gibbs212521/HEC_2_senior_design/LaTeX/FDR_front_page.pdf

## The University of Texas at Tyler College of Engineering and Computer Science Tyler, TX 75799

## Final Design Report

## For

## Wireless Charger Project

### A design project to fulfill the requirements of Senior Design in the Department of Electrical Engineering at The University of Texas at Tyler

The individuals whose names and signatures appear below certify that the narrative, diagrams, figures, tables, calculations, and analyses contained within this document are their original work except as otherwise cited.

Flory, David | April 12, 2021
Signature | Date
Fran¸ca, Natasha | April 12, 2021
Signature | Date
Franulovic, Franci | April 12, 2021
Signature | Date
Gibbons, Chad | April 12, 2021
Signature | Date
Sosa, Francisco | April 12, 2021
Signature | Date
