gibbs212521/HEC_2_senior_design/LaTeX/PDD_Submission.pdf

## The University of Texas at Tyler College of Engineering and Computer Science Tyler, TX 75799

## Primary Design Document Draft For

## Wireless Charger Project

### A design project to fulfill the requirements of Senior Design in the Department of Electrical Engineering at The University of Texas at Tyler

The individuals whose names and signatures appear below certify that the narrative, diagrams, figures, tables, calculations, and analyses contained within this document are their original work except as otherwise cited.

Flory, David | December 1, 2020
Signature | Date
Franca, Natasha | December 1, 2020
Signature | Date
Franulovic, Franci | December 1, 2020
Signature | Date
Gibbons, Chad | December 1, 2020
Signature | Date
Sosa, Francisco | December 1, 2020
Signature | Date

EXECUTIVE SUMMARY

The team proposes to design and prototype a managed, 30 watt wireless resonant charger for use with lithium-ion battery packs. It will be a versatile solution to the problem of powering autonomous mobile devices fitted with moderately sized battery packs of approximately four to six 18650 cells configured for 7.4 to 14.7 volts nominal output. With a preliminary cost estimate of $300, it fills a gap between inexpensive inductive chargers in the 5 watt range and custom 90 watt robotic power systems with an entry level price of $2000.

Our charging system will be made of two essential components: a transmitter and receiver. The transmitter will be supplied by standard line voltage and will be responsible for safely delivering up to 30 watts of resonant power to the receiver when in range and appropriately positioned. It will communicate status with the receiver over a Bluetooth link and will enable or disable power transmission when requested.

The receiver will communicate with the transmitter and to a user GUI over Bluetooth links, and optionally with the user’s own application (i.e. a robot microcontroller) over a serial link. It will be capable of delivering requested power transmission and charging status information and beginning or ending the charging process. It will disable charging on receipt of an error status from the charging circuit and will notify the user to take corrective action. Under normal conditions it will deliver power to the charging control IC, which in turn will charge the attached battery pack.

The charger may be configured to charge 7.4 to 14.7 nominal Li-Ion battery cells, which must have internal protection circuitry in accordance with UL1642 and IEC61960. Optimal configurations would include a 7.4V pack rated for 3.2A charging, a 11.1V pack rated for 2.2A charging, or a 14.8V pack rated for 1.7A charging.

To best demonstrate the full potential of our project, the team has specified optional deliverables that will be completed if time permits once the core project is completed. These stretch goals include a mobile robot capable of charging itself for continuous wireless operation and integration with a smart Li-ion battery for detailed fuel gauge and battery health status.

i

## Contents

I | Project Description | 1
II | Target Specifications and Ethical Considerations | 3
II.A Subsystem Dependencies | | 4
II.B | Hardware Components | | 5
II.1 | Transmitter: | | 6
II.2 | Receiver: | | 6
II.3 | Robot: | | 7
II.4 | Software: | | 7
II.C | Ethical and Professional Considerations | | 9
II.1 | Public Health: | | 9
II.2 | Safety and Welfare: | | 9
II.3 | Global Factors: | | 9
II.4 | Societal factors | | 9
II.5 | Environmental factors: | | 9
II.6 | Economic factors: | | 9
III | Engineering Standards and Constraints | 10
III.A Safety Constraints Mandated by Government and Possible Risks of Wire-
less Power Transfer (WPT) | | 10
III.1 FDA Safety Regulations | | 11
III.B Relevant FDA Safety Regulations and Standards | | 11
III.1 Safety Standards for Lithium-ion Battery Chargers | | 12
III.2 WPT frequency plan and power limits international overview . . . | 12
IV | Evaluation of Design Alternatives | 15
IV.A Primary Power Stage | | 15
IV.B Battery Management, Power Supply, and Target Power Delivery . . . . | 16
IV.C Transmitter circuit | | 20
IV.D Wireless Communications | | 24
IV.1 Ultra-Wideband | | 24
IV.2 ZigBee | | 25
IV.3 Infrared Wireless | | 26
IV.4 Bluetooth | | 26
IV.E Transmitter Coil Design | | 28
IV.F Software | | 29
V | Final Design | 34
V.A Battery Management, Power Supply, and Target Power Delivery . . . . | 34
V.B | Transmitter and Receiver Voltage Regulators (3.3 V and 5 V) | | 37
V.C | Class E Amplifier 30V Voltage Regulator | | 38
V.D Transmitter Design | | 40
V.E | Skin Depth Effects Calculations and Coil Parameters | | 47

ii

V.F | MSP430FR5994 Microcontroller | | 52
V.G Software | | 54
VI | Subsystem Simulations | 56
VI.A Transmitter Simulation | | 56
VI.B Receiver Simulation | | 58
VI.C Battery Management, Power Supply, and Target Power Delivery Simulation 59
VI.D Software Testing Protocol | | 61
VI.E Buck Down Converter Simulations | | 62
VII | Final Design Specifications | 65
VII.A Feasibility Study | | 65
VII.B Microcontroller | | 66
VII.C Transmitter Coil | | 66
VII.D Transmitter | | 67
VII.E Receiver | | 68
VII.F Thermal Considerations for 3.3V and 5V Voltage Regulators | | 68
VII.G Charging Subsystem | | 70
VII.H Battery Considerations | | 70
VII.I Microcontroller Considerations | | 73
VII.J Firmware Requirements: Transmitter | | 73
VII.K Firmware Requirements: Receiver | | 74
VII.L Software Requirements: GUI | | 75
VII.M Coil Considerations | | 75
VII.N Specification Summary | | 77
VIII Project Work Plan for Senior Design II | 78
IX | Resources Required | 81
IX.1 Simulation Tools | | 82
IX.2 Necessary Tools and Equipment | | 82
X | Conclusion | 83
XI | References | 84
Appendices | 87
A | Project Gantt Chart | 87
A.1 | First Review Period | | 87
A.2 | Second Review Period | | 90
A.3 | Third Review Period | | 92
B | Coursework Related Knowledge and Skills | 94

iii

## List of Figures

1 | Operation Story Block Diagram | | 2
2 | Power Supply of Transmitter and Receiver Subsystems | | 5
3 | Transmitter and Receiver Block Diagrams | | 5
4 | Subsystem Relational Block Diagram | | 8
5 | Microsemi Reference Design Kit for DRF1200 [6] | | 20
6 | Singe-Stage and Push-Pull Topology Comparison [11] | | 21
7 | Half-Bridge Structure [33] | | 21
8 | Receiver RF-DC Stage | | 23
9 | 9V to 35V 2-Cell 3.2A Charger with PowerPath and 2A Input Limit [20] | 34
10 | Battery Charger State Diagram [20] | | 35
11 | Tabular Representation of the JEITA system, Default JEITA Values and
| β=3490K Equivalent Temperatures [20] | | 36
12 | Recommended NTC Thermistor Circuit, Analog Devices: NTC Calculator 36
13 | 48 V to 3.33 V or 5 V Buck Down Converter Typical Schematic with Fixed
| Output [35] | | 38
14 | 48 V to 30 V Buck Down Converter Simplified Schematic Diagram [34] . | 39
15 | 48 V to 30 V Buck Down Converter Full Schematic Diagram | | 39
16 | LMG1210 Internal functional block diagram [19] | | 40
17 | Topology of Class-E Amplifier | | 41
18 | Transmitter Class E Amplifier Circuit Diagram | | 44
19 | Receiver RF to DC Stage | | 44
20 | INA19x Reference Schematic Diagram [15] | | 47
21 | Cross-Sectional View of Flat Spiral Coil [5] | | 49
22 | Functional Block Diagram [22] | | 52
23 | Comparison Within MSP430 Family [22] | | 53
24 | Graphical User Interface Architecture UML Diagram | | 55
25 | Class E Amplifier Simulation | | 56
26 | Class E Amplifier Output Voltage and GaN FET Drain Voltage | | 57
27 | Receiver RF-DC Converter | | 58
28 | LTC4162 Demo Board Layout [9] | | 59
29 | LTC4162 Demo Board Output GUI [9] | | 60
30 | LTC4162 Demo Board Simulated Performance [9] | | 61
31 | Schematic Diagram for TPSM265R1V3SILR (3.3 V Regulator) | | 62
32 | 3.33V Buck Converter Efficiency Curve for Expected Input Voltage vs
| Load Current | | 63
33 | Schematic Diagram forTPSM265R1V5SILR (5 V Regulator) | | 63
34 | 5V Buck Converter Efficiency Curve for Expected Input Voltage vs Load
| Current | | 64
35 | 30V Power Supply Schematic | | 64
36 | 30V Buck Converter Efficiency Curve for Expected Input Voltage vs Load
| Current | | 65
37 | Thermal Resistance vs. PCB Area [35] | | 69
38 | Basic Work Breakdown Structure Diagram – Deliverable-Based WBS . . | 79
| iv

## List of Tables

1 | Receiver Specifications | | 3
2 | Transmitter Specifications | | 3
3 | Communication Link Specifications | | 3
4 | GUI Specifications | | 3
5 | Ethical and Professional Considerations | | 10
6 | Overview of Relevant Standards | | 13
7 | Overview of Constraints | | 14
8 | Battery Charger Alternatives Evaluation Table | | 19
9 | Transmitter Alternatives Evaluation Table | | 24
10 | RF-DC Converter Alternatives Evaluation Table | | 25
11 | Wireless Communication Alternatives Evaluation Table | | 27
12 | Coil Design Alternatives Evaluation Table | | 29
13 | Software Alternatives Evaluation Table | | 32
14 | Alternatives Evaluation Table | | 43
15 | Skin Depths Effects in Copper Wire at High Frequencies | | 48
16 | Copper Coil Inner Diameters Calculated at 90 mm Outer Diameter [21] . | 49
17 | Copper Coil Inner Diameters Calculated at 90 mm Outer Diameter with
| Winding Variables | | 50
18 | Copper Coil Inner Diameters Calculated at 90 mm Outer Diameter with
| Inductance | | 50
19 | Copper Coil Resonance Inductance and Capacitance at 13.6 MHz . . . . | 50
20 | Copper Coil Skin Depth and Resistivity Calculations | | 51
21 | Quality Factor Inputs and Outputs | | 51
22 | MSP430FR5994 Parameters [22] | | 54
23 | Table of Software Utilized | | 54
24 | Final Design’s Charging Subsystem Specifications | | 72
25 | Final Design’s Coil Tubing Specifications | | 75
26 | Final Design’s Receiver Coil Specifications | | 76
27 | Final Design’s Receiver Specifications | | 77
28 | Final Design’s Transmitter Specifications | | 77
29 | Final Design’s Communication Link Specifications | | 78
30 | Final Design’s GUI Specifications | | 78
31 | Project Milestones | | 80
32 | Coursework Related Knowledge and Skills Table | | 94

v

I. PROJECT DESCRIPTION

Our project is to design and prototype a 30 watts nominal resonant wireless charger for use with 4 to 6 cell lithium ion battery packs. It will be microcontroller managed and may be monitored and controlled by a user GUI or directly by the target application. Unlike existing customized and proprietary robotic charging systems, our product will charge a standard battery type and be suitable for both stand-alone operation and integration into the user’s own design.

The team has been unable to discover any equivalent to our intended product for retail. The closest comparable product is a 90 watt magnetic resonance device that is marketed to businesses designing commercial drones and robotic systems. On the lower end, nearly all unbranded, low-cost wireless chargers that are available from mass online retailers supply no more than 5W via inductive charging. For a single industrial unit, the team has received a price quote for approximately $2000 USD. Individuals and small R&D teams that search for suitable devices through online retailers will find that these low-end transmitters are not modular and are limited to one specific purpose such as charging cell phones or key-fobs.

Our charging system shall employ magnetic resonance coupling to charge a lithium ion battery pack, delivering between 15 and 30 watts of power. The power transmitter and receiver will communicate as a unified system which shall provide battery management, protect against overcharging, and provide both diagnostic and telemetric information to the user and to an optional serial connection with the powered application’s control circuitry. The charging system may be monitored and controlled by the user either through an attached LCD interface or a GUI from either a Bluetooth connected PC or smartphone.

As an alternative to wireless charging, our intended market of hobbyists and prototype designers might consider a self-docking direct electrical connection. This is the charging method used by the Roomba, which engages with a custom dock and charges using metal contacts. While this is a cost-effective solution for a mass-produced product, wireless charging is a superior choice for autonomous mobile devices that might have a wide variety of sizes and shapes. The benefits offered by wireless charging include flexible placement of the charger, a compact charging area, greater tolerance for imperfect alignment between the charger and the target device, and the absence of exposed electrical connections.

To best demonstrate the full potential of our project, the team has specified optional deliverables that will be specified in detail once the core project is completed and tested. They include a mobile robot capable of charging itself for continuous wireless operation, fully integrated with a smart Li-ion battery for detailed fuel gauge and battery health status.

The team holds that a moderate power, low cost wireless charger with accessible telemetry will be useful to a small but important market of robotics hobbyists and developers, who at present are not being served by either proprietary business-to-business solutions or the low power, poorly documented inductive chargers available on the hobby market.

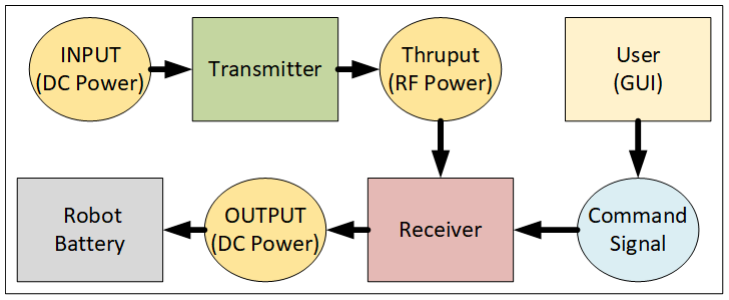
[picture p66: figure]

Figure 1: Operation Story Block Diagram

II. TARGET SPECIFICATIONS AND ETHICAL CONSIDERATIONS

Table 1: Receiver Specifications

Charge time
(4Ah Battery
Pack)

5 Hours Max

Battery pack voltage | 14.2 V
Coupling
Efficiency Transmitter to Receiver | 90%
AC-DC Conversion Efficiency | 80%
Charging Controller DC-DC converter | 85%
Overall Receiver Conversion Efficiency | 61.2%
Maximum Battery Charging Current | 1.25 A (14.7 V battery pack)
Charger Subsystem Charge Protocol | Constant Current Constant Voltage (Li-ION Battery)
Battery Type | Lithium-Ion (4 x18650 in Series or 2P4S Configuration)
Power Negotiation | Bluetooth 5 LE
Transmitter Locator Method | RF Localization [Bluetooth]
Deliverable Demo | Self-Moving Device (Robot)
Telemetry | Report State to GUI Device
LCD display | Diagnostic Character String Display

Table 2: Transmitter Specifications

Operating frequency | 13.56 MHz
RF power output | 30 W
Max operating range | 30 cm
DC Power supply | 12V 5A max.
Conversion
Efficiency DC-AC | 80%
Telemetry | Report State to GUI Device

Table 3: Communication Link Specifications

Communication Medium | Bluetooth 5 LE
Protocol | TBD

Table 4: GUI Specifications

GUI OS | WinOS, IOS, Linux, & Android
License | LGPL 3.0
Software Architecture | Model-Controller-View (MCV) Architecture
Delivery Model | Open Source (Free App Download)

A. Subsystem Dependencies

There are three modular components of the wireless charger project: the transmitter, the receiver, and the GUI. Additionally, in order to demonstrate a POC, this project will include a robotic subsystem that accepts the receiver as an onboard module. Thus, the project is concerned with four modular components that fall within a hierarchy of control. This evaluation of how each component and their subsystems subordinate to one another is critical for firmware and software development methodologies implementation.

The most independent component is the robot. This means that the robot does not ask anything from the receiver, transmitter, or GUI but must accept transmissions to it and perform the task associated with the particular communiqu´e and any status report is read by the other components dependent upon the robot for information. The furthest extent of interaction on part of the robot component for the POC would be to validate a networking handshake during Bluetooth communications.

The next most independent component is the transmitter on account to its responsive or passive functionality. The transmitter shall respond to the receiver’s requests for charging and periodically emit RF-pings to provide the receiver with positional data. The transmitter will not consider whether a ping is received nor search for a receiver unless instructed to do so by the user via the project’s GUI. The transmitter must have fail-safe protocols within its subsystems from its microcontroller.

Each receiver is independent of one another as well as from the GUI. A receiver would be dependent upon the robot accepting its telemetry’s locating feed as well as the transmitter pings and power to provide any value. The receiver will monitor the battery status and seek to induce proper voltages and currents in order to charge the battery. It will provide the transmitter with a distance vector to validate that it is close enough to begin charging via magnetic coupling. Furthermore, it will inform the transmitter to shut off by ceasing network authentication after detecting that the battery is charged or any system error is detected. The receiver shall be pairable to a specific transmitter before it is installed into a robot in order to maintain full operability in the absence of a user running The Project’s GUI Application.

The completely dependent component is the GUI, i.e. the Graphical User Interface. For the purposes of this section, the GUI will be considered indistinguishable from the Project’s Application that runs the GUI and fulfills all its functionality. It will have the adaptability to communicate with the receiver’s enclosing robot. The GUI primarily fulfills the need to monitor the status of the transmitter and receiver in real time. It can be used to monitor the battery’s charge or to turn off either the receiver or the transmitter directly as a bypass. The GUI will be compiled on any OS that Qt5 supports and downloadable for free off the internet. The GUI will add value to the Wireless Charging System as a whole without being a critical component.

B. Hardware Components

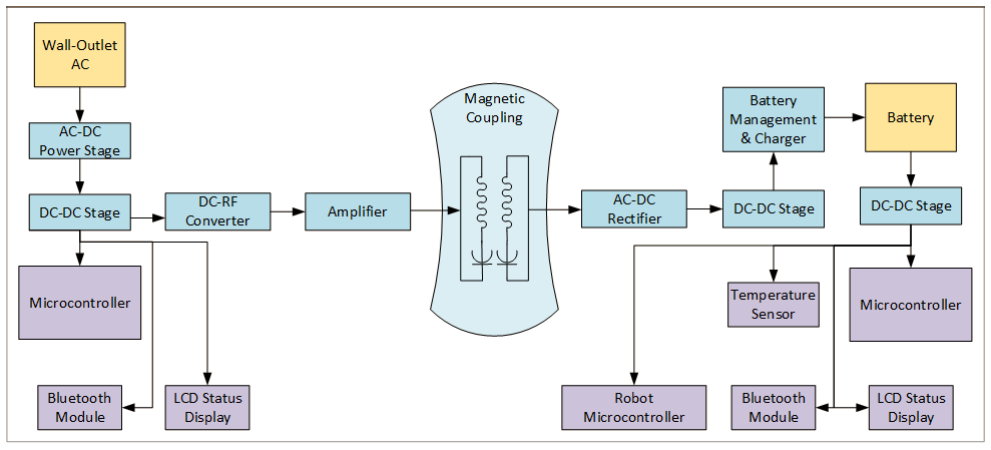
[picture p67: figure]

Figure 2: Power Supply of Transmitter and Receiver Subsystems

There are two hardware components to the system: a transmitter and receiver. Additionally, a third hardware component shall be included for the scope of this system’s proof of concept (POC), i.e. a robot with the wireless charger receiver module on-board. The POC demonstration will exhibit the charging of onboard batteries, locating the robot via the receiver’s telemetry, an error test with only the receiver’s attached LCD Status Display, and provide real-time feedback on a GUI via Bluetooth communication. The onboard battery pack is to provide power to both the robot and the receiver power when uncoupled from the transmitter.

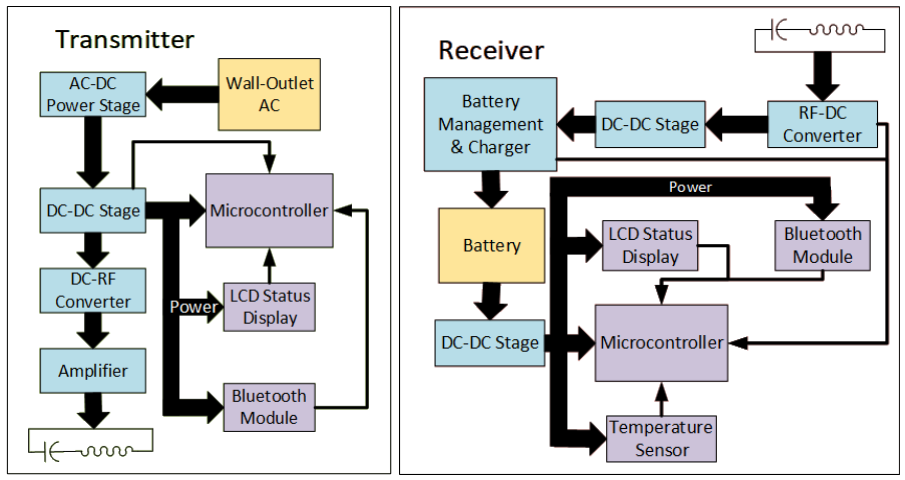
[picture p68: figure]

Figure 3: Transmitter and Receiver Block Diagrams

1.) Transmitter: The transmitter provides power wirelessly and communicates asynchronously with the receiver. The receiver converts that power to proper voltage levels for battery charging. Telemetry and robot subsystems shall operate on the battery’s power. Both the transmitter and receiver will negotiate power transmission and the wattage thereof. The transmitter will not be on at all times. The transmitter will start providing RF power only while the receiver requests power. Also, power delivery will be disabled if the coupling efficiency drops below 90%. Upon undesired decoupling, the receiver will provide its robot correctional vectors that can be used to reposition the robot for optimal charging. This receiver’s positional correction will give an added benefit of preventing bystanders from exposure to strong electromagnetic fields.

Both of the system’s hardware components will require firmware for their microcontrollers to fulfill their targeted deliverables. This firmware is specific to their design and must be developed as part of the project. Their firmware must permit communication with external devices running the project’s graphical user interface (GUI) over Bluetooth.

The transmitter takes power from a DC source and generates an electromagnetic field using an RF amplifier and antenna. For safety and efficiency concerns a power negotiation protocol between the transmitter and the receiver is required for safe and efficient operation. The transmitter will display important parameters on the LCD display mounted on its enclosure and more detailed data will be transmitted to the remote PC, tablet or phone via wireless link.

- External power supply 12V, 5A (off the shelf power supply) will be used to provide power to the system.
- Internal DC-DC converter will be used to step down input voltage to appropriate levels for internal devices. (The transmitter will require at three different voltage levels for powering microcontroller, Bluetooth, LCD, RF generation stage and RF amplifier.)
- DC to RF converter consists of an RF oscillator followed by a buffer stage.
- Buffered RF signal is supplied to the class E amplifier that drives the tuned transmitter LC circuit.
- Microcontroller is used to control the transmitter (power negotiation and safety), data collection and communication coordination.
- The LCD is used to display selected parameters such as RF amplifier supply current, input power current and coil RF voltage. This display will be a simple two row charter display.
- The Bluetooth module will be used as a communication device for telemetry and power negotiation between the power transmitter and receiver.
- Entire transmitter will be designed and assembled on a single PCB.

2.) Receiver: The receiver is responsible for battery management, conversion of RF to DC power for charging, and for communicating status with the transmitter, the device under power, and the user via a local LCD interface or remote GUI. Battery management functions will include the monitoring of charge level, battery temperature, and charging current and voltage. The receiver will detect a low battery condition, provide telemetry to the powered device, and will request RF power transmission from the transmitter when in charging range. A single microcontroller will manage all receiver functions with support from appropriate battery management and wireless communication modules.

3.) Robot: As a proof of concept for the wireless charger we will integrate it into an example robotics application. Our mobile robotics application will interpret charger telemetry to recognize a low battery condition and position itself appropriately for charging.
- Custom PCB will be required for the microcontroller and stepper motor drivers. Electronic circuit for this part will be independent from the charger circuit.

4.) Software: The inter-platform software will provide the user an interactive suite of realtime information via a graphical user interface (GUI). The GUI shall be modular and have the ability to incorporate further functionality, be it communicating with the robot or implementing automated communications to the hardware components.


Figure 4: Subsystem Relational Block Diagram

C. Ethical and Professional Considerations

1.) Public Health: Life preserving medical equipment requires concern in the transmission of powerful RF charging signals that may interfere with the medical equipment. We will adhere to FCC standards for intentional radiators and ensure that the charger transmitter does not exceed FDA guidelines for RF emission. Our design will be informed by the guidelines of the National Council on Radiation Protection and Measurements (NCRP) and the Institute of Electrical and Electronics Engineers (IEEE).

2.) Safety and Welfare: Our design may contribute to public safety and welfare by easing the development of robotic systems intended to handle hazardous materials, work in narrow spaces, high temperature environments, or in vacuum. We will follow industry best practices for safe charging, such as current limiting and temperature monitoring, to minimize the risk of battery failure.

3.) Global Factors: The pressures of governing bodies are to be taken into consideration in any choice this project takes; however, we are primarily concerned with the US governing bodies and then the EU bodies in order to streamline our development process to hit the largest market base possible. Additionally, Canadian and Mexican regulations would be considered as immediate market options.
In an alternate vein, there are sourcing questions that must be investigated before production in order to conform with internation laws and prevent being banned from specific global markets whether at home or abroad.

4.) Societal factors The source code will be educational as well as providing value to the device itself. The design’s modular intention will permit versatile implementations at work or at home. The product should serve influenceable groups such as teenagers, helping them enter STEM related fields.
The product as a whole should be considered in a way that would encourage further education in the classroom in physics. Likewise, the production of the product should foster a community between the product’s programmers and engineers.

5.) Environmental factors: This concern requires continual attention for any anomalies concerning the battery cells. The device cannot account for all of these concerns, but should maintain labeling that makes the customer aware of such concerns that may be caused by their device. The project must provide a means of emergency shut off by some interrupt port that is always active. The operating robot, the user via a GUI, and the receiver itself must have this ability to turn off the charging feature of the receiver.

6.) Economic factors: The device could fulfill legal requirements for a client, and, in that case, a custom suite would be developed in the software at a premium to satisfy a client’s needs. Additionally, creating a lightweight, low-cost production process is critical in maximizing profits. The open-source market also provides extensive free advertising momentum when capitalized successfully. Additionally, the product would assist in producing other products, especially in research and development.

Table 5: Ethical and Professional Considerations

Public Health | · Medical Equipment RF Exposure · Electrical Shock · Chemical Exposure
Safety and Wellness | · RF Bandwidth Jamming · Electrical Shock · Chemical Exposure
Global Factors | · International Governing Bodies · Sourcing Restrictions · Inter-Market Penetrability
Societal Factors | · Open-Source Capitalization · STEM Educational Resources · Professional Organizations · Customer Privacy & Security
Environmental Factors | · Chemical Pollution · User Environmental Awareness · Emergency Shut Off Cases
Economic Factors | · Open-Source Capitalization · Specialty Clientele · Rapid Agile-Deployment · Light-Weight Production

III. ENGINEERING STANDARDS AND CONSTRAINTS

A. Safety Constraints Mandated by Government and Possible Risks of Wireless Power Transfer (WPT)

In the United States, two government agencies are responsible for regulations regarding RF exposure safety. Those agencies are the Federal Drug Administration (FDA) and Federal Communications Commission (FCC). Both agencies have their own set of rules that are similar.

1.) FDA Safety Regulations There are safety concerns about exposure to strong electromagnetic fields. The FDA divides wireless chargers into two categories:
- Proximity type (where the device is in contact with the charger)
- Directed (beamed) delivery across space

Since this design fits in the category of proximity chargers FDA rules for this type of charger must be followed. According to FDA Resonant proximity charges have resonant LC circuit which improves range and efficiency. FDA clearly states that higher power RF transmitters pose a higher risk. Since the wireless charger is a powerful RF transmitter there are concerns about effects of the wireless charger to metal objects such as rings and implanted medical devices and other wearable metal pieces.

The FDA clearly states that higher power products pose a higher risk and there are concerns about effects of the wireless charger to metal objects such as rings implanted medical devices and other wearable metal pieces. Also, the FDA has concerns regarding WPT in terms of electromagnetic interference with medical devices or disruption of device communications. Therefore, engineering controls must be sensitive and reliable enough to prevent injury. Also, it is important to keep in mind that not all existing products implement electromagnetic safety. Hence, some existing products may malfunction if they are exposed to strong electromagnetic fields.

B. Relevant FDA Safety Regulations and Standards

FDA has multiple standards and regulations. Since our device will use an RF transmitter for power transfer, Title 21 code CFR 1000.15(b) is applicable [1].

IEEE C95.1-2005 standard defines guidelines regarding RF power density for localized and whole-body exposure to electromagnetic fields generated by the RF emitter [14] (in our case transmitter). Those two standards address exposure to electromagnetic fields. In order to address this rule, we are limiting our transmitter power to 30W[14]. A power negotiation protocol will be used to enable the charger transmitter only when the receiver is present and properly placed in the front of the charger.

Exposure limits are clarified in IEEE Standards Interpretations for IEEE Std C95.1-2005. IEEE Standard for Safety Levels concerning Human Exposure to Radio Frequency Electromagnetic Fields, 3 kHz to 300 GHz. According to interpretation from the IEEE Standards Interpretations the whole body exposure is limited to 0.08W /kg and localized exposure is 2W/kg. Since the transmitter will operate on the frequency that ranges from 100kHz to 1GHz exposure levels in this rule is applicable to our design.

The FCC also addresses concerns about RF exposure considerations for low power consumer wireless power transfer from FCC. WPT devices must satisfy RF exposure limits from FCC standard KDB 680106 D01 [25][16][27]. All wireless power transfer devices that operate above 9kHz are considered intentional radiators and they are subject to FCC rules.

FCC sets regulations and norms for WPT devices and it is mandatory to certify WPT devices prior making them available on the market. Those rules include unwanted emissions limits in order to prevent electromagnetic interference. Also, FCC sets frequency allocation plans. According to the frequency allocation plan frequency 13.56MHz is available for wireless power transfer devices in the USA.

FCC has established a regulatory framework for wireless power transfer. According to the FCC information, the charging mode is certified under FCC Part 18 [16] and the communication part is certified under Part 15 [25][27]. Given FCC requirements it is feasible to use an already certified module for wireless communication such as Bluetooth, Zigbee, or Wi-Fi. That way only WPT circuits would be subject to certification according to FCC Part 18 [16]. When all available regulations are considered the best operating frequency for the wireless charger is most likely 13.56MHz since that frequency may become the worldwide standard for WPT. Also, this frequency will allow WPT transfer using magnetic resonance which does not require very precise positioning and matching charger transmitter coil. The power limit ( max. 30W) will be more than enough for this application.

Given FCC requirements, it is feasible to use an already certified module for wireless communication such as Bluetooth. Bluetooth is covered by the IEEE 802.15.1 standard and is widely used in many devices and is licensed worldwide [12].

1.) Safety Standards for Lithium-ion Battery Chargers We plan to follow the IEEE 1625-2008 Standard [13] for rechargeable batteries for multicell mobile computing devices because this device is universal and can be considered as a computing device. This standard provides guidelines on implementing the safety controls for the design and manufacture of lithium-ion (Li-ion) and lithium-ion polymer (Li-ion polymer) rechargeable battery packs [13]. Safety guidelines are addressing the fire hazard due to charger or battery failure [13].

2.) WPT frequency plan and power limits international overview According to ETSI (European Standards Organization), there are certain frequencies and prescribed maximum power levels for wireless charging. Some of those frequency bands are candidates for international harmonization (those frequency bands will be dedicated to WPT transfer). At this moment there is no agreement on which frequency band will be used for WPT worldwide.

ETSI documentation gives an overview of different frequencies for the implementation of WPT systems. According to ETSI 13.553 – 13.567 MHz band is currently used for power transfer for the following power classes P<1W, 1W<P<5W, 5W<P<31.5W [17]. This is an International standard that covers European Union EU and European economic area (EEA) as well as many other regions (Parts of Africa, Asia and Australia ) follow European Union (EU) regulations related to this matter.

EN 55011:2016 international standard for electromagnetic compatibility. This standard applies Industrial, scientific and medical equipment and addresses radio frequency disturbance. This standard sets limits to electromagnetic emissions from the product. In order to avoid creating disturbance in RF communication the wireless charger electromagnetic emissions must be below the limit prescribed in this standard. This is achieved by proper circuit design and using low pass filters on all connections that are exposed to the user.

Table 6: Overview of Relevant Standards

Organization | Engineering Standards
IEEE | IEEE C95.1-2005 This standard defines exposure limits to the electromagnetic field This standard is adopted in many safety standards. IEEE 1625-2008 Standard for rechargeable batteries for multicell mobile computing devices. IEEE 802.15.1 Bluetooth standard
Government | FCC Part 15, FCC part 18 RF Power levels and communication links are defined by FCC Part 15 and Part 18. The RF transmitter power level limits in the US are much higher than in some other countries. FDA: 21 CFR 1000.15 FCC: KDB 680106 D01 Both standards define exposure limits to electromagnetic fields. The limits will be satisfied if the transmitter power is limited to 5W. Higher power levels are allowed if proper safety measures are implemented.
International | EN 55011:2016 This standard defines limits for unwanted emissions in the RF spectrum above 30MHz. The proposed WPT charger system must follow limitations for unwanted emissions.

Table 7: Overview of Constraints

| Technical Description
Cost | $320 Estimated Prototype Cost
FDA | FDA: 21 CFR 1000.15 FCC: KDB 680106 D01 Both standards define exposure limits to electromagnetic fields. The limits will be satisfied if the transmitter power is limited to 5W. Higher power levels are allowed with proper safety measures.
Government | FCC Part 15, FCC part 18 RF Power levels and communication links sic FCC Part 15 and Part 18. The RF transmitter power level limits in the US are much higher than other countries. EU rules power requirements satisfy US regulations.
International | EN 55011:2016 This standard defines limits for unwanted emissions in the RF spec-trum above 30MHz. The proposed WPT charger system must follow limitations for un-wanted emissions.
Speed | Recharge speed 5 hours (for 5. Ah battery pack 14.4V)
Reliability | The charger will be able to detect improper positioning and it will monitor for power coupling efficiency. If is coupling inefficient it will provide warning and it will not start charging process. The device will continuously monitor battery conditions such as charge or discharge current, voltage and temperature in order to prevent battery capacity degradation Power RF transmitter power <30W Overall power supply input requirement will be <50W.
Complexity | The system has two hardware parts power transmitter and the robot with integrated power receiver with the charger battery management and battery pack
Manufacturability | The device design will be based on standard electronic/electrical and mechanical components that are readily available. Electronic circuit assembly sic custom printed circuit board design. Two PCBs one for receiver and the other for the receiver/robot. All electrical components such as batteries and motors will be stan-dard, readily available components. The design will utilize mechanical parts such as gears, shafts, and fasteners that are commonly used and readily available.
Sustainability | This device is designed to cause minimal wear and tear to itself and any device connected to its system. The receiver would extend the lifetime of others’ devices by providing a low-cost recharging option.

IV. EVALUATION OF DESIGN ALTERNATIVES

A. Primary Power Stage

The wireless charger and receiver system will depend on AC line power provided to the wireless transmitter unit.

Options:

1) Direct AC connection
a) Immediately rejected due to safety concerns and unneeded complexity.
2) Approved 110-220 VAC to 12 VDC commercial switch-mode power supply.
a) Advantages
i) low cost
ii) standard voltage
iii) ready availability.
b) Disadvantages
i) Additional boost stage required to provide the higher voltages required by the resonant transmitter, adding complexity and power loss.
ii) Five amp input current would create undesired power losses.
3) Approved 110-220 VAC to 48 VDC commercial switch-mode power supply.
a) Advantages
i) Good availability through engineering supply channels.
ii) Relatively low input current reduces heat loss
iii) Voltage near or only slightly above what is needed by the transmission stage.
iv) Example: TDK-Lambda DT62PW480D
1) 48 VDC, 1.36 A maximum (65 watts)
2) Higher wattages and alternate manufacturers available
3) Note that optimal efficiency is usually obtained below maximum
power draw.

The 48 VDC primary supply was provisionally approved. It will require a step down stage to provide 5V and 3.3V logic supplies for the wireless transmitter microcontroller, class E amplifier, and support circuitry.

The step down buck down DC converters could either be accomplished via individual custom op amp voltage regulators or integrated buck down circuits. Furthermore, the 5 V and 3.33 V buck down DC converters could potentially be merged into a single topology. Custom op amp voltage regulators would take up a larger surface area as well as require excessive soldering and are thus not desirable. The only limitation in merging the 5 V and 3.33 V buck downs into a unified topology is that the 5 V buck down would require more current to feed both outputs. The benefit would be the reduction of parts and surface area required for the total circuit.

B. Battery Management, Power Supply, and Target Power Delivery

Our project will convert electricity from the wireless power receiver into a form suitable for charging a cell battery. It must do so while powering its own circuitry, and it must deliver power from the batteries to the target application. Our project must also be capable of monitoring the charging process and battery charge status for both safety and diagnostic purposes. It must be able to respond to instructions and queries received from the wireless power receiver microcontroller.

When implementing a rechargeable battery management system, it is first necessary to decide what battery chemistries the system will support. The team considered NiMH and Li-ion chemistries and favored the latter due to the far greater power density. The team had already selected a mobile robot as an ideal example application for our charger. It was clear that the performance and user appeal of our wireless charger would be much greater if it could utilize the higher-performance battery chemistry. The team understood that there would need to take special care that our charge circuitry would manage these high performance batteries safely.

The following requirements were identified for the battery management system:

1.) DC to DC conversion from the wireless power receiver to a form appropriate for the charging and power supply circuits.
2.) Charging appropriate for battery chemistry, i.e. constant current stage followed by a constant voltage stage.
3.) Temperature monitoring and protection against overcharging.
4.) The ability to vary charging currents in response to varying levels of wireless power, either automatically or in response to commands from the wireless receiver control unit.
5.) The ability to draw operating power from batteries and charger while charging is in progress (i.e. PowerPath).
6.) The ability to detect a low battery condition, which may or may not include more detailed fuel gauge capabilities.
7.) The ability to control charging behavior as needed in response to demands from the wireless power receiver microprocessor or user controls.
8.) The ability to report telemetry to the wireless power receiver microprocessor or user.

There are many available integrated solutions that could meet the above requirements. In order to narrow down the possibilities the following choices must be made:

1) Battery chemistry
a) Lithium-Ion
b) NiMH option
c) Multi-chemistry: rejected due to limited hardware options, complexity, and safety concerns.
2) Linear vs. Switching input stage and input voltage range
a) Linear
i) Usually seen on small, single or dual cell chargers.
b) If Switching:
i) Buck: may make an additional DC/DC stage unnecessary.
ii) Boost: not likely to be necessary
iii) Buck-boost: may make an additional DC/DC stage unnecessary
3) Stand-alone vs. programmable
a) Jumper/hardware settings
i) Limited configuration options.
ii) Limited data available via status lines (i.e. over-temp condition) iii) Simple implementation.
b) I2C programmability
i) Most configuration and control issues may be worked out in software. ii) Configuration may be altered during operation by firmware or
user instructions.
iii) Status registers may be queried by the microcontroller at any time.
c) SMBus programmability
i) Generally equivalent to I2C
ii) Libraries available for MSP430
iii) Automatic timeout supported
4) Maximum power point tracking
a) Offered as an integrated option within Analog Devices LTC4162 family.
i) May be useful depending on wireless power receiver design choices.

Preliminary recommendations: A fully programmable multi-cell charge controller from a modern, well-supported product line is the most flexible option. Such a device would allow many design choices to be made in software and changed if necessary.

Candidates include:

1) Texas Instruments: BQ257xx
a) Buck-boost power input
b) Supports 1-4 Li-ion cells
c) Options include I2C/SMBus, USB-PD, CPU throttling signals
d) Demo available: BQ2571x
2) Analog Devices: LTC4162
a) Buck power input
b) Supports 1-8 Li-ion cells
c) Integrated MPPT option
d) Demo available: DC2038A
3) Texas Instruments: BQ2002
a) Linear power regulation
b) Supports 1-4 NiMH cells
c) Thermistor monitoring
d) Standalone RC-Settable

Table 8: Battery Charger Alternatives Evaluation Table

Evaluation Basis | Texas Instruments BQ25790 | Analog Devices LTC4162 | Texas Instruments BQ2002
Environmental Factors | RoHS compliant. Environmental con-cerns with Li-ion cell production and disposal. | RoHS compliant. Environmental con-cerns with Li-ion cell production and disposal. | RoHS compliant. Environmental con-cerns with Li-ion cell production and disposal.
Economic Factors | $2.29 per unit | $2.95 per unit | $0.786 per unit
Public Health | RoHS | RoHS | RoHS
Social Factors | Fully programmable charge voltage and cell configuration. High power density for a wide variety of applications. | Fully programmable charge voltage and cell configuration. High power density for a wide variety of applications. | Very simple imple-mentation. Much lower power density may limit applications.
Safety and Welfare | Full battery teleme-try and temperature monitoring. | Full battery teleme-try and temperature monitoring. | Thermistor monitor-ing. Fewer safety con-cerns with NiMH chemistry.
Global Factors | None identified; may be used worldwide. | None identified; may be used worldwide. | NiMH cells may be more readily available in some markets.
Cultural Factors | Flexible battery configuration. | Flexible battery configuration. | Fixed battery con-figuration using batteries widely available by retail.

Our team decided to use Li-ion chemistry due to its superior performance and power density. The Analog Devices LTC4162 was chosen for its versatility, clear documentation and the availability of development hardware.

C. Transmitter circuit

One very common way of driving coils at 13.56MHz is the class E amplifier. This amplifier can be realized by using discrete components available in integrated amplifiers (hybrid ICs).

One readily available solution for the transmitter amplifier circuit is an integrated circuit from Microsemi (part # DRF1200).


Figure 5: Microsemi Reference Design Kit for DRF1200 [6]

This DRF1200 was tested and found to meet project specifications. The manufacturer had acceptable support and documentation. The cost of the driver was $182.80, which would have added unacceptable costs to the design. With a maximum 1 kW output, it also far exceeded the project’s 30 W power requirement [6].

A very high voltage across the transmitter coil can be developed at high output powers in class E amplifier designs. This voltage could be as high as 1kVp−p. This is a potential electric shock hazard. A possible safer alternative to the class E amplifier is a push-pull driver, commonly used in low-frequency WPT designs but can extend to 13.56 MHz.

The push-pull topology utilizes two power transistors for driving in a way that one transistor is on and the other is off. This design would have required a complex gate

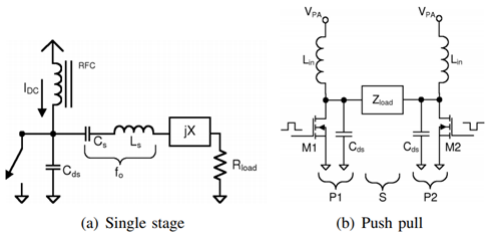
[picture p69: figure]

Figure 6: Singe-Stage and Push-Pull Topology Comparison [11]

driving circuit and it as well required a circuit that generates two signals, 180 degrees out of phase for the power MOSFETs gate drive. In this design, the load impedance was not required to have a tuned network on the output [11].

Another way of driving the transmitter coil was to implement a H bridge. This design would have required two half H-bridge circuits that would have been used to drive the transmitter coils.


Figure 7: Half-Bridge Structure [33]

This topology requires a gate driving circuit which is similar to the push-pull gate driving circuit. The load in this design was driven with full h-bridge (two half-bridge circuits). One side of the H bridge would act as a current sink while the other side would act as a current source. This approach increases the complexity and cost of the circuit beyond that of a single transistor class E amplifier [33].

Powerful electromagnetic fields can cause undesired heating of nearby metal objects. Possible safety mechanisms include power negotiation and monitoring of the receivertransmitter coupling. These safety mechanisms will prevent the transmitter from turning on without the proper receiver coupling. With effective coupling, most of the RF energy will be absorbed by the receiver and when the batteries are fully charged the receiver will then be able to send a request to the transmitter to turn off RF power.

Receiver alternative designs

The conversion from RF power to DC is performed by the rectifying stage. The design options for this stage are relatively limited and straightforward. One common way of solving this problem is to implement a full-wave rectifier bridge implementing Schottky diodes. There are many diodes that are available for this purpose. One adequate choice was the diode part number 80SQ045N from ON Semiconductor.

A half-wave rectifier circuit would be the simplest and least expensive method for RF-DC conversion. This option was immediately rejected for the unacceptable loss of half the potential power of the induced AC current.

For safety and testing purposes, it is necessary for the receiver to be capable of determining how much power is received. The most direct approach to making this data available is to include a current sense resistor and differential amplifier to provide current sense data, and a voltage divider to provide voltage sense data. The analog output of these sensors may be measured directly by the microcontroller ADC.

The final design recommendation is that RF to DC conversion shall be performed by a full-wave Schottky diode rectifier bridge with sense circuits for the measurement of received power.


Figure 8: Receiver RF-DC Stage

Table 9: Transmitter Alternatives Evaluation Table

Evaluation Basis | Single-stage driver | Push-pull driver | H-Bridge driver
Environmental Factors | Less efficient than push-pull or H-bridge driver | Efficient requires less energy than a single-stage driver for the same power output. | Efficient and com-plexity are similar to a push-pull solution.
Public Health | Does not have nega-tive effects on public health if safety circuits are imple-mented. | Does not have nega-tive effects on public health if safety circuits are imple-mented. | Does not have nega-tive effects on public health if safety circuits are imple-mented.
Economic Factors | Easy to implement. Simple driving cir-cuit | Requires compli-cated driver circuit. Increases the cost of the product. | Requires compli-cated driver circuit. Increases the cost of the product.
Social Factors | N/A | N/A | N/A
Safety and Welfare | Requires safety circuits in order to satisfy safe RF exposure limits. | Requires safety circuits in order to satisfy safe RF exposure limits. | Requires safety circuits in order to satisfy safe RF exposure limits.
Global Factors | This circuit does not have any special parts. Parts are very likely available in most countries. | Special parts may be required for this design that may not be available in every country. | Special parts may be required for this design that may not be available in every country.
Cultural Factors | N/A | N/A | N/A
D. Wireless Communications

1.) Ultra-Wideband This communication technique is designed for short-range transmission, and enables charging of multiple devices of high bandwidth data. Used to relay data from one device to another within a maximum distance of 30 feet. UWB waveforms are different from other carrier waves in that they are short in duration. They also offer optimal enhancements in areas including communications, radar and positioning/ranging. In communications systems, large RF bandwidths can transmit data rates

Table 10: RF-DC Converter Alternatives Evaluation Table

Evaluation Basis | Diode full-wave rectifier bridge | Diode half-wave rectifier bridge
Environmental Factors | More efficient which will reduce negative environmental ef-fects. | Less efficient
Public Health | Does not have nega-tive effects on public health. | Does not have nega-tive effects on public health.
Economic Factors | Simple and inexpen-sive design. | More simple and inexpensive design.
Social Factors | N/A | N/A
Safety and Welfare | N/A | N/A
Global Factors | This circuit does not have any special parts. Parts are very likely available in most countries. | This circuit does not have any special parts. Parts are very likely available in most countries.
Cultural Factors | N/A | N/A

of gigabits per second. UWB can be also used as communication links that involve sensors, such as temperature, and pulse rate sensors. Within positioning/ranging systems, time is used to determine signals that give out close-range positioning within ten of meters. When the bandwidth is increased, precision is also increased [26]. This system is very low cost and low power for ICs. UWB causes little to no interference within existing services because it divides its power across a big frequency spectrum. Used in military and other government operations, ultra wideband is considered to be the most secure and reliable means of data communication. [3]

2.) ZigBee This is one of the most widely used transceiver standards in wireless applications. ZigBee is reliable, can support a large number of nodes, is easy to deploy, has incredibly long battery durability, secure, low cost unit, used world-wide, has standards protocol with little to no licensing fees, has chipsets available from different sources, it is low power, low and maintenance. ZigBee’s data transfer seems to fall around 250kbps, which accounts for a low data rate transfer application. Applications involve home automation systems, meter reading, vehicle control, and fitness monitoring. This system’s end device is ideally a low power battery device. It also can’t relay data from other devices. [31]

3.) Infrared Wireless Infrared is used for short-range and indoor communication. Its high-speed emitters and detectors are low cost. It is unregulated worldwide. Infrared light is absorbed by dark objects, reflected from shiny objects/surfaces and colored items. It penetrates through glass, but not through walls or any other barriers which limits transmission to a single room. While it requires a line-of-sight (LOS) connection, its wave confinement allows for secure communication and does not interfere with other devices located outside its room. Infrared can achieve high capacity and efficient signal transmission, while radio communications suffer from larger fluctuations in signal receiving due to multiple-path transmission needing coordination. [18]

4.) Bluetooth Bluetooth is a wireless system that uses radio waves for communication. It operates at 2.45 GHz (available globally), although slight variation of location and bandwidth apply. Does not interfere with other devices on the same frequency. The maximum operational range is between 10 and 100 meters to optimize experience for users. Gross data rate is 1 Mbit/s. It draws low current at standby mode, enabling performance longevity for battery powered devices. Bluetooth provides very low risk of RF radiation that is linked to cell function, infertility, and DNA damage, and emits low levels of nonionizing radiation, considered safe to humans. Class 3 radios have range 1 to 3 feet, class 2 have range 10 to 30 feet, and class 1 have range 100 to 300 feet.

Table 11: Wireless Communication Alternatives Evaluation Table

Evaluation Basis | Ultra Wideband | ZigBee | Infrared Wireless | Bluetooth
Environmental Factors | N/A | Low Draw Power | N/A | Low Power Draw
Public Health | N/A | N/A | Point-to-point laser can cause burns or blind-ing | N/A
Economic Factors | Low Cost (Sub $25) | Low Cost | Low Cost | Low Cost (Sub $13)
Social Factors | Able to be integrated in wide array of applications | Able to be integrated in wide array of applications | Able to be integrated in wide array of applications Signal confine-ment increases data security. | Able to be integrated in wide array of applications Radio ranges: Class 1 = 100m Class 2 = 10m Class 3 = 1m
Safety and Welfare | Safety Periodic Limit: (10 µs to 100µs) | Device Limit: 50 | Low power transmitter recommended | N/A
Global Factors | Frequency ranges in most countries in EMEA range from 3.1-4.8 GHz. | Has standards protocol with little to no licensing fees. | Generally unregulated worldwide. | Operates in the unlicensed ISM band (2.4 to 2.485 GHz).
Cultural Factors | N/A | N/A | N/A | N/A

E. Transmitter Coil Design

There are various types of coil shapes that can be implemented in our product to provide wireless power transfer. These diverse coil shapes offer different efficiencies in power transfer and as well differ in performance. It was imperative to decide on a method which was the best suitable for our project, there were three different coil shapes designs that were considered for this project; helix circular coils, planar circular coils and multiple circular planar coils. The coil configurations that were considered all provided the same purpose, but each one affected specific attributes of our application. It is important that the correct coil shape design is implemented in order to optimize functionality in the WPT system. Since there were different configurations of the coils, these varying configurations will affect certain parameters of the coils which are highly essential in WPT systems. These parameters have a large impact on efficiency, bandwidth, and transfer distance of the wireless power transfer system. [6]

The first alternative considered that was a helix circular coil design. The major reason this design was considered was because this type of coil design provided adequate transfer efficiency in WPT systems [36]. Another reason it was considered as an alternative was because this coil design also performs very well in long transfer distances. Although this coil design is efficient in power transfer and also had the longest transfer distance out of the three, it had a couple of downsides which could cause issues with our product. A drawback of this coil design would be that it occupies too much space. [36]

The second alternative method is a planar circular coil design. This design is traditionally the most used design in wireless charging applications. The circular planar coil design also provides good wireless power transfer capabilities but not as good as the helix circular coils [36]. This design could maintain a good efficiency at larger distances than the helix design. Positioning of the transmitter and receiver must be precise in order to perform efficient power transfer in the WPT system.[7]

The multi coil circular planar design of multiple circular planar coils provides several solutions to issues that were faced by the single circular planar coil. It provides the same characteristics of a single planar coil but resolves the issue of precise positioning. This coil design provides a free position solution to the application. This coil design would not limit it to a specific charging area but rather allow it to be charged in multiple positions, thus the receiver would have more freedom of coupling capabilities.[7]

Table 12: Coil Design Alternatives Evaluation Table

Evaluation Basis | Helix Circular Coil | Single Planar Circular Coil | Multi-Coil Planar Circular Coil
Environmental Factors | Long RF Transfer distance More directional | Medium RF transfer distance | Medium RF transfer distance
Public Health | Greater directional-ity Increases risk at high transmission power. | Dependent on trans-mission power | Dependent on trans-mission power
Economic Factors | High production cost Low durability Inflexible Efficiency is distance dependent | Easy implementation Flexible Durable Compact | Easy implementation Flexible Simultaneous coil charging
Social Factors | Low portability pos-sibilities | High portable possi-bilities | High portable possi-bilities
Safety and Welfare | Higher risk to com-ponent damage Low risk of shock | Low risk of shock | Low risk of shock
Global Factors | N/A | N/A | N/A
Cultural Factors | N/A | N/A | N/A
F. Software

The software design can be accomplished via various programming languages, frameworks, toolkits, architectures, and development methodologies. The programming language will dictate the limitations and speed of the software itself. Various frameworks should be considered for each programming language due to their built-in functionalities and platform preferences. Any available toolkits should be considered and given a proper cost-benefit analysis. Various architectures should be considered to match the needs of the project’s scope and complexity. Lastly, the design considerations should also evaluate the development methodologies or if any combinational approach best accommodates time constraints and all deliverables.

The programming languages available are C++, Python, and Javascript. All three languages are deployable on every desired operating system. Python is the slowest while C++ is the fastest. Python is an interpretive language while both C++ and Javascript are compiled languages, on account of which Python is better for rapid or iterative testing. Javascript would rely upon software such as Chrome or other modern internet browsers to build the GUI. Python and C++ would be downloadable and built to the OS specifically. The team is not aware of any method of deploying python without revealing source code directly beside running a script that “hides” directories on the machine. C++ may be deployed in the binary state or as a single executable file that at least immediately conceals source code. Javascript permits server-side operations and license control that can mostly hide server side code. C++ is the lowest level language while Python is the highest level language. The higher level a programming language is, the greater the impact value per line of code is. Lastly, the team is most familiar with Python and least familiar with Javascript.

C++ Frameworks could include either Qt5 or wxWidgets. wxWidgets includes all basic GUI functionality and is open source even when deployed commercially. The framework does not have native Bluetooth capabilities but is capable of being adapted to utilize Bluetooth. Qt5, however, has built-in Bluetooth integration for all operating systems when utilizing Bluetooth LE Central [24] . However, Qt requires modification to operate Classic Bluetooth on iOS and cannot immediately operate Bluetooth LE Peripheral on Windows machines. In any case where the framework cannot fulfill a required deliverable such as Bluetooth operation, the design would have to implement either custom code or employ another framework.

Python Frameworks could include PyQt5 and TkInter. PyQt5 has most of the functionality of Qt5 but requires familiarity with C++ in order to take advantage of many class methods. TkInter is a basic GUI framework that lacks a large portion of functionality compared to PyQt5. TkInter could also be fully deployed under corporate licensure without permitting access to source code as it is in Python’s Standard Library. TkInter would also require additional front-end work to create an intuitive relationship between user interactions and visual objects.

Javascript frameworks could include Vue.js or Angular.js. Vue.js is both newer and more compact than Angular.js with a significant upward trend in popularity. Angular.js can be integrated into standalone apps for mobile devices or desktop operating systems and overcomes a general fault of javascript’s reliance on third party software to operate, such as Chrome. Vue.js renders graphics on the server-side and adds a layer of proprietary security at the cost of program speed. Angular.js possesses a larger codebase that would make the downloadable file larger and take up greater bandwidth. Angular.js is rendered on the client-side and is not necessarily dependent upon an internet connection to function.

As far toolkits of interest are concerned, there is either Qt-Designer and OutSystems Integration Studio. Both are open-source toolkits that add value to their respective frameworks. Both add excessive overhead to the development process for the cost of real-time visualization. Qt-Designer can be implemented for either PyQt on Python or Qt on C++. OutSystems Integration Studio utilizes Angular.js to create phone apps or web apps.

The software could be accomplished as a monolith, Model-Controller-View (MCV), or Humble View architecture. The monolith is the simplest and, theoretically, fastest architecture to employ during software design. Monolith programs have an exponential relationship between their size and how long it takes to produce or test the code. If the GUI can be created quickly and simply, this would be the best option. The MCV architecture allows for an increase in modularity to the software by separating out the intrinsic components of a GUI into individual modules that scale to fulfill the program requirements. Humble View architectures are an offshoot of the MCV architecture that strips out anything that cannot be tested by some automation and isolates them as visual objects and model objects have no functionality beyond being methodless data-classes. Humble View architectures require the most up front work but provide the most versatile development platform for continual development.

There are three recommendable development methodologies to implement with the project: Agile, Waterfall, and Spiral. Waterfall development is generally what engineers use and requires all constraints and deliverables to be known before planning out the project. Waterfall development is not flexible and moves from one stage of development to the next in a linear fashion. Agile development is the polar opposite of waterfall development and is most suited to GUI Software development as it emphasizes keeping a production worthy program at every stage of the development process that adds value iteratively. A compromise between these design methodologies would be spiral development. Spiral Development retains clear stages that are planned up front but has planned releasable deliverables that must be tested before moving onto the next stage with regular integration testing of prior code throughout each spiral.

Table 13: Software Alternatives Evaluation Table

Evaluation Basis | Python | C++ | Javascript
Environmental Factors | Permits use of commonly owned hardware preventing the need to purchase materials for addi-tional remotes | Permits use of commonly owned hardware preventing the need to purchase materials for addi-tional remotes | Permits use of commonly owned hardware preventing the need to purchase materials for addi-tional remotes
Economic Factors | Minimal develop-ment expenses | Balances develop-ment with security | Ability for minimal copyright infringe-ment expenses.
Public Health | N/A | N/A | N/A
Social Factors | Encourage STEM | Encourage STEM | Encourage STEM
Safety and Welfare | Allows for minimal interaction with powered hardware | Allows for minimal interaction with powered hardware | Allows for minimal interaction with powered hardware
Global Factors | Opportunity for multi-national imple-mentation | Opportunity for multi-national imple-mentation | Opportunity for multi-national imple-mentation
Cultural Factors | Opportunity for multi-national imple-mentation | Opportunity for multi-national imple-mentation | Opportunity for multi-national imple-mentation

Due to the importance of source code security and the intention of mass deployment, the software language should be C++. Python could cut down development time to less than a tenth of the C++ time but would require a C++ wrapper to deploy cleanly. However, the team lacks the experience of wrapping a C++ wrapper for Python in C++. In some sense, wrapping python code that wraps C++ with a C++ wrapper is redundant. Javascript would be the heaviest option if the team built a stand alone app or the least reliable option if the team built an app dependent on server-side operations. Javascript has no development advantage over C++ and has the option of server-side security features at the cost of reliability.

The framework of choice is Qt5 primarily based upon the team’s experience with it. The team has some experience with the Qt Framework and producing professional GUI apps. There are other frameworks that may be a better fit, but the codebase would have to be refactored post-production in order to become marketable. Additionally, fully open-source projects lack the depth and functionality that Qt has.

The design will not use any toolkit in the development of the software. Toolkits are generally beneficial for creating a quick and dirty program, but it is necessary to have a malleable program that can adapt to new, unforeseen problems and needs as is reflective in agile methodologies. Qt’s toolkit, Qt Designer, would build additional overhead and create a functional mapping nightmare when evaluating or testing the codebase. This choice will increase the development time-frame of an initial product by more than twenty times but will make the app versatile enough to create entirely new programs in less than 30 minutes which is impossible with a designer tool. This post production benefit of time saved is also true when library dependencies update and creates a product that has nominal upkeep costs.

The architecture of the GUI application should be a Model-View-Controller (MCV) architecture. This architecture would be a compromise moving towards an ideal Humble View architecture that sets the project in position to be refactored into a Humble View architecture. The MCV architecture will allow for a clean testing suite that allows due to its distinct boundaries based on code functionality. If the architecture can be implemented with functional programming, it will lead to an effective, modular codebase that could adapt to any business rule. The codebase is expected to be too large to handle a monolithic architecture. The time-frame of delivery is too short for implementing a Humble View architecture.

Due to the requirements of this PDD the design methodology for both the GUI application and microcontroller will be a spiral development methodology. These constrictions of the product force a waterfall front load of the design and development process with the objective of achieving a minimally viable product with specific deliverables already in mind. However, the project has too many unknowns and is too large to use a waterfall development methodology effectively. Thus a spiral design methodology is a balanced compromise between the agile and waterfall methods that allow the development tract to focus on one aspect at a time and bring that individual component to the minimally viable status until the whole project is presentable.

V. FINAL DESIGN
A. Battery Management, Power Supply, and Target Power Delivery

Most battery management and power delivery functions will be performed by the LTC4162-L monolithic charging controller as shown in the example circuit design below. Note that charging does not interrupt the power supply to the target device. The microcontroller may read and change the LTC4162 status and control registers through I2C, but is not required to directly manage the charging process. It may remain in a low-power state until an interrupt-on-change is triggered by SMBALERT.

The LTC4162-L can monitor input, output, and battery voltage, input and battery current, battery pack thermistor voltage, and battery impedance. The microcontroller will periodically query these measurements over the I2C interface and make them available via the GUI or LCD interface. The firmware can also set limits on these parameters and trigger a shutdown and error report if they are exceeded. An abnormally high or low battery impedance could indicate a defective or incorrectly installed battery pack.


Figure 9: 9V to 35V 2-Cell 3.2A Charger with PowerPath and 2A Input Limit [20]

The wireless receiver microcontroller will draw power from the installed Li-ion batteries though a suitable linear or low power switching/linear regulator.

Most important battery testing and safety procedures are handled automatically, as shown in the battery charging state diagram below. Charging does not begin unless batteries are detected and can draw and receive a test current while maintaining a stable voltage. In the event of an error a microcontroller interrupt may be triggered via the SMBALERT line for further error handling. Most faults will require the microcontroller to signal the wireless power transmitter to cease operation while notifying the user to take corrective action.


Figure 10: Battery Charger State Diagram [20]

Under normal circumstances the LTC4162-L will automatically charge Li-ion batteries in accordance with JEITA (Japan Electronics and Information Technology Industries Association) recommended charge curves. The thermistor circuit and charge curve coefficients are set by programmable registers. The standard JEITA charging profile is set by default. Current and voltage will automatically be limited when the temperature recorded near the battery pack is below or above the optimal charging temperature of 10 to 40 degrees Celsius.

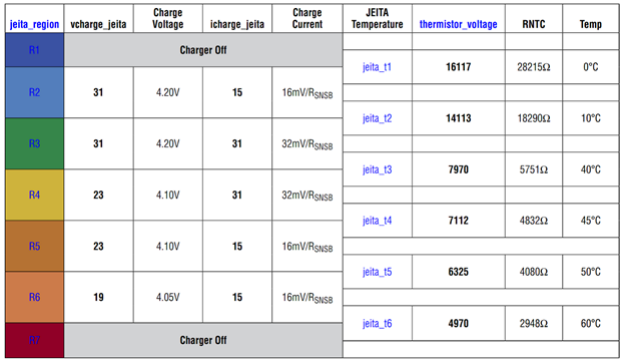
[picture p70: figure]

Figure 11: Tabular Representation of the JEITA system, Default JEITA Values and β=3490K Equivalent Temperatures [20]

Temperature is measured using a NTC thermistor circuit with a Beta of approximately 3490K. A Vishay NTCS0402E3103FLT is a recommended example. Appropriate values may be found by using Analog Devices’ NTC Calculator or by reference to the datasheet.

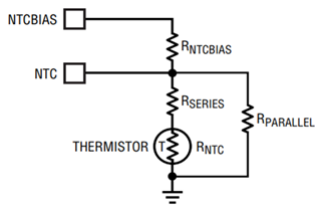
[picture p71: figure]

Figure 12: Recommended NTC Thermistor Circuit, Analog Devices: NTC Calculator

The LT4162-L is designed to operate at switching frequencies between 1Mhz and 2.5Mhz, with optimal performance at 1.5Mhz. At this frequency the switching inductor may be determined from:

L =

0.3 · VinMAX
1.5MHz

(1)

An appropriate inductor must have a saturation current well above the maximum charging current. The Coilcraft XGL6060 6.8uH is one possible example.

Two logic-level MOSFETs are necessary to control the input and battery paths. Their exact specifications will depend on the maximum load current and input and battery voltages.

The high frequency of the LT4162-L switching stage places special requirements on component selection and placement, particularly for bypass capacitors and switching components. The team will follow the manufacturer’s guidelines to minimize the risk of glitches or interference. Detailed recommendations for support circuitry and PCB layout are found in the Analog Devices LTC4162-L datasheet.

Reversal of the battery in the charger can create a hazardous condition. The team will implement appropriate protection circuitry to prevent this common user error from damaging the device or putting the user at risk. [30]

B. Transmitter and Receiver Voltage Regulators (3.3 V and 5 V)

The transmitter requires the power supplies regulated to 5V, 3.3V, and 30V. The expected input voltage is 48V.
Based on power requirements and input voltages the following parts are selected and simulated.

The 3.3 V (TPSM265R1V3SILR) voltage regulator is used for digital circuits.

The 5.0V (TPSM265R1V5SILR) voltage regulator is used for the transmitter amplifier driver, LCD backlight, and other low power circuits that require a 5V power supply.

Both voltage regulators have a wide input range of 3V to 65V and adjustable output voltages from 1.223V to 15V. Also, this series of buck regulators offers internally set output voltages that are commonly used such as 3.3V and 5V. That makes this part a good choice for this application because it reduces the number of components required and reduces the cost of the product. This part has a quiescent current of 0.5-µA which is very important for low power applications.

The maximum output current for both voltage regulators is 100mA.

It is not expected that 3.3V and 5V buck regulators will be providing a large output current (the expected current draw is from 50mA to 80 mA). The maximum output current estimate of 0.1A seems to be reasonable.

The same regulators will be used in the receiver subsystem since the power requirements in the receiver are also low [35].


Figure 13: 48 V to 3.33 V or 5 V Buck Down Converter Typical Schematic with Fixed Output [35]

C. Class E Amplifier 30V Voltage Regulator

The schematic below shows the TPS54160ADGQR integrated power supply that takes 45V-60 V input and regulates to 30.0 V. The power supply is optimized for 1 A output current. At 1 A load current total power dissipation is 1 W. The maximum output current is 1.5 A. The output voltage is set using the equation shown below. R2 (Rfbb) value is 10 kΩ and the desired voltage on the output is 30 V.

R1 = R2 ·

VOUT − 0.8V
0.8V

(2)

R1(Rfbt)= 10 kΩ³⁰⁻⁰.8
0.8 =365 kΩ
Output capacitor calculation based on the ripple voltage and capacitor equivalent series resistance (ESR)

IRIP P LE = 1.5 A = 1500 mA
VOUT RIP P LE = 0.3 V = 30 mV

COUT

1

8 · fsw

·

1

VOUT (ripple)

IRIP P LE

(3)

RESR = 30
1500 = 0.02 Ω

COUT =

1
8∗189870 ·

1
0.02 = 32.92 µF

The slow start capacitor is used to determine the minimum amount of time that will take for the regulator to reach the specified output voltage. In this case, the output voltage is 30 V. This feature is used to prevent large inrush currents and prevent overcurrent protection activation in the external power supply.

Slow start capacitor calculation are below.

CssnF =

tss · Iss[ms · µA]
VREF · 0.8[V ]

(4)

tss = 0.0027 s
Iss = 2 µA
Css =

0.0027·1.5
0.8

2 = 6.8 nF


Figure 14: 48 V to 30 V Buck Down Converter Simplified Schematic Diagram [34]

The circuit diagram below shows a complete voltage regulator schematic. The circuit is relatively simple with a total of 17 components. The circuit is optimized for 48V input voltage.

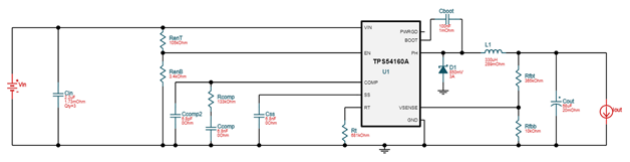
[picture p72: figure]

Figure 15: 48 V to 30 V Buck Down Converter Full Schematic Diagram

D. Transmitter Design

DC to RF Converter
Oscillator and Driver

The DC to RF converter consists of a temperature-compensated crystal oscillator (TCXO) connected to the buffer. The buffer is connected to the input of the class-E amplifier. The buffer circuit will be realized using Texas instruments GaN FET driver part number LMG1210. The crystal oscillator will be realized using TCXO from Abracon (part number AST3TQ-T-15.360MHZ-28). Both components are standard components that are readily available from many electronics parts vendors. AST3TQ-T-15.360MHZ-28 operates at 3.3V. The initial frequency tolerance is +/-0.3ppm. Supply current is 4.0mA at 10 MHz output carrier. The output waveform is a square wave with a minimum of 2.4V in a high state (VOH) and VOL 0.4V maximum [4].

The LMG1210 is a high-speed Gallium Nitride Field Effect Transistor (GaN FET) driver that operates up to 50MHz. The GaN FET driver requires a 6V minimum and 18V maximum supply voltage for proper operation. The driver is optimized for GaN FETs. PWM and EN digital inputs work with standard CMOS voltage levels. The GaN FET driver has two outputs for driving FETs on the high side and low side FETs. In this design, it is required to drive only low-side FET.

According to Texas Instruments, it is recommended to install a bypass 0.3 µF capacitor between Vdd and Vss to avoid undervoltage lockdown conditions. Also, to avoid ground bounce effects, it is recommended to insert an RC filter between the TCXO and the driver [19].


Figure 16: LMG1210 Internal functional block diagram [19]

Coil Driver
Class E-Amplifier

The transmitter operates at 13.56MHz. Precise frequency is generated by a crystal oscillator (TCXO). The oscillator output is buffered using a driver LMG1210 circuit. The output of the buffer is connected to the input of the class E amplifier.

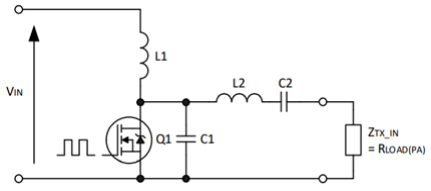
[picture p73: figure]

Figure 17: Topology of Class-E Amplifier

The topology of the Class-E amplifier is shown in the figure above. The figure above is generic and does not show passive components values. In order to determine passive components design, parameters must be established based on the design requirements and specifications. According to the design specifications, the operating frequency is 13.56MHz and output power is 30W.

Based on research the best way to achieve a 30W power level with a single-stage amplifier is to use GaN FET. This transistor is inexpensive ($3.34 ). Maximum Drain -Source voltage is 200V and the maximum drain current is 8.5A. The maximum on-resistance is 0.05 Ω. The maximum gate-source voltage is 6V and the minimum gate-source voltage is -4V [10].

The class E amplifier design eliminates the effects of capacitances within the MOS transistor which results in high-efficiency operation. This amplifier is a switching amplifier with a tuned RC network on the output. The transistor switches between two states zero voltage and zero current (on state and off-state). To achieve maximum efficiency, resistances in all components must be as low as possible. Those resistances include ESR of inductors and capacitors and on-resistance of the FET.

The following equations were used to determine passive components values

C1 =

1
2πfR(π²
4 + 1) π
2

(0.99866 +

0.91424
QL

−

1.03175
Q²
L

) + 0.6 (2πf) 2LI
(5)

C1 =

1
34.2219R

(0.99866 +

0.91424
QL

−

1.03175
Q²
L

) + 0.6
(2πf)

2LI

(6)

C2 =

1
2πfR

(

1
QL − 0.104823

)(1.00121 +

1.01468
QL − 1.7879

) −

0.2
(2πf)

2LI

(7)

L2 =

QLR
2πf | (8)

Load Resistance:

Rload = RESRL2 − ESRC2 − 1.365Ron − 0.2116ESRC1 | (9)

Ron is the resistance of the transistor

QL is defined as 2πf L2
R
R = ((VCC − Vo)

2
P

)0.576801(1.0000086 −

0.414395
QL

−

0.414395
Q²
L

+

0.205967
Q³
L

(10)

Where Vo is the transistor saturation offset voltage. Vo can be neglected because in this design a field-effect transistor is used [29].

Due to the complexity of the equations, it was necessary to set up an Excel spreadsheet for C1, C2, L1, and L2 calculations.

Calculations are performed using the formulas shown above. The results of all calculations are shown in the table below.

From the calculation data the Load resistance is 15.5Ω, L2 inductance is 0.9096 µH, C2 capacitance 203.2pF, and C1 capacitance is 1.65pF. L1 is selected arbitrarily and the value is 50muH. The calculations are based on the inductor L2 quality factor of 5 and supply voltage 30V.

Table 14: Alternatives Evaluation Table

PARAMETER | VALUE | UNITS
Frequency | 13.56 | MHz
L1 | 50 | µH
QL | 5
Transistor Saturation Offset Voltage Vo | 0 | V
Supply voltage VCC | 30 | V
Pout | 30 | W
Load Resistance R | 15.4988268 | Ω
L2 | 909.556 | nH
C1 | 1.65369 | pF
C2 | 203.206 | pF

The amplifier schematic is shown below.
The Receiver has multiple components and is one of the most critical components in the RF to DC converter

In this design, the RF to DC converter will be a full-wave rectifier bridge. The bridge will be realized using the Schottky diodes. Schottky diodes exhibit lower forward voltage drop, therefore, the rectifier circuit will produce lower power dissipation which will result in higher overall efficiency. The diode part manufacturer number is 80SQ045N. According to the manufacturer datasheet, the diode maximum forward voltage drop is 0.55V. The diode average rectifying current is 8.0A and the non-repetitive peak surge current is 140A. According to the manufacturer, the diode exhibits low-power loss at high frequency [2].

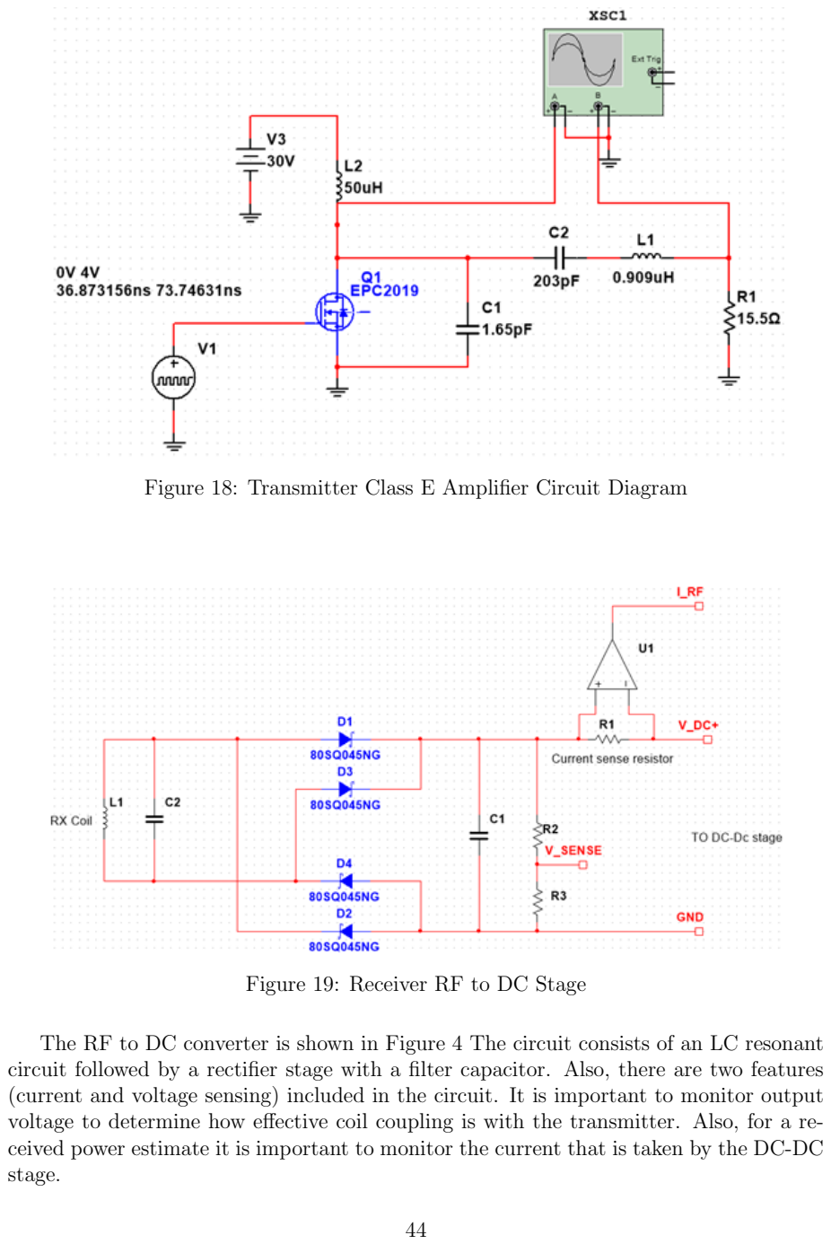
[picture p74: page 50]

Figure 18: Transmitter Class E Amplifier Circuit Diagram

Figure 19: Receiver RF to DC Stage

The RF to DC converter is shown in Figure 4 The circuit consists of an LC resonant circuit followed by a rectifier stage with a filter capacitor. Also, there are two features (current and voltage sensing) included in the circuit. It is important to monitor output voltage to determine how effective coil coupling is with the transmitter. Also, for a received power estimate it is important to monitor the current that is taken by the DC-DC stage.

Maximum power dissipation is estimated by assuming that that maximum current of 2.5A will be supplied to the DC-DC stage. This is the worst case scenario: power dissipation in the rectifier bridge is based on two forward voltage drops across diodes in the rectifier bridge.

PdissipationRB = 2VD · Imax = 2 · (0.55) · 2.5 = 2.75W | (11)
Filter capacitor C1 selection

The ripple voltage can be calculated using the following equation [23]:

Vr =

Vmax
2fRC | (12)

Required capacitance can be calculated based on ripple voltage on the output of the RF-DC converter

Let Vr = 0.1V.

C =

Vmax
2fRVr

=

Vmax
2fVrR

=

Imax
2fVr

=

2.5
2 · 13.56 · 10⁶
- 0.1
= 9.218 · 10⁻⁷F = 921.8nF | (13)
C ≈ 1.0µF | (14)
R1 and R2 are used to divide DC voltage to a level that is appropriate for sampling using an analog to digital converter (ADC). The AD converter maximum input voltage is 3.3V. Therefore, the sense voltage cannot exceed 3.3V. However, it is difficult to make an exact calculation for the unregulated DC voltage on the output of the RF to DC converter. The voltage may reach 50V on the output of the RF-DC stage.

Current sense resistor selection

Vo = VDC

R2
R3 + R2

(15)

R2 = R3(

VDC

VSENSE

− 1) | (16)

By assuming that 55V is the maximum voltage 50V + 5V for a safety margin.

The resistive divider resistor values are calculated by assuming that R3 is 10kΩ

And R2 is
R2 = 10k(

55
3.3
− 1) | (17)
R2 = 156.67kΩ | (18)
Therefore, R3 = 10kΩ and R2= 156.67Ω. Current sense

Current sensing will be realized using Texas instruments

INA197 has a gain of 50 V
V

. This amplifier has a wide common-mode voltage (from -16 to+80V), low error (3.0%), and a quiescent current of 0.9mA [15].

Because the maximum battery charging current is 1.25A it is realistic to assume that the current into DC/DC converter will not exceed 2.5A (that is double of estimated battery charging current on the battery side. Also, it is expected that the voltage on the RF-DC converter side will be higher than the voltage on the battery side. That means that under normal operation the current on the high voltage side will be lower than the current on the output of the buck converter. The expected efficiency of the buck converter is in the range from 80 to 90%.

If the current sense resistor is 20mΩ than the output voltage of the current sense amplifier can be calculated using the following equation

Vo = AvRsenseIV DCMAX = 50 · 0.002 · 2.5 = 2.5V | (19)

Maximum power loss (when IV DC = 2.5A) can be calculated using the the following equation

Pdissipation = IV DCMAX · Rsense = 2.5

2
- 0.02 = 0.125W | (20)
The figure below shows the current sense circuit implementation. The current sense resistor is connected in series with the load and amplifier input is connected across the resistor. The power supply for the amplifier is taken from the separate power supply that has a voltage in the range from 2.7V to 18V [15].

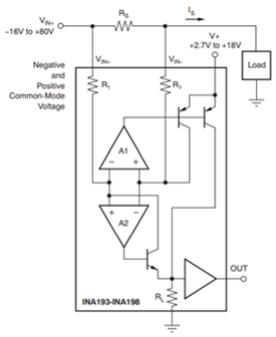
[picture p75: figure]

Figure 20: INA19x Reference Schematic Diagram [15].

E. Skin Depth Effects Calculations and Coil Parameters

The operating frequency influences the design of any WPT system. Throughout the WPT design it is important to consider the possible skin effects that RF current could possibly have on the copper coils. Since the WPT system would be operating at a high frequency of 13.6 MHz it is important to consider this element. Generally in a copper coil, the RF current will flow within a very small thickness of the surface of the conductor [5]. For this reason, if the skin depth is low, a copper tube could be implemented without any perceivable loss of functionality in the performance in the WPT system [5]. Typically conductors may have a relative permeability of very near to 1, so a µ value of 4π· 10-7 H/m may safely be assumed [8].

δs =

r
2
ω · µ · σ

=

r
1
π · f · µ · σ

(21)

The equation above is used to calculate skin depth [28] where: δs is the skin depth in meters (m), ρ is resistivity in ohm-meters (Ω·m), ω is frequency in radians, and σ is conductivity in siemen per meter ( S
m

or mho
m

).

Table 15: Skin Depths Effects in Copper Wire at High Frequencies

Frequency | Skin Depth (µm) | Skin Depth (m)
5 MHz | 29.15 | 2.915 x 10⁻5
11 MHz | 19.65 | 1.965 x 10⁻5
13.6 MHz | 17.67 | 1.767 x 10⁻5
16 MHz | 16.29 | 1.629 x 10⁻⁵

The table above shows the possible skin depths of a wide range of high frequencies from 5 MHz to 16 MHz in the copper material. The table shows that the coil’s copper wire may be replaced with tubing to lower its cost.

The planar spiral coils would allow the WPT system to have optimal power transfer between the transmitter and receiver. [5] The figure below shows the relationship between the coil dimensions, wire diameter, the spacing, and the number of turns.

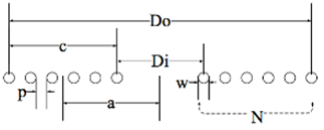
[picture p76: figure]

Figure 21: Cross-Sectional View of Flat Spiral Coil [5]

Di = Do − 2N(w + p) | (22)

Based on the amplifier inductance requirements, the coil parameters were determined: such as the length of the coil, the inner diameter, the winding radius, the radial depth of the windings, the inductance, and resistances at various number of turns. The type of copper tubing that is used has an outer diameter of 1/8 of an inch (3.175 mm) with a wall thickness of 0.03 inches (0.762 mm) [21].

Table 16: Copper Coil Inner Diameters Calculated at 90 mm Outer Diameter [21]

Outer Diameter (Do) [mm] | Number of Turns (N) | Spacing Between Coils (p) [mm] | Diameter of Coil (w) [mm] | Inner Diameter (Di) [mm]
90 | 3 | 3.13 | 3.175 | 52.17
90 | 4 | 4.81 | 3.175 | 26.12
90 | 5 | 5.04 | 3.175 | 7.85

l =

1
2
Nπ(Do + Di) | (23)

Where l is the length of wire [5]

a =

1
4
(Do + Di) | (24)

Where a is the winding radius [5]

c =

1
2
(Do − Di) | (25)

Table 17: Copper Coil Inner Diameters Calculated at 90 mm Outer Diameter with Winding Variables

Outer Diameter (Do) [mm] | Number of Turns (N) | Inner Diameter (Di) [mm] | Length [mm] | Winding Radius [mm] | Radial Depth [mm]
90 | 3 | 52.17 | 669.9 | 35.50 | 18.92
90 | 4 | 26.12 | 729.6 | 29.03 | 31.94
90 | 5 | 7.85 | 7685 | 24.46 | 41.08

Where c is the radial depth of the winding [5]

L(H) = N²

(Do − N(w + p))²
16Do + 28N(w + p)

(26)

Where L(H) is the inductance of the coil [5].

Table 18: Copper Coil Inner Diameters Calculated at 90 mm Outer Diameter with Inductance

Outer Diameter (Do) [mm] | Spacing Between Coils [mm] (p) | Number of Turns (N) | Length [mm] | Inner Diameter (Di) [mm] | Inductance [nH]
90 | 3.13 | 3 | 669.9 | 3.175 | 909.04
90 | 4.81 | 4 | 729.6 | 3.175 | 909.66
90 | 5.04 | 5 | 7685 | 3.175 | 909.60
C(F) = | 1 (2πf)

2L

(27)

Where C is the capacitance of the coil [5].

Table 19: Copper Coil Resonance Inductance and Capacitance at 13.6 MHz

Frequency (f) [MHz] | Inductance (L) [nH] | Capacitance (C) [pF]
13.6 | 909.04 | 150.65
13.6 | 909.66 | 150.55
13.6 | 909.60 | 150.56

RDC =

l
σπ(w/2)²

(28)

Where RDC is the DC resistance of the coil [5].

R = RDC

w
4δ

(29)

Where R is the total resistance of the coil [5].

Table 20: Copper Coil Skin Depth and Resistivity Calculations

Skin Depth [µm] | Width of Tubing (w) [mm] | Conductivity [MS] | Length [mm] | RDC [mΩ] | R [mΩ]
17.67 | 3.175 | 596 | 669.9 | 1.4197 | 63.80
17.67 | 3.175 | 596 | 729.6 | 1.5462 | 69.46
17.67 | 3.175 | 596 | 768.5 | 1.6286 | 71.58

Q =

1
R

r
L
C

(30)

Where Q is the quality factor of the coil [5].

Table 21: Quality Factor Inputs and Outputs

Inductance (L) [nH] | Capacitance (C) [pF] | R [mΩ] | Q
909.04 | 150.65 | 63.80 | 1217
909.66 | 150.55 | 069.46 | 1119.09
909.60 | 150.56 | 71.58 | 1085.87

F. MSP430FR5994 Microcontroller

The 16-bit RISC architecture MSP430FR5994 contains 256 KB FRAM, and a clock that can reach 16MHz. This microcontroller writes at a rate of 125 ns per word using ultra low power. Being fairly resistant to radiation and nonmagnetic, the voltage supply of this device goes from 1.8 V to 3.6 V, as restricted by regulations. [32]


Figure 22: Functional Block Diagram [22]

This system is advanced and flexible, performing under very low power within an active mode of 118 µA/MHz. Its standby conditions include VLO and real time clock. VLO of current 500 nA, and real time clock of 350 nA. For the shutdown, 45 nA. This microcontroller contains 8KB SRAM, which gives a maximum of 264KB to be used among code and data sections [32]. The MSP430FR5994 also contains Low-Energy Accelerator (LEA), which gives a highly efficient while low power acceleration, making it easier for the microcontroller to acknowledge analog data coming in. This operation is independent , with 4KB RAM shared with the CPU. [22]

There are quite a few peripherals integrated within this device which include comm ports, real time clock, AES encryption, error checking modules, real time clock, interrupts, timers, and comparators. It is worth mentioning the smart technology within these, which include 16 bit timers, RTC with functions such as calendar and alarm, internal DMA up to 6 channels, and a 32 bit multiplier. [32]


Figure 23: Comparison Within MSP430 Family [22]

Within its flexibility, the clock system offers a frequency that is DCO fixed, and with up 10 options. As mentioned earlier, VLO is included. The crystals in this system are also very high frequency, 32 kHz. Important to the user is also whether the microcontroller is secured, and AES encryption and decryption coprocessor guarantees that, with a size of either 128 or 256 bits. Random number seed (RNS) used for algorithm writing, as well as the use of IP address encapsulation to ensure no access from the outside can be granted. [22]

The MSP430FR5994 has an improved serial link, with up to 4 serial comm ports, UART with Baud rate detection, as well as IrDA encode and decode. This device’s input and output ports are multifunctional, with pins supporting capacitive touch (no need for outside components). Featuring bits that are easily accessible, programmable port pull-up and pull-down, and edge wake port from LPM. With high performing analog features it is a 16 channel comparator, and 12 bit ADC that features window comparator, sample-and-hold, and maximum of 20 external input channels. [22]

The team purchased Launchpad kits to test the battery circuit with these microcontrollers. The system will be using two of these, one for the transmitter and one for the receiver. The receiver microcontroller will communicate with the transmitter and GUI. The MSP430FR5994 will also gather battery data.

Table 22: MSP430FR5994 Parameters [22]

Features | DMA, Low-Energy Accel-erator (LEA), Real-Time Clock
Non-volatile memory (kB) | 256
RAM (KB) | 8
ADC | 12-bit SAR
ADC: channels (#) | 20
GPIO pins (#) | 68
I2C | 4
SPI | 8
UART | 4
Comparator channels (#) | 16
Approx. price (US$) | 1ku | 3.08
Timers – 16-bit | 6
Bootloader (BSL) | UART
Special I/O | N/A
Operating temperature range (C) | -40 to 85
Rating | Catalog
G. Software

Table 23: Table of Software Utilized

Language | C++
Framework | Qt
Toolkit | None
Architecture | MCV
Development Methodology | Spiral


Figure 24: Graphical User Interface Architecture UML Diagram

VI. SUBSYSTEM SIMULATIONS

A. Transmitter Simulation

In this simulation calculated components are verified
The amplifier circuit was simulated using Multisim software.
The amplifier circuit was simulated using calculated capacitors and inductors values.

Simulation data is shown below:
DC supply voltage was 30V.
DC supply current was 0.878A.
Output Average Power 26.7W (measured in simulation). However, the calculated power is lower than the power measured by the probe. This could be a problem with Multisim power measurements.


Figure 25: Class E Amplifier Simulation


Figure 26: Class E Amplifier Output Voltage and GaN FET Drain Voltage

The figure above shows waveforms on GaN FET Drain (lower trace ) and output (across R1) upper trace.
The output voltage across the 15.5 Ω resistor is 56.6 Vp−p and the drain voltage is 117 Vp−p.
Based on the simulation data input power Pin = VDC IDC = 30 (0.878) = 26.34W. The output power POUT = VRMS/R1 = 202/15.5 = 25.83W.
Efficiency η = Pout/Pin = 25.83/26.34 = 0.98.
The simulated efficiency is 98%. However, the simulation includes ideal passive components and it is expected that the efficiency of the real circuit is lower.

B. Receiver Simulation

The receiver Rf-DC simulation circuit is shown in the figure below.
The coupling factor between the generator coil and the receiver coil was 0.95 Simulation results.
Input RMS current was 1.40A.
Input RMS voltage was 23.25V.
Output current into 20Ω load was 1.15A.
DC voltage across load was 22.93.
The current sensor amplifier current was 412.278mV. Vsense voltage was 1.383V.

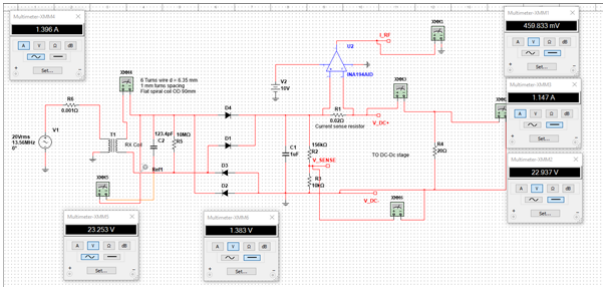
[picture p77: figure]

Figure 27: Receiver RF-DC Converter

Input power Pin= Vinrms· Iinrms = 23.25 · 1.40 = 32.55W Output power Pin= Vout· Iload = 22.93 · 1.15 = 26.37W
Efficiency η= Pout/Pin = 26.37/32.55 = 0.81
Efficiency η= 0.81

The expected efficiency was 80%. Simulation efficiency is 81%. It is important to select fast recovery diodes with a low forward voltage drop to improve efficiency.
The Current sense amplifier has the wrong gain. The current sense amplifier part number is correct but the gain looks lower (20V/V instead 50V/V). In the simulation was used the correct part with a gain of 50 V/V.
V sense voltage has correct scaling.

C. Battery Management, Power Supply, and Target Power Delivery Simulation

Simulation of the charging operation and microcontroller interface will be performed with an Analog Devices DC2038A-J demonstration board. This board contains an LTC4162 reference charging circuit and permits GUI or programmed monitoring and control of all registers during charge and discharge cycles. It will be used as an operational reference and as a development platform for the wireless power receiver firmware. In the following example, an input power supply of 16V and 4A is supplied to Vin. The circuit provides power to Vout while simultaneously charging a simulated battery.

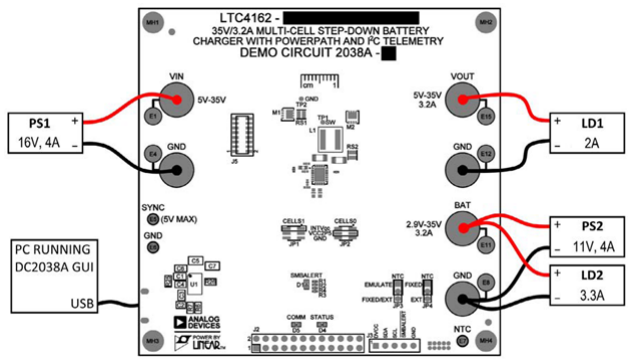
[picture p78: figure]

Figure 28: LTC4162 Demo Board Layout [9]

This hardware simulation may be performed with real batteries, which will make it possible for us to evaluate specific target battery configurations and expected charging temperature and behavior under load.

A GUI and onboard microcontroller permits real time monitoring of charging state and all control and status registers.


Figure 29: LTC4162 Demo Board Output GUI [9]

Note that the current and voltage supplied to the battery depends on battery temperature and the current charge state. The DC2038 and GUI tools may be used to configure and test JEITA charge thresholds.


Figure 30: LTC4162 Demo Board Simulated Performance [9]

At a later stage of development, the on-board microcontroller will be bypassed and our MSP-EXP430FR5994 will interface directly with the LTC4162 over I2C.
This development hardware will make it possible for us to refine and test our power delivery system design and firmware with real hardware before taking on the challenges of layout and PCB fabrication.
D. Software Testing Protocol

The software testing will incorporate three distinct categories: 1) functional unit testing, 2) mock-up unit testing, and 3) integration testing. Functional unit tests will be utilized to ensure continuous integration during development so that a new piece of code does not break any pre-existing code. Mock-up unit tests will be utilized to ensure that a component or section of the software and/or hardware communicates according to the proper algorithm and accepts appropriate messages at their respective ports. Mock-up unit tests will be compartmentalized with each software component integrated with that software’s hardware components only. Unlike mock-up testing, integration testing will involve actual communication between the microcontrollers and both other microcontrollers and the GUI. Integration testing will be composed of manual and automated tests conducted from a central virtual machine or server.

E. Buck Down Converter Simulations

Both voltage regulators based on the TPSM265R integrated circuit are simulated using the Texas Instruments Webench simulator. The data shown below is a summary of the simulations.

The schematic of the 3.3V circuit is shown below.

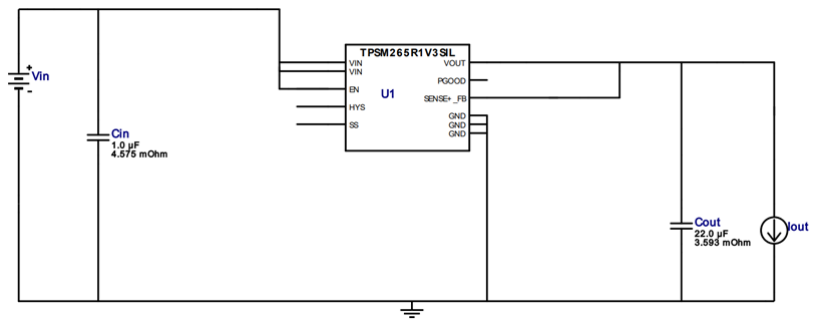
[picture p79: figure]

Figure 31: Schematic Diagram for TPSM265R1V3SILR (3.3 V Regulator)

The largest ripple voltage observed in simulation at full load was 8 mV.

According to the simulation, startup time is 1.14 ms.

Expected efficiency for 48V input vs. load current is given in the graph below. The lowest efficiency is around 67.8% at the highest load current (0.1 A). The power dissipation according to the simulation is 0.16 W.

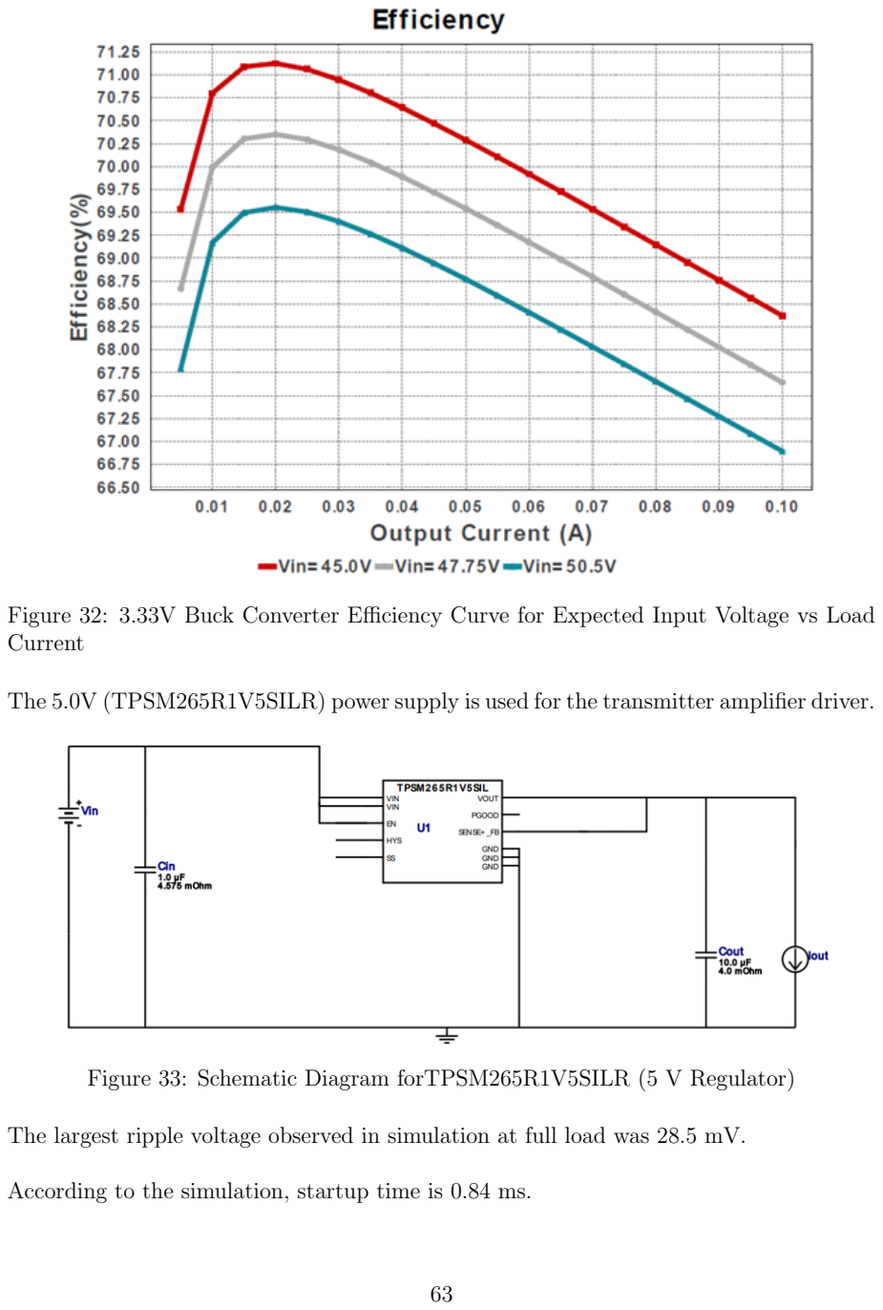
[picture p80: page 69]

Figure 32: 3.33V Buck Converter Efficiency Curve for Expected Input Voltage vs Load Current

The 5.0V (TPSM265R1V5SILR) power supply is used for the transmitter amplifier driver.

Figure 33: Schematic Diagram forTPSM265R1V5SILR (5 V Regulator)

The largest ripple voltage observed in simulation at full load was 28.5 mV.

According to the simulation, startup time is 0.84 ms.

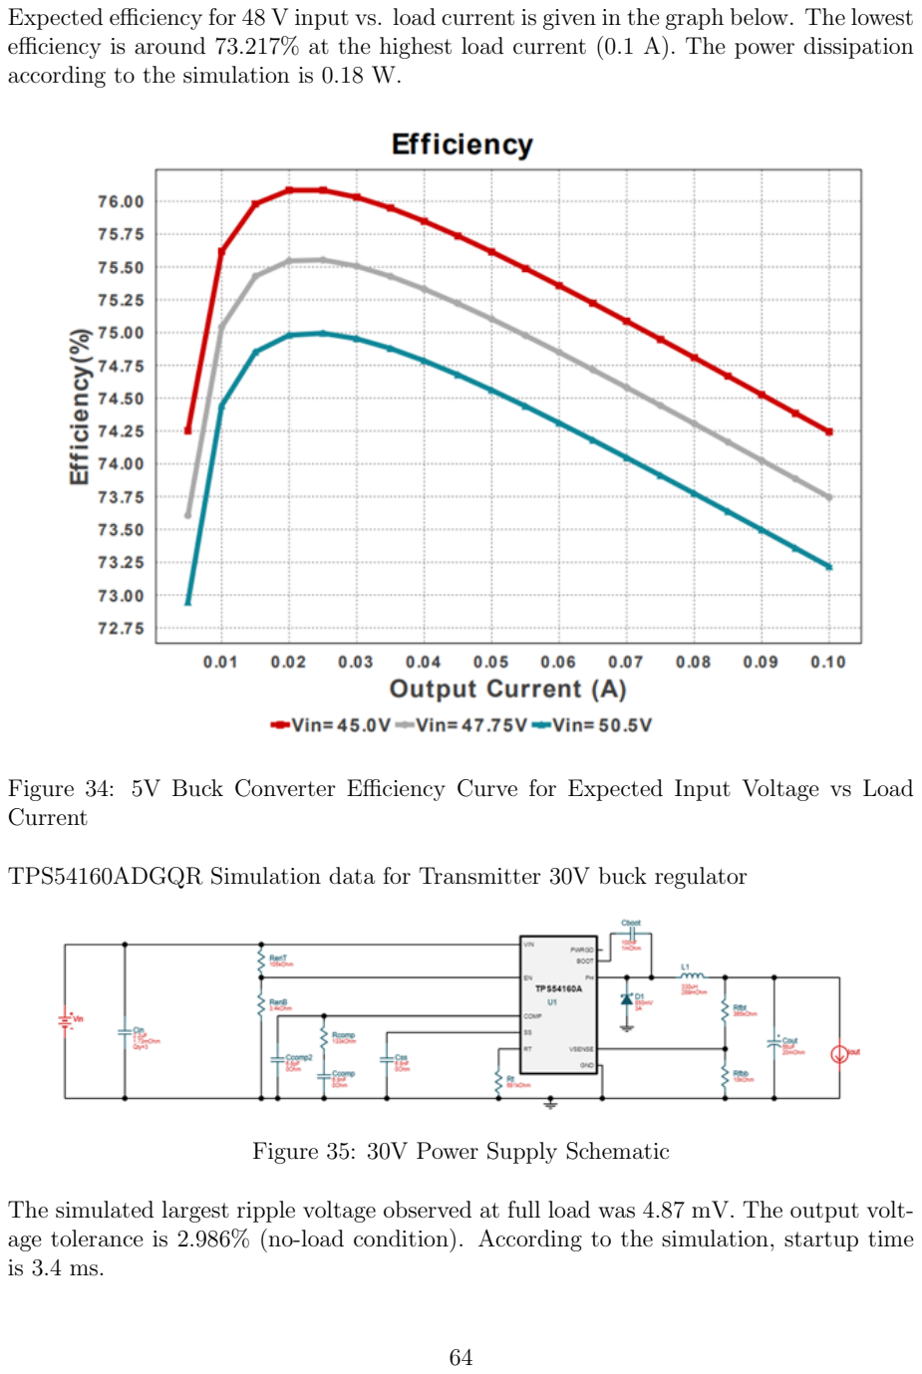
[picture p81: page 70]

Expected efficiency for 48 V input vs. load current is given in the graph below. The lowest efficiency is around 73.217% at the highest load current (0.1 A). The power dissipation according to the simulation is 0.18 W.

Figure 34: 5V Buck Converter Efficiency Curve for Expected Input Voltage vs Load Current

TPS54160ADGQR Simulation data for Transmitter 30V buck regulator

Figure 35: 30V Power Supply Schematic

The simulated largest ripple voltage observed at full load was 4.87 mV. The output voltage tolerance is 2.986% (no-load condition). According to the simulation, startup time is 3.4 ms.

Expected efficiency for 48 V input vs. load current is given in the graph below. The lowest efficiency is around 96.76% at the highest load current (1.0 A). The power dissipation according to the simulation is 1 W.


Figure 36: 30V Buck Converter Efficiency Curve for Expected Input Voltage vs Load Current

VII. FINAL DESIGN SPECIFICATIONS

A. Feasibility Study

The design consists of two subsystems: the transmitter and the receiver. This product is expected to be used by hobbyists and prototype designers for different applications that require contactless charging. There is no similar device available in the price range from $200 to $400. The expected cost of the charger system is $300. There are some commercial chargers available right now and the cost of that system is $2000. The price of $300 per system will make wireless charging affordable for hobbyists and freelance hardware developers.

The design tools such as Altium designer and Multisim simulator are available free of charge to all group members using the provided UT Tyler license. Also, parts manufacturers are providing free simulation and evaluation tools for development. In addition to the software evaluation kits may be required for testing certain parts of the system such as the microcontroller, Bluetooth module, and the battery charger controller. Most of those evaluation modules are already purchased and they are available to team members. Evaluation kits are purchased by Indus instruments.

The system is designed such that it uses standard components that are available at any electronic components store and they can be purchased without restrictions. PCB fabrication will be given to a company located in China that is offering quick turnaround PCB fabrication and fast shipping. Components purchasing and printed circuit board assembly will be done at Indus Instruments. Indus Instruments have all the necessary equipment that can handle surface mount components.

All test equipment required for development and testing will be available. Indus Instruments will provide space and necessary test equipment for the wireless charging system prototype evaluation and testing.

The final product cost is estimated at around $300 (for small quantities). Most likely for larger quantities, it is possible to decrease the cost even more.

B. Microcontroller

There are four aspects to analyze: economics, technical, legal, and scheduling. A single MSP430FR5994 part costs about $3 to $4, while the MSP-EXP430FR5994 Launch-Pad kit costs $16.99. Considering the team will have only two of these microcontrollers (one for the transmitter and one for the receiver), this is a cheap and reasonable cost. [22 & 31] [22] [32]. On the technical side, this microcontroller’s memory, voltage supply limitations, UART and I2Cmode specifications, and overall low power consumption makes it the ideal model for our project needs [22]. Some of the most important standards TI’s MSP430FR5994 complies with include ANSI, JEDEC, and ESDA [22]. Lastly, the team already has in hands the LaunchPad kit for the microcontroller. The individual microcontrollers are also ready-to-purchase items with delivery times of less than 7 days. More testing will be done once the team has the first PCB design in hands.

C. Transmitter Coil

The circular planar coil was the most inexpensive approach, the copper tubing to make the coils has an approximate value of $15.99. The design properties also significantly contributed to reducing the complexity of acquiring the main coil parameters. It was important to take this factor into account because of the time constraint of two months. In order to reduce the complexity in our project, the spiral planar design was the best option.

The calculation of the inductance formula in the planar spiral design was easier to acquire than the other two proposed solutions. This was crucial because it significantly gave the project a higher chance of matching the predestined inductance of the circuit

requirement of .909 µH.

The economical and ethical considerations did not affect our decision making as much, due to the fact that there were not many differences. Furthermore, this design was appropriate for our project and the team does have the budget, resources and time to successfully to implement this design.

In order for the project to have a stronger chance of successfully providing a prototype, the best option was the planar spiral coil design. This design will allow the project to more likely have a chance of being completed within the time constraint as well it reduced the complexity of the formulas implemented in the calculations. It also allowed for the project to be completed in a much easier and efficient manner.

D. Transmitter

The transmitter class-E amplifier circuit was simulated and efficiency was 98%. The actual transmitter efficiency will likely be around 90% with the actual circuit. In the simulation, it was determined that the current required to power the class-E amplifier is 0.9 A at 30 V. The power for the transmitter will be supplied by using an external 48 V AC to DC converter followed by a step-down converter in the transmitter subsystem.

The main concern in this subsystem is the immunity of the supporting circuits to the RF electromagnetic field generated by the transmitter coil. The transmitter coil placement must be done such that the electromagnetic field has minimal effects on the electronic circuits in the transmitter. The transmitter sensitive electronic parts may require EMI shields.

During the simulation, the high voltage across the coil was observed. The highest voltage observed was 320 Vpp. That voltage poses a serious electric shock hazard. Therefore, the transmitter coil insulation must be capable of withstanding voltages that are in the 500V to 1kV range to provide a safety margin for the design. One way of achieving this is to make a plastic box that would contain the transmitter coil and have insulation that is capable of withstanding voltages in the 500 V to 1000 V range.

Heat dissipation in the Class E amplifier circuit is expected to be around 3W (based on the efficiency of 90%). That dissipation will occur in inductors, capacitors (due to ESR), and the amplifier transistor. The transistor will have a proper heatsink to prevent overheating. Since the dissipation in the transistor is very small (on-resistance is 50 mW) the proper thermal management will be achieved on the printed circuit board. Coils used in the transmitter will be designed such that the col resistance is minimized which also will decrease the heat dissipation in the transmitter circuit.

E. Receiver

There is a possibility that the receiver RF to DC stage performs with higher losses than the losses that were determined in the simulation. According to the simulation data, the RF to DC conversion will be 81% efficient. In the system specification, the conversion efficiency is set to 80%. It is important to keep efficiency above 80% to prevent excessive heat generation. If received power is 25W and efficiency is 80% then power dissipation is 5 W.

The excessive heat may have adverse effects on battery life and the speed of charging [35]. A higher temperature environment requires lower charging currents to prevent further temperature rise and damage to the battery cells. Also, excessive heat generation must be minimized to avoid the use of fans and large heat-sinks. Heat-sinks and fans would increase the cost and the size of our product. If during the prototype test phase efficiency drops below 80% the circuit must be redesigned to achieve the target specification efficiency.

One problem that is likely to occur is the interference in the battery charging and communication link circuits caused by a strong electromagnetic field generated by the transmitter coil. Even though all good practices will be followed for the circuit board design the electromagnetic interference still may not be prevented. Charging circuit disruption can cause battery failure due to overcharging or overheating. If this problem occurs the additional EMI shielding will be required. The shielding includes placing metal boxes over sensitive electronic subcircuits and placing additional filters in series with DC power supplies for sensitive parts such as a microcontroller, Bluetooth module, and charger controller.

F. Thermal Considerations for 3.3V and 5V Voltage Regulators

According to the simulation data both parts have small power dissipation. The largest power dissipation is 0.18 W (5.0V regulator).

The graph below provides thermal resistance junction to ambient as a function of the printed circuit board. The equation below can be used to find the required thermal resistance junction to ambient (ΘJA). The estimated ambient temperature in the transmitter is 45◦C.

ΘJA =

125◦C − TA(max)

PD(max)

◦C
W
(31)

ΘJA =

125−45

0.18 = 444.44 h
◦C
W

i

The estimated transmitter PCB area will be around 100cm2. Given the board size and thermal resistance vs. board size, those regulators will have a proper heatsink.

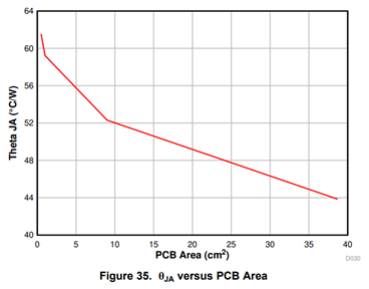
[picture p82: figure]

Figure 37: Thermal Resistance vs. PCB Area [35]

Thermal considerations(for class E amplifier voltage regulator (30V, 1.0A buck converter)

TA(max) = TJ(max) − RT H · PT OT | (32)
- PT OT is the total device power dissipation in [W]
- TA is the ambient temperature in [◦C]
- TJ is the junction temperature in [◦C]
- RT H is the thermal resistance of the package h
◦C
W

i

- TA(max)

is the maximum ambient temperature in [◦C]

- TJ(max)

is the maximum junction temperature in [◦C]

The expected ambient temperature is 40◦C (that is temperature inside the transmitter enclosure).
Thermal resistance for a standard board (ΘJA) is 62.5h
◦C
W

i
[34].
From the simulation the total power dissipation is 1 W.
From the recommended operating conditions the maximum junction temperature is 150◦C [34].
Based on the data from the simulation and the datasheet the maximum ambient temperature can be determined

TA(MAX) = TJ(MAX) - RT H*PT OT
TA(MAX) = 150 – 62.5*1 = 87.5◦C

The expected ambient temperature is lower than the maximum temperature calculated based on simulation data. Therefore, this part will operate within specified recommended conditions in the datasheet.

G. Charging Subsystem

The LTC4162-L is designed to manage a power path between an external input power source Vin, an output power Vout, and an installed battery pack. When external input power greater than the battery voltage is available at Vin, the LTC4162 will route Vin to Vout and charge the connected battery. If external power is interrupted or falls below Vbat, battery power will be automatically routed to Vout. As long as the battery has charge or a power source exists at Vin, Vout will be supplied with power, but the voltage will range from Vbat to Vin. In order to provide consistent voltage to the target device output power should be drawn directly from the battery. Leaving Vout unused allows the maximum power point tracking feature to operate with optimal efficiency.

The LTC4162 draws power directly from Vout and has its own internal LDO linear regulators. All other components of the wireless receiver PCB must be powered by an appropriate DC-DC stage at Vout that can convert any potential input voltage (i.e. 7.4-35
V) to the required operating voltages of 5 V and 3.3 V. These circuits will require power in order to operate and initiate charging. In the event that the battery is severely depleted and cannot power the microprocessor and Bluetooth interface, it will be necessary for the transmitter to be capable of initiating charging independently.

Since the LTC4162 has only an internal buck voltage regulator, the wireless power receiver subsystem must provide power to Vin that is higher than the voltage of the battery but below the maximum input voltage of 35V.

The LTC4162 approaches 95% efficiency at recommended switching frequency when the input voltage is no more than approximately 5V above battery charging voltage, and surpasses 90% in less ideal configurations. Heat losses will be in the range of three watts or less. It has a ΘJC of 3.4 h
◦C
W

i
and will be soldered to a four-layer PCB. The team does not anticipate any thermal management issues with this circuit.
H. Battery Considerations

Li-Ion batteries offer superb performance and high energy density, but require special attention to safety. Under normal circumstances the LTC4162-L will monitor battery voltage and avoid overcharging. A NTC thermistor will allow the LTC4162 to monitor local charging temperatures and limit current in accordance with JEIDA recommendations.

For safety reasons, the team requires stricter battery specifications than originally planned. While our charger’s thermistor can limit charging current in response to ambient temperature extremes, it cannot monitor individual cells–particularly if the battery pack is intended to be modular. While it can recognize and respond to abnormal battery voltages or short conditions, it cannot automatically determine maximum safe charging current. Any battery pack used must have a maximum charge current greater than the maximum current delivery of the charger. Battery packs must also meet UL1642 and IEC61960 standards and contain internal protection circuitry to limit charge and discharge currents and protect against thermal runaway.

The LTC4162 can deliver a maximum of 3.2 amps and has an efficiency of up to 95%. Assuming optimal efficiency and 26 W output from the wireless receiver, the charging voltage must be at least frac25W3.2A = 7.8 V in order to fully utilize the available power. Since the voltage of a typical Li-Ion cell is 3.7 V and the charging voltage is 4.2 V, the target battery pack should consist of two or more cells in series. The LTC4162 supports 1 to 8 cell series arrangements provided the input voltage is adequate. Optimal arrangements would include a 7.4V pack rated for 3.2 A charging, a 11.1 V pack rated for 2.2 A charging, or a 14.8 V pack rated for 1.7 A charging. The number of cells is set by selection pins and may be configured by a DIP switch or jumpers. It is not necessary to specify a specific number of cells for suitable battery packs, provided that they meet UL1642 and IEC61960 standards. The optimal balance of safe charging rates and performance will likely be found with packs utilizing six to eight 18650 cells or the equivalent. The power delivery estimates above are optimistic and actual power delivery from the charger may not reach these levels. As prototyping progresses, it will be possible to refine battery recommendations and expected charging times.

Ideally, up to 25 W will be delivered to the battery pack, making the battery the largest potential source of heat in our system. Since the battery pack is intended to be a modular, removable component with flexible specifications, it will not necessary for it to be enclosed with the wireless receiver PCB and receiving coil. It will be connected by an appropriate low-loss cable and connector, and exact placement will be determined by the user application. For this reason, the team has specified that only battery packs with internal temperature monitoring and protection circuitry should be used with this charger.

Our original specifications suggested that the charging subsystem would be capable of detailed monitoring of battery health and charge state. The team has learned that this type of information must be obtained at the individual cell level by a specialized controller which is usually integrated into the battery pack itself. Our charge subsystem can only recognize an approaching low-battery condition by a drop in voltage, and cannot estimate battery capacity except by calculation using charging voltage, charge times and currents, and such data would be of limited use considering battery aging and user-replaceability. It will be possible to notify the user and target device of a drop in battery voltage, but more detailed fuel gauge and battery health information will require an SMBus enabled smart battery. An I2C line on the MSP430FR5994 will be reserved for communication with an optional SMBus capable smart battery pack. If feasible, optional battery pack telemetry may be polled by firmware and reported to the user along with the data already available from the LTC4162.

All the parts and design resources needed to complete the charging and power subsystem are readily available. Constructing this subsystem within the projected time-frame is feasible.

Table 24: Final Design’s Charging Subsystem Specifications

DC-DC stage from wireless receiver to Vin | May not be necessary, pending further determination of wireless receiver output voltage
DC-DC stage from Vout | 5V at 100mA; 3.3V at 100 mA
Battery Requirements | UL1642 and IEC61960 compliant Li-Ion packs with 7.4-15 VDC nominal output voltage
Maximum Charging Current | 3.2A (7.4V); 2.2A (11.1V); 1.7A (14.8V)
Provision for optional smart battery health and fuel gauge monitoring | Reserved I2C line from MSP430FR5994 with buffering

I. Microcontroller Considerations

The MSP430FR5994 has a body size that ranges from 6mm by 6mm to 12mm by 12mm depending on the package the group purchases, 8KB RAM, 68 GPIO pins, 4 I²C, 4 UART, up to four serial communication ports, and 20 ADC channels. The MSP430 series include limitations that range from safety to performance [22].

Relevant limitations to the project include:

1. ESD (Electrostatic discharge) ratings. For a human-body model, safe discharge ratings are around 500 V to 1000 V, while for a charged-device model, safe discharge ratings are around 250 V. These regulations are taken from JEDEC JS-001 and JESD22-C101 respectively [22].
2. Absolute maximum ratings: voltage applied to any pin must be within -0.3 V to 4.1 V, voltage difference between DVCC and AVCC pins must stay within -0.3 V to 0.3 V (if not, writing errors could occur to RAM and FRAM), and current at any device pin must have a maximum of -2 to 2 mA [22].
3. Supply voltage applied should be within 1.8 V to 3.6 V, maximum ACLK frequency should be 50 kHz, and maximum SMCLK frequency should be 16 MHz [22].
4. For the eUSCI I²C, eUSCI (enhanced universal serial communication interface) input clock frequency should not exceed 16 MHz, SCL clock frequency should not exceed 400 kHz [22].
J. Firmware Requirements: Transmitter

The Wireless Power Transmission Stage (Transmitter) will be controlled by an MSP430FR5994 running custom firmware. The firmware must meet the following requirements:

1.) Activate or deactivate wireless transmitter.

2.) Respond to commands received from a Bluetooth link with the Wireless Power Receiver Stage (Receiver), which may include requests for power delivery measurements or instructions to initiate or cease charging.

3.) Continuously monitor wireless power transmitter current and voltage and calculate delivered power.

4.) Automatically cease power transmission when the Receiver requests a shutdown or if severe interference is detected.

5.) Communicate operating status to the Receiver via Bluetooth, and directly to the user via fault LED’s or an installed LCD.

K. Firmware Requirements: Receiver

The Wireless Power Receiver Stage (Receiver) will be controlled by an MSP430FR5994 running custom firmware. The firmware must meet the following requirements:

1.) Link to the Transmitter over Bluetooth.

2.) Link to user GUI device over Bluetooth.

3.) Link to an optional UART connection with the target device.

4.) Respond to queries or instructions from the Bluetooth connection to the user GUI or from the optional UART connection.

5.) Monitor charging state and battery status though I2C connection with LTC4162 and optional SMBus link with smart battery.

6.) Recognize low voltage state or optional low capacity battery warning and notify the user and target device.

7.) Signal the Transmitter via Bluetooth to initiate charging when instructed by the user or target device.

8.) Continuously monitor wireless power receiver current and voltage and calculate delivered power.

9.) Monitor reported power transmission from the Transmitter, compare it with received power, and recognize excessive power losses that could indicate unsafe interference conditions

10.) In the event of excessive transmission losses, instruct the Transmitter to cease power transmission. Notify the user and target device of the error condition.

The Transmitter and Receiver firmware will be developed with Texas Instruments Code Composer Studio. The team has suitable Launchpad development boards and access to all necessary documentation and libraries are available. The team is composed of multiple experienced programmers in our group. The firmware requirements are limited and well-defined and completing it within our scheduled time-frame is feasible.

L. Software Requirements: GUI

The GUI will be operated on multiple platforms and rely upon QT5 to operate. The software must fulfill the following requirements:

1.) Provide connection to transmitter and receiver for the product’s user that grants sufficient control over the product’s hardware

2.) Serve as a platform for custom messages to and from the user’s device connected to the receiver.

3.) Provide alert system via push notifications and continuous monitoring of the transmitter and receiver.

M. Coil Considerations

Table 25: Final Design’s Coil Tubing Specifications

Material | 122 Copper
Tube Size | 1 [in] 8
Outter Diameter (OD) | 1 [in] 4
Wall Thickness | 0.049 [in]
Inner Diameter (ID) | 0.152 [in]
Fabrication | Seamless
Bending Method | By hand
Temper Rating | Soft
Compatible Tube Fittings | Compression, Solder Connect
Specifications met | ASTM B75 RoHS 3(2015/863/EU) Compliant
Resistivity | 1.68 x 10⁻⁸ [Ω/m]
Conductivity | 5.96 x 10⁷ [S/m]

This tubing has good corrosion resistance and excellent heat transfer qualities. All tubing meets international standards for copper tubing. Important to note: Tube size is an accepted industry designation, not an actual size [8].

Table 26: Final Design’s Receiver Coil Specifications

Outside Diameter of Coils (Do) | 90 mm
Number of Turns | 4
Length | 729.6 mm
Spacing | 4.81 mm
Width of Tubing | 3.175 mm
Inner Diameter (Di) | 26.12 mm
Winding Radius | 29.03 mm
Radial Depth | 31.94 mm
Inductance | 909.66 nH.
Capacitance | 150.55 pF
Frequency | 13.6 MHz
Resistance (Dc) | 1.5462 mΩ
Total Resistance | 69.46 mΩ
Quality Factor | 1119.09

N. Specification Summary

Table 27: Final Design’s Receiver Specifications

Charge time(4Ah Battery Pack) | 5 Hours Max
Battery pack voltage | User Selectable: 7.4V-14.2 V
Coupling Efficiency Transmitter to Receiver | 90%
AC-DC Conversion Efficiency | 80%
Charging Controller DC-DC Converter | 85%
Overall Receiver Conversion Efficiency | 61.2%
Battery Requirements: | UL1642 and IEC61960 compliant Li-ion packs.
Maximum Battery Charging Current | 3.2A (7.4V); 2.2A (11.1V); 1.7A (14.8V)
Charger Subsystem Charge Protocol | Constant Current Constant Voltage (Li-Ion Battery)
Battery Type | UL1642 and IEC61960 compliant Li-Ion packs; 7.4-15 VDC nominal output voltage.
Power Negotiation | Using Bluetooth 5 LE
Deliverables | Wireless resonant charger with approximately 30W power transmission capability. Stretch Goal: a mobile device to demonstrate autonomous charging.
Telemetry | Report State to GUI Device
LCD display | Diagnostic Data Character String Display

Table 28: Final Design’s Transmitter Specifications

Operating Frequency | 13.56 MHz
RF Power Output | 30 W
Max. Charging Distance | 30 cm
DC Power supply | 48V 1.25A min.
Conversion Efficiency DC-AC | 80%
Telemetry | Report State to Receiver

Table 29: Final Design’s Communication Link Specifications

Communication Medium | Bluetooth 5 LE
Protocols | GUI: Host Controller Interface (HCI) Receiver- transmitter: Synchronous Connection-Oriented (SCO) link

Table 30: Final Design’s GUI Specifications

OS | WinOS, IOS, Linux, & Android
License | LGPL 3.0
Software Architecture | Model-Controller-View (MCV) Architecture
Delivery Model | Open Source Free App Download

VIII. PROJECT WORK PLAN FOR SENIOR DESIGN II

The Wireless Power Charger Project shall be completed with three major components with a supplementary component that could either be purchased off the shelf or designed explicitly for the project’s proof of concept. The components are listed in the work breakdown structure diagram (WBS) below with all deliverables. The WBS does not include subprocess breakdowns; for a greater breakdown, one may see Appendix C: Project Management Gantt Chart.


Figure 38: Basic Work Breakdown Structure Diagram – Deliverable-Based WBS

Table 31: Project Milestones

| Transmitter | Receiver | GUI | Robot
Planned and Designed | X | X | X | X
Coil Module Completed | X | X
Complete Enclosure | X | X
End User Documentation | X | X | X
Design Documentation | | | X
Wall AC-DC Converter Obtained | X
Firmware Implemented | X | X
Order Initial PCB | X | X
Test and Modify Initial PCB | X | X | X
Order Second/Final PCB | X | X
Compiled | | | X
Architecture Implemented | | | X
Initial Demo | X | X | X | X
Stress Test Completed | X | X | X | X
Complete PDD
Present for Senior Design

Clear due dates may be observed in Appendix D: The Spring Project Calendar which is broken up into five major sections that each concludes with some due date or deadline. The team shall utilize Winter Break to prep for the January PCB design. The initial PCB and all tasks leading up to it should be completed by the last week of January followed by a period focusing on the first PDD report until the PCB arrives. The next section focuses on experiments that will be used to elaborate the second PDD report slated for the first week of March as well as modify the design. The fourth section of time shall focus on PCB design modifications until the second and final PCB is ordered in late mid-March. Lastly, the project’s final period shall begin with the third PDD report at the start of April and end with the tandem presentation of a prototype alongside the final PDD report in the middle of April.

It is expected that with each PDD report submission or presentation, that there will be a formal design review that serves to report all tasks accomplished and referenced against the timelines provided. Additionally, these milestones and tasks shall be modified as is necessary.

All PCB designs shall be accomplished via the Altium Designer software’s student license. PCB Components not included in the PCB CAD software shall be created to fulfill requirements. The PCB construction shall be outsourced to Chinese companies due to budget constraints, and the team is allocating between ten and fifteen days for each shipment to arrive from the day of ordering.

The coils shall be created according to calculated specs above and validated via a vector network analyzer (VNA) provided by our sponsor company, Indus Instruments.

The software and firmware methods will be developed prior to ordering the initial PCB. The software GUI visual mock-up shall be completed prior to the building of the initial PCB while awaiting the PCB’s arrival. The software and firmware methods must be tested during the initial evaluation of the initial PCB and demo. The software must be compiled in all intended operating systems for exhaustive testing to be accomplished prior to the submission of the second PDD report. Software and firmware must undergo stress testing alongside all hardware components prior to the ordering of the final PCB. Cellular demos shall be recorded via an external camera while PC demos shall be recorded via third party, onboard video software.

Any and all additional, script documentation is considered a stretch goal in addition to developing a proof of concept robot.

IX. RESOURCES REQUIRED

All test equipment and programming tools needed for this project are available at Indus Instruments. The software required for simulation and testing is available through our school or we will have access to it at Indus Instruments.

The prototype PCB build depends on an external company which means that there is little control over their schedule. This makes it even more important to pay attention to the schedule and place PCB fabrication orders in a timely manner. Also, it is necessary to do a PCB design review before the order is placed. Because time is limited and the whole project must be finished during the spring semester it is crucial to minimize the number of PCB design iterations.

In the event that our PCB supplier is unable to complete our boards on time, we have alternative local fabricators available that will be able to meet our needs at the cost of higher prototyping expenses.

1.) Simulation Tools

1) MSP-EXP430FR5994
a) Microcontroller Development Board
b) Code Composer Studio
2) DC2038A
a) LTC4162-L Development Board
b) LTC4162 GUI
3) RN4870
a) Bluetooth Development Board
4) Wireless Power Transmission Circuits
a) Multisim
b) Laboratory work with test circuits
5) Power Conversion Stages
a) TI WEBBench and Power Stage Designer
b) Multisim

2.) Necessary Tools and Equipment

1) Laboratory Equipment
a) DC Power Supplies
b) Simulated Load
c) Li-Ion Battery Packs
d) Oscilloscope
e) a) Vector Network Analyzer (VNA)
f) Spectrum Analyzer
g) Digital Multimeter
2) Prototyping and Fabrication Resources
a) Altium Designer
b) Soldering and Reflow Tools
c) PCB Fabrication Service

X. CONCLUSION

Our proposed project is the design and prototype of a wireless resonant charger. This charger will consist of a transmitter and receiver, and will deliver approximately 30 watts to a Li-Ion battery charge controller integrated into the receiver. The transmitter will be powered by a regionally approved mains adapter.

The transmitter and receiver will be computer-controlled and will communicate with each other and to a GUI interface over Bluetooth LE.

The team has developed a timeframe for the necessary steps to complete the design and prototype. Those steps include finalizing charger subsystems design, creating necessary manufacturing documentation, testing prototypes and repeating the process until the prototype is working as specified. If the team meets its design goals ahead of schedule it will attempt to develop a mobile device to demonstrate the wireless charger’s potential as part of an autonomous charging system.

XI. REFERENCES

SOFTWARE REFERENCES

Block diagrams were rendered in Windows Visio Standard 2019. Multisim circuits simulated in NI Multisim V.14.2 2019.

REGULATORY REFERENCES

[1] “21 CFR §1000.15 - Examples of electronic products subject to Radiation Control for Health and Safety Act of 1968”. In: Electronic Code of Federal Regulations Title 21 (2020). url: https://www.law.cornell.edu/cfr/text/21/1000.15.
[3] “A Summary of Worldwide Telecommunications Regulations Governing the Use of Ultra-Wideband Radio Version 1.2”. In: Decawave Application Note: APR001 (2015), pp. 1–63.
[12] “IEEE Standard for Information Technology. Local and Metropolitan Area Networks. Specific Requirements”. In: IEEE Std 802.15.1-2005 (2005), pp. 1–312.
[13] “IEEE Standard for Rechargeable Batteries for Multi-Cell Mobile Computing Devices”. In: IEEE Std 1625-2008 (Revision of IEEE Std 1625-2004) (2008), pp. 1–0. doi: 10.1109/IEEESTD.2008.4657368. (https://doi.org/10.1109/IEEESTD.2008.4657368)
[14] “IEEE Standard for Safety Levels with Respect to Human Exposure to Electric, Magnetic, and Electromagnetic Fields, 0 Hz to 300 GHz”. In: IEEE Std C95.1-2019 (Revision of IEEE Std C95.1-2005/ Incorporates IEEE Std C95.1-2019/Cor 1-2019) (2019), pp. 1–312.
[16] “Industrial, Scientific, and Medical Equipment”. In: FCC Std 18 (2020).
[17] “Industrial, Scientific and Medical Equipment. Radio-Frequency Disturbance Characteristics. Limits and Methods of Measurement”. In: BS EN 55011:2016+A1:2017 (2017), pp. 1–98.
[25] “Radio Frequency Devices”. In: FCC Std 15 (2020).
[27] “RF Exposure Considerations for Low Power Consumer Wireless Power Transfer Applications”. In: FCC Office of Engineering and Technology Laboratory Division (2018), pp. 1–4.

DESIGN REFERENCES

[2] “80SQ045N Axial Lead Rectifier”. In: Semiconductor Components Industries LLC. Public Datasheet (2000), pp. 1–5. url: https://www.onsemi.com/pub/Collateral/80SQ045N-D.PDF. (https://www.onsemi.com/pub/Collateral/80SQ045N-D.PDF)
[4] “AST3TQ-28”. In: Abracon LLC. Precision SMD TCXO/VCTCXO (2019), pp. 1–
6. url: https://abracon.com/Oscillators/AST3TQ-28.pdf.
[5] Gunbok Lee Benjamin Waters Brody Mahoney and Joshua R. Smith. “Optimal Coil Size Ratios for Wireless Power Transfer Applications”. In: ISCAS (2014), pp. 1–4.
url: https://sensor.cs.washington.edu/pubs/ML/power/optimal\_coil_ratio.pdf. (https://sensor.cs.washington.edu/pubs/ML/power/optimal\_coil_ratio.pdf)
[6] G. Choi. “13.56 MHz, CLASS-E, 1KW RF Generator using a Microsemi DRF1200 Driver/ MOSFET Hybrid”. In: Microsemi (2013).
[7] “Coils Used for Wireless Charging”. In: Freescale Semiconductor, Inc. AN4866 Rev. 0, 01/2014 (2014).
[8] Conductor Bulk Resistivity & Skin Depths. RF Cafe. url: https://www.rfcafe.com/references/electrical/cond-high-freq.htm. (https://www.rfcafe.com/references/electrical/cond-high-freq.htm)
[9] “DEMO MANUAL DC2038A”. In: Analog Devices, Inc. Evaluation Kit Manuals (2019), pp. 1–14. url: analog.com/media/en/dsp-documentation/evaluationkit-manuals/DC2038A.pdf.
[10] “eGaN® FET DATASHEET”. In: Efficient Power Conversion Corporation (EPC) Patents (2019), pp. 1–6. url: https : / / epc - co . com / epc / Portals / 0 / epc / documents/datasheets/EPC2019\_datasheet.pdf. (https://epc-co.com/epc/Portals/0/epc/documents/datasheets/EPC2019\_datasheet.pdf)
[11] T. Gerrits. “Third harmonic filtered 13.56 MHz Push-Pull Class-E Power Amplifier”. In: Energy Conversion Congress and Exposition (ECCE), 2010 IEEE (2008).
[15] “INA19x”. In: Texas Instruments Inc. SBOS307G12D - MAY 2004 - REVISED JANUARY 2015 (2015), pp. 1–33. url: https://www.ti.com/lit/ds/symlink/ina197 . pdf ? ts = 1603583914042 \ &ref _ url = https \ %253A \ %252F \ %252Fwww . ti.com\%252Fproduct\%252FINA197\%253Fdcmp\%253Ddsproject\%2526hqs\ %253Dpf.. (https://www.ti.com/lit/ds/symlink/ina197.pdf?ts=1603583914042\)
[19] “LMG1210”. In: Texas Instruments Inc. SNOSD12D - NOVEMBER 2018 - RE-VISED JANUARY 2019 (2019), pp. 1–6. url: https://www.ti.com/lit/ds/symlink / lmg1210 . pdf ? HQS = TI - null - null - mousermode - df - pf - null - wwe \ &DCM=yes\&ref\_url=https\%3A\%2F\%2Fwww.mouser.com\%2F\&distId=26. (https://www.ti.com/lit/ds/symlink/lmg1210.pdf?HQS=TI-null-null-mousermode-df-pf-null-wwe\&DCM=yes\&ref\_url=https\%3A\%2F\%2Fwww.mouser.com\%2F\&distId=26)
[20] “LTC4162-L 35V/3.2A Multicell Lithium-Ion Step-Down Battery Charger with PowerPath and I² Telemetry”. In: Analog Devices, Inc (2018), pp. 1–52. url:
https : / / www . analog . com / media / en / technical - documentation / data -sheets/LTC4162-L.pdf. (https://www.analog.com/media/en/technical-documentation/data-sheets/LTC4162-L.pdf)

[22] “MSP430FR599x, MSP430FR596x Mixed-Signal Microcontrollers”. In: Texas Instruments Inc. SLASE54C - MARCH 2016 - REVISED AUGUST 2018 (2018), pp. 1–172. url: https : / / www . ti . com / lit / ds / symlink / msp430fr5994 . pdf?ts=1604041478538\&ref\_url=https\%253A\%252F\%252Fwww.ti.com\ %252Fproduct\%252FMSP430FR5994. (https://www.ti.com/lit/ds/symlink/msp430fr5994.pdf?ts=1604041478538\)
[23] D. A. Neamen. Microelectronics: Circuit Analysis and Design. Mc Graw Hill, 2010, pp. 75–81.
[24] Qt Documentation :: Qt 5.15 :: Qt Bluetooth. Qt Company Ltd. url: https : //doc.qt.io/qt-5/qtbluetooth-index.html (visited on 10/08/2020).
[26] Y. Rahayu et al. “Ultra wideband technology and its applications”. In: 2008 5th IFIP International Conference on Wireless and Optical Communications Networks (WOCN ’08). 2008, pp. 1–5. doi: 10.1109/WOCN.2008.4542537. (https://doi.org/10.1109/WOCN.2008.4542537)
[28] Skin Depth (aka Skin Effect) as a Function of Frequency, Permeability, & Conductivity. RF Cafe. url: https://www.rfcafe.com/references/electrical/skindepth.htm. (https://www.rfcafe.com/references/electrical/skin-depth.htm)
[29] N. O. Sokal. “Class-E RF Power Amplifiers”. In: QEX (2001), pp. 9–20.
[30] Battery Charger Design Manager Steven Martin. “Reverse Voltage Protection for Battery Chargers”. In: Analog Devices, Inc. Application Note 171 (2018), pp. 1–
6. url: https : / / www . analog . com / media / en / technical - documentation / application-notes/AN-171\_AN-1568.pdf. (https://www.analog.com/media/en/technical-documentation/application-notes/AN-171\_AN-1568.pdf)
[32] Texas Instruments MSP430FR5994 Tool Description. url: https://www.ti.com/tool/MSP-EXP430FR5994. (https://www.ti.com/tool/MSP-EXP430FR5994)
[33] “The Quest for Power Density”. In: Semiconductor Components Industries, LLC TND6239/D Rev.1, JUNE - 2019 (2019).
[34] “TPS54160 1.5-A, 60-V, Step-Down DC/DC Converter with Eco-mode”. In: Texas Instruments Inc. SLVSB56C - MAY 2012 - REVISED FEBRUARY 2014 (2014), pp. 1–58. url: https://www.ti.com/lit/ds/symlink/tps54160.pdf.
[35] “TPSM265R1 65-V Input, 100-mA Power Module with Ultra-Low IQ”. In: Texas Instruments Inc. SNVSBF6A - OCTOBER 2019 - REVISED DECEMBER 2019 (2019), pp. 1–32. url: https : / / www . ti . com / lit / ds / symlink / tpsm265r1 . pdf?ts=1606735419804&ref_url=https\%253A\%252F\%252Fduckduckgo.com\ %252F. (https://www.ti.com/lit/ds/symlink/tpsm265r1.pdf?ts=1606735419804)
[36] Meiling Qu Xinshi Shi Chang Qi and Shuangli Ye. “Effects of Coil Shapes on Wireless Power Transfer Via Magnetic Resonance Coupling”. In: Journal of Electromagnetic Waves and Applications 28 (11) (2014).

CATELOGS FOR PARTS INVESTIGATED

[21] McMaster-Carr Standard Metal Tubing Catelog. url: https://www.mcmaster.com/standard-metal-tubing/. (https://www.mcmaster.com/standard-metal-tubing/)

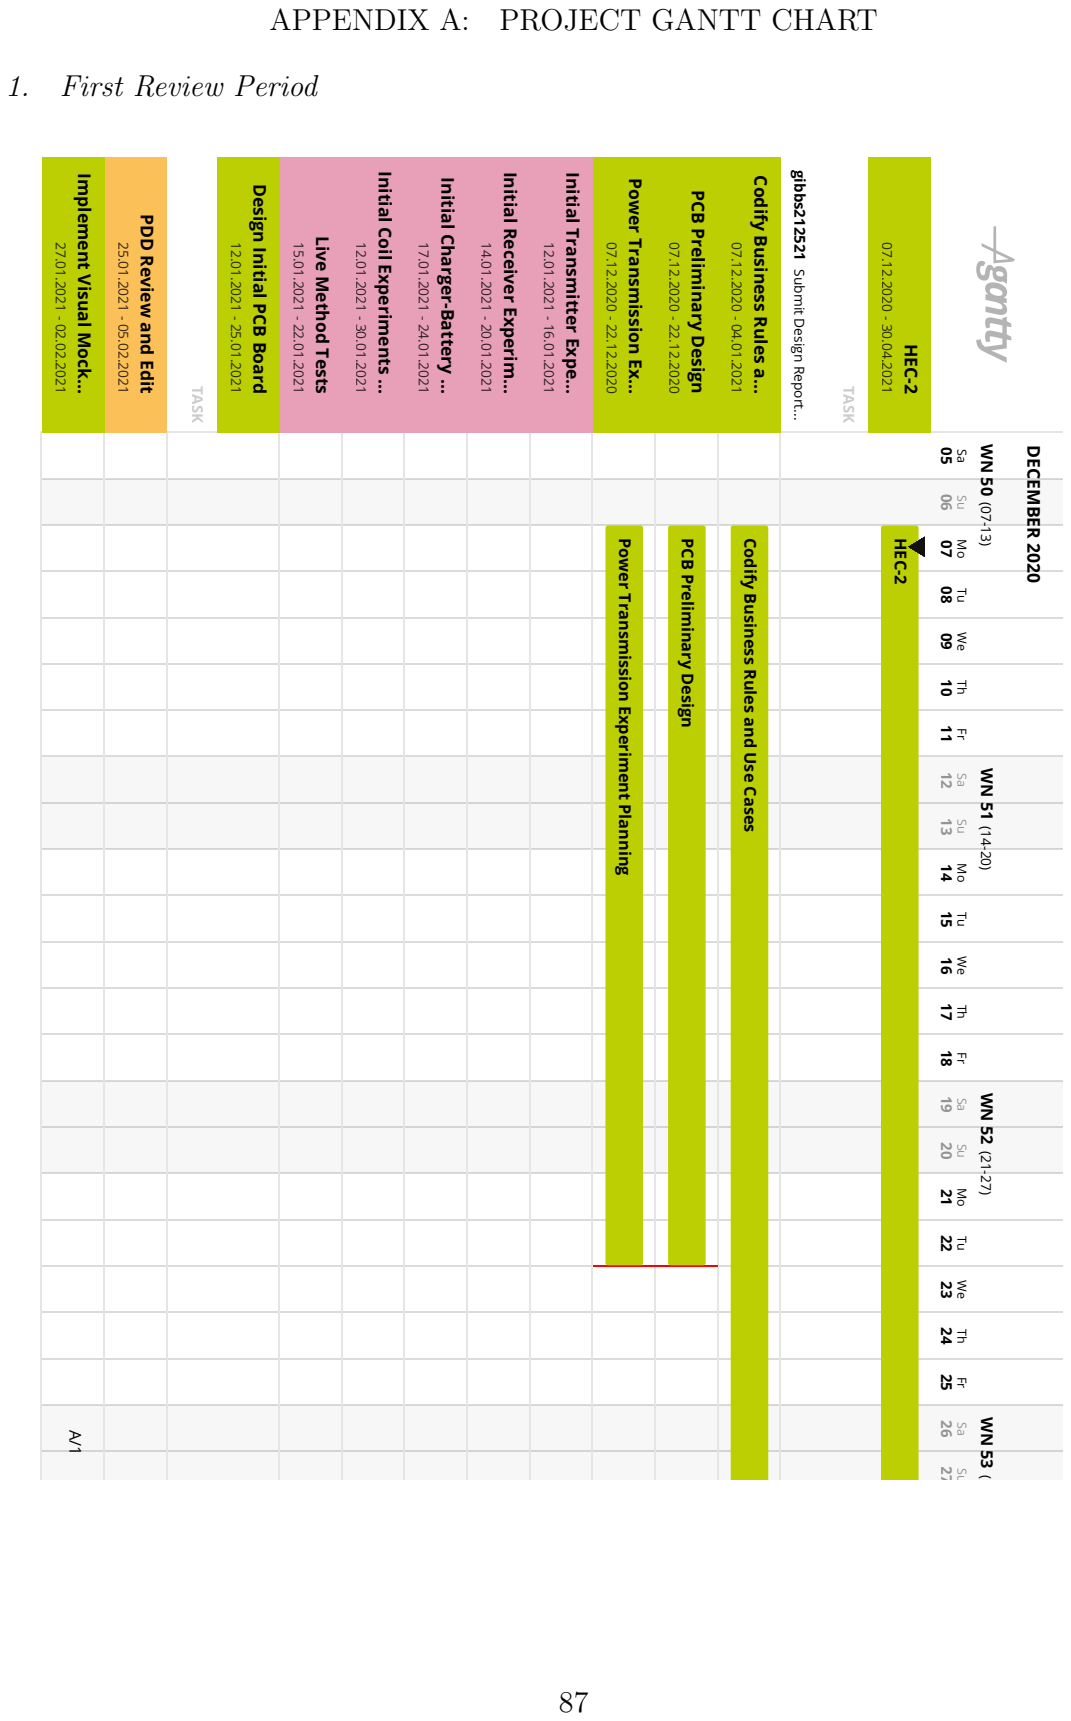
[picture p83: page 93]
gibbs212521; HEC-2; DECEMBER 2020

APPENDIX A: PROJECT GANTT CHART

1. First Review Period

Submit Design Report... 07.12.2020 - 30.04.2021TASK Codify Business Rules a... 07.12.2020 - 04.01.2021 PCB Preliminary Design 07.12.2020 - 22.12.2020 Power Transmission Ex... 07.12.2020 - 22.12.2020 Initial Transmitter Expe... 12.01.2021 - 16.01.2021 Initial Receiver Experim... 14.01.2021 - 20.01.2021 Initial Charger-Battery ... 17.01.2021 - 24.01.2021 Initial Coil Experiments ... 12.01.2021 - 30.01.2021 Live Method Tests 15.01.2021 - 22.01.2021 Design Initial PCB Board 12.01.2021 - 25.01.2021TASK PDD Review and Edit 25.01.2021 - 05.02.2021 Implement Visual Mock... 27.01.2021 - 02.02.2021 Power Transmission Experiment Planning PCB Preliminary Design Codify Business Rules and Use Cases

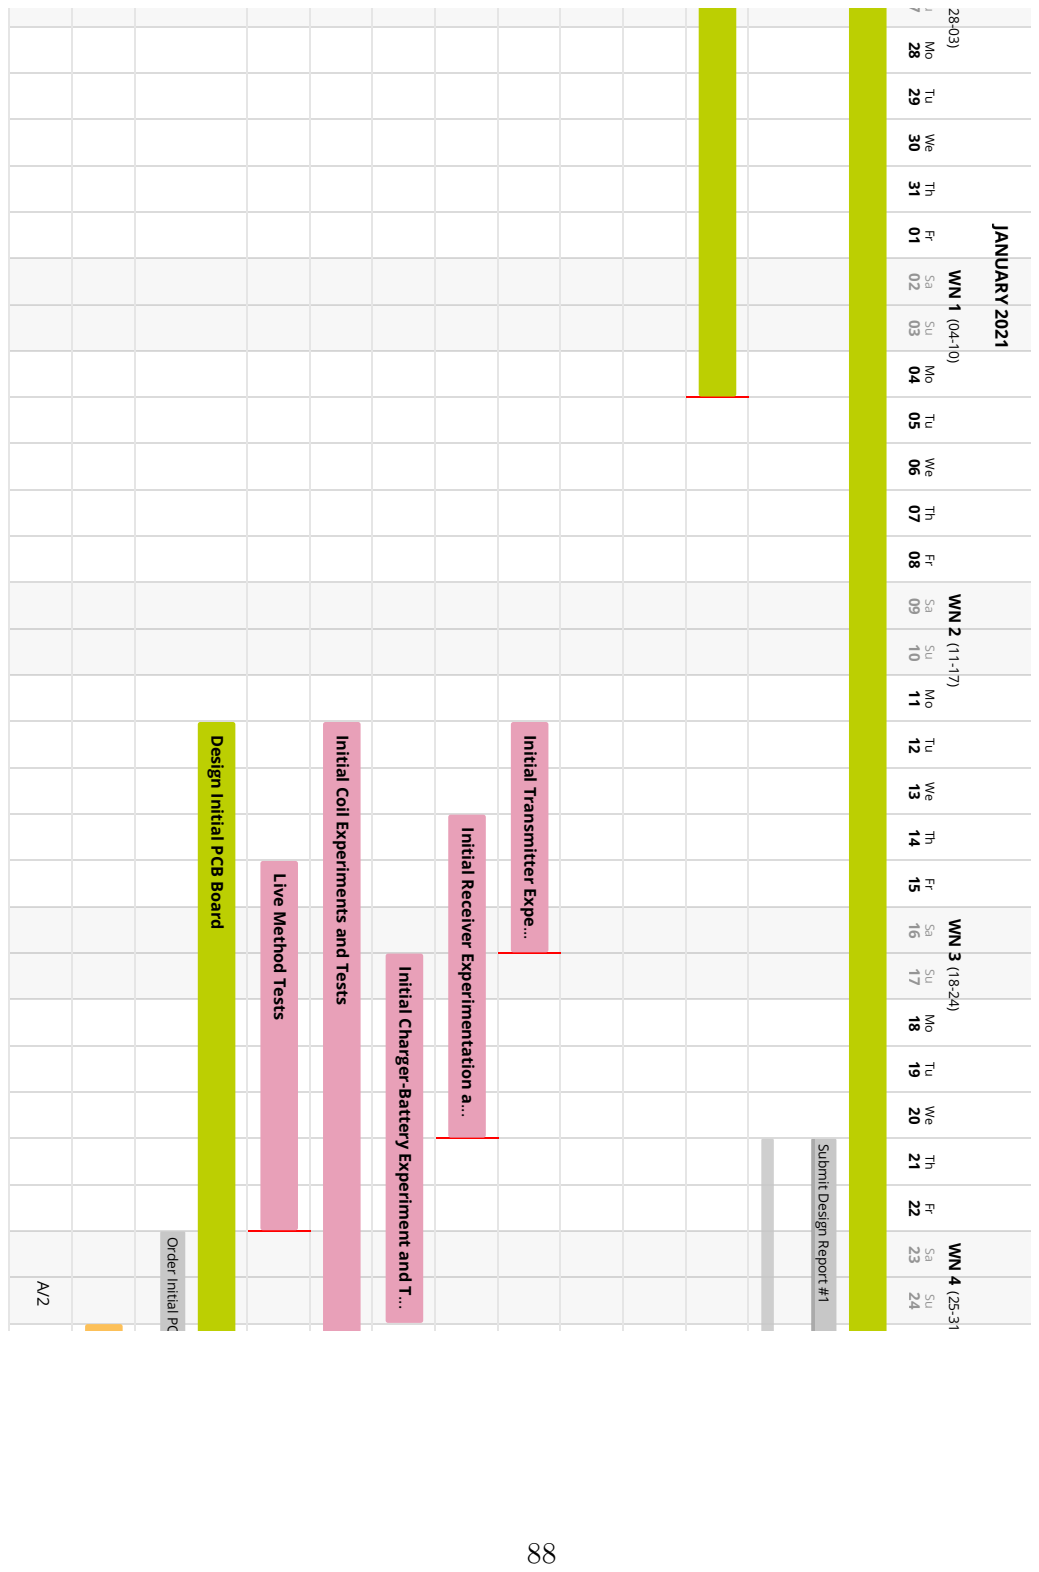
[picture p84: page 94]
JANUARY 2021

Design Initial PCB Board

Initial Coil Experiments and Tests

Submit Design Report #1 ... Initial Transmitter Expe ... Initial Receiver Experimentation a ... Initial Charger-Battery Experiment and T

Live Method Tests

Order Initial PC

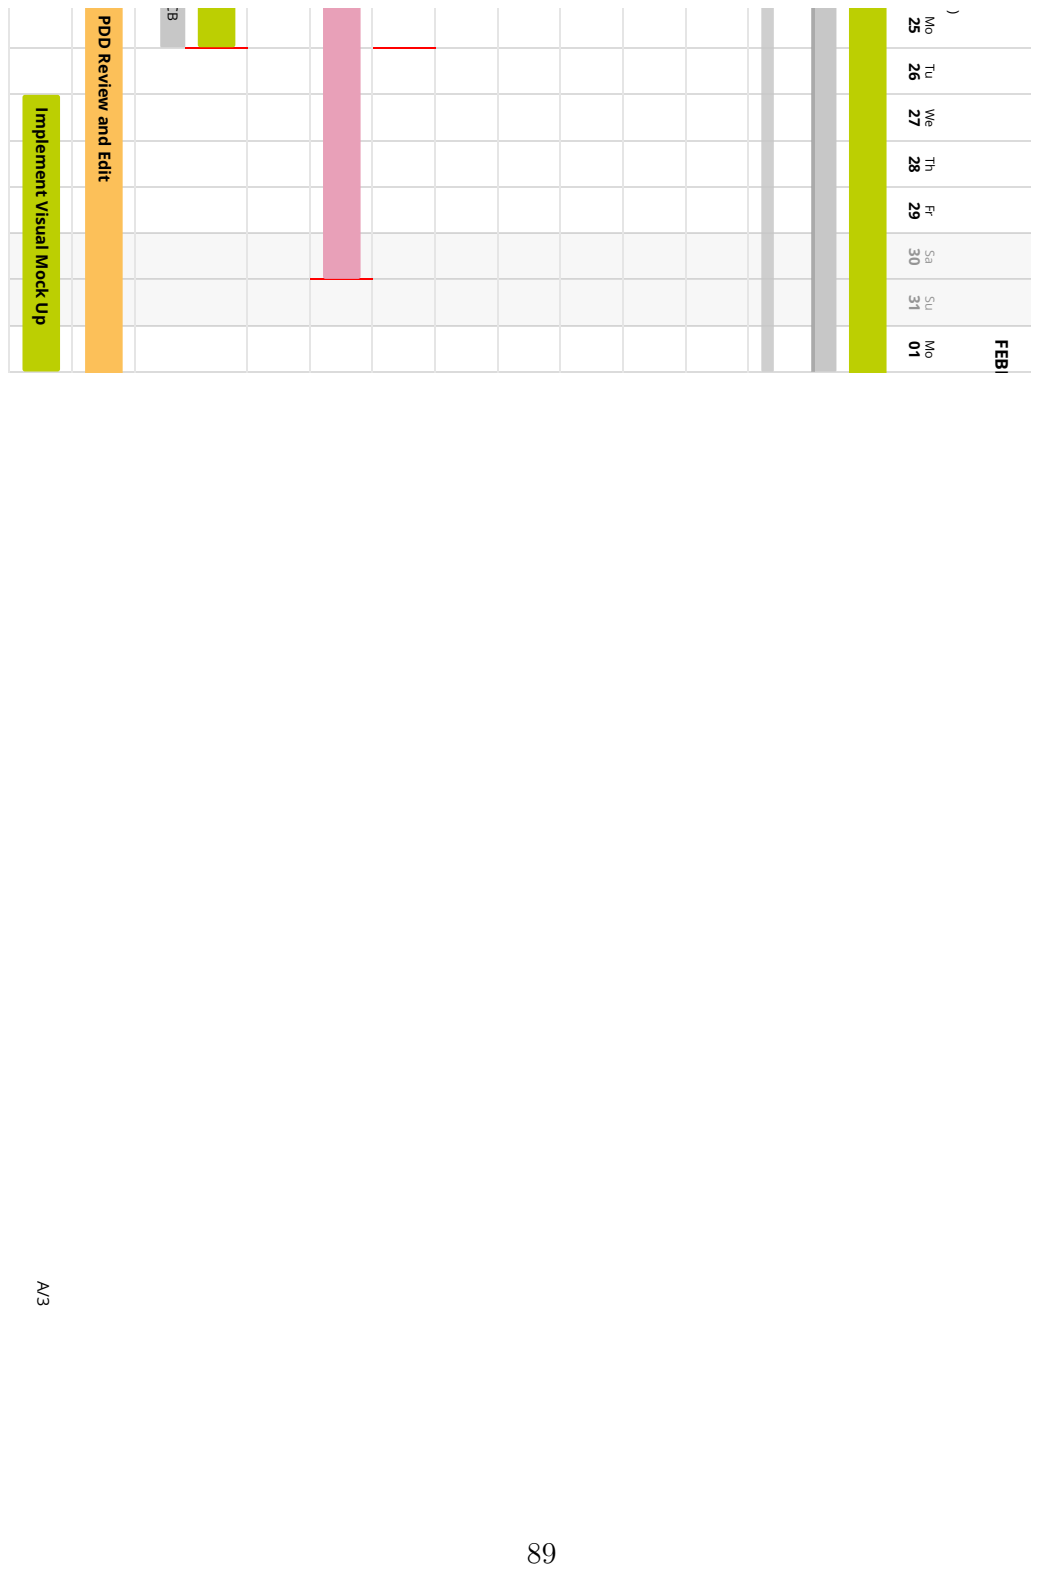
[picture p85: page 95]
FEBR

PDD Review and Edit

Implement Visual Mock Up

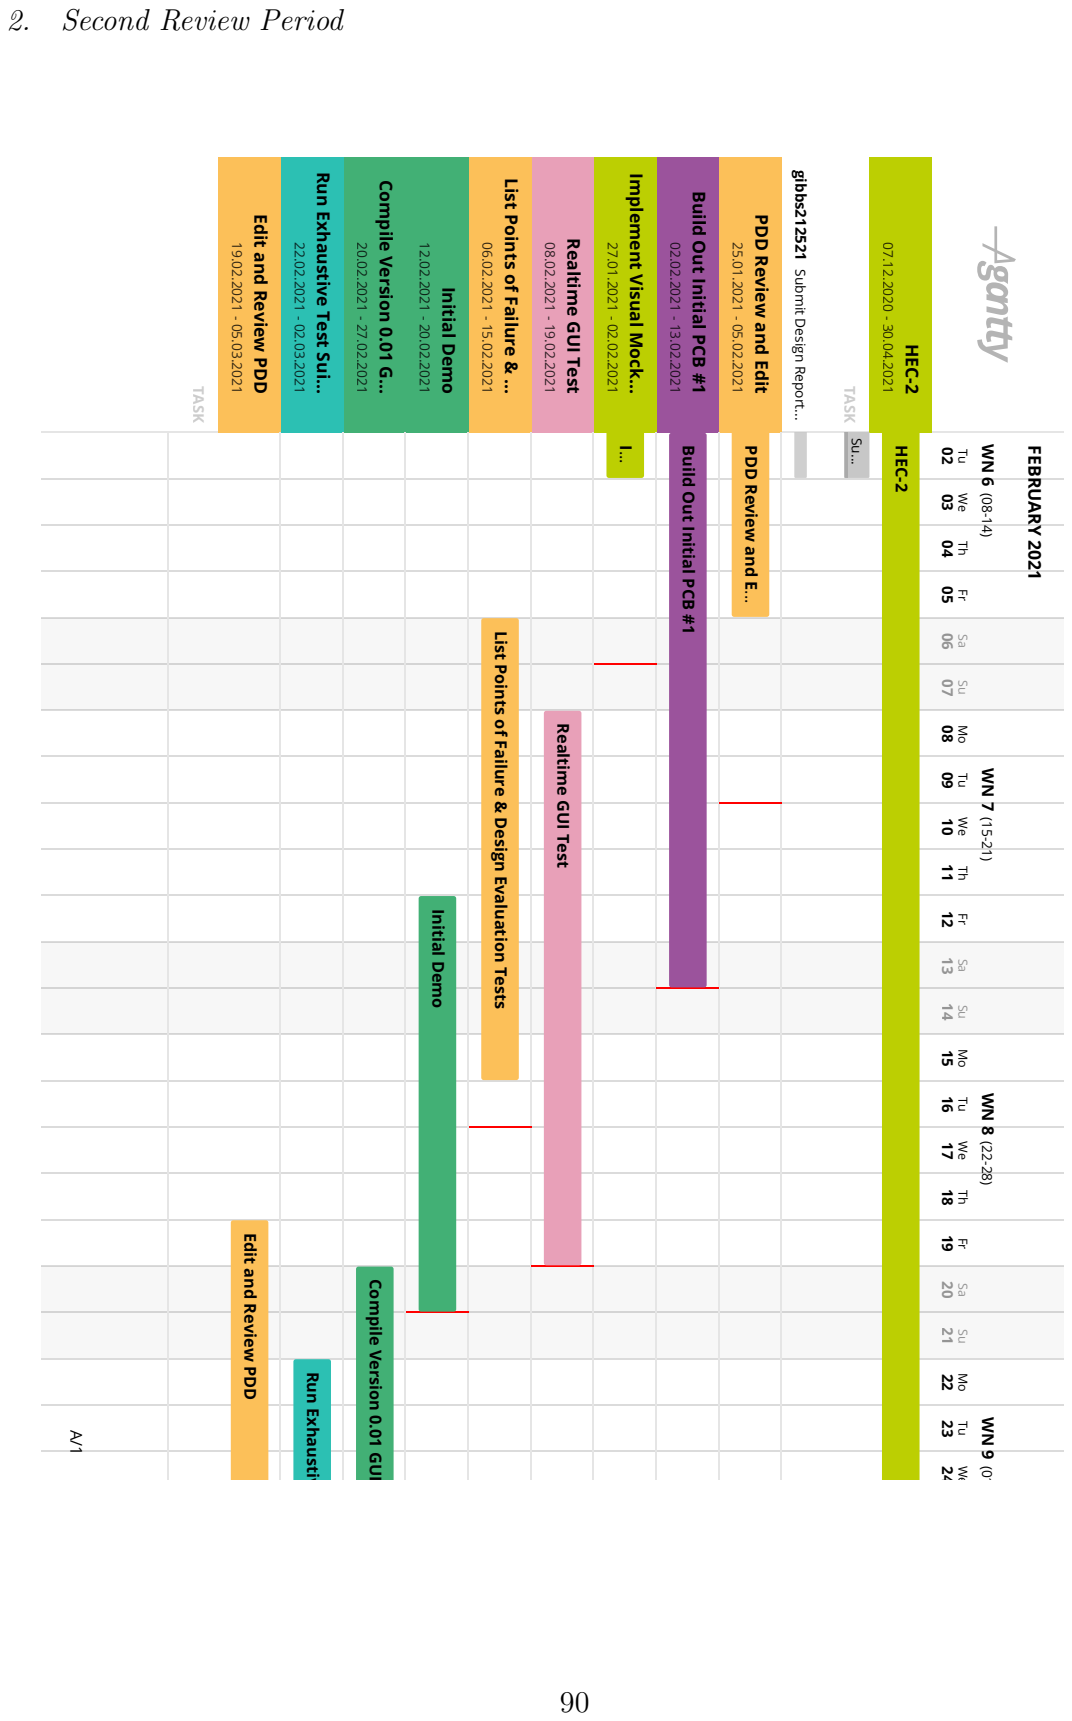
[picture p86: page 96]
gibbs212521; HEC-2; Initial Demo; Run Exhaustiv; FEBRUARY 2021

2. Second Review Period

Submit Design Report... 07.12.2020 - 30.04.2021TASK PDD Review and Edit 25.01.2021 - 05.02.2021 Build Out Initial PCB #1 02.02.2021 - 13.02.2021 Implement Visual Mock... 08.02.2021 - 19.02.2021 Realtime GUI Test 27.01.2021 - 02.02.2021 List Points of Failure & ... 06.02.2021 - 15.02.2021 Initial Demo 12.02.2021 - 20.02.2021 Compile Version 0.01 G... 20.02.2021 - 27.02.2021 Run Exhaustive Test Sui... 22.02.2021 - 02.03.2021 Edit and Review PDD 19.02.2021 - 05.03.2021TASK

Su... ... Build Out Initial PCB #1 PDD Review and E ... I

List Points of Failure & Design Evaluation Tests

Realtime GUI Test

Edit and Review PDD

Compile Version 0.01 GUI

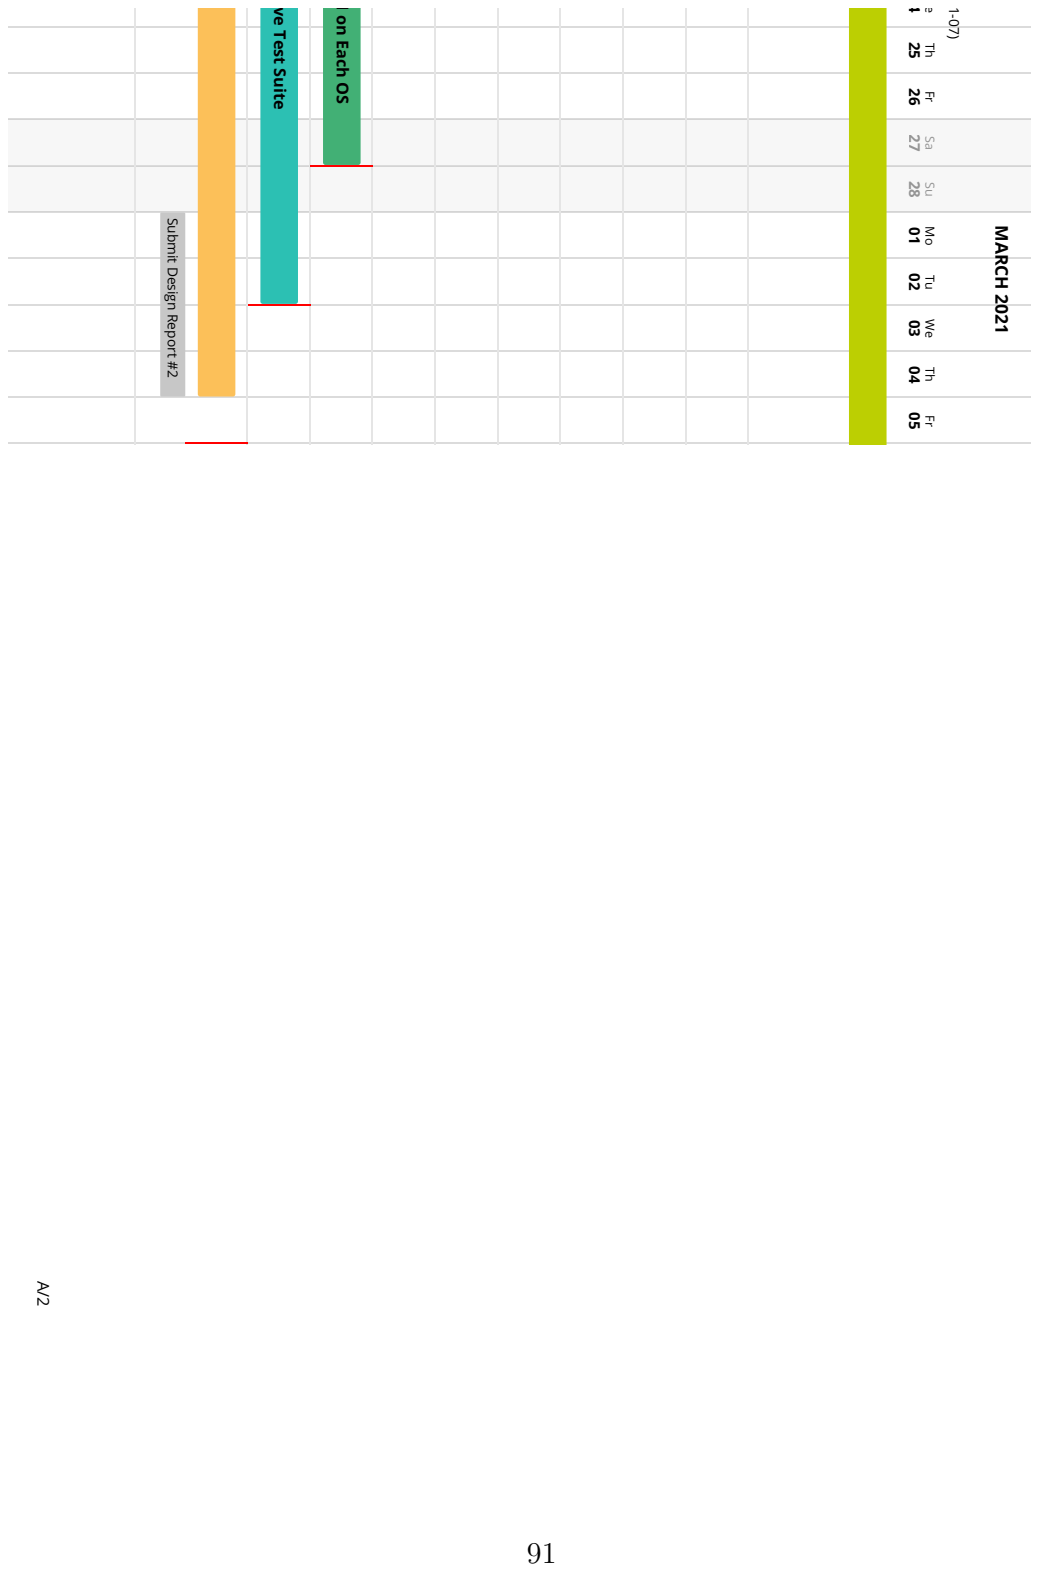
[picture p87: page 97]
MARCH 2021

ve Test Suite

I on Each OS

Submit Design Report #2

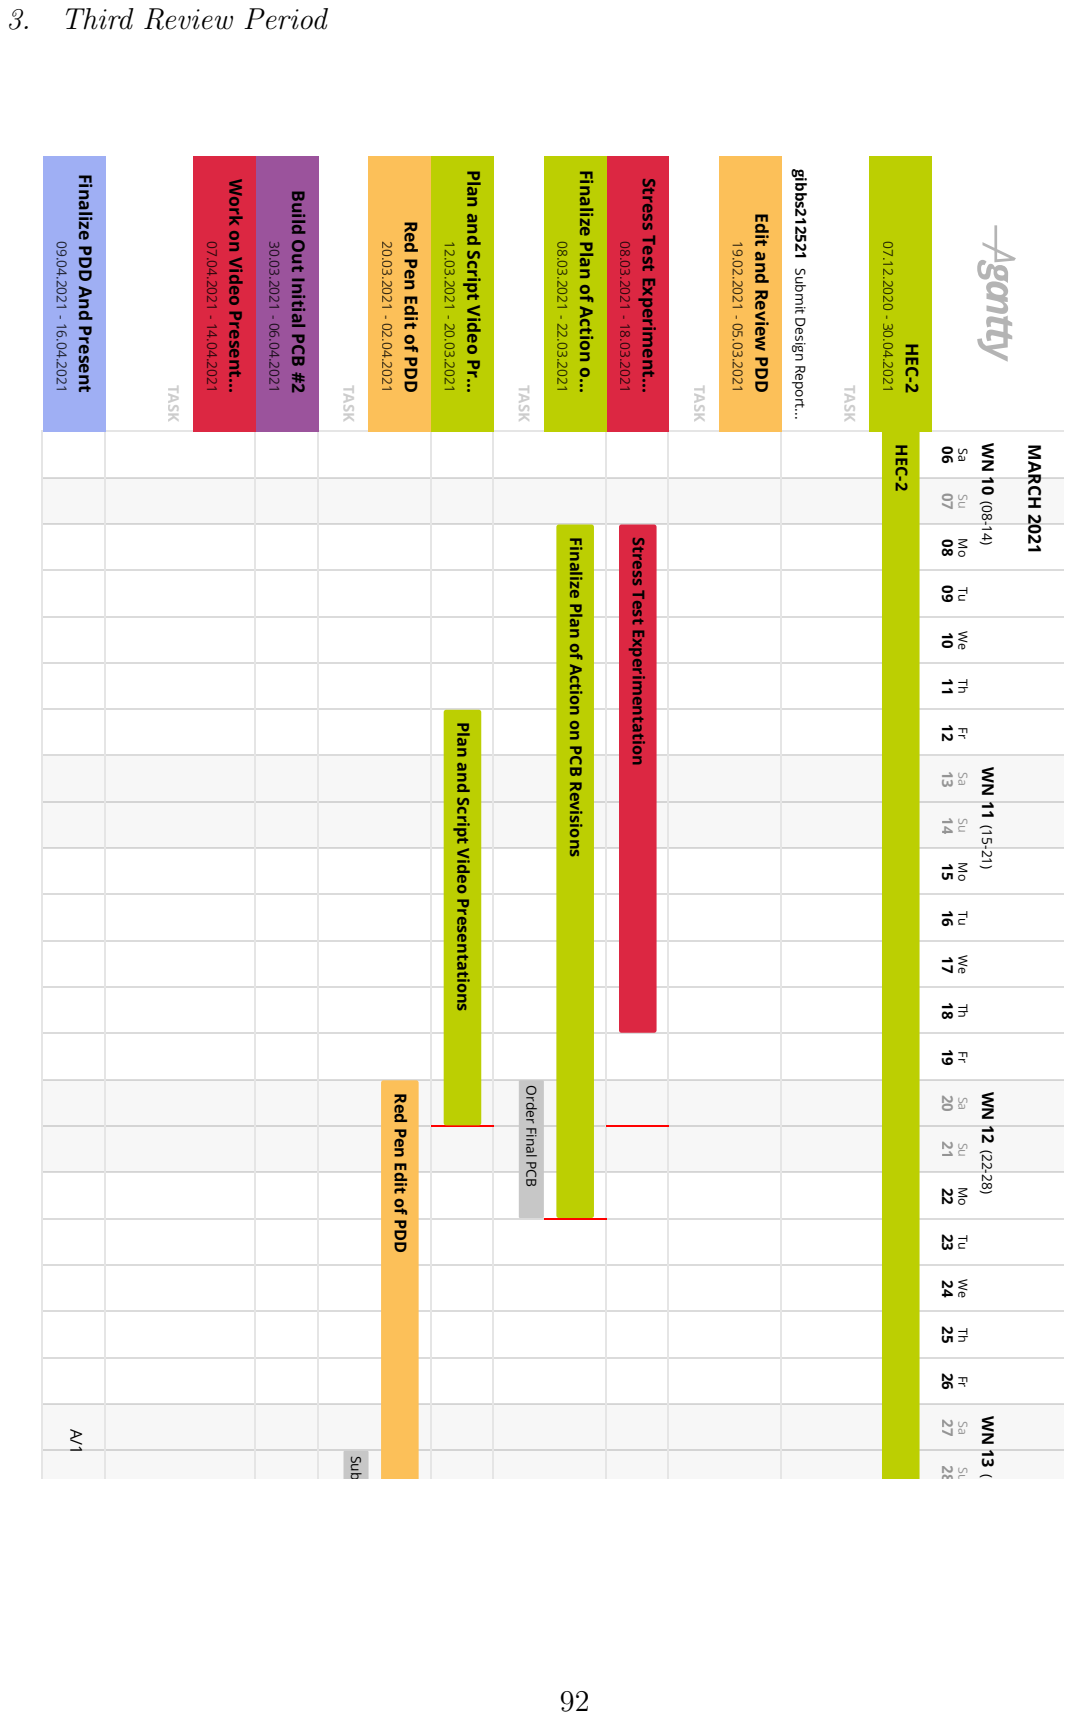
[picture p88: page 98]
gibbs212521; HEC-2; Sub; MARCH 2021

3. Third Review Period

Submit Design Report... 07.12.2020 - 30.04.2021TASK Edit and Review PDD 19.02.2021 - 05.03.2021TASK Stress Test Experiment... 08.03.2021 - 18.03.2021 Finalize Plan of Action o... 08.03.2021 - 22.03.2021TASK Plan and Script Video Pr... 12.03.2021 - 20.03.2021 Red Pen Edit of PDD 20.03.2021 - 02.04.2021TASK Build Out Initial PCB #2 30.03.2021 - 06.04.2021 Work on Video Present... 07.04.2021 - 14.04.2021TASK Finalize PDD And Present 09.04.2021 - 16.04.2021

Finalize Plan of Action on PCB Revisions

Stress Test Experimentation

Plan and Script Video Presentations

Red Pen Edit of PDD

Order Final PCB

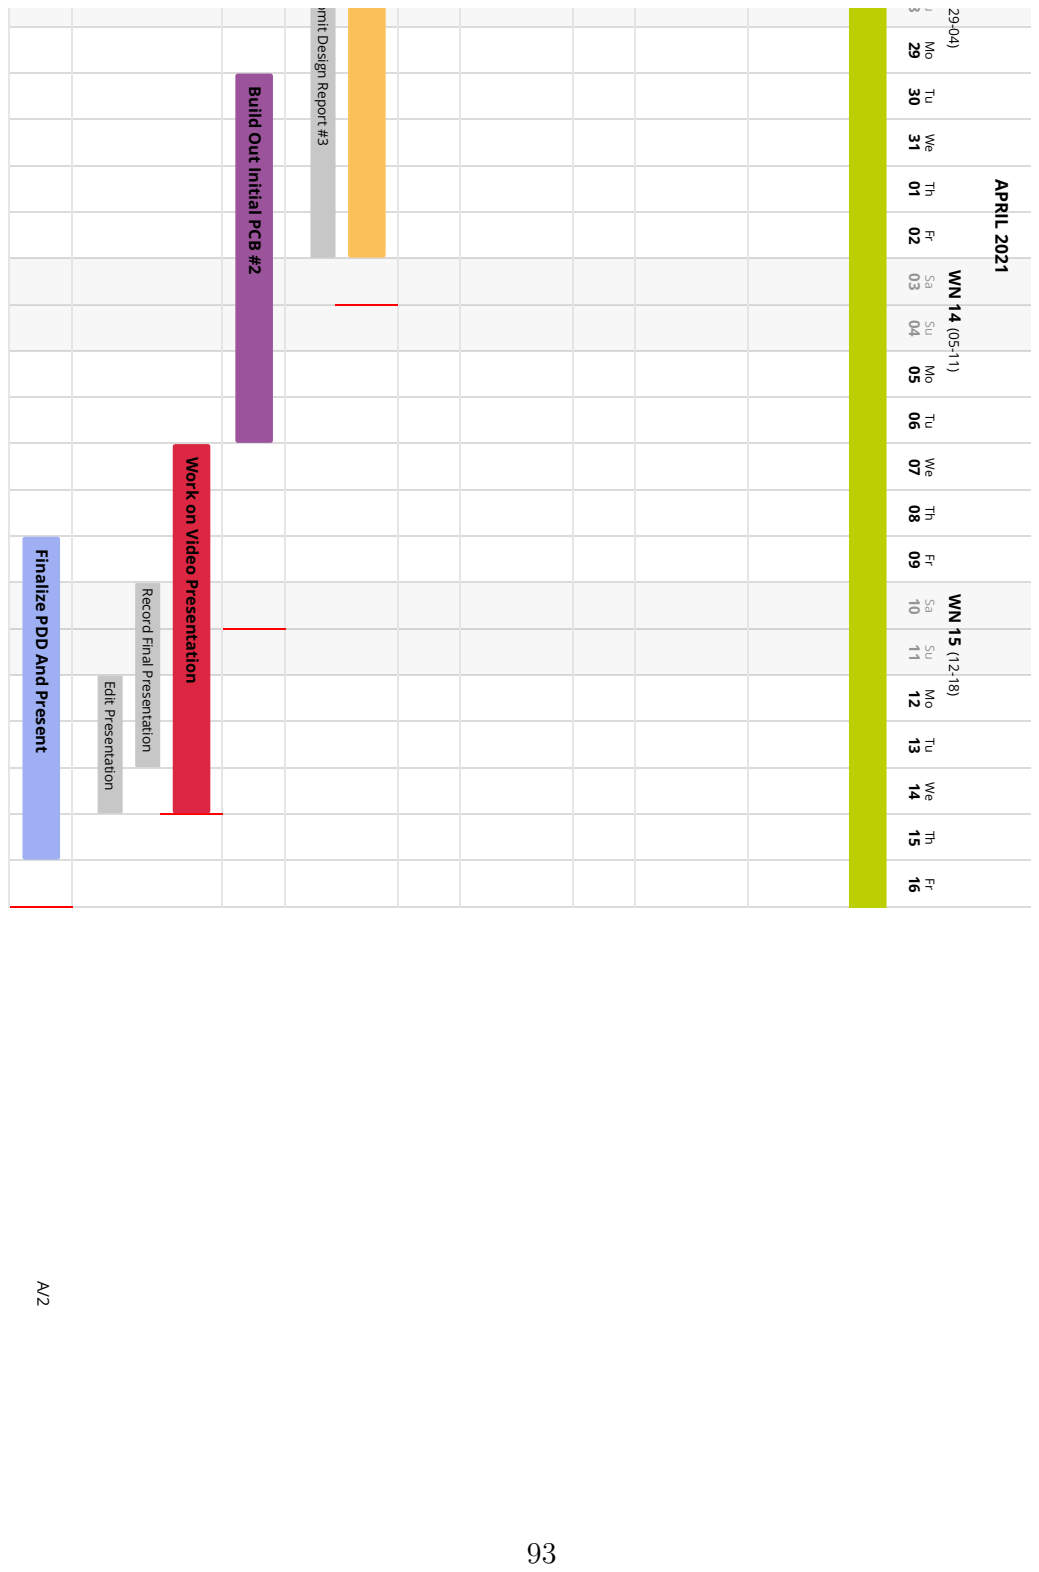
[picture p89: page 99]
Edit Presentation; APRIL 2021

bmit Design Report #3

Build Out Initial PCB #2

Work on Video Presentation

Finalize PDD And Present

Record Final Presentation

APPENDIX B: COURSEWORK RELATED KNOWLEDGE AND SKILLS

Table 32: Coursework Related Knowledge and Skills Table

Courses | Knowledge / Skills
EENG 3106 - Circuit Analysis I Lab | Laboratory Technique
EENG 3305 - Linear Circuits Analysis II | Circuit Analysis (RLC Circuits)
EENG 4109 - Electronic Circuit Analysis II Lab | Laboratory Technique
EENG 4309 - Electronic Circuit Analysis II | Amplifier Design Electronic circuit-analysis (amplifiers and rectifier circuits)
EENG 3303 - Electromagnetic Fields | Electromagnetic Theory Inductor parameters (inductance and resis-tance calculations based on shape and wire cross-section area and length.
EENG 3302 - Digital Systems | Digital Troubleshooting
EENG 3307 - Microprocessors | Microcontroller Programming
EENG 4350 - Advanced Microprocessors | Microcontroller Programming
