gibbs212521/HEC_2_senior_design/docs/Preliminary/BTLTE.png

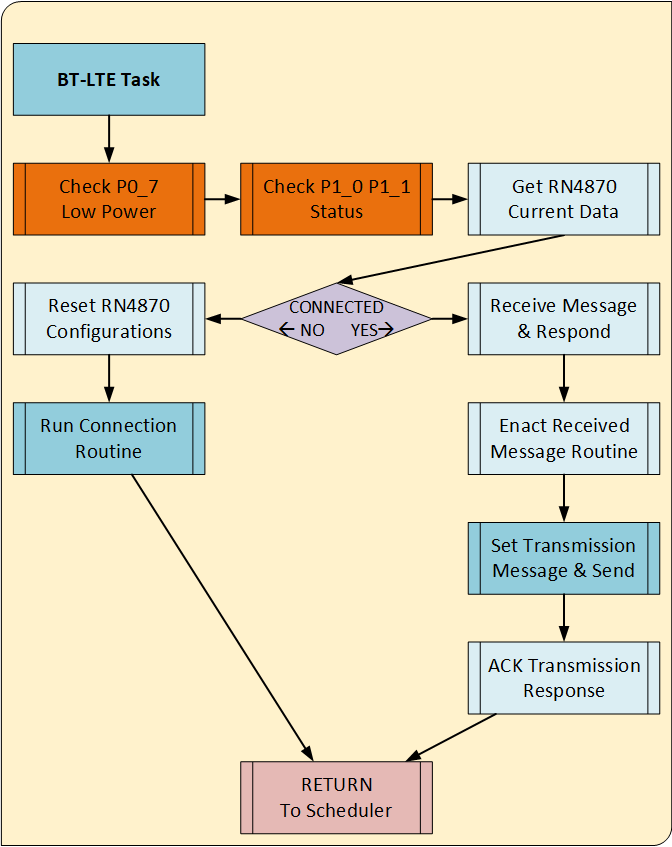
docs/Preliminary/BTLTE.png
