gibbs212521/HEC_2_senior_design/docs/Preliminary/MCU_init.png

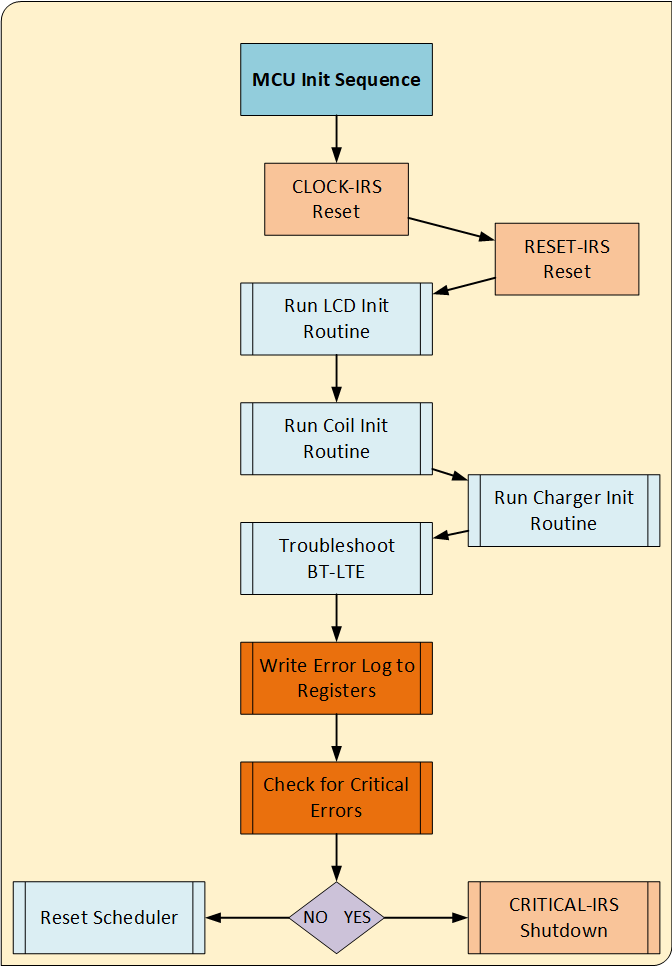
docs/Preliminary/MCU_init.png
