gibbs212521/HEC_2_senior_design/docs/Preliminary/software_naming_convention.png

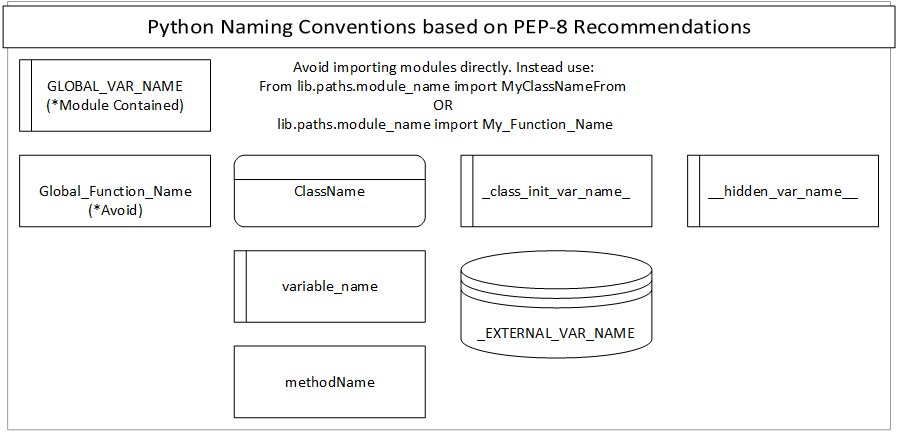
docs/Preliminary/software_naming_convention.png
