gibbs212521/HEC_2_senior_design/docs/Software/C_object_example.png

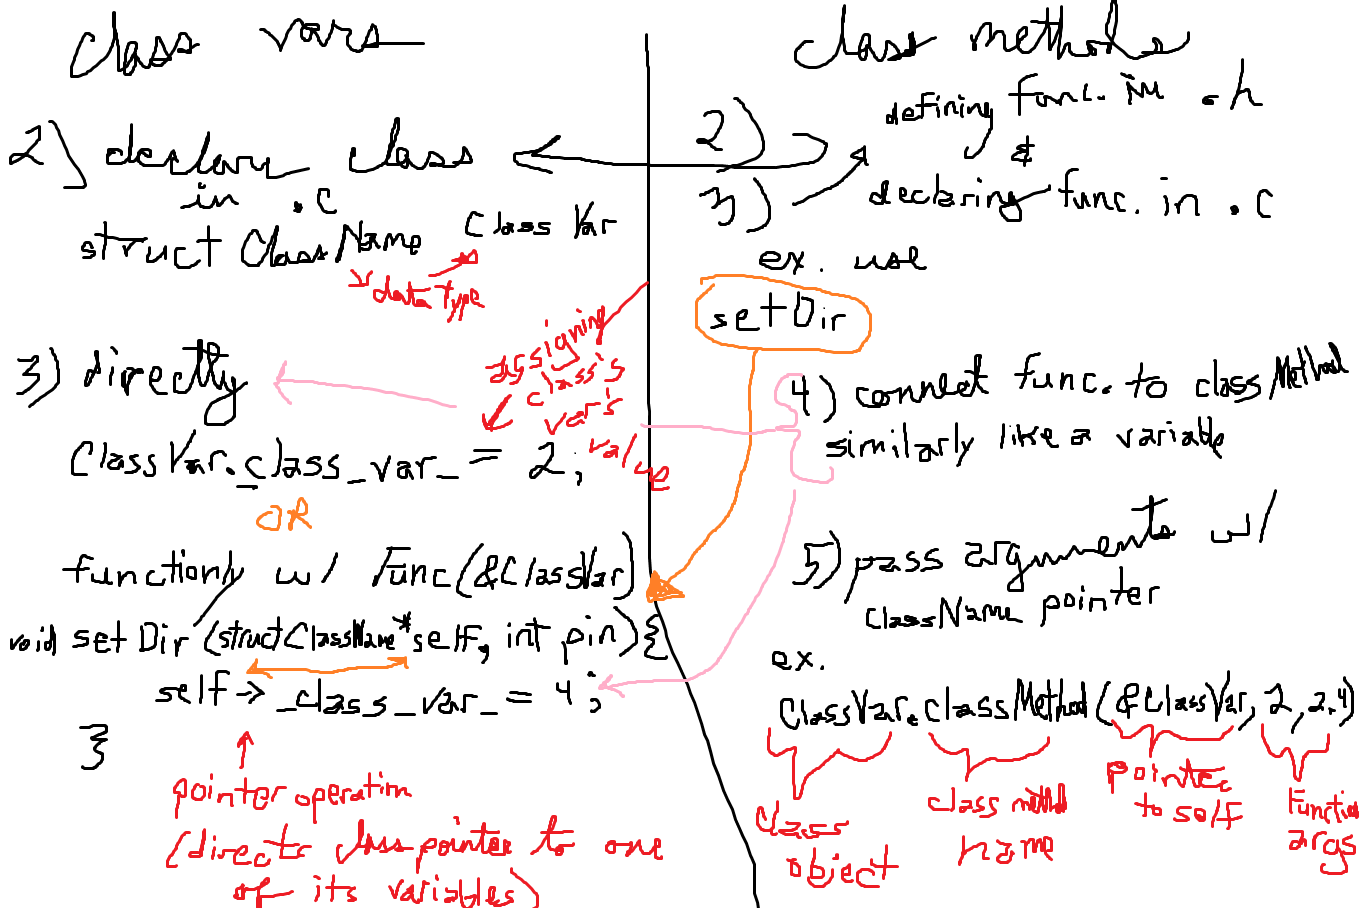
docs/Software/C_object_example.png
