gibbs212521/HEC_2_senior_design/Hardware/Receiver/receiver_png/HEC2 Receiver_007.png

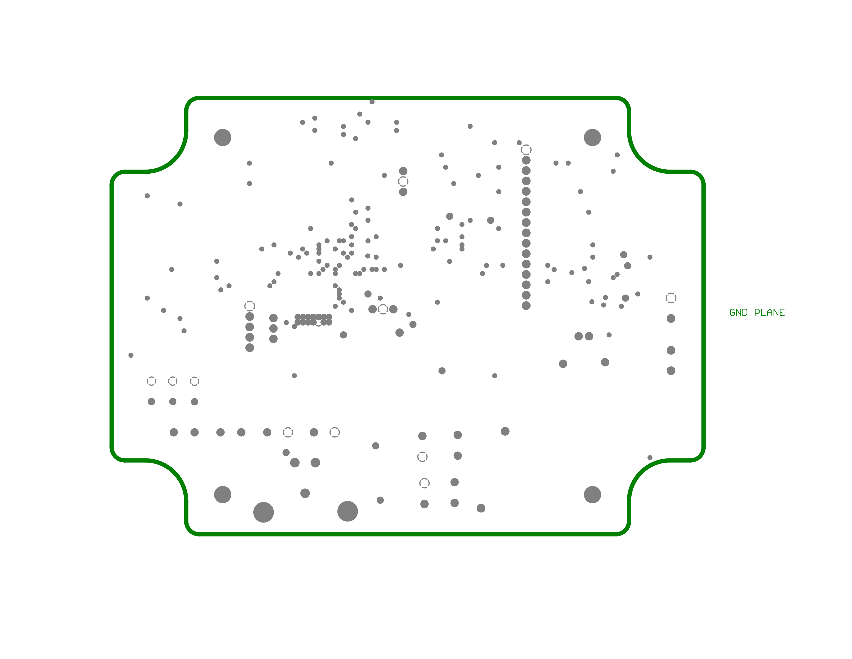
Hardware/Receiver/receiver_png/HEC2 Receiver_007.png
