gibbs212521/HEC_2_senior_design/Hardware/Transmitter/transmitter_png/HEC2 Transmitter_011.png

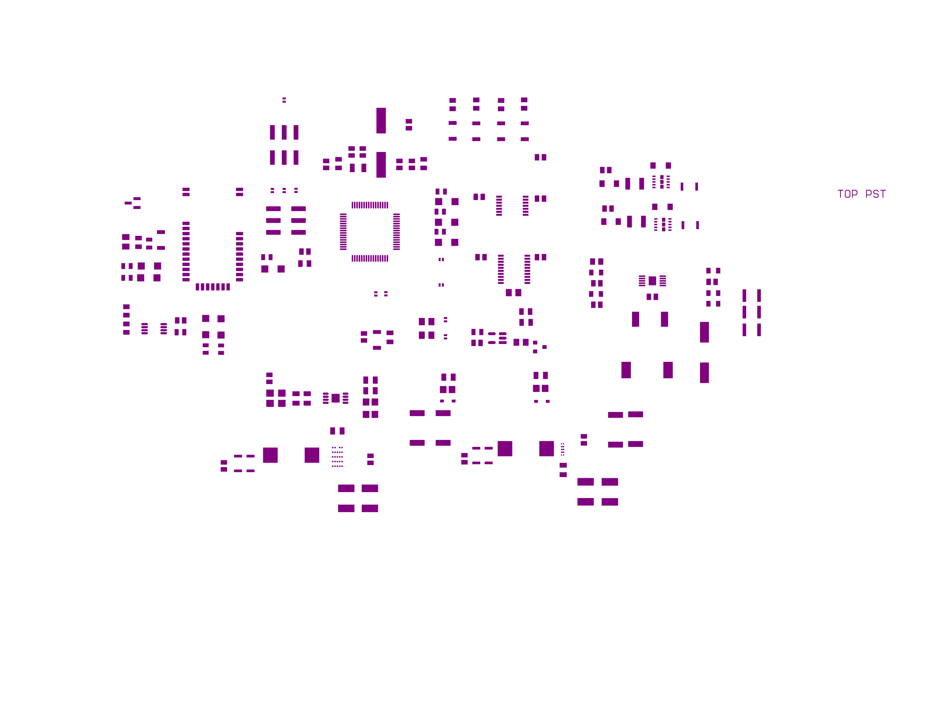
Hardware/Transmitter/transmitter_png/HEC2 Transmitter_011.png
