gibbs212521/HEC_2_senior_design/LaTeX/images/48V_sim.png

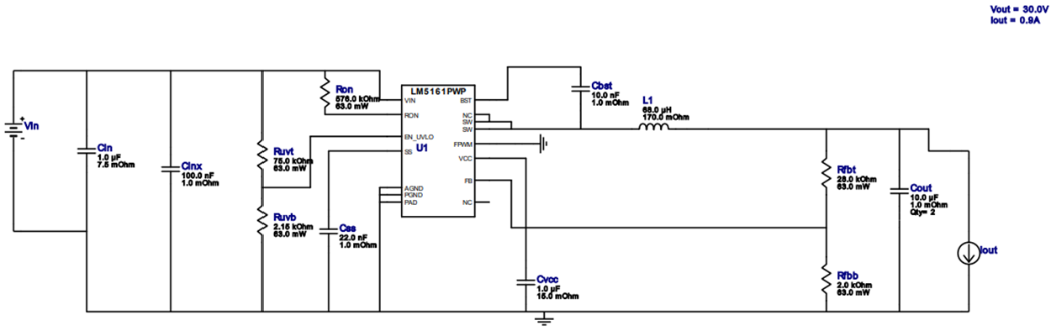
LaTeX/images/48V_sim.png
