gibbs212521/HEC_2_senior_design/LaTeX/images/Class_E_amplifier_trans.png

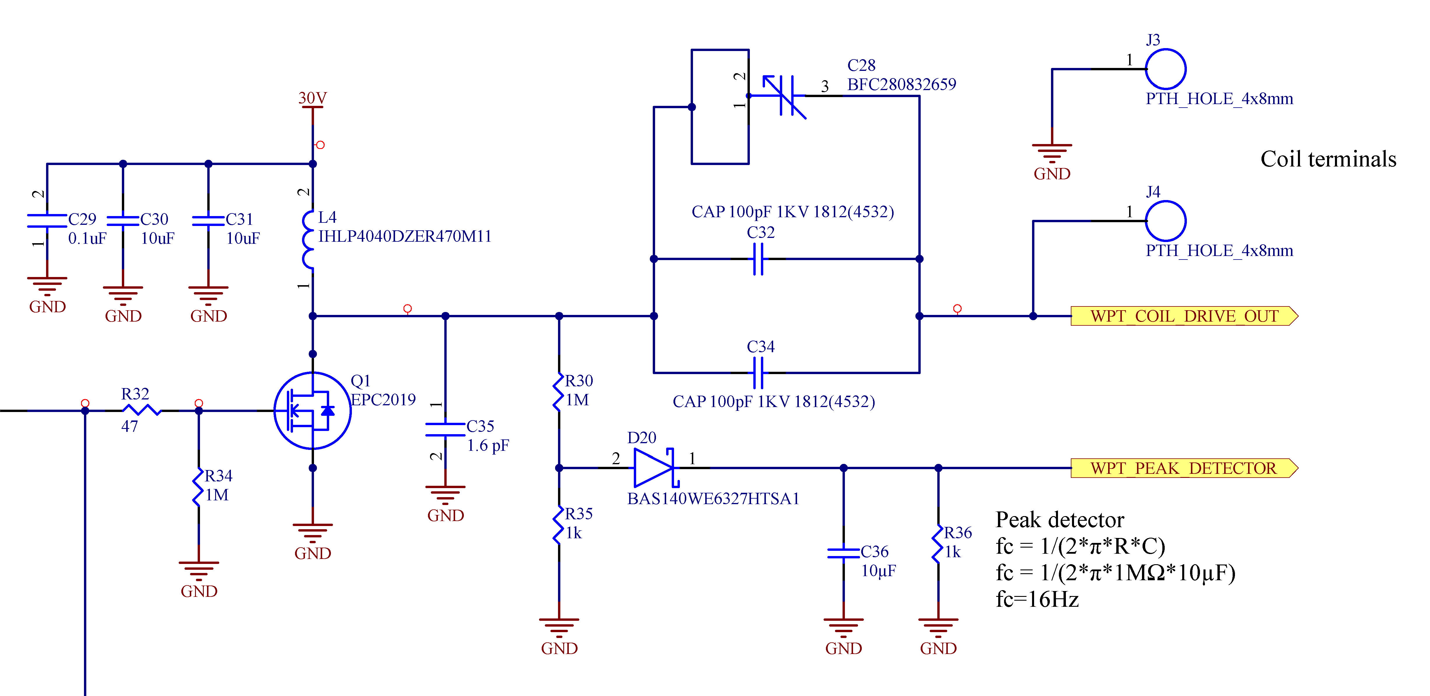
LaTeX/images/Class_E_amplifier_trans.png
