gibbs212521/HEC_2_senior_design/LaTeX/images/dag_diagram.png

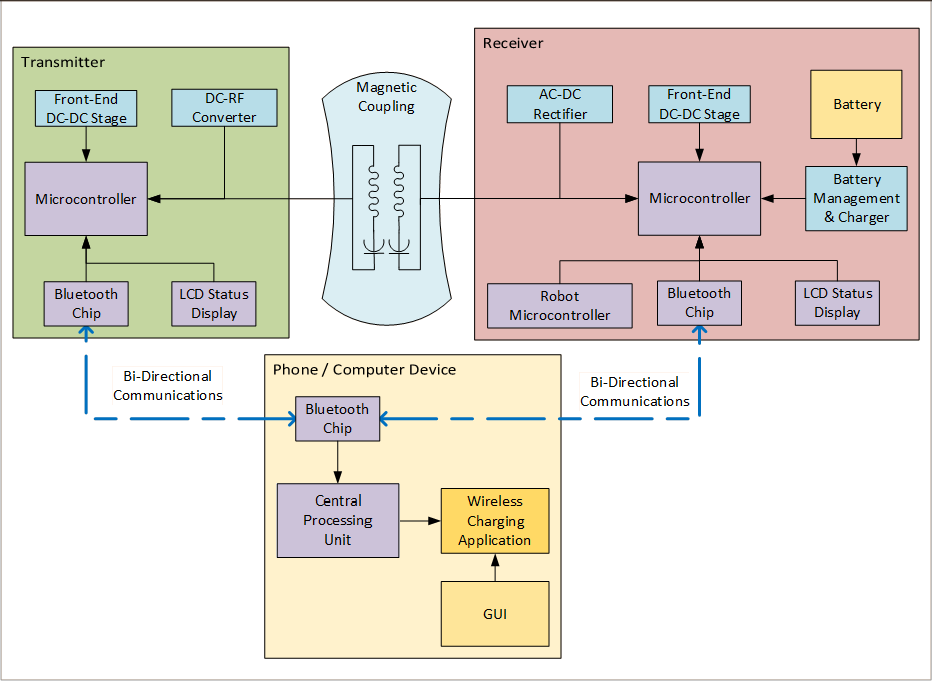
LaTeX/images/dag_diagram.png
