gibbs212521/HEC_2_senior_design/LaTeX/images/front_view.PNG

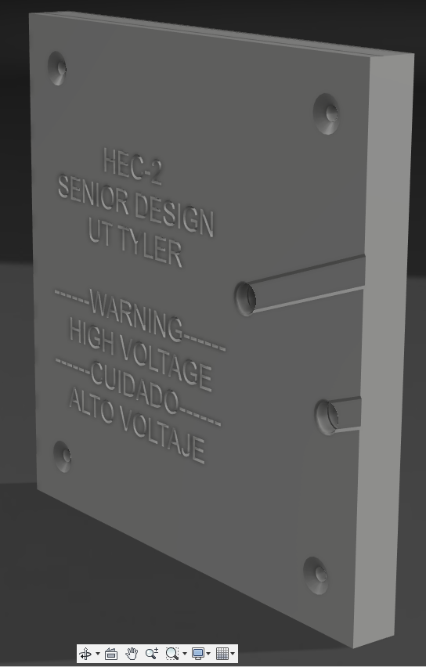
LaTeX/images/front_view.PNG
