gibbs212521/HEC_2_senior_design/LaTeX/images/no_lid_front.PNG

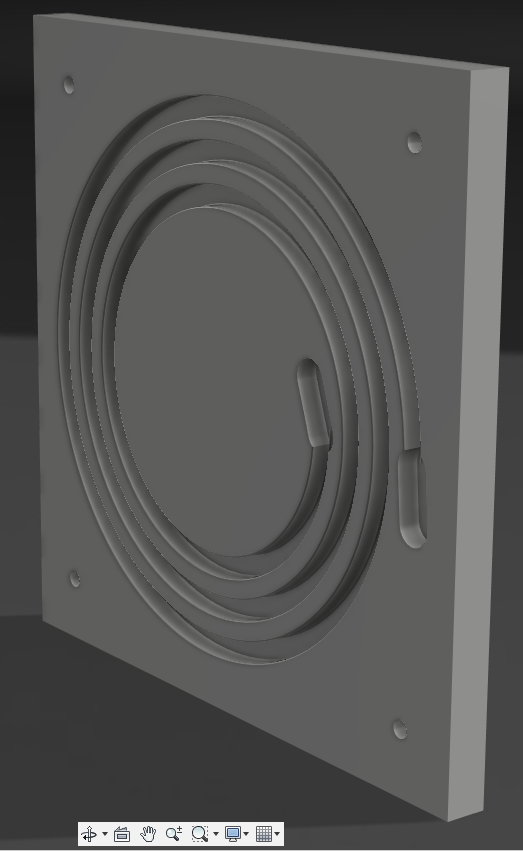
LaTeX/images/no_lid_front.PNG
