gibbs212521/HEC_2_senior_design/LaTeX/images/power_reg.PNG

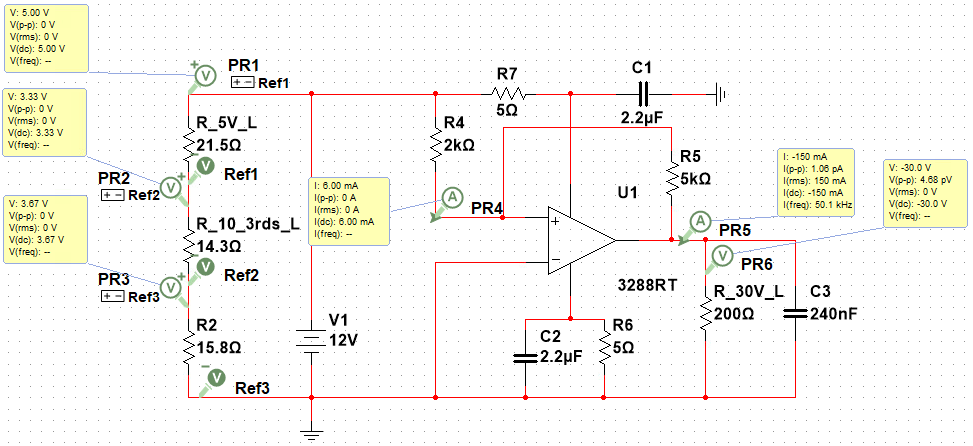
LaTeX/images/power_reg.PNG
