gibbs212521/HEC_2_senior_design/LaTeX/images/RX_COIL_Terminals_trans.png

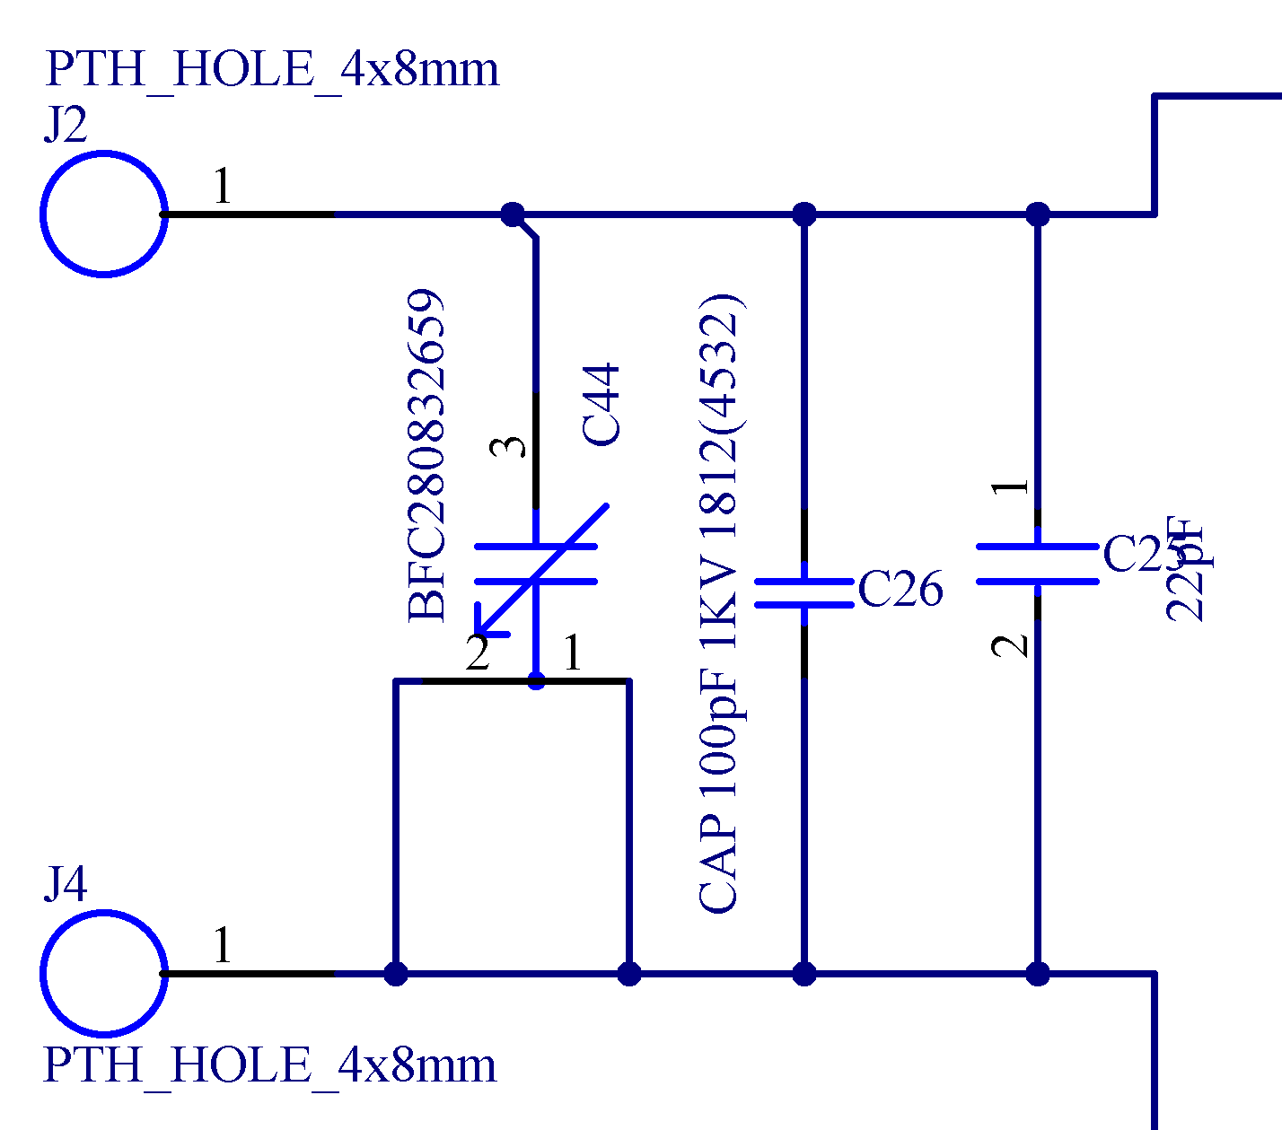
LaTeX/images/RX_COIL_Terminals_trans.png
