gibbs212521/HEC_2_senior_design/LaTeX/images/Transmitter_power_supply_sch_diag_trans.png

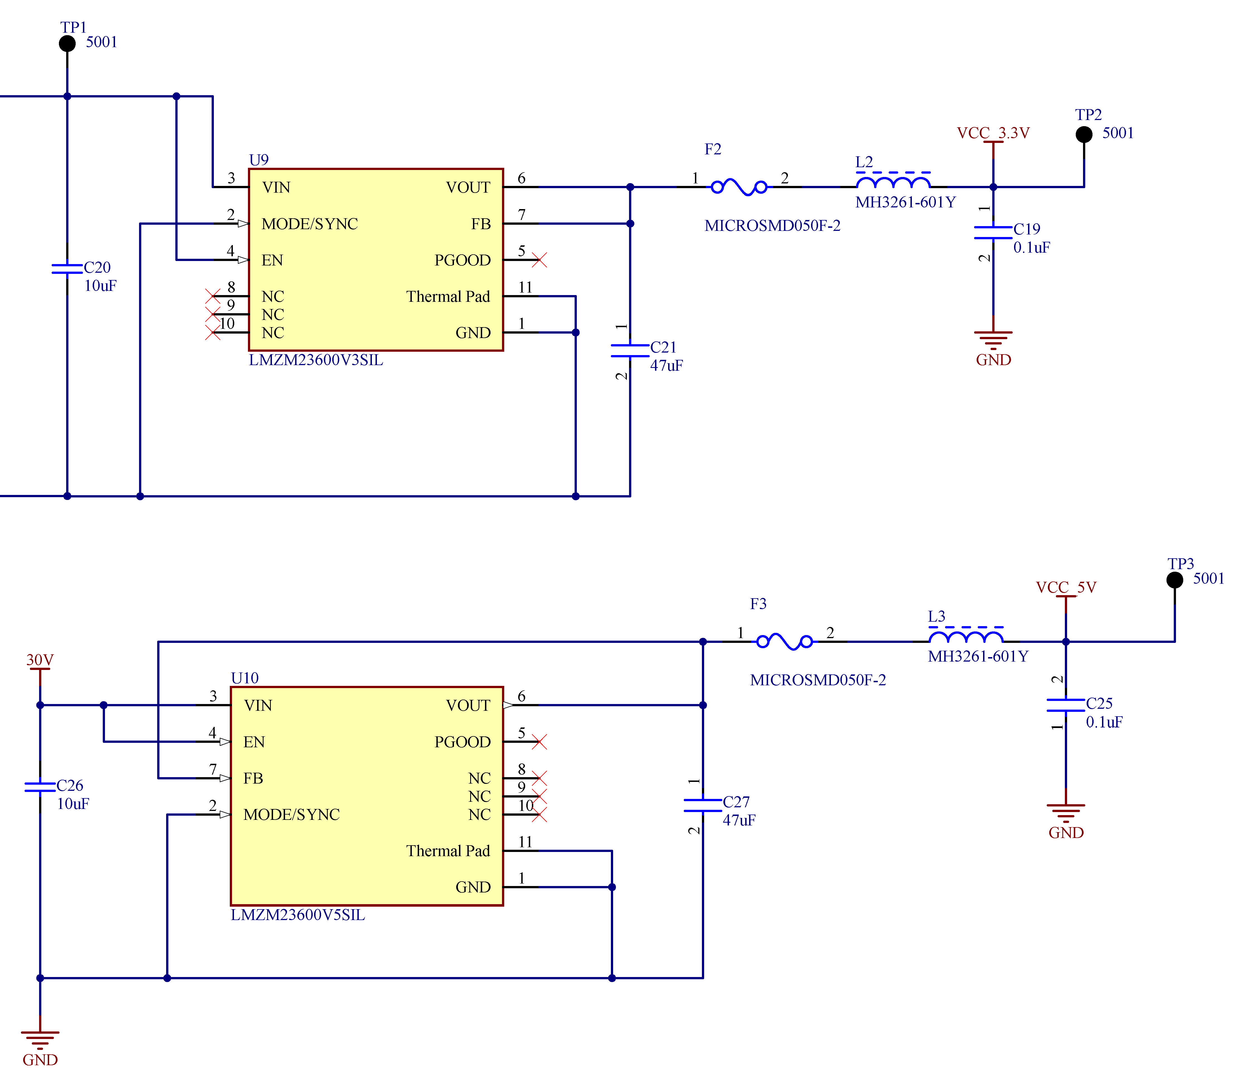
LaTeX/images/Transmitter_power_supply_sch_diag_trans.png
