gibbs212521/HEC_2_senior_design/LaTeX/images/tx_micro_bt_lcd.png

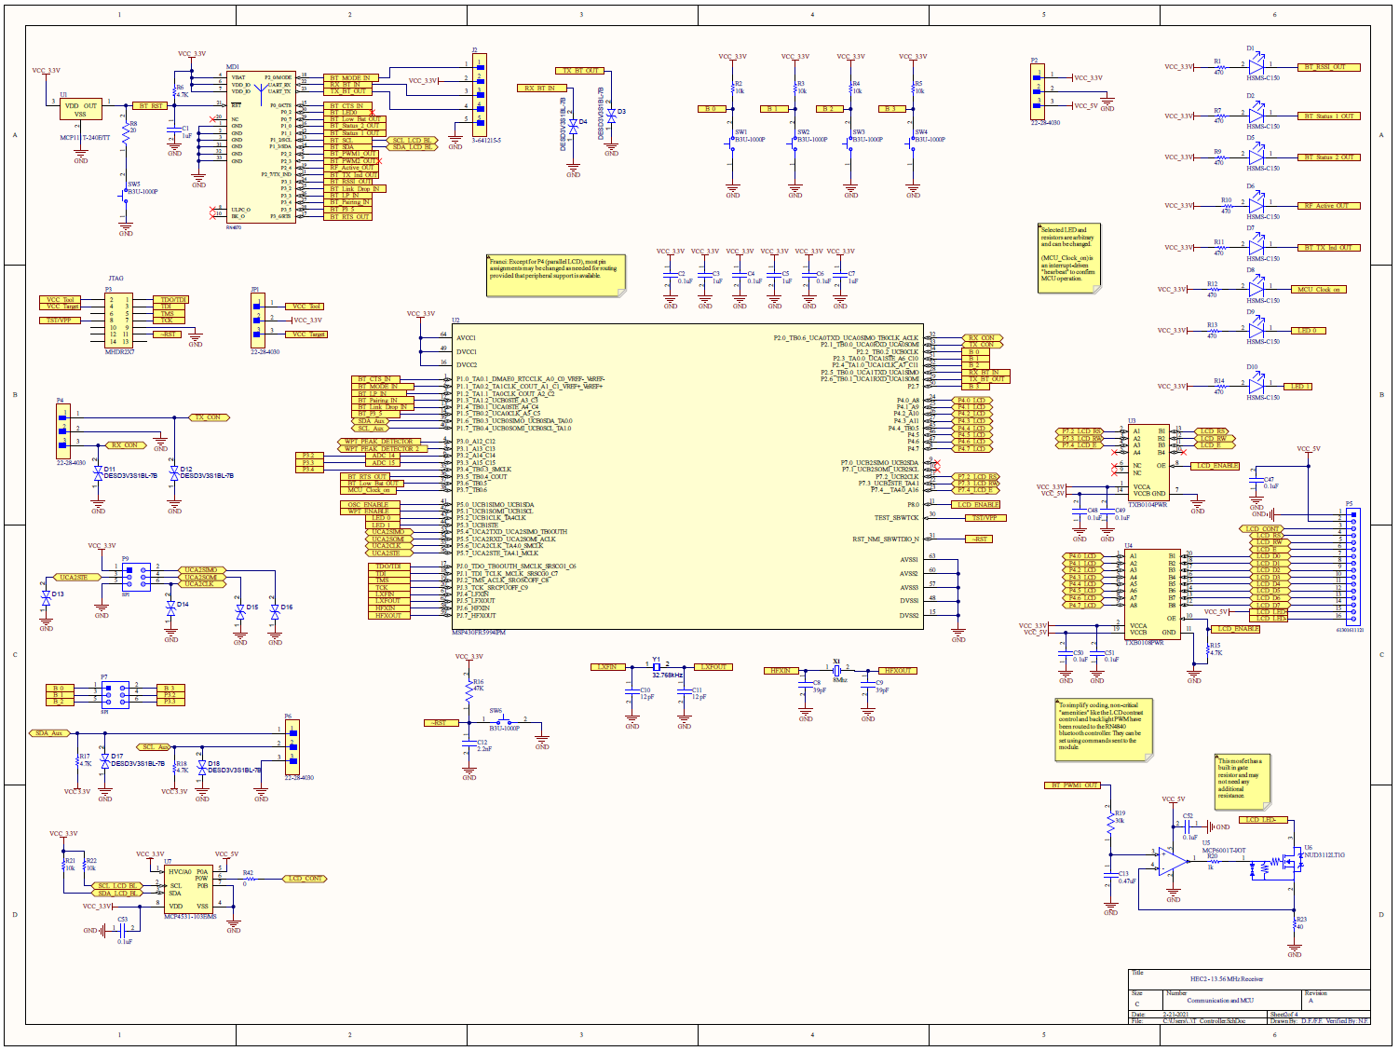
LaTeX/images/tx_micro_bt_lcd.png
