gibbs212521/HEC_2_senior_design/LaTeX/images/TX_oscillator_and_buffer_trans.png

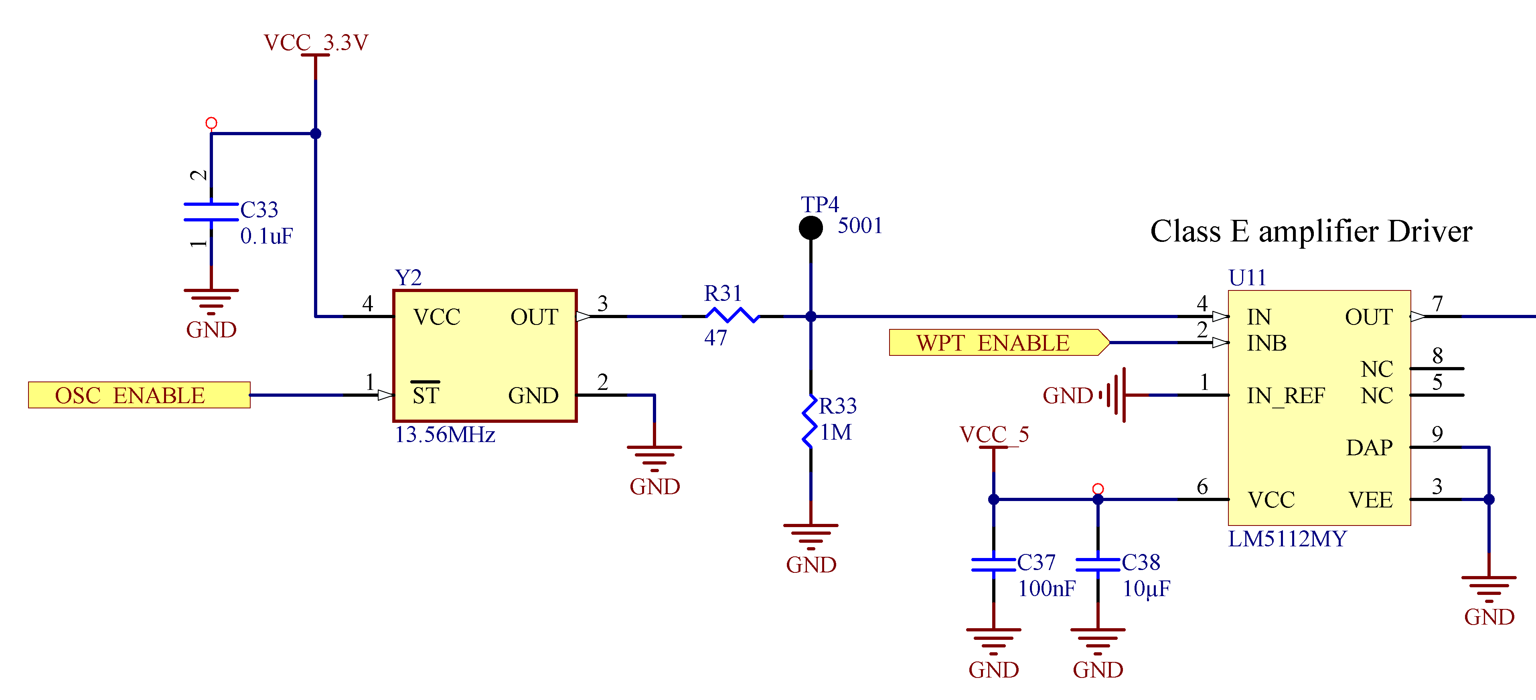
LaTeX/images/TX_oscillator_and_buffer_trans.png
