gibbs212521/HEC_2_senior_design/LaTeX/images/version_control_example.png

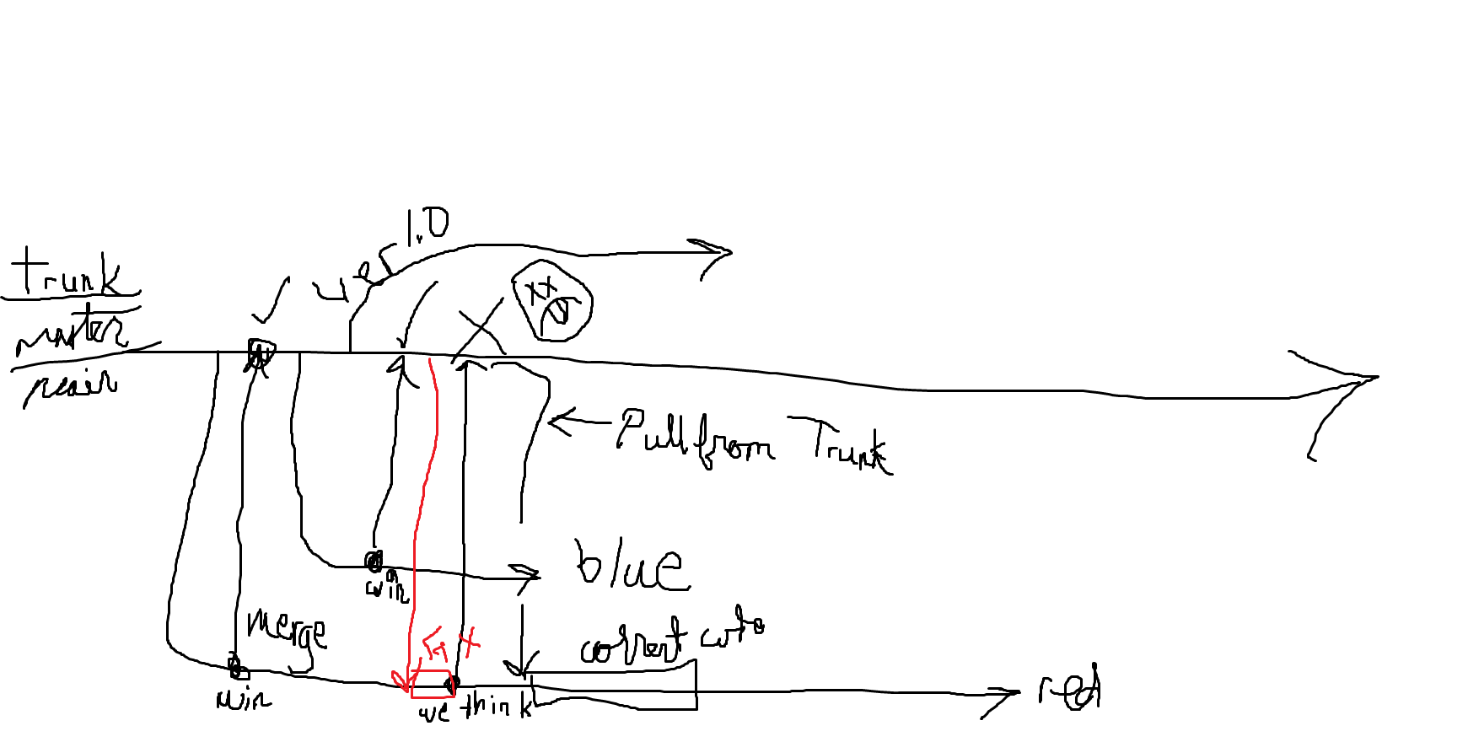
LaTeX/images/version_control_example.png
