gibbs212521/HEC_2_senior_design/docs/Preliminary/version_control_guide.PNG

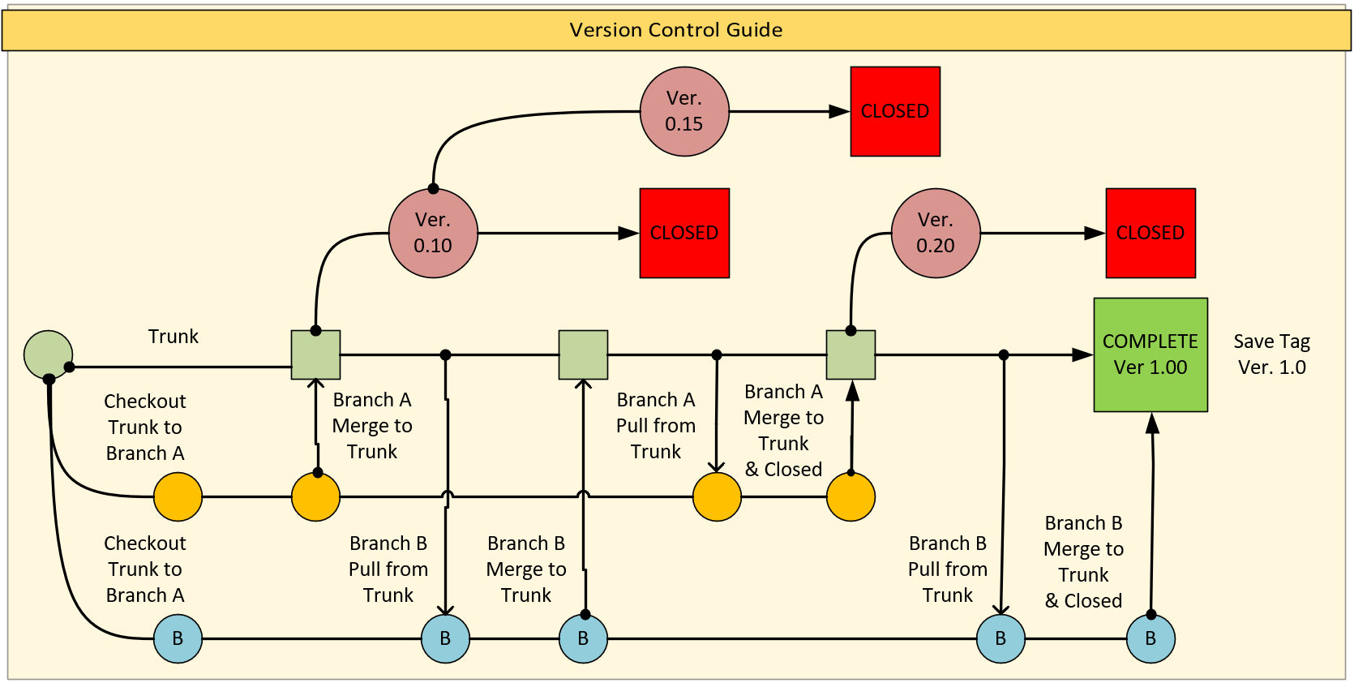
docs/Preliminary/version_control_guide.PNG
