gibbs212521/HEC_2_senior_design/LaTeX/appendices/gantt_1_dec_feb.pdf

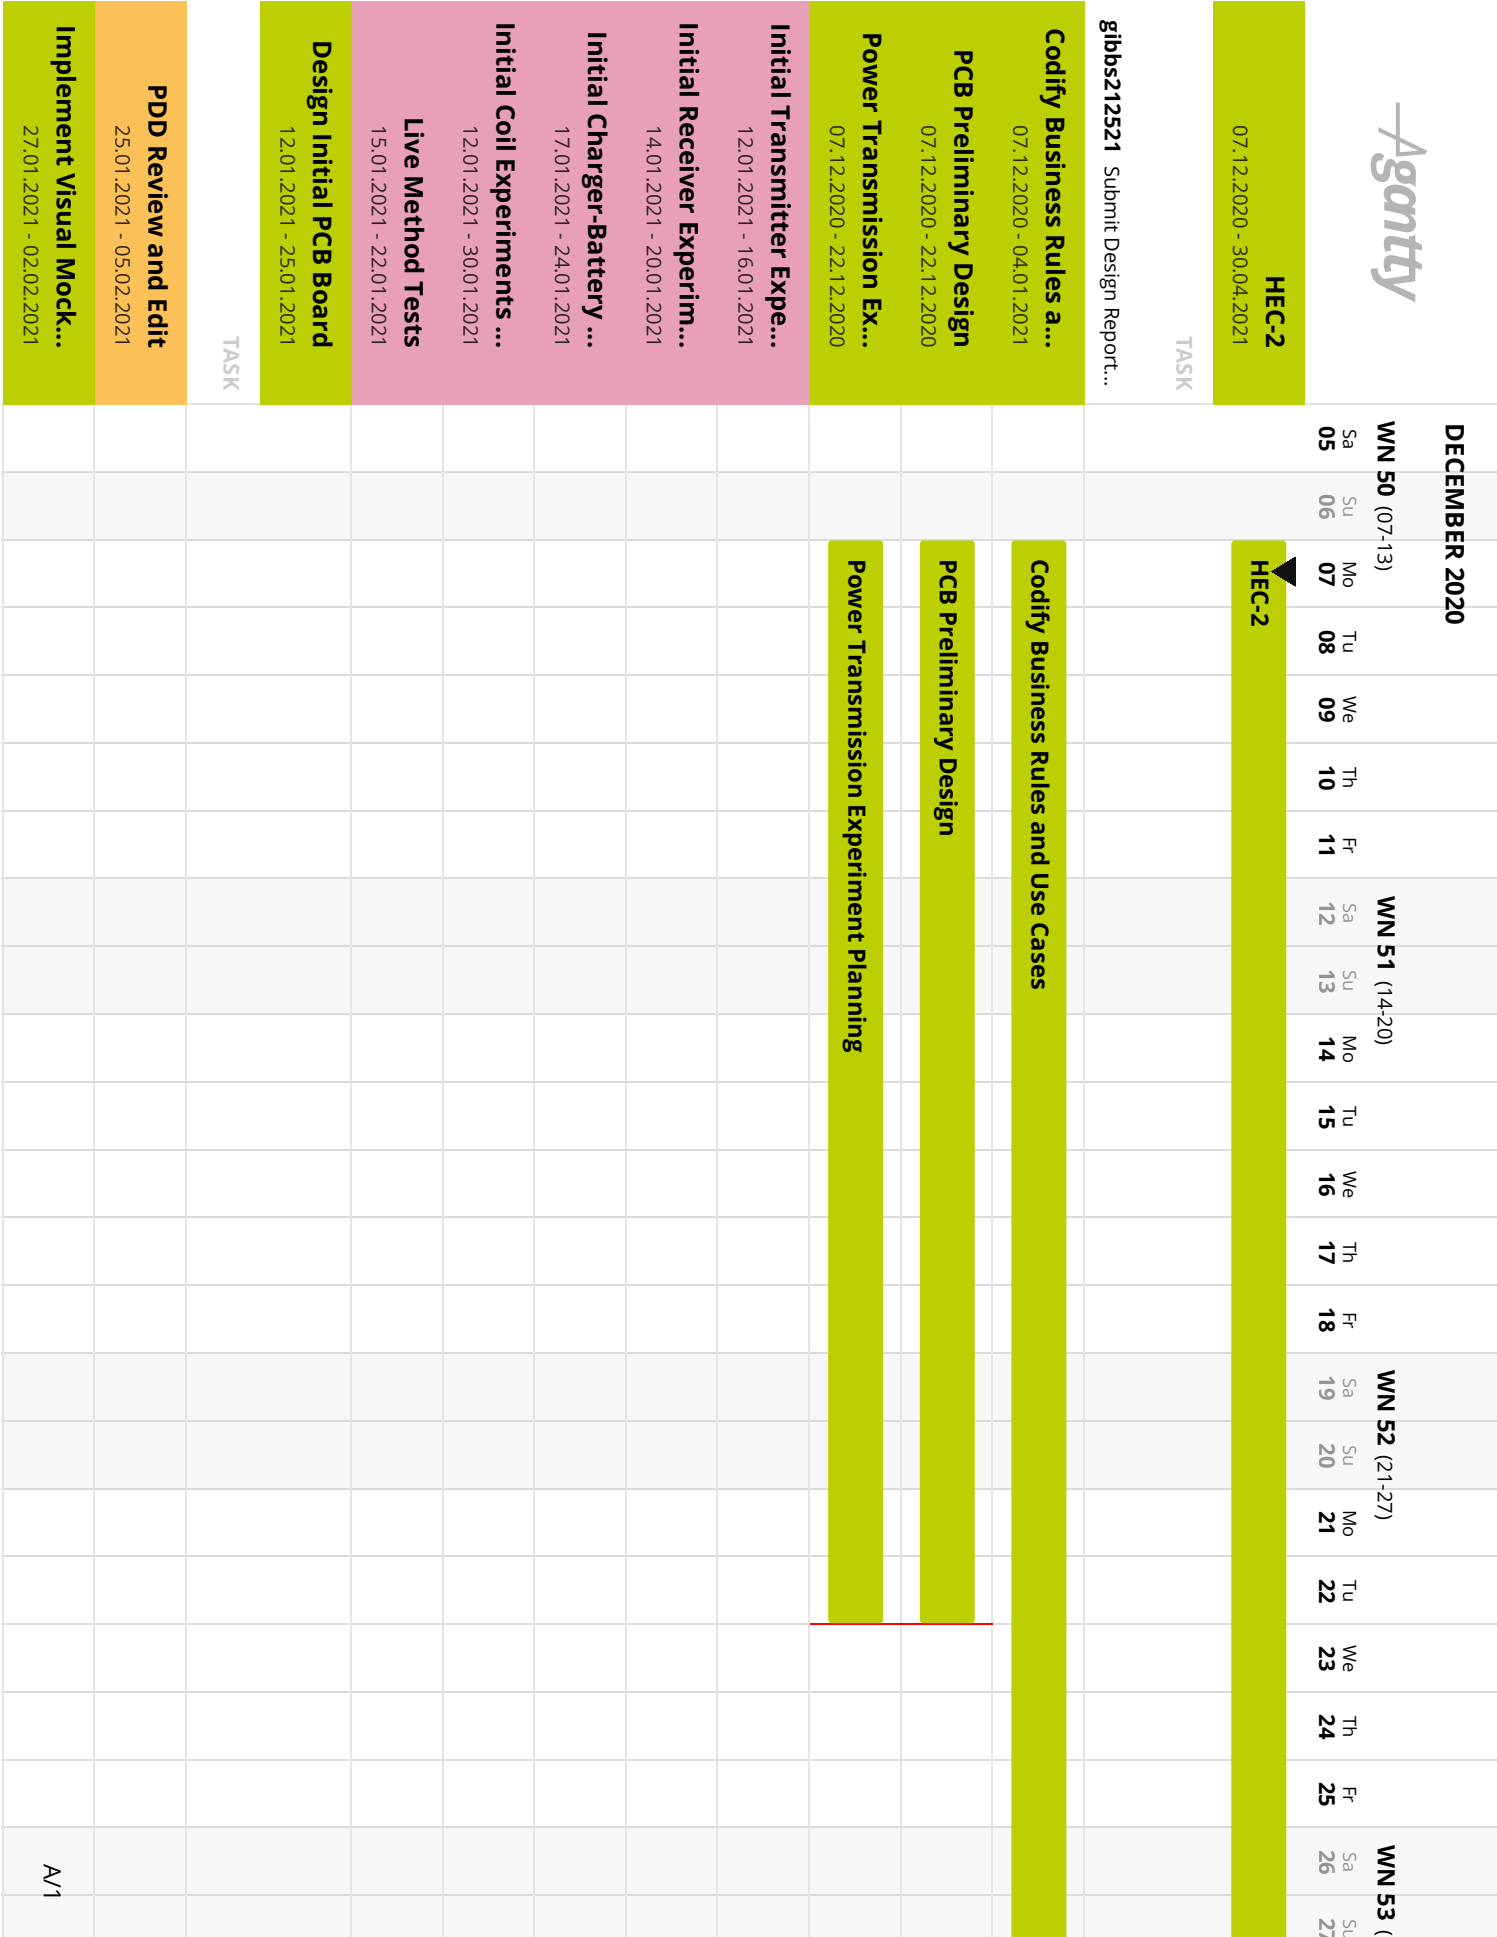
[picture p142: page 1]
gibbs212521; HEC-2; DECEMBER 2020

Submit Design Report... 07.12.2020 - 30.04.2021TASK Codify Business Rules a... 07.12.2020 - 04.01.2021 PCB Preliminary Design 07.12.2020 - 22.12.2020 Power Transmission Ex... 07.12.2020 - 22.12.2020 Initial Transmitter Expe... 12.01.2021 - 16.01.2021 Initial Receiver Experim... 14.01.2021 - 20.01.2021 Initial Charger-Battery ... 17.01.2021 - 24.01.2021 Initial Coil Experiments ... 12.01.2021 - 30.01.2021 Live Method Tests 15.01.2021 - 22.01.2021 Design Initial PCB Board 12.01.2021 - 25.01.2021TASK PDD Review and Edit 25.01.2021 - 05.02.2021 Implement Visual Mock... 27.01.2021 - 02.02.2021 Power Transmission Experiment Planning PCB Preliminary Design Codify Business Rules and Use Cases

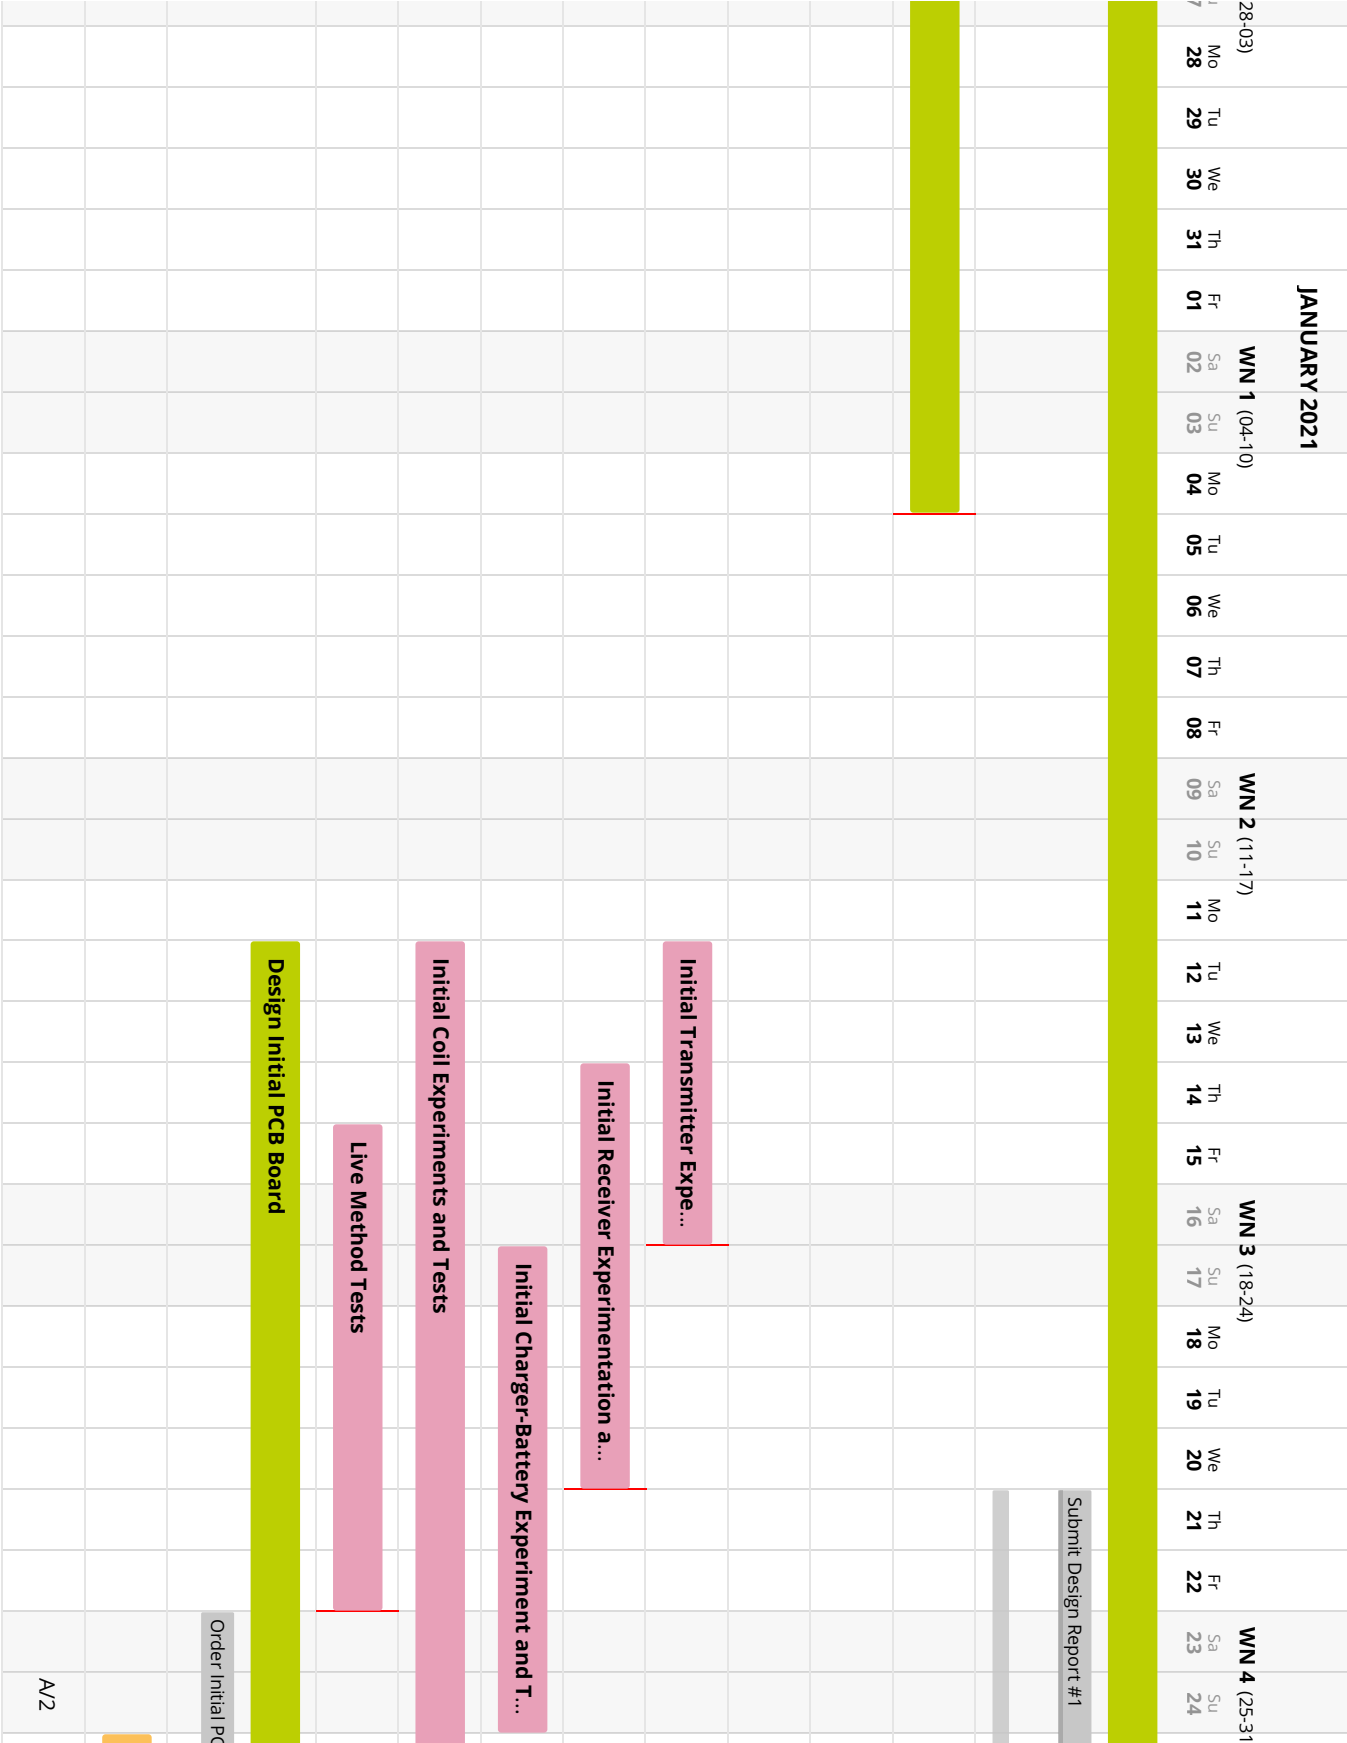
[picture p143: page 2]
JANUARY 2021

Design Initial PCB Board

Initial Coil Experiments and Tests

Submit Design Report #1 ... Initial Transmitter Expe ... Initial Receiver Experimentation a ... Initial Charger-Battery Experiment and T

Live Method Tests

Order Initial PC

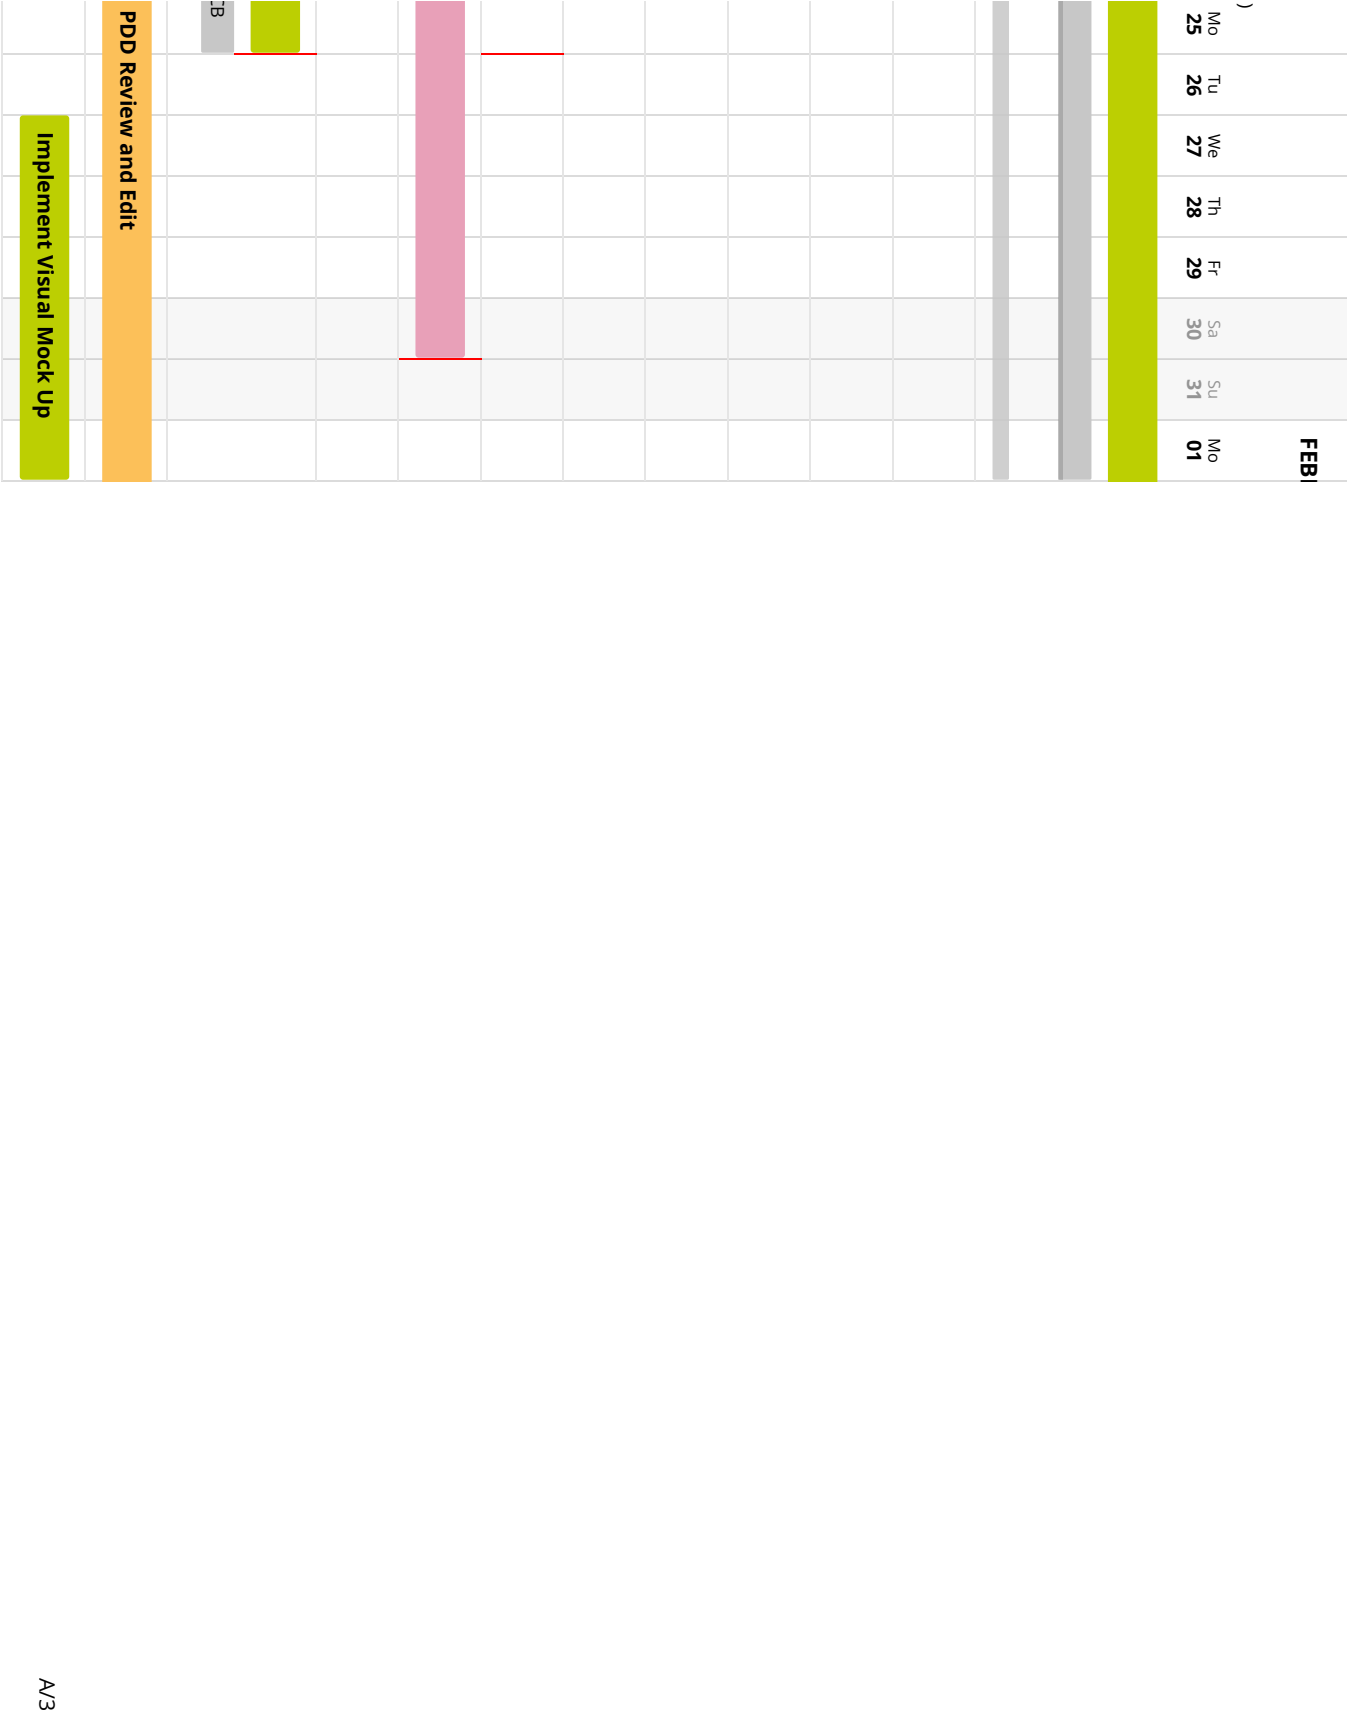
[picture p144: page 3]
FEBR

PDD Review and Edit

Implement Visual Mock Up
