gibbs212521/HEC_2_senior_design/LaTeX/appendices/gantt_3_mar_apr.pdf

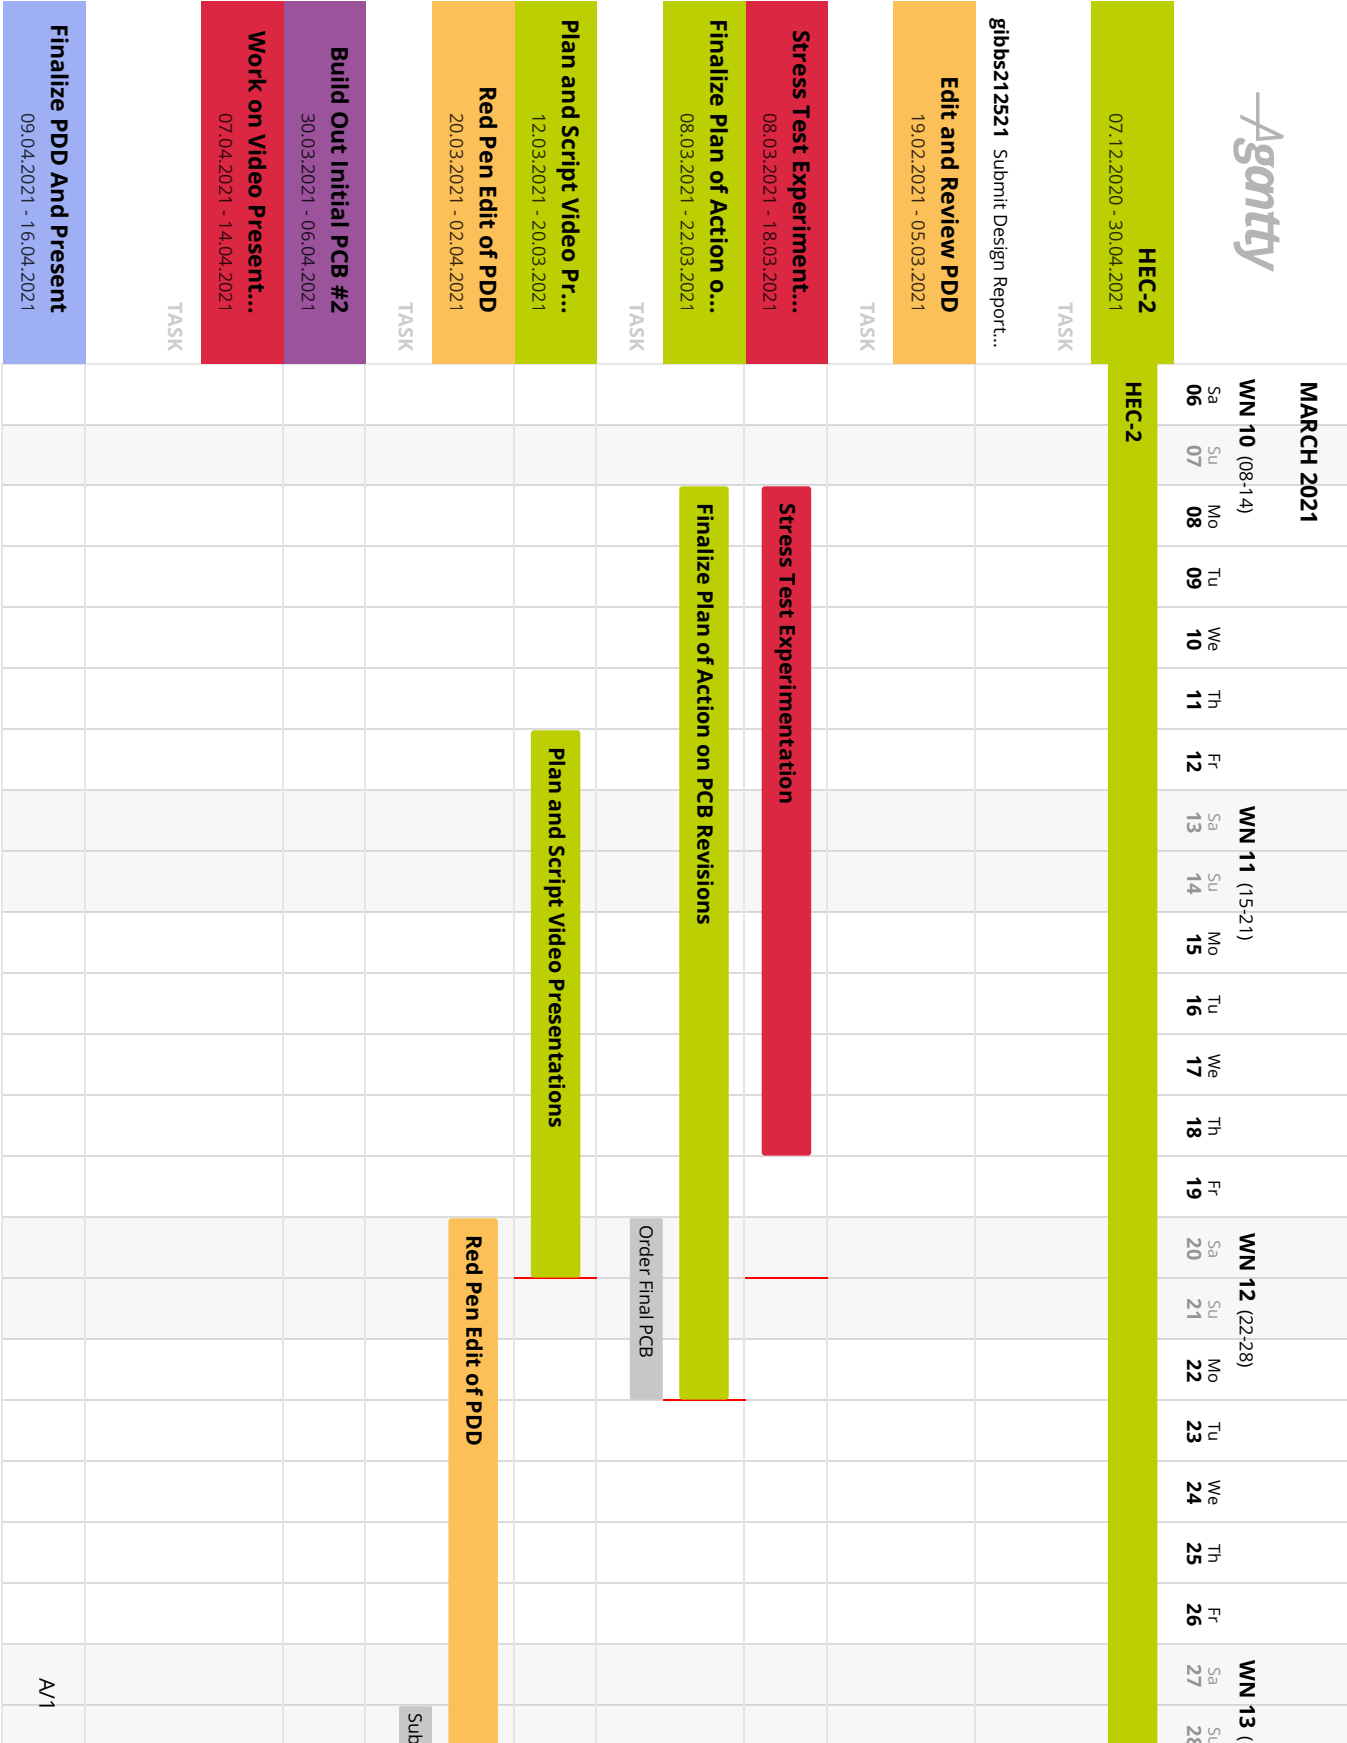
[picture p145: page 1]
gibbs212521; HEC-2; Sub; MARCH 2021

Submit Design Report... 07.12.2020 - 30.04.2021TASK Edit and Review PDD 19.02.2021 - 05.03.2021TASK Stress Test Experiment... 08.03.2021 - 18.03.2021 Finalize Plan of Action o... 08.03.2021 - 22.03.2021TASK Plan and Script Video Pr... 12.03.2021 - 20.03.2021 Red Pen Edit of PDD 20.03.2021 - 02.04.2021TASK Build Out Initial PCB #2 30.03.2021 - 06.04.2021 Work on Video Present... 07.04.2021 - 14.04.2021TASK Finalize PDD And Present 09.04.2021 - 16.04.2021

Finalize Plan of Action on PCB Revisions

Stress Test Experimentation

Plan and Script Video Presentations

Red Pen Edit of PDD

Order Final PCB

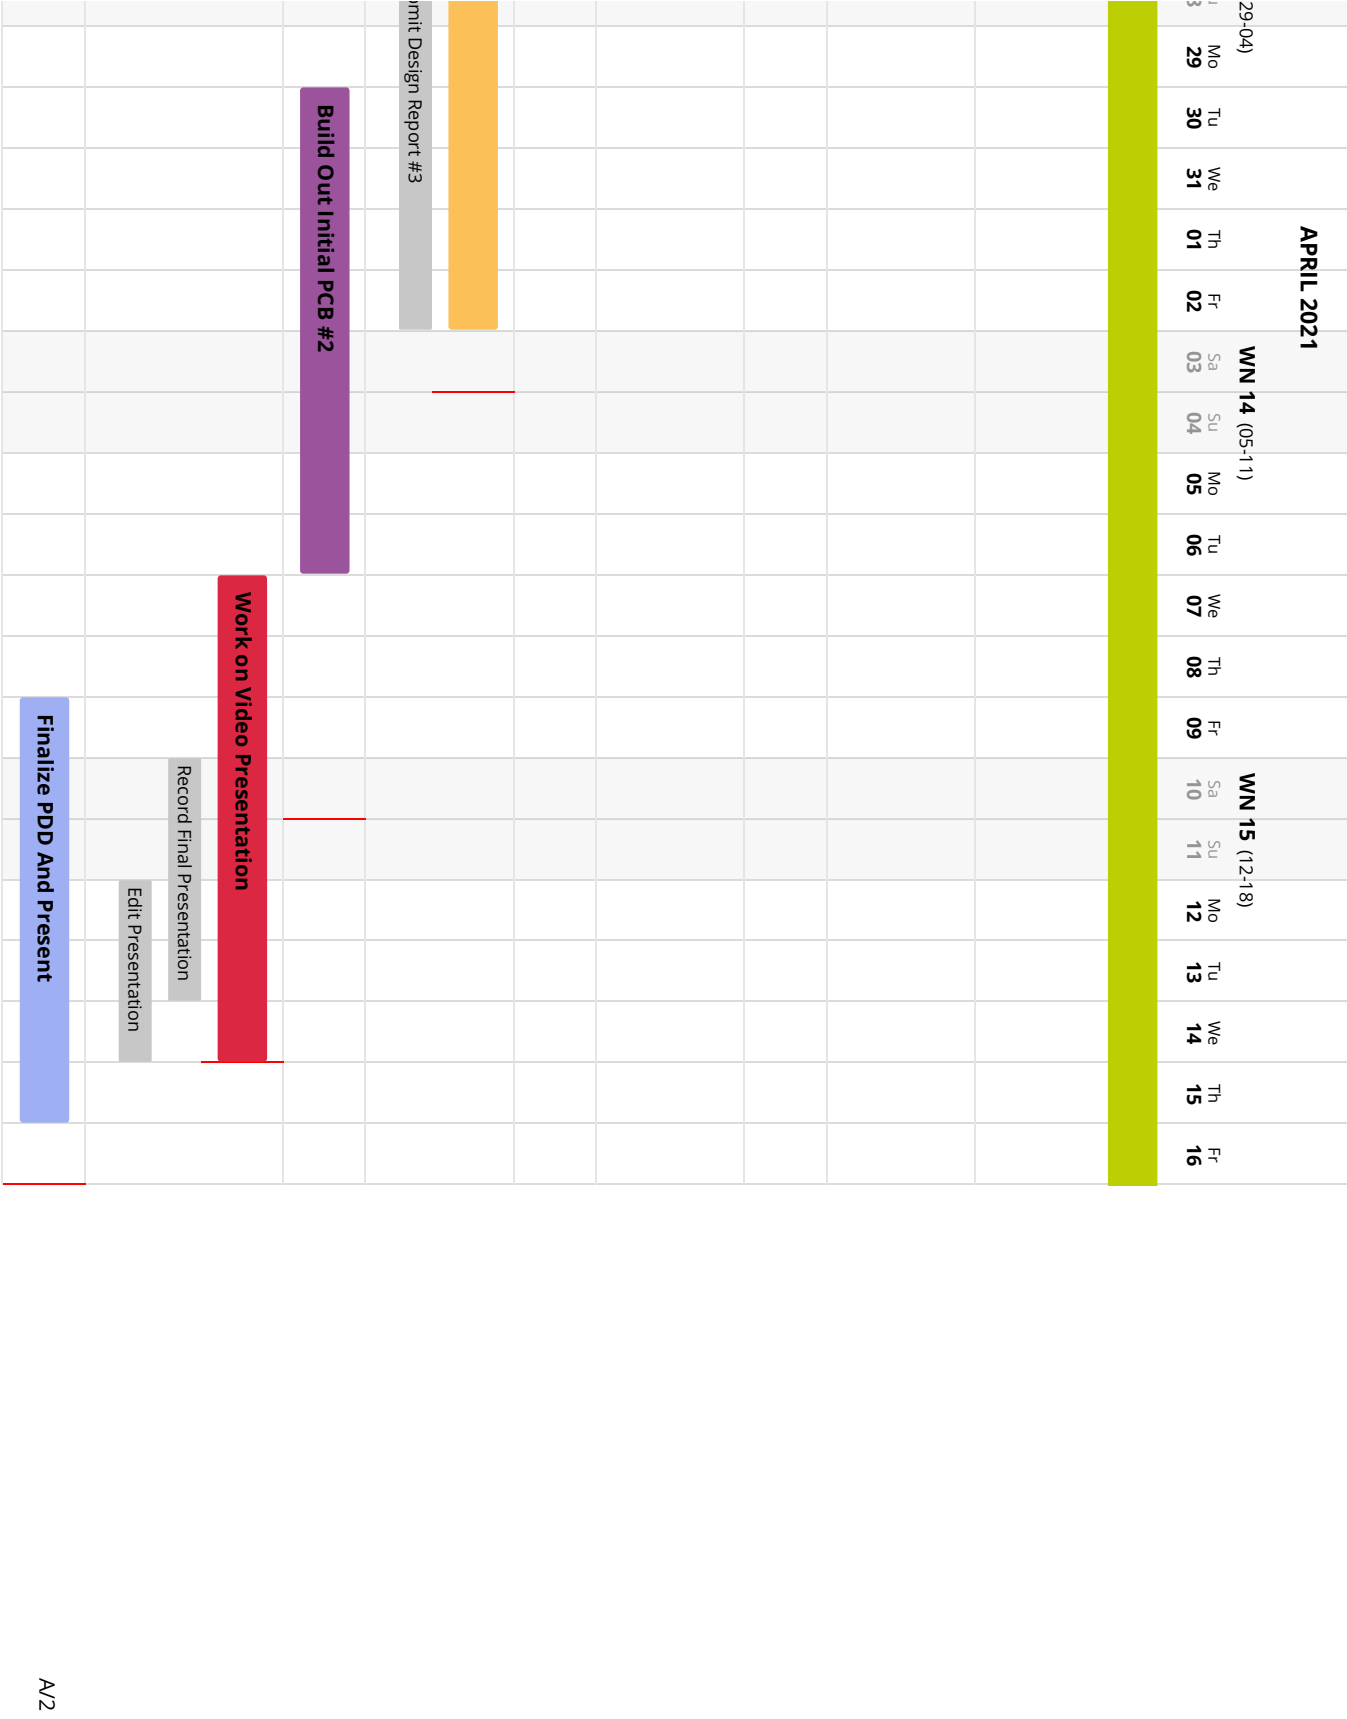
[picture p146: page 2]
Edit Presentation; APRIL 2021

Finalize PDD And Present 8

bmit Design Report #3

Build Out Initial PCB #2

Work on Video Presentation

Record Final Presentation
