gibbs212521/HEC_2_senior_design/LaTeX/simulations/48_30_DC.pdf

## WEBENCH ® Design Report

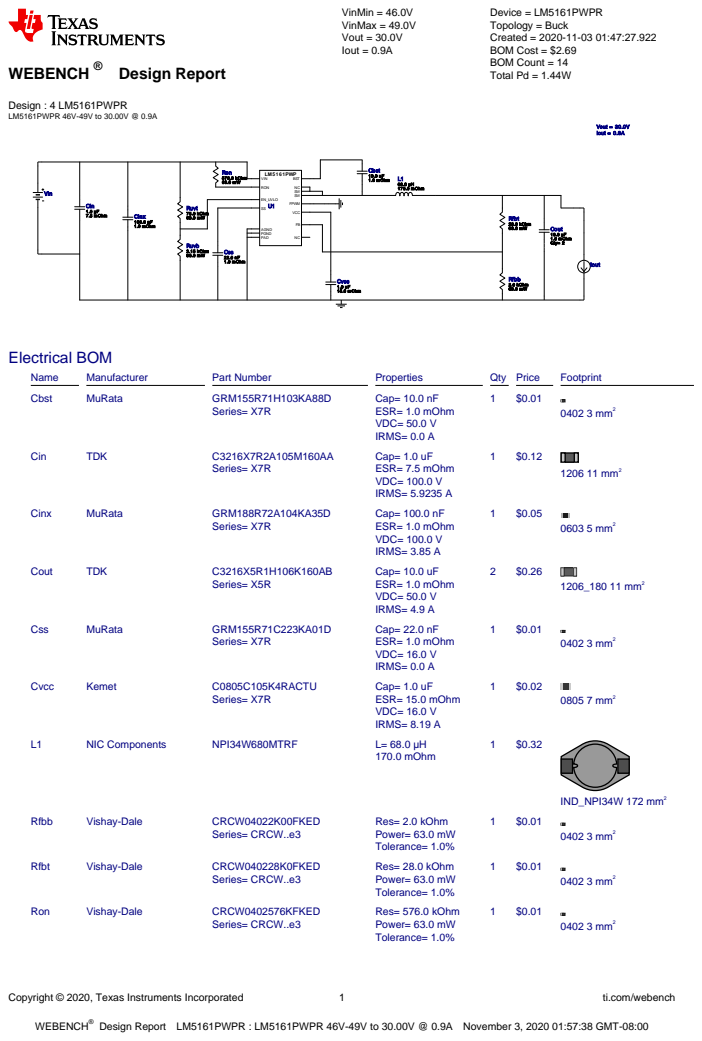
[picture p154: page 1]
Copyright © 2020, Texas Instruments Incorporated; ti.com/webench; WEBENCH®; Design : 4 LM5161PWPR LM5161PWPR 46V-49V to 30.00V @ 0.9A; VinMin = 46.0V VinMax = 49.0V Vout = 30.0V Iout = 0.9A; Device = LM5161PWPR Topology = Buck Created = 2020-11-03 01:47:27.922 BOM Cost = $2.69 BOM Count = 14 Total Pd = 1.44W; Cin 1.0 µF; 7.5 mOhm; Cinx; 1.0 mOhm; Cout 10.0 µF; 1.0 mOhm Qty= 2; Css 22.0 nF 1.0 mOhm; Cvcc 1.0 µF 15.0 mOhm; L1 68.0 µH 170.0 mOhm; Rfbb 2.0 kOhm 63.0 mW; Rfbt 28.0 kOhm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

Design Report LM5161PWPR : LM5161PWPR 46V-49V to 30.00V @ 0.9A November 3, 2020 01:57:38 GMT-08:00

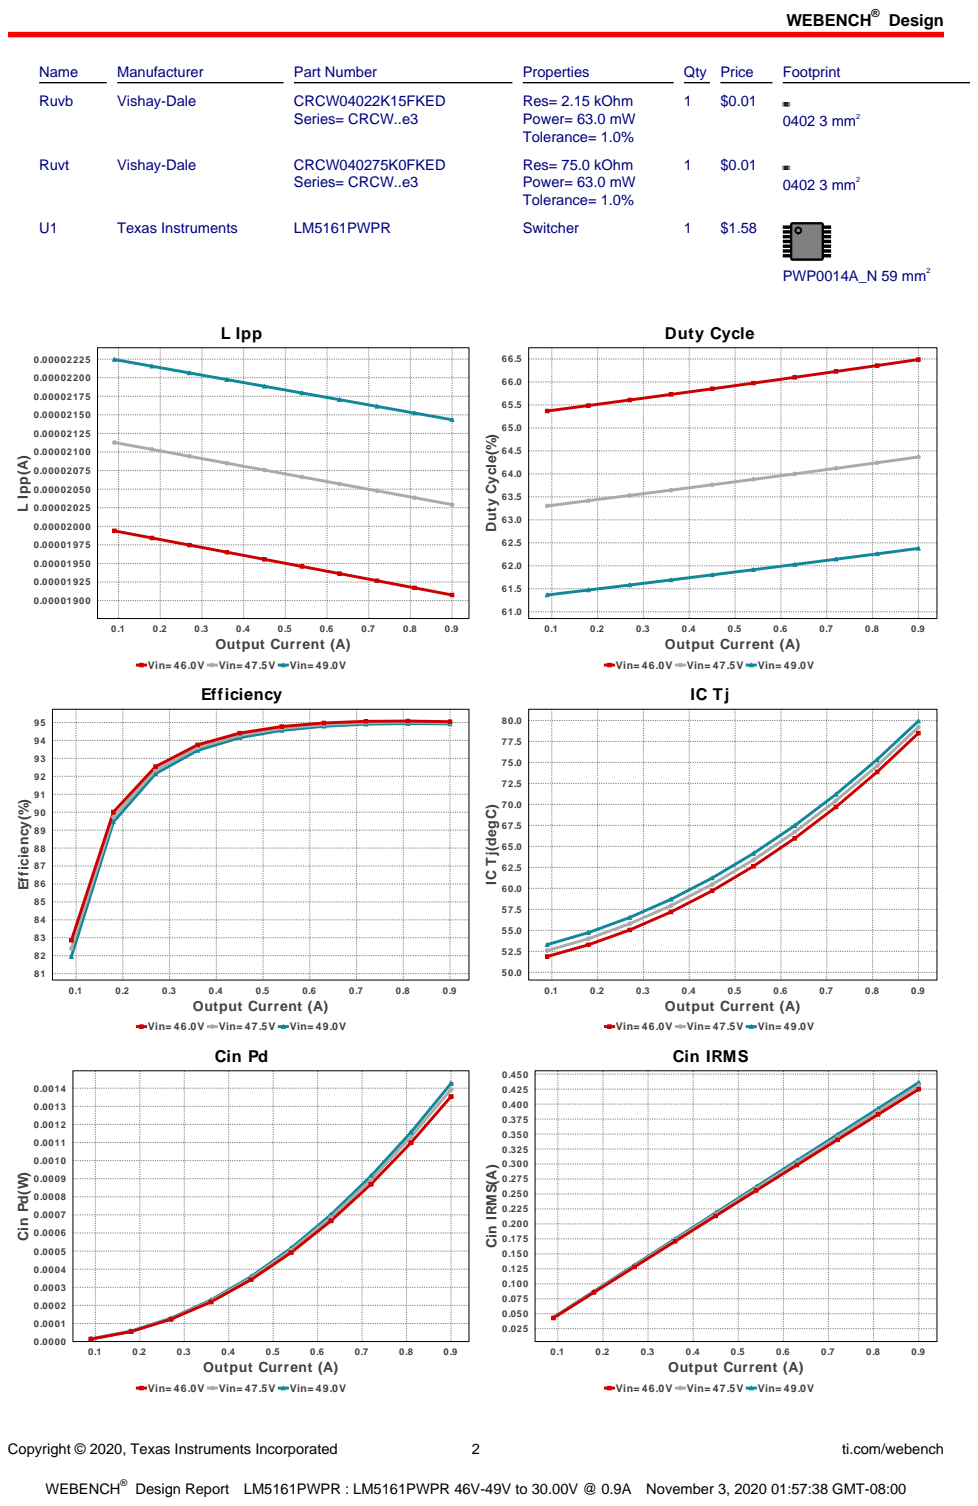
[picture p155: page 2]
Design; Copyright © 2020, Texas Instruments Incorporated; ti.com/webench; Name; Manufacturer; Part Number; Properties; Qty Price; Footprint; Ruvb; Vishay-Dale; CRCW04022K15FKED; Series= CRCW..e3; Res= 2.15 kOhm Power= 63.0 mW Tolerance= 1.0%; 0402 3 mm²; Ruvt; CRCW040275K0FKED; Res= 75.0 kOhm Power= 63.0 mW Tolerance= 1.0%; Texas Instruments; LM5161PWPR; Switcher; PWP0014A_N 59 mm²; L Ipp; 0.9 Output Current (A); L Ipp(A); Duty Cycle; Duty Cycle(%); Efficiency(%); Cin Pd; Cin Pd(W); Cin IRMS(A)

Vin= 46.0V Vin= 47.5V Vin= 49.0V
Efficiency

IC Tj(degC)

Cin IRMS

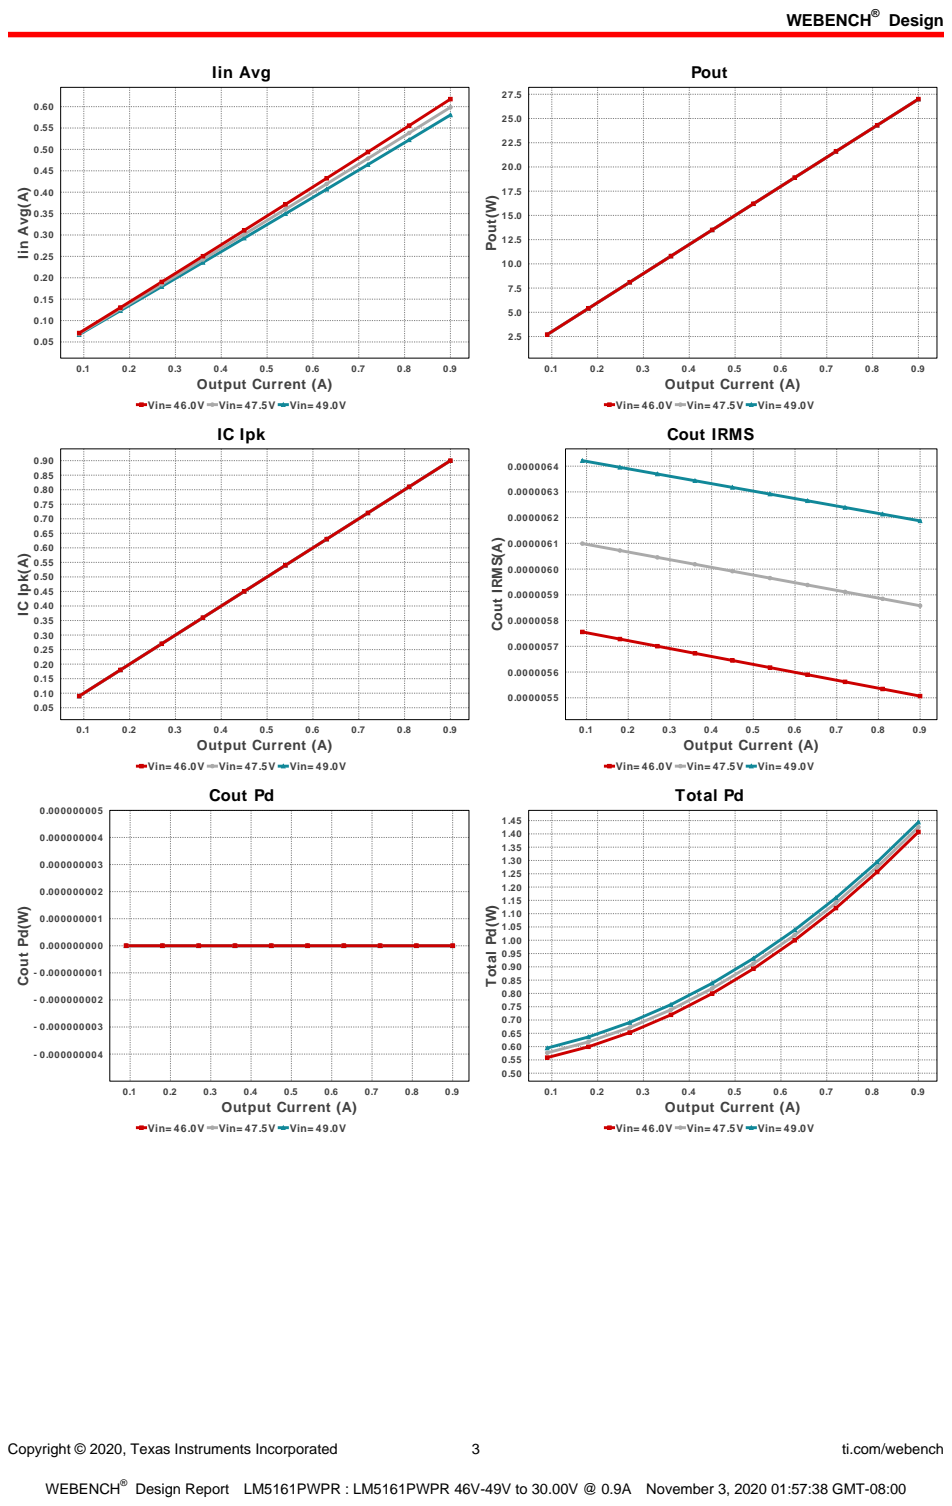
[picture p156: page 3]
Copyright © 2020, Texas Instruments Incorporated; ti.com/webench; Iin Avg; 0.9 Output Current (A); Iin Avg(A); Pout; Pout(W); IC Ipk; IC Ipk(A); Cout IRMS(A); Cout Pd; Cout Pd(W); Total Pd; Total Pd(W)

Vin= 46.0V Vin= 47.5V Vin= 49.0V

Cout IRMS

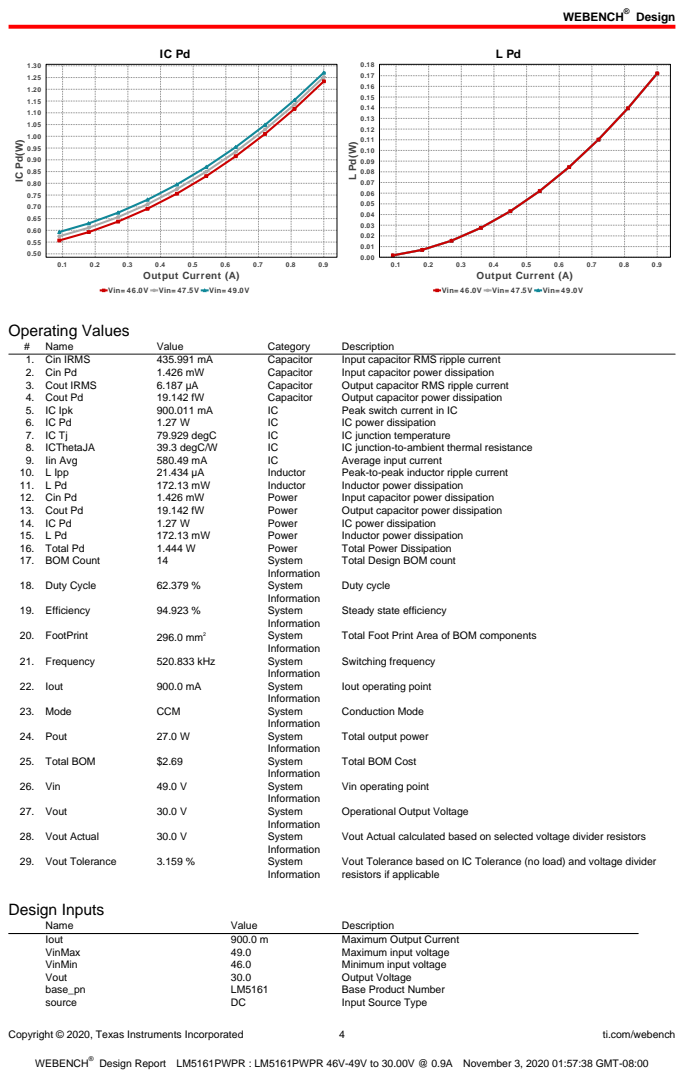
[picture p157: page 4]
Copyright © 2020, Texas Instruments Incorporated; ti.com/webench; 0.9 Output Current (A); Operating Values; Name; Value; Category; Description; 1. Cin IRMS; Capacitor; Input capacitor RMS ripple current; 2. Cin Pd; Input capacitor power dissipation; 3. Cout IRMS; Output capacitor RMS ripple current; 4. Cout Pd; Output capacitor power dissipation; 5. IC Ipk; Peak switch current in IC; IC power dissipation; 79.929 degC; IC junction temperature; 8. ICThetaJA; 39.3 degC/W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

Vin= 46.0V Vin= 47.5V Vin= 49.0V

Total Design BOM count

Steady state efficiency

Total Foot Print Area of BOM components

Iout operating point

Total output power

Total BOM Cost

Vin operating point

Operational Output Voltage

Vout Actual calculated based on selected voltage divider resistors

Vout Tolerance based on IC Tolerance (no load) and voltage divider
resistors if applicable

Copyright © 2020, Texas Instruments Incorporated | 5 | ti.com/webench
Name | Value | Description
Ta | 30.0 | Ambient temperature


Copyright © 2020, Texas Instruments Incorporated | 6 | ti.com/webench

## Assembly

## Component Testing

Some published data on components in datasheets such as Capacitor ESR and Inductor DC resistance is based on conservative values that will guarantee that the components always exceed the specification. For design purposes it is usually better to work with typical values. Since this data is not always available it is a good practice to measure the Capacitance and ESR values of Cin and Cout, and the inductance and DC resistance of L1 before assembly of the board. Any large discrepancies in values should be electrically simulated in WEBENCH to check for instabilities and thermally simulated in WebTHERM to make sure critical temperatures are not exceeded.

## Soldering Component to Board

If board assembly is done in house it is best to tack down one terminal of a component on the board then solder the other terminal. For surface mount parts with large tabs, such as the DPAK, the tab on the back of the package should be pre-tinned with solder, then tacked into place by one of the pins. To solder the tab town to the board place the iron down on the board while resting against the tab, heating both surfaces simultaneously. Apply light pressure to the top of the plastic case until the solder flows around the part and the part is flush with the PCB. If the solder is not flowing around the board you may need a higher wattage iron (generally 25W to 30W is enough).

## Initial Startup of Circuit

It is best to initially power up the board by setting the input supply voltage to the lowest operating input voltage 46.0V and set the input supply's current limit to zero. With the input supply off connect up the input supply to Vin and GND. Connect a digital volt meter and a load if needed to set the minimum Iout of the design from Vout and GND. Turn on the input supply and slowly turn up the current limit on the input supply.
If the voltage starts to rise on the input supply continue increasing the input supply current limit while watching the output voltage. If the current increases on the input supply, but the voltage remains near zero, then there may be a short or a component misplaced on the board. Power down the board and visually inspect for solder bridges and recheck the diode and capacitor polarities. Once the power supply circuit is operational then more extensive testing may include full load testing, transient load and line tests to compare with simulation results.

## Load Testing

The setup is the same as the initial startup, except that an additional digital voltmeter is connected between Vin and GND, a load is connected between Vout and GND and a current meter is connected in series between Vout and the load. The load must be able to handle at least rated output power + 50% ( 7.5 watts for this design). Ideally the load is supplied in the form of a variable load test unit. It can also be done in the form of suitably large power resistors. When using an oscilloscope to measure waveforms on the prototype board, the ground leads of the oscilloscope probes should be as short as possible and the area of the loop formed by the ground lead should be kept to a minimum. This will help reduce ground lead inductance and eliminate EMI noise that is not actually present in the circuit.

## WEBENCH® Electrical Simulation Report

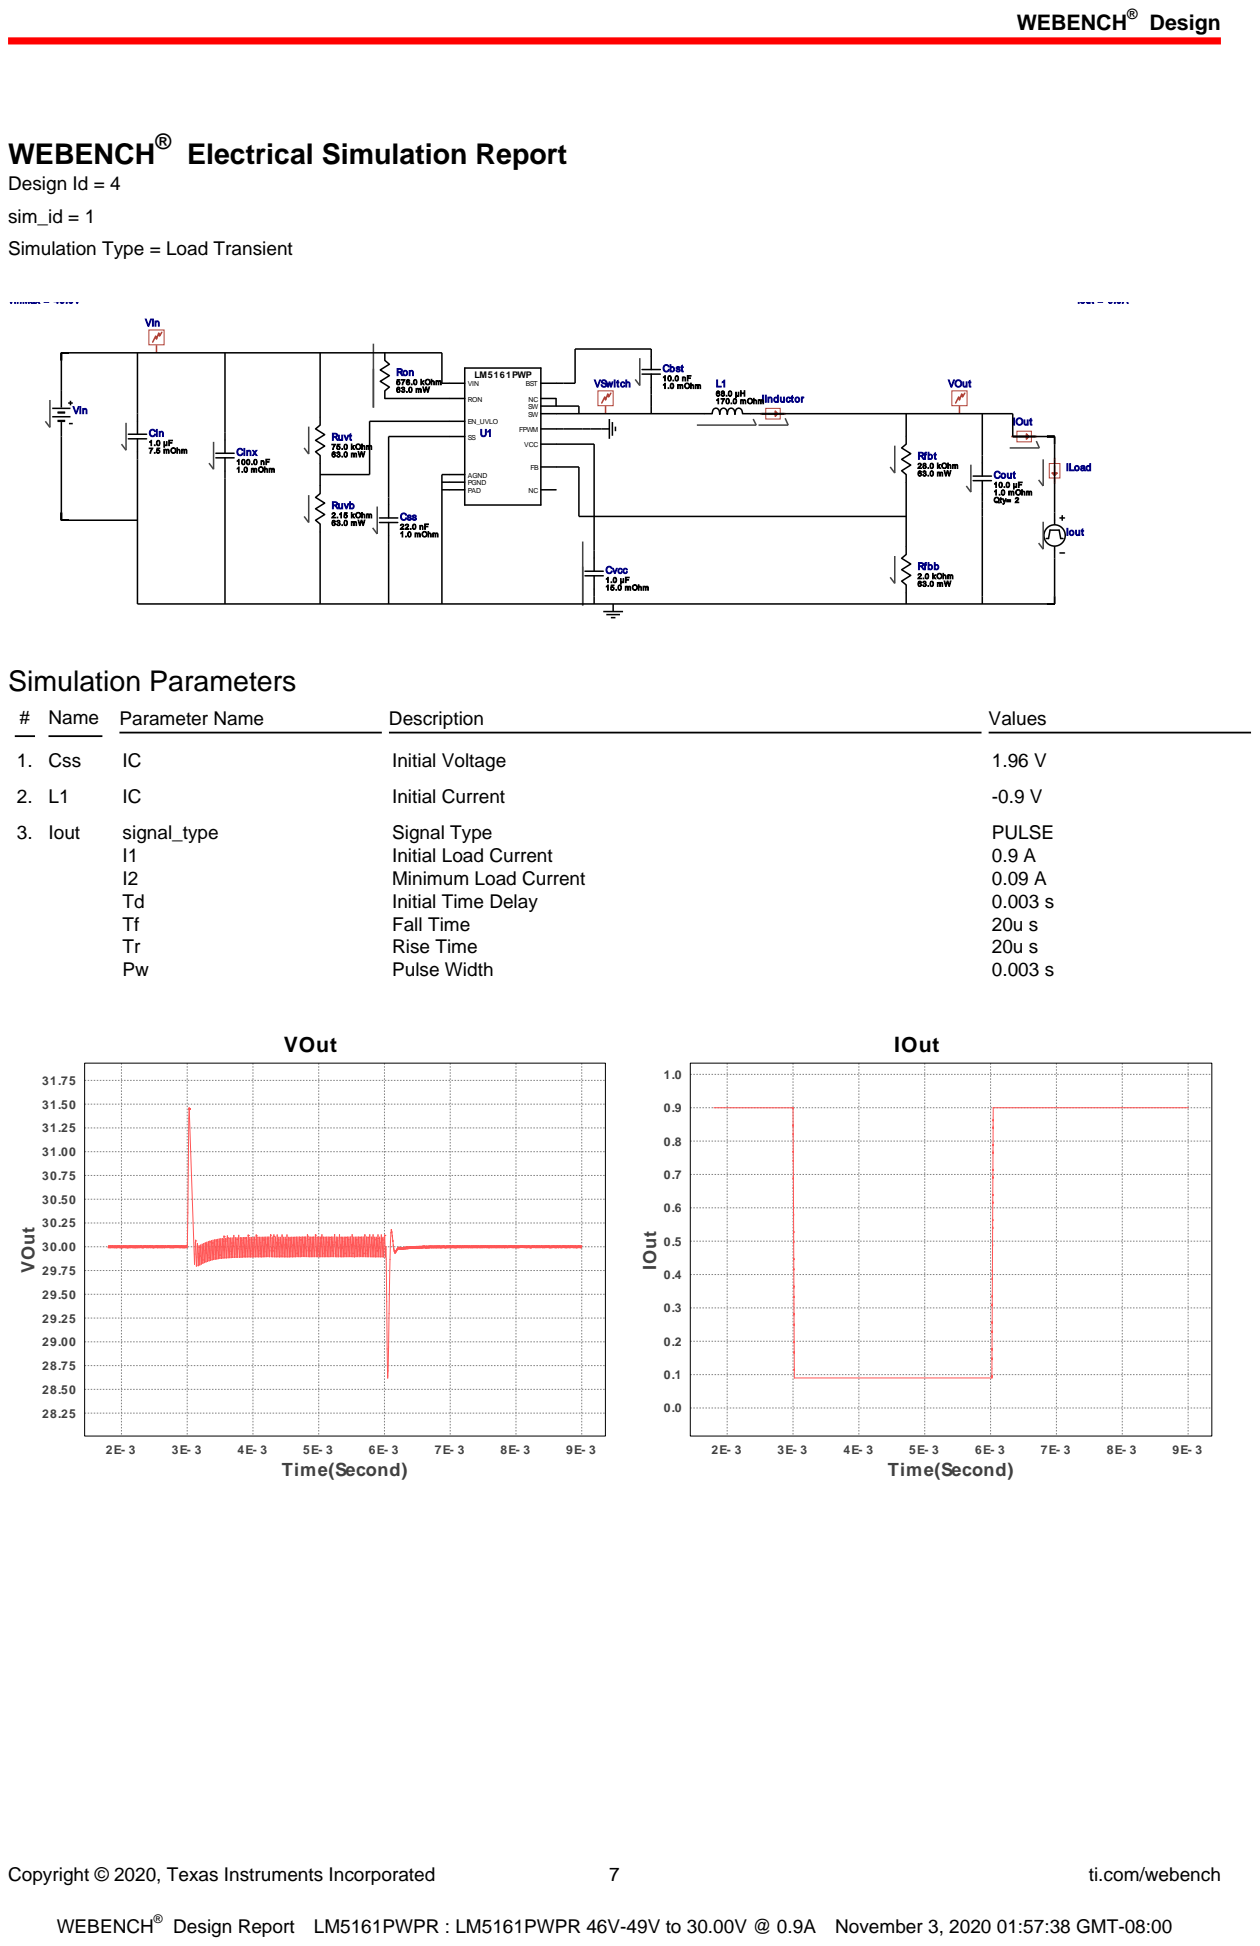
[picture p158: page 7]
Copyright © 2020, Texas Instruments Incorporated; ti.com/webench; Cin 1.0 µF; 7.5 mOhm; Cinx; 1.0 mOhm; Cout 10.0 µF; 1.0 mOhm Qty= 2; Css 22.0 nF 1.0 mOhm; Cvcc 1.0 µF 15.0 mOhm; IInductor; IOut; L1 68.0 µH 170.0 mOhm; Rfbb 2.0 kOhm 63.0 mW; Rfbt 28.0 kOhm; Ron 576.0 kOhm 63.0 mW; Ruvb 2.15 kOhm 63.0 mW; Ruvt 75.0 kOhm; LM5161PWP; AGND PGND; VIN; EN_UVLO; RON; FPWM; VCC; BST; PAD; VinMax = 49.0V; VIn; Iout = 0.9A; VSwitch; VOut; Cbst 10.0 nF; Vin; ILoad; Iout; Simulation Parameters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

Design Id = 4
sim_id = 1
Simulation Type = Load Transient

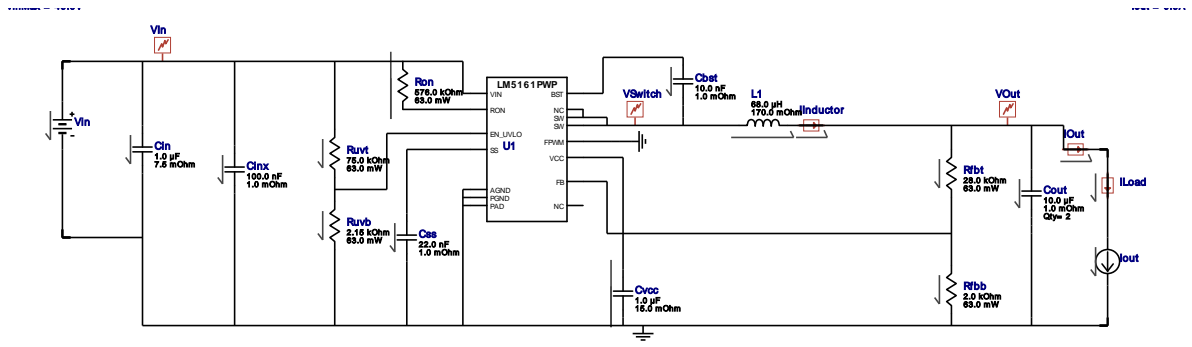
[picture p159: figure]
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
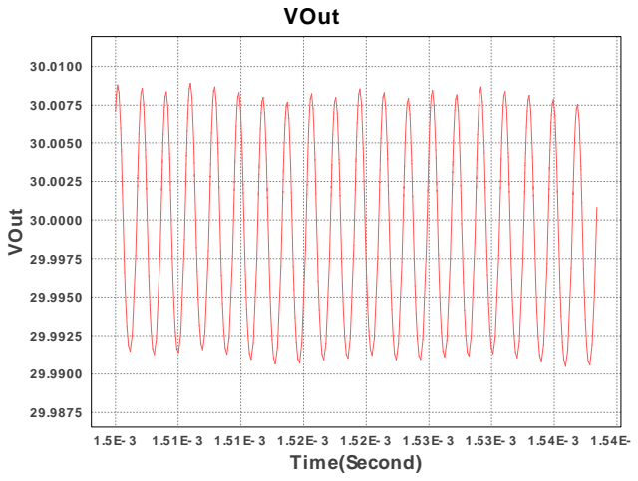
[picture p160: figure]
VOut

Copyright © 2020, Texas Instruments Incorporated | 8 | ti.com/webench

Design Id = 4
sim_id = 2
Simulation Type = Steady State

## Simulation Parameters

# Name Parameter Name | Description | Values

1. Css | IC | Initial Voltage | 1.96 V
2. L1 | IC | Initial Current | -0.9 A
3. Iout | I | Load Current | 0.9 A

1.5E- 3 1.51E- 3 1.51E- 3 1.52E- 3 1.52E- 3 1.53E- 3 1.53E- 3 1.54E- 3 1.54E- 3 Time(Second)

## Design Assistance

1. For a Constant On Time device to be stable, we need to provide a ripple at the feedback comparator. There are various methods to implement the ripple. Depending on the circuit complexity vs. the allowable ripple, we have three options to choose from. The simplest option, 'Low Complexity', would require only a high ESR cap at the output. This means that the BOM count will be small, but the output voltage ripple will be quite large. The 'Optimal Solution' would require a feed-forward cap in parallel with the upper feedback resistor to AC couple the ripple to the feedback node. This increases the BOM count slightly, but now we have more control over the output voltage ripple. If the output voltage requirement is very tight, then the best option is to go for the 'Low Output Ripple' solution. In this option we can go with very low ESR output caps and have very good control over the output voltage ripple.
2. Master key : 6306BADE0F5211DD[v1]
3. LM5161 Product Folder : http://www.ti.com/product/LM5161 : contains the data sheet and other resources.

Copyright © 2020, Texas Instruments Incorporated | 9 | ti.com/webench

Important Notice and Disclaimer

TI provides technical and reliability data (including datasheets), design resources (including reference designs), application or other design advice, web tools, safety information, and other resources AS IS and with all faults, and disclaims all warranties. These resources are intended for skilled developers designing with TI products. You are solely responsible for (1) selecting the appropriate TI products for your application, (2) designing, validating and testing your application, and (3) ensuring your application meets applicable standards, and any other safety, security, or other requirements.

These resources are subject to change without notice. TI grants you permission to use these resources only for development of an application that uses the TI products described in the resource. Other reproduction and display of these resources is prohibited. No license is granted to any other TI intellectual property right or to any third party intellectual property right. TI disclaims responsibility for, and you will fully indemnify TI and its representatives against, any claims, damages, costs, losses, and liabilities arising out of your use of these resources.

Providing these resources does not expand or otherwise alter TI's applicable Terms of Sale or other applicable terms available either on ti.com or provided in conjunction with TI products.
