gibbs212521/HEC_2_senior_design/LaTeX/simulations/48_5_DC.pdf

## WEBENCH ® Design Report

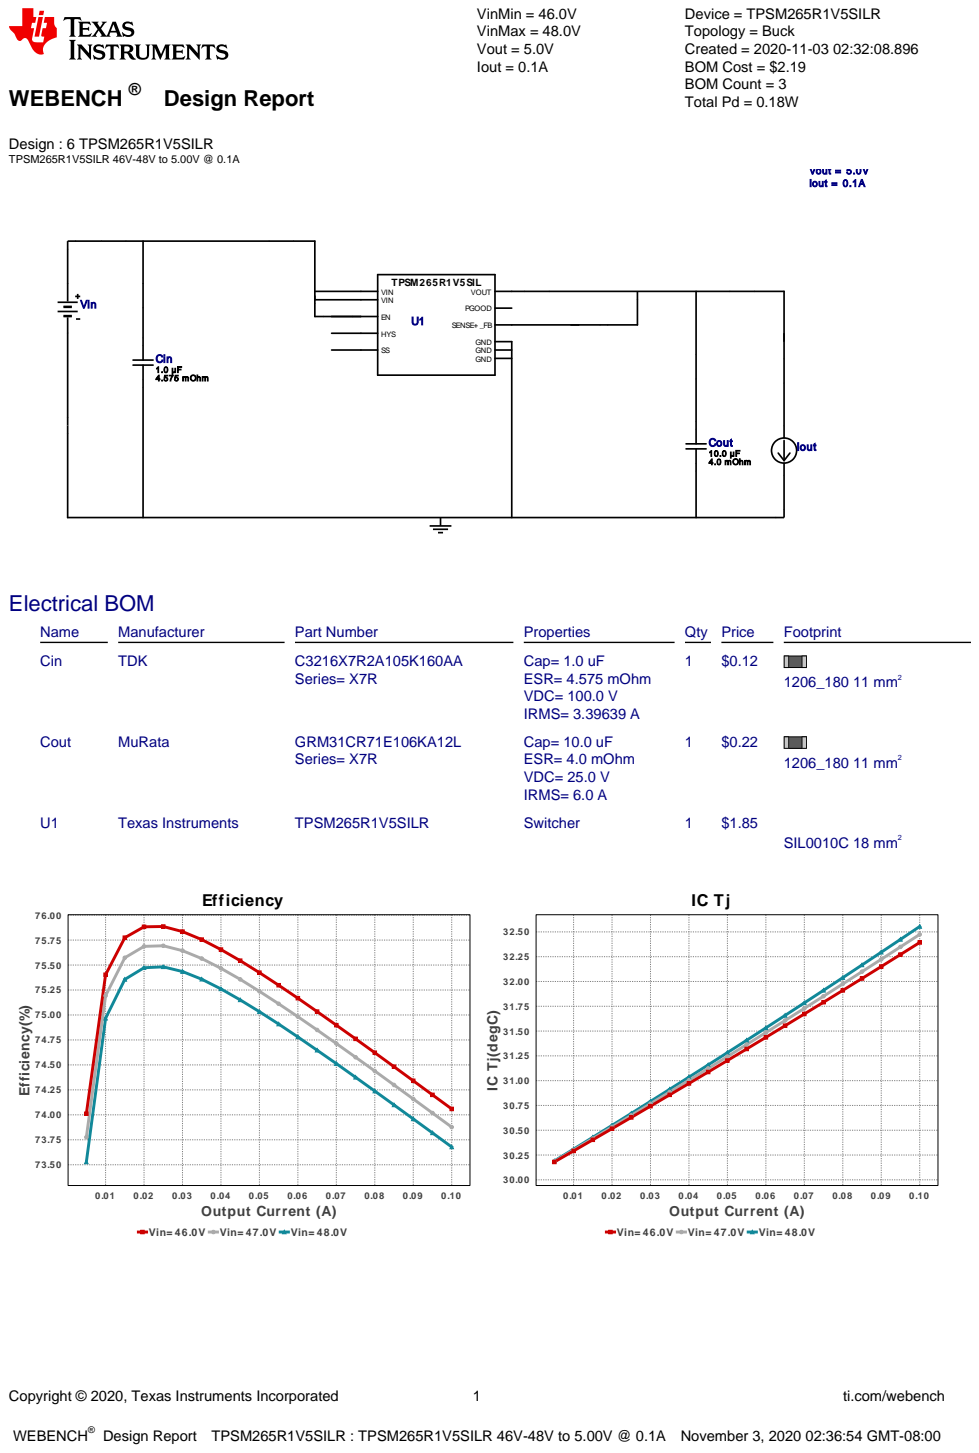
[picture p161: page 1]
Copyright © 2020, Texas Instruments Incorporated; ti.com/webench; WEBENCH®; Design : 6 TPSM265R1V5SILR TPSM265R1V5SILR 46V-48V to 5.00V @ 0.1A; VinMin = 46.0V VinMax = 48.0V Vout = 5.0V Iout = 0.1A; Device = TPSM265R1V5SILR Topology = Buck Created = 2020-11-03 02:32:08.896 BOM Cost = $2.19 BOM Count = 3 Total Pd = 0.18W; Cin 1.0 µF 4.575 mOhm; Vout = 5.0V Iout = 0.1A; TPSM265R1V5SIL VOUT; GND; VIN VIN; HYS; SENSE+ _FB; PGOOD; Cout 10.0 µF 4.0 mOhm; Iout; Vin; Electrical BOM; Name; Manufacturer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

IC Tj(degC)

Vin= 46.0V Vin= 47.0V Vin= 48.0V

Design Report TPSM265R1V5SILR : TPSM265R1V5SILR 46V-48V to 5.00V @ 0.1A November 3, 2020 02:36:54 GMT-08:00

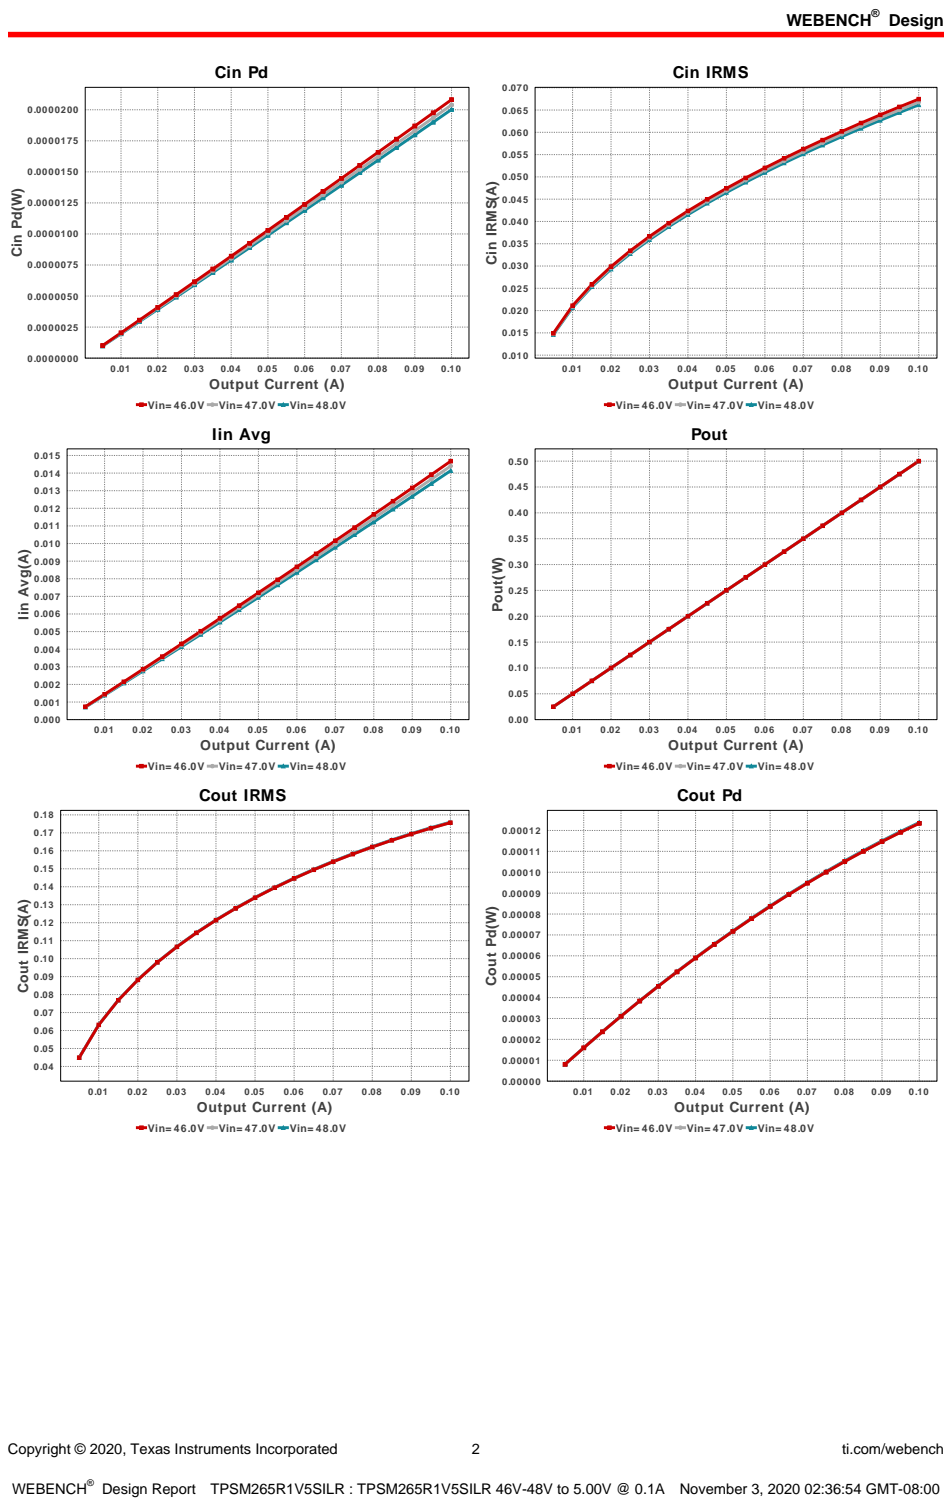
[picture p162: page 2]
Design; Copyright © 2020, Texas Instruments Incorporated; ti.com/webench; Cin Pd; 0.10 Output Current (A); Cin Pd(W); Cin IRMS; Cin IRMS(A); Iin Avg; Iin Avg(A); Pout; Pout(W); Cout IRMS(A); Cout Pd; Cout Pd(W)

Vin= 46.0V Vin= 47.0V Vin= 48.0V

Cout IRMS

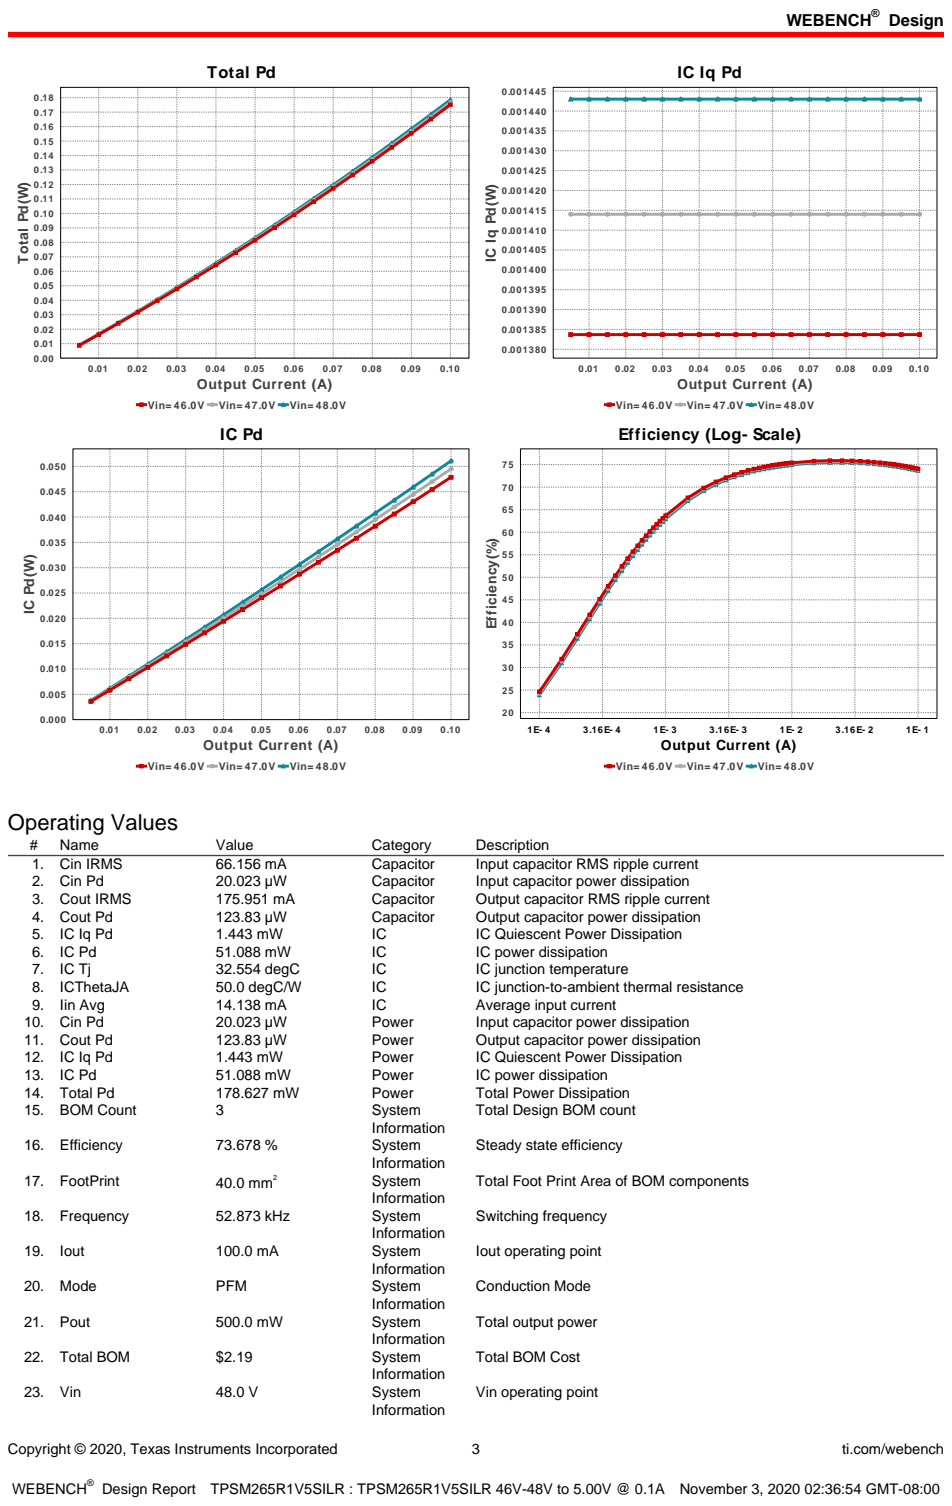
[picture p163: page 3]
Copyright © 2020, Texas Instruments Incorporated; ti.com/webench; Total Pd; 0.10 Output Current (A); Total Pd(W); 1E- 1 Output Current (A); Efficiency(%); Operating Values; Name; Value; Category; Description; 1. Cin IRMS; Capacitor; Input capacitor RMS ripple current; 2. Cin Pd; Input capacitor power dissipation; 3. Cout IRMS; Output capacitor RMS ripple current; 4. Cout Pd; Output capacitor power dissipation; IC Quiescent Power Dissipation; IC power dissipation; 32.554 degC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

Vin= 46.0V Vin= 47.0V Vin= 48.0V

Efficiency (Log- Scale)

Total Design BOM count

Steady state efficiency

Total Foot Print Area of BOM components

Iout operating point

Total output power

Total BOM Cost

Vin operating point

Copyright © 2020, Texas Instruments Incorporated | 4 | ti.com/webench
# | Name | Value | Category | Description

24. Vout | 5.0 V | System
| | | Information | Operational Output Voltage
25. Vout Tolerance | 2.0 % | System
| | | Information | Vout Tolerance based on IC Tolerance (no load) and voltage divider resistors if applicable

## Design Inputs

Name | Value | Description
| Iout | | 100.0 m | Maximum Output Current
VinMax | 48.0 | Maximum input voltage
VinMin | 46.0 | Minimum input voltage
Vout | 5.0 | Output Voltage
| base_pn | | TPSM265R1V5 | Base Product Number
source | DC | Input Source Type
Ta | 30.0 | Ambient temperature


Copyright © 2020, Texas Instruments Incorporated | 5 | ti.com/webench

## Assembly

## Component Testing

Some published data on components in datasheets such as Capacitor ESR and Inductor DC resistance is based on conservative values that will guarantee that the components always exceed the specification. For design purposes it is usually better to work with typical values. Since this data is not always available it is a good practice to measure the Capacitance and ESR values of Cin and Cout, and the inductance and DC resistance of L1 before assembly of the board. Any large discrepancies in values should be electrically simulated in WEBENCH to check for instabilities and thermally simulated in WebTHERM to make sure critical temperatures are not exceeded.

## Soldering Component to Board

If board assembly is done in house it is best to tack down one terminal of a component on the board then solder the other terminal. For surface mount parts with large tabs, such as the DPAK, the tab on the back of the package should be pre-tinned with solder, then tacked into place by one of the pins. To solder the tab town to the board place the iron down on the board while resting against the tab, heating both surfaces simultaneously. Apply light pressure to the top of the plastic case until the solder flows around the part and the part is flush with the PCB. If the solder is not flowing around the board you may need a higher wattage iron (generally 25W to 30W is enough).

## Initial Startup of Circuit

It is best to initially power up the board by setting the input supply voltage to the lowest operating input voltage 46.0V and set the input supply's current limit to zero. With the input supply off connect up the input supply to Vin and GND. Connect a digital volt meter and a load if needed to set the minimum Iout of the design from Vout and GND. Turn on the input supply and slowly turn up the current limit on the input supply.
If the voltage starts to rise on the input supply continue increasing the input supply current limit while watching the output voltage. If the current increases on the input supply, but the voltage remains near zero, then there may be a short or a component misplaced on the board. Power down the board and visually inspect for solder bridges and recheck the diode and capacitor polarities. Once the power supply circuit is operational then more extensive testing may include full load testing, transient load and line tests to compare with simulation results.

## Load Testing

The setup is the same as the initial startup, except that an additional digital voltmeter is connected between Vin and GND, a load is connected between Vout and GND and a current meter is connected in series between Vout and the load. The load must be able to handle at least rated output power + 50% ( 7.5 watts for this design). Ideally the load is supplied in the form of a variable load test unit. It can also be done in the form of suitably large power resistors. When using an oscilloscope to measure waveforms on the prototype board, the ground leads of the oscilloscope probes should be as short as possible and the area of the loop formed by the ground lead should be kept to a minimum. This will help reduce ground lead inductance and eliminate EMI noise that is not actually present in the circuit.

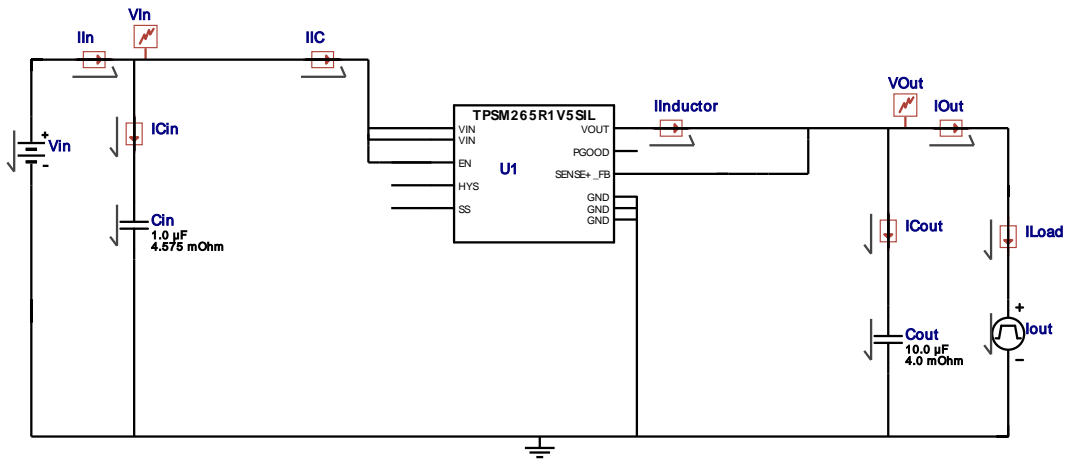
[picture p164: figure]
IOut; Cin 1.0 µF 4.575 mOhm; VOut; ICin; TPSM265R1V5SIL VOUT; GND; VIN VIN; HYS; SENSE+ _FB; PGOOD; IIn; Cout 10.0 µF 4.0 mOhm; IInductor; VIn; IIC; ICout; ILoad; Iout; Vin
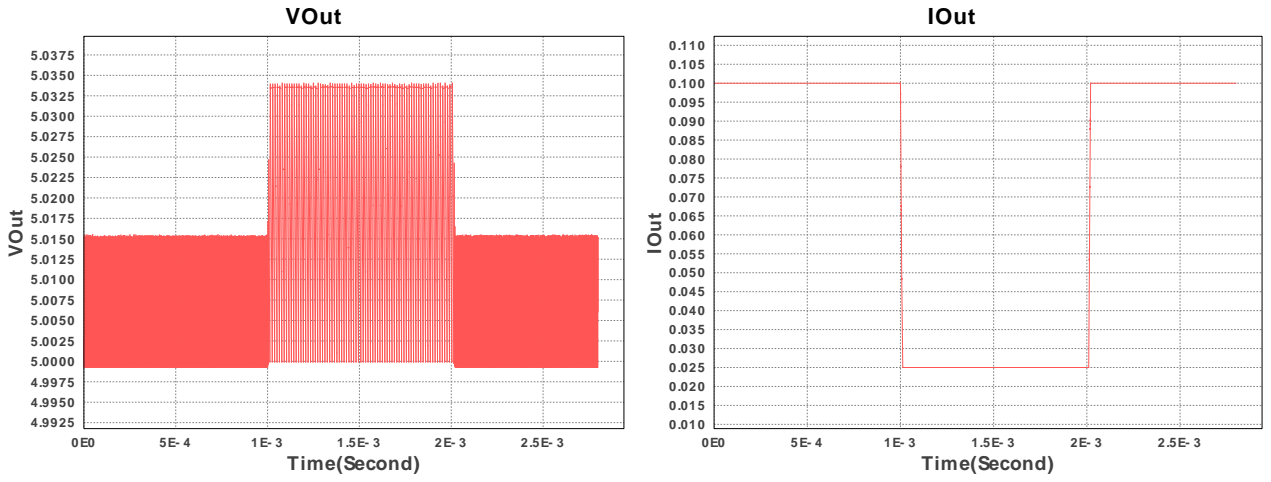
[picture p165: figure]
VOut; 2.5E- 3 Time(Second); IOut

Copyright © 2020, Texas Instruments Incorporated | 6 | ti.com/webench

## WEBENCH® Electrical Simulation Report

Design Id = 6
sim_id = 1
Simulation Type = Load Transient

## Simulation Parameters

# Name Parameter Name | Description | Values

1. Cout | IC | Initial Voltage | 5.0 V
2. Iout | signal_type | Signal Type | PULSE
| I1 | Initial Load Current | 0.1 A
| I2 | Minimum Load Current | 0.025 A
| Td | Initial Time Delay | 0.001 s
| Tf | Fall Time | 10u s
| Tr | Rise Time | 10u s
| Pw | Pulse Width | 0.001 s

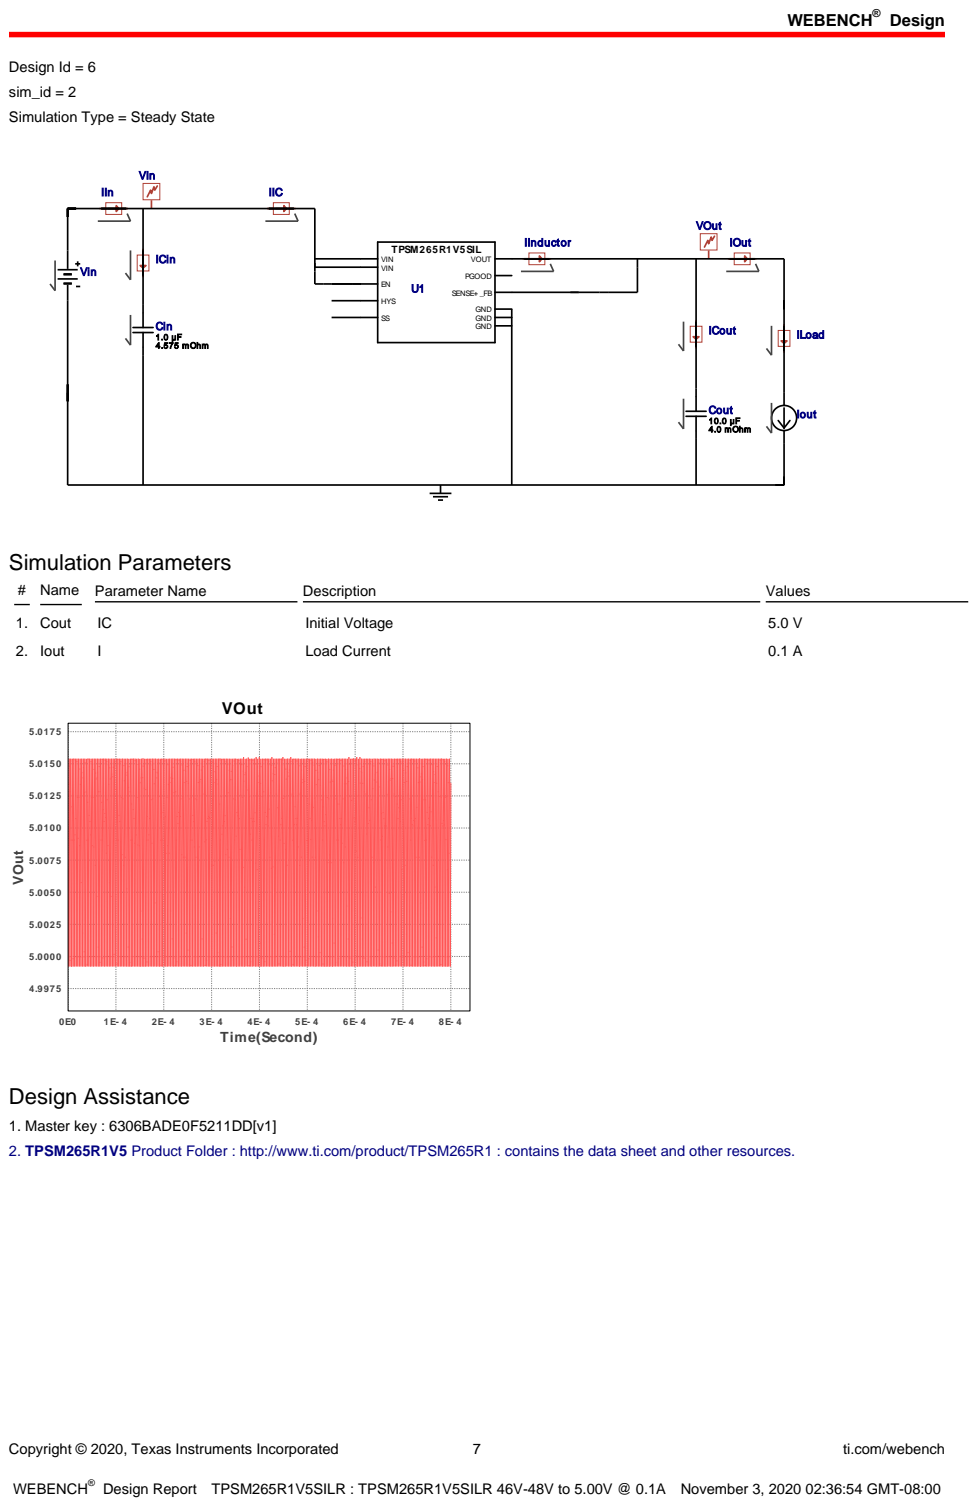
[picture p166: page 7]
Copyright © 2020, Texas Instruments Incorporated; ti.com/webench; IOut; Cin 1.0 µF 4.575 mOhm; VOut; ICin; TPSM265R1V5SIL VOUT; GND; VIN VIN; HYS; SENSE+ _FB; PGOOD; IIn; Cout 10.0 µF 4.0 mOhm; IInductor; VIn; IIC; ICout; ILoad; Iout; Vin; Simulation Parameters; # Name Parameter Name; Description; Values; 1. Cout; Initial Voltage; 2. Iout; Load Current; 8E- 4 Time(Second); Design Assistance

Design Id = 6
sim_id = 2
Simulation Type = Steady State

1. Master key : 6306BADE0F5211DD[v1]
2. TPSM265R1V5 Product Folder : http://www.ti.com/product/TPSM265R1 : contains the data sheet and other resources.

Copyright © 2020, Texas Instruments Incorporated | 8 | ti.com/webench

Important Notice and Disclaimer

TI provides technical and reliability data (including datasheets), design resources (including reference designs), application or other design advice, web tools, safety information, and other resources AS IS and with all faults, and disclaims all warranties. These resources are intended for skilled developers designing with TI products. You are solely responsible for (1) selecting the appropriate TI products for your application, (2) designing, validating and testing your application, and (3) ensuring your application meets applicable standards, and any other safety, security, or other requirements.

These resources are subject to change without notice. TI grants you permission to use these resources only for development of an application that uses the TI products described in the resource. Other reproduction and display of these resources is prohibited. No license is granted to any other TI intellectual property right or to any third party intellectual property right. TI disclaims responsibility for, and you will fully indemnify TI and its representatives against, any claims, damages, costs, losses, and liabilities arising out of your use of these resources.

Providing these resources does not expand or otherwise alter TI's applicable Terms of Sale or other applicable terms available either on ti.com or provided in conjunction with TI products.
