gibbs212521/HEC_2_senior_design/LaTeX/appendices/gantt_2_feb_mar.pdf

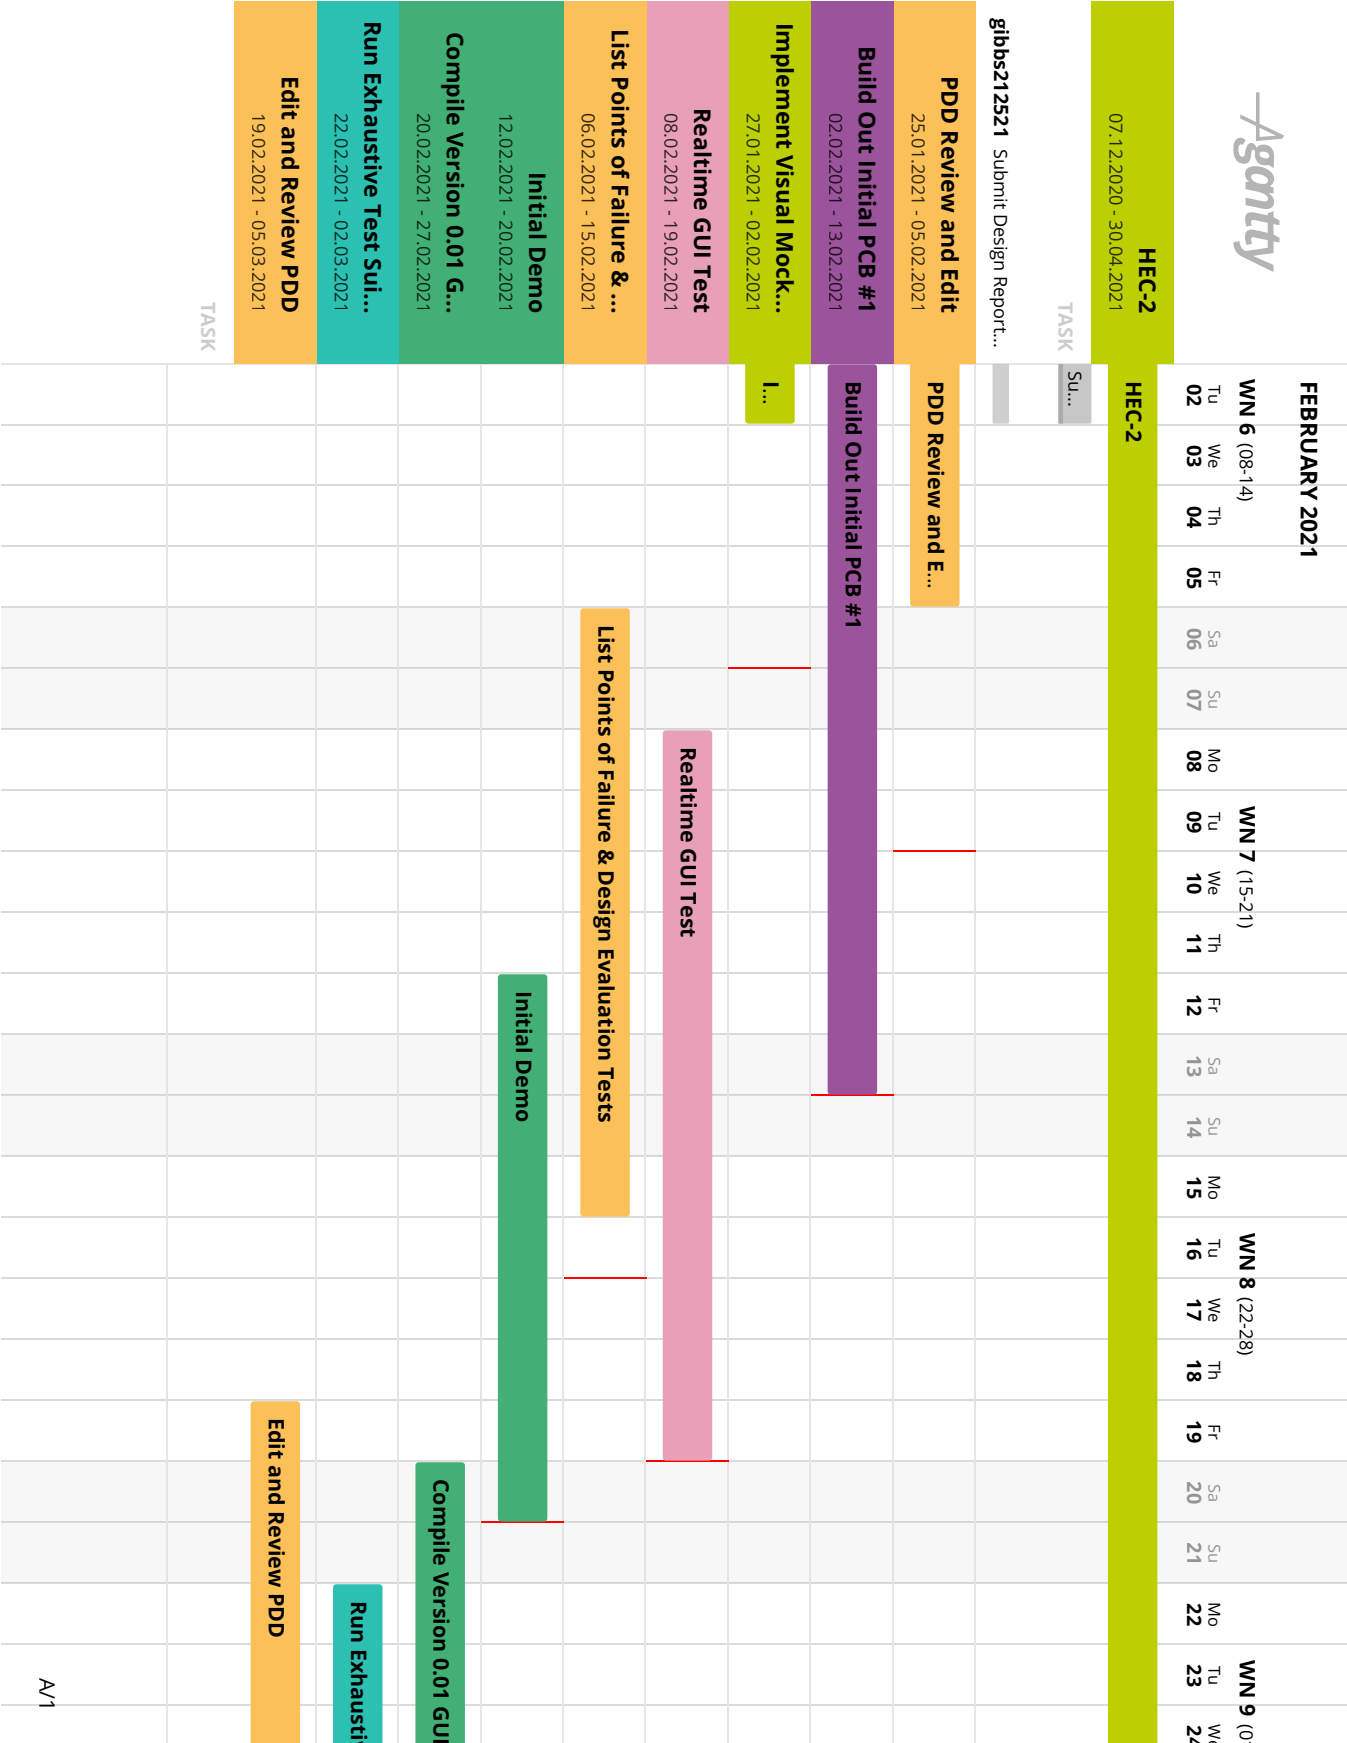
[picture p169: page 1]
gibbs212521; HEC-2; Initial Demo; Run Exhaustiv; FEBRUARY 2021

Submit Design Report... 07.12.2020 - 30.04.2021TASK PDD Review and Edit 25.01.2021 - 05.02.2021 Build Out Initial PCB #1 02.02.2021 - 13.02.2021 Implement Visual Mock... 08.02.2021 - 19.02.2021 Realtime GUI Test 27.01.2021 - 02.02.2021 List Points of Failure & ... 06.02.2021 - 15.02.2021 Initial Demo 12.02.2021 - 20.02.2021 Compile Version 0.01 G... 20.02.2021 - 27.02.2021 Run Exhaustive Test Sui... 22.02.2021 - 02.03.2021 Edit and Review PDD 19.02.2021 - 05.03.2021TASK

Su... ... Build Out Initial PCB #1 PDD Review and E ... I

List Points of Failure & Design Evaluation Tests

Realtime GUI Test

Edit and Review PDD

Compile Version 0.01 GUI

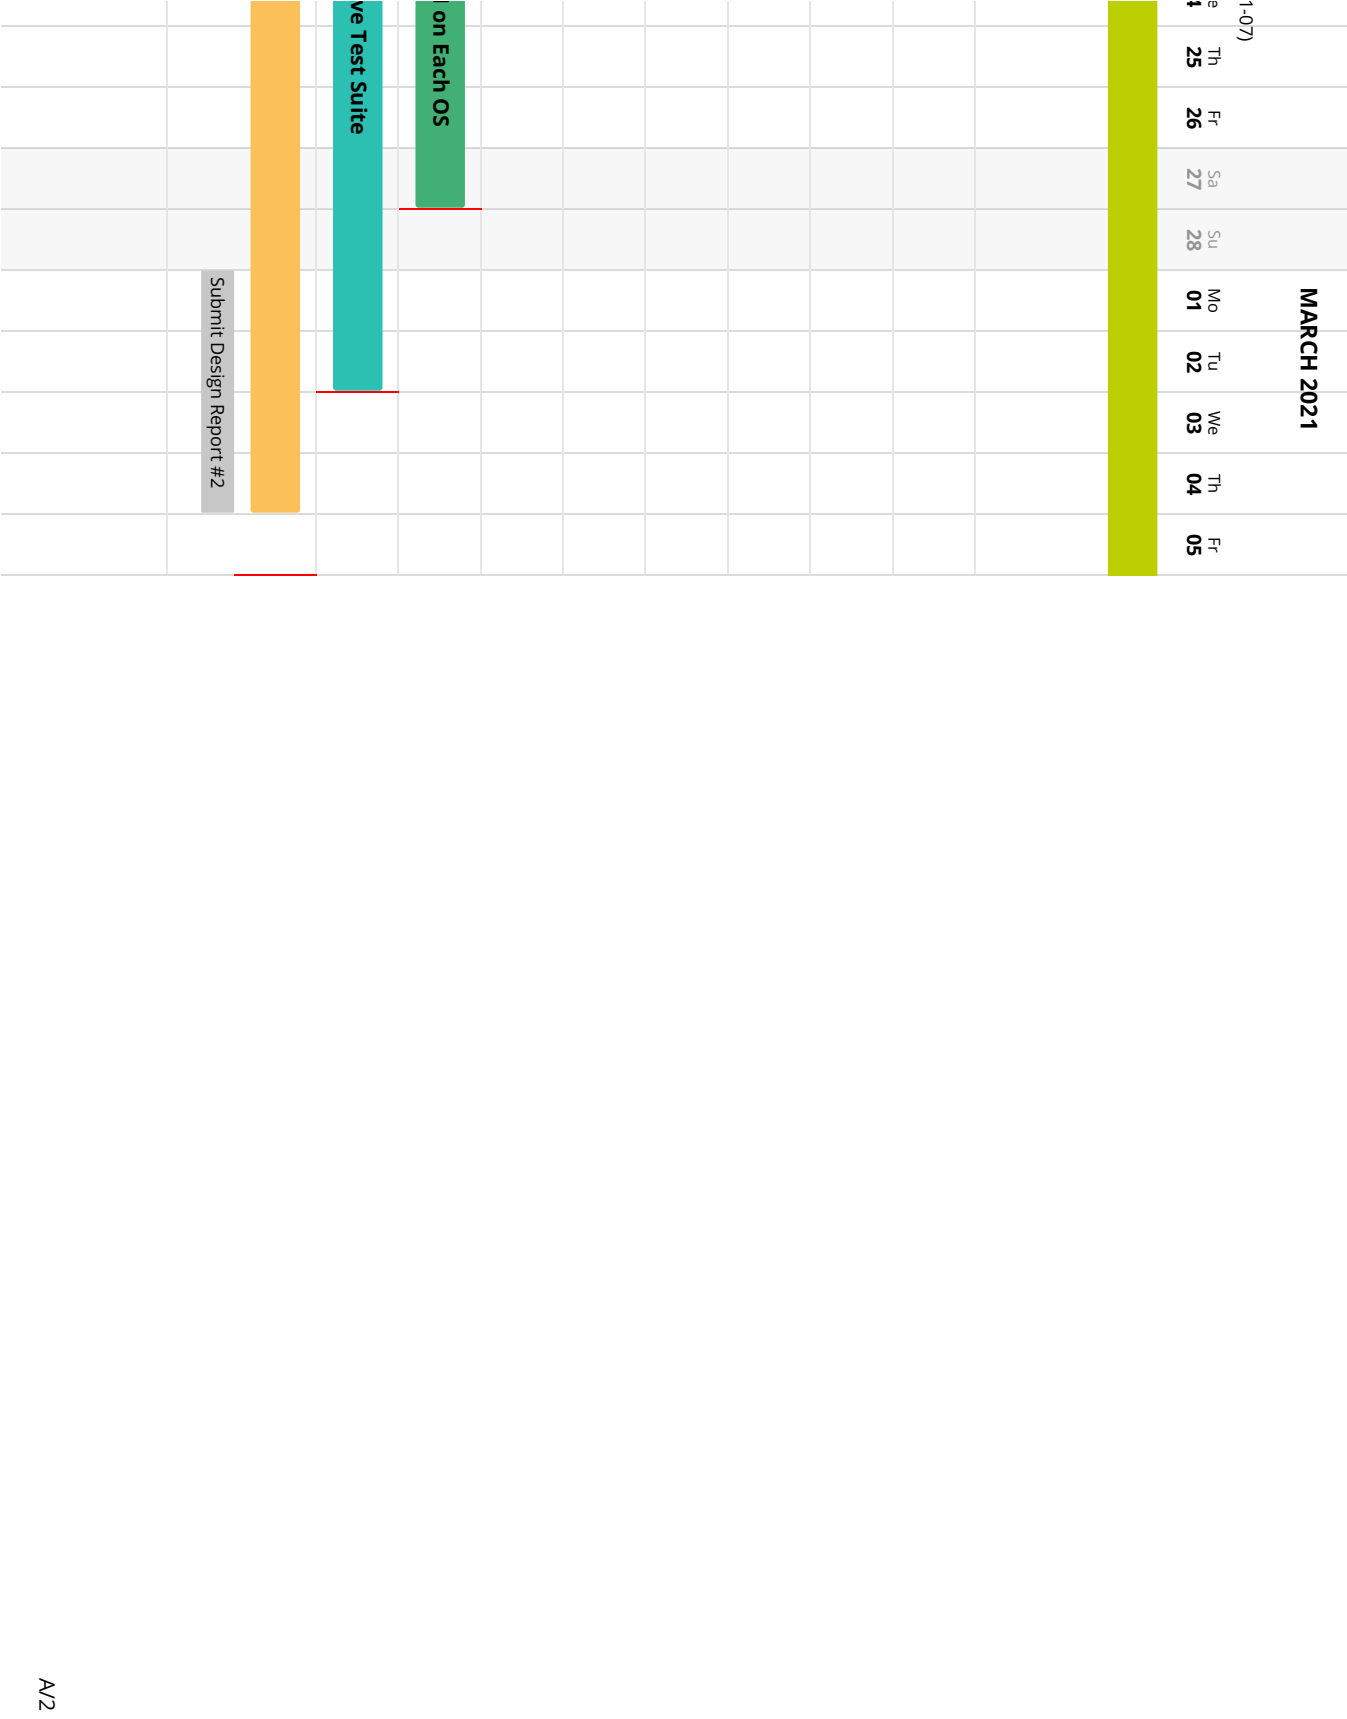
[picture p170: page 2]
MARCH 2021

ve Test Suite

I on Each OS

Submit Design Report #2
