gibbs212521/HEC_2_senior_design/docs/Firmware/LTC4162-LADM/c_code/common/LTC4162-LADM_reg_defs.h

/*!*****************************************************************************
*
* LTC4162: Advanced Synchronous Switching Battery Charger and PowerPath Manager
*
* @verbatim
* The LTC®4162-L is an advanced synchronous switching battery charger and
* PowerPath manager that seamlessly manages power distribution from input
* sources such as wall adapters, backplanes, solar panels, etc. and a
* rechargeable battery. A high resolution telemetry system provides extensive
* information on circuit voltages, currents, battery resistance and temperatures
* which can all be read back over the serial interface. The serial interface can
* also be used to configure many of the charging parameters including
* termination algorithms as well as numerous system status alerts. The LTC4162-L
* can charge Lithium-Ion cell stacks as high as eight cells with up to 3.2A of
* charge current. The power path topology decouples the output voltage from the
* battery allowing a portable product to start up under very low battery voltage
* conditions. The LTC4162-L is available in an I²C adjustable version as well as
* 4.0V, 4.1V and 4.2V fixed voltage versions all with and without MPPT enabled
* by default. The LTC4162-L is available in the 28-pin 4mm × 5mm × 0.75mm QFN
* surface mount package.
* @endverbatim
*
* http://www.linear.com/product/LTC4162
*
* http://www.linear.com/product/LTC4162#demoboards
*
* REVISION HISTORY
* $Revision$
* $Date: 2019-03-06 17:20:19 -0500 (Wed, 06 Mar 2019) $
*
* Copyright (c) 2019 Analog Devices, Inc.
*
* All rights reserved.
*
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
* The Linear Technology Linduino is not affiliated with the official Arduino
* team. However, the Linduino is only possible because of the Arduino team's
* commitment to the open-source community. Please, visit http://www.arduino.cc
* and http://store.arduino.cc, and consider a purchase that will help fund
* their ongoing work.
*
* Generated on: 2019-03-06
*
******************************************************************************/

/*! @file
 *  @ingroup LTC4162-LADM
 *  @brief LTC4162-LADM Register Map Definition Header
 *
 *
 *  This file contains LTC4162 definitions for each command_code as well as
 *  each individual bit field for the case when a register contains multiple
 *  bit-packed fields smaller than the register width.
 *
 *  Each bit field name is prepended with LTC4162_.
 *  Each bit field has individual definitions for its _SIZE, _OFFSET (LSB) and _MASK,
 *  as well as the three fields stored in a single 16-bit word for use with the access
 *  functions provided by LTC4162-LADM.c and LTC4162-LADM.h.
 *
 *  Additionally, each bit field contains a _DECODE macro to unpack multiple individual
 *  bit fields from a single copy of complete register data.
 *
 *  In the case that the bit field contents represent an enumeration, _ENUM
 *  definitions exist to translate from human readable format to the encoded value.
 *
 *  In the case that the bit field contents represent scalar data,
 *  macros exist in LTC4162_formats.h to translate from real units to integer values and back again.
 *  Real to integer conversions of literals should generally be optimized away at compile time
 *  without impact on execution speed or code size.
 *
 *  See @ref LTC4162-LADM_register_map for detailed descriptions of each bit field.
 *  See @ref LTC4162-LADM_formats for detailed descriptions of each data formatting macro.
 */

/*! @defgroup LTC4162-LADM_register_map LTC4162 Register Map Definitions
 *  @ingroup LTC4162-LADM
 */

#ifndef LTC4162_REG_DEFS_H_
#define LTC4162_REG_DEFS_H_

#define LTC4162_ADDR_68 0x68u //!<LTC4162 I2C address in 7-bit format

#define LTC4162_WORD_SIZE 16u

/*! @defgroup LTC4162_VBAT_LO_ALERT_LIMIT_REG VBAT_LO_ALERT_LIMIT_REG
 *  @ingroup LTC4162-LADM_register_map
 *  @brief VBAT_LO_ALERT_LIMIT_REG Register
 *
 * |                15:0 |
 * |:-------------------:|
 * | VBAT_LO_ALERT_LIMIT |
 *
 *   - CommandCode: 0x01
 *   - Contains Bit Fields:
 *     + @ref LTC4162_VBAT_LO_ALERT_LIMIT "VBAT_LO_ALERT_LIMIT" : Signed number that sets a lower limit that can be used to trigger an interrupt based on the per-cell battery voltage out of range. The value is based on the A/D value, vbat, which has a scaling factor of cell_count × 192.4µV/LSB. To compute the per-cell bit count, divide the desired trigger voltage by both cell_count and 192.4µV. The alert is enabled by setting en_vbat_lo_alert and can be read back and cleared at vbat_lo_alert.
*/

//!@{
#define LTC4162_VBAT_LO_ALERT_LIMIT_REG_SUBADDR 0x01u
#define LTC4162_VBAT_LO_ALERT_LIMIT_REG (0u << 12 | (LTC4162_WORD_SIZE - 1) << 8 | LTC4162_VBAT_LO_ALERT_LIMIT_REG_SUBADDR)
//!@}
/*! @defgroup LTC4162_VBAT_LO_ALERT_LIMIT VBAT_LO_ALERT_LIMIT
 *  @ingroup LTC4162-LADM_register_map
 *  @brief VBAT_LO_ALERT_LIMIT Bit Field
 *
 *  Signed number that sets a lower limit that can be used to trigger an interrupt based on the per-cell battery voltage out of range. The value is based on the A/D value, vbat, which has a scaling factor of cell_count × 192.4µV/LSB. To compute the per-cell bit count, divide the desired trigger voltage by both cell_count and 192.4µV. The alert is enabled by setting en_vbat_lo_alert and can be read back and cleared at vbat_lo_alert.
 *   - Register: @ref LTC4162_VBAT_LO_ALERT_LIMIT_REG "VBAT_LO_ALERT_LIMIT_REG"
 *   - CommandCode: 0x01
 *   - Size: 16
 *   - Offset: 0
 *   - MSB: 15
 *   - MASK: 0xFFFF
 *   - Access: R/W
 *   - Default: 0
 *   - Format: LTC4162_VBAT_FORMAT
 */
//!@{
#define LTC4162_VBAT_LO_ALERT_LIMIT_SUBADDR LTC4162_VBAT_LO_ALERT_LIMIT_REG_SUBADDR //!< @ref LTC4162_VBAT_LO_ALERT_LIMIT "VBAT_LO_ALERT_LIMIT"
#define LTC4162_VBAT_LO_ALERT_LIMIT_SIZE 16u
#define LTC4162_VBAT_LO_ALERT_LIMIT_OFFSET 0u
#define LTC4162_VBAT_LO_ALERT_LIMIT_MASK 0xFFFFu
#define LTC4162_VBAT_LO_ALERT_LIMIT_DEFAULT 0u
#define LTC4162_VBAT_LO_ALERT_LIMIT_DECODE(register_data) (register_data)
#define LTC4162_VBAT_LO_ALERT_LIMIT (LTC4162_VBAT_LO_ALERT_LIMIT_OFFSET << 12 | (LTC4162_VBAT_LO_ALERT_LIMIT_SIZE - 1) << 8 | LTC4162_VBAT_LO_ALERT_LIMIT_SUBADDR)
//!@}

/*! @defgroup LTC4162_VBAT_HI_ALERT_LIMIT_REG VBAT_HI_ALERT_LIMIT_REG
 *  @ingroup LTC4162-LADM_register_map
 *  @brief VBAT_HI_ALERT_LIMIT_REG Register
 *
 * |                15:0 |
 * |:-------------------:|
 * | VBAT_HI_ALERT_LIMIT |
 *
 *   - CommandCode: 0x02
 *   - Contains Bit Fields:
 *     + @ref LTC4162_VBAT_HI_ALERT_LIMIT "VBAT_HI_ALERT_LIMIT" : Signed number that sets an upper limit that can be used to trigger an interrupt based on the per-cell battery voltage out of range. The value is based on the A/D value, vbat, which has a scaling factor of cell_count × 192.4µV/LSB. To compute the per-cell bit count, divide the desired trigger voltage by both cell_count and 192.4µV. The alert is enabled by setting en_vbat_hi_alert and can be read back and cleared at vbat_hi_alert.
*/

//!@{
#define LTC4162_VBAT_HI_ALERT_LIMIT_REG_SUBADDR 0x02u
#define LTC4162_VBAT_HI_ALERT_LIMIT_REG (0u << 12 | (LTC4162_WORD_SIZE - 1) << 8 | LTC4162_VBAT_HI_ALERT_LIMIT_REG_SUBADDR)
//!@}
/*! @defgroup LTC4162_VBAT_HI_ALERT_LIMIT VBAT_HI_ALERT_LIMIT
 *  @ingroup LTC4162-LADM_register_map
 *  @brief VBAT_HI_ALERT_LIMIT Bit Field
 *
 *  Signed number that sets an upper limit that can be used to trigger an interrupt based on the per-cell battery voltage out of range. The value is based on the A/D value, vbat, which has a scaling factor of cell_count × 192.4µV/LSB. To compute the per-cell bit count, divide the desired trigger voltage by both cell_count and 192.4µV. The alert is enabled by setting en_vbat_hi_alert and can be read back and cleared at vbat_hi_alert.
 *   - Register: @ref LTC4162_VBAT_HI_ALERT_LIMIT_REG "VBAT_HI_ALERT_LIMIT_REG"
 *   - CommandCode: 0x02
 *   - Size: 16
 *   - Offset: 0
 *   - MSB: 15
 *   - MASK: 0xFFFF
 *   - Access: R/W
 *   - Default: 0
 *   - Format: LTC4162_VBAT_FORMAT
 */
//!@{
#define LTC4162_VBAT_HI_ALERT_LIMIT_SUBADDR LTC4162_VBAT_HI_ALERT_LIMIT_REG_SUBADDR //!< @ref LTC4162_VBAT_HI_ALERT_LIMIT "VBAT_HI_ALERT_LIMIT"
#define LTC4162_VBAT_HI_ALERT_LIMIT_SIZE 16u
#define LTC4162_VBAT_HI_ALERT_LIMIT_OFFSET 0u
#define LTC4162_VBAT_HI_ALERT_LIMIT_MASK 0xFFFFu
#define LTC4162_VBAT_HI_ALERT_LIMIT_DEFAULT 0u
#define LTC4162_VBAT_HI_ALERT_LIMIT_DECODE(register_data) (register_data)
#define LTC4162_VBAT_HI_ALERT_LIMIT (LTC4162_VBAT_HI_ALERT_LIMIT_OFFSET << 12 | (LTC4162_VBAT_HI_ALERT_LIMIT_SIZE - 1) << 8 | LTC4162_VBAT_HI_ALERT_LIMIT_SUBADDR)
//!@}

/*! @defgroup LTC4162_VIN_LO_ALERT_LIMIT_REG VIN_LO_ALERT_LIMIT_REG
 *  @ingroup LTC4162-LADM_register_map
 *  @brief VIN_LO_ALERT_LIMIT_REG Register
 *
 * |               15:0 |
 * |:------------------:|
 * | VIN_LO_ALERT_LIMIT |
 *
 *   - CommandCode: 0x03
 *   - Contains Bit Fields:
 *     + @ref LTC4162_VIN_LO_ALERT_LIMIT "VIN_LO_ALERT_LIMIT" : Signed number that sets a lower limit that can be used to trigger an interrupt based on input voltage out of range. The value is based on the A/D value, vin, which has a scaling factor of 1.649mV/LSB. The alert is enabled by setting en_vin_lo_alert and can be read back and cleared at vin_lo_alert.
*/

//!@{
#define LTC4162_VIN_LO_ALERT_LIMIT_REG_SUBADDR 0x03u
#define LTC4162_VIN_LO_ALERT_LIMIT_REG (0u << 12 | (LTC4162_WORD_SIZE - 1) << 8 | LTC4162_VIN_LO_ALERT_LIMIT_REG_SUBADDR)
//!@}
/*! @defgroup LTC4162_VIN_LO_ALERT_LIMIT VIN_LO_ALERT_LIMIT
 *  @ingroup LTC4162-LADM_register_map
 *  @brief VIN_LO_ALERT_LIMIT Bit Field
 *
 *  Signed number that sets a lower limit that can be used to trigger an interrupt based on input voltage out of range. The value is based on the A/D value, vin, which has a scaling factor of 1.649mV/LSB. The alert is enabled by setting en_vin_lo_alert and can be read back and cleared at vin_lo_alert.
 *   - Register: @ref LTC4162_VIN_LO_ALERT_LIMIT_REG "VIN_LO_ALERT_LIMIT_REG"
 *   - CommandCode: 0x03
 *   - Size: 16
 *   - Offset: 0
 *   - MSB: 15
 *   - MASK: 0xFFFF
 *   - Access: R/W
 *   - Default: 0
 *   - Format: LTC4162_VIN_FORMAT
 */
//!@{
#define LTC4162_VIN_LO_ALERT_LIMIT_SUBADDR LTC4162_VIN_LO_ALERT_LIMIT_REG_SUBADDR //!< @ref LTC4162_VIN_LO_ALERT_LIMIT "VIN_LO_ALERT_LIMIT"
#define LTC4162_VIN_LO_ALERT_LIMIT_SIZE 16u
#define LTC4162_VIN_LO_ALERT_LIMIT_OFFSET 0u
#define LTC4162_VIN_LO_ALERT_LIMIT_MASK 0xFFFFu
#define LTC4162_VIN_LO_ALERT_LIMIT_DEFAULT 0u
#define LTC4162_VIN_LO_ALERT_LIMIT_DECODE(register_data) (register_data)
#define LTC4162_VIN_LO_ALERT_LIMIT (LTC4162_VIN_LO_ALERT_LIMIT_OFFSET << 12 | (LTC4162_VIN_LO_ALERT_LIMIT_SIZE - 1) << 8 | LTC4162_VIN_LO_ALERT_LIMIT_SUBADDR)
//!@}

/*! @defgroup LTC4162_VIN_HI_ALERT_LIMIT_REG VIN_HI_ALERT_LIMIT_REG
 *  @ingroup LTC4162-LADM_register_map
 *  @brief VIN_HI_ALERT_LIMIT_REG Register
 *
 * |               15:0 |
 * |:------------------:|
 * | VIN_HI_ALERT_LIMIT |
 *
 *   - CommandCode: 0x04
 *   - Contains Bit Fields:
 *     + @ref LTC4162_VIN_HI_ALERT_LIMIT "VIN_HI_ALERT_LIMIT" : Signed number that sets an upper limit that can be used to trigger an interrupt based on input voltage out of range. The value is based on the A/D value, vin, which has a scaling factor of 1.649mV/LSB. The alert is enabled by setting en_vin_hi_alert and can be read back and cleared at vin_hi_alert.
*/

//!@{
#define LTC4162_VIN_HI_ALERT_LIMIT_REG_SUBADDR 0x04u
#define LTC4162_VIN_HI_ALERT_LIMIT_REG (0u << 12 | (LTC4162_WORD_SIZE - 1) << 8 | LTC4162_VIN_HI_ALERT_LIMIT_REG_SUBADDR)
//!@}
/*! @defgroup LTC4162_VIN_HI_ALERT_LIMIT VIN_HI_ALERT_LIMIT
 *  @ingroup LTC4162-LADM_register_map
 *  @brief VIN_HI_ALERT_LIMIT Bit Field
 *
 *  Signed number that sets an upper limit that can be used to trigger an interrupt based on input voltage out of range. The value is based on the A/D value, vin, which has a scaling factor of 1.649mV/LSB. The alert is enabled by setting en_vin_hi_alert and can be read back and cleared at vin_hi_alert.
 *   - Register: @ref LTC4162_VIN_HI_ALERT_LIMIT_REG "VIN_HI_ALERT_LIMIT_REG"
 *   - CommandCode: 0x04
 *   - Size: 16
 *   - Offset: 0
 *   - MSB: 15
 *   - MASK: 0xFFFF
 *   - Access: R/W
 *   - Default: 0
 *   - Format: LTC4162_VIN_FORMAT
 */
//!@{
#define LTC4162_VIN_HI_ALERT_LIMIT_SUBADDR LTC4162_VIN_HI_ALERT_LIMIT_REG_SUBADDR //!< @ref LTC4162_VIN_HI_ALERT_LIMIT "VIN_HI_ALERT_LIMIT"
#define LTC4162_VIN_HI_ALERT_LIMIT_SIZE 16u
#define LTC4162_VIN_HI_ALERT_LIMIT_OFFSET 0u
#define LTC4162_VIN_HI_ALERT_LIMIT_MASK 0xFFFFu
#define LTC4162_VIN_HI_ALERT_LIMIT_DEFAULT 0u
#define LTC4162_VIN_HI_ALERT_LIMIT_DECODE(register_data) (register_data)
#define LTC4162_VIN_HI_ALERT_LIMIT (LTC4162_VIN_HI_ALERT_LIMIT_OFFSET << 12 | (LTC4162_VIN_HI_ALERT_LIMIT_SIZE - 1) << 8 | LTC4162_VIN_HI_ALERT_LIMIT_SUBADDR)
//!@}

/*! @defgroup LTC4162_VOUT_LO_ALERT_LIMIT_REG VOUT_LO_ALERT_LIMIT_REG
 *  @ingroup LTC4162-LADM_register_map
 *  @brief VOUT_LO_ALERT_LIMIT_REG Register
 *
 * |                15:0 |
 * |:-------------------:|
 * | VOUT_LO_ALERT_LIMIT |
 *
 *   - CommandCode: 0x05
 *   - Contains Bit Fields:
 *     + @ref LTC4162_VOUT_LO_ALERT_LIMIT "VOUT_LO_ALERT_LIMIT" : Signed number that sets a lower limit that can be used to trigger an interrupt based on vout voltage out of range. The value is based on the A/D value, vout, which has a scaling factor of 1.653mV/LSB. The alert is enabled by setting en_vout_lo_alert and can be read back and cleared at vout_lo_alert.
*/

//!@{
#define LTC4162_VOUT_LO_ALERT_LIMIT_REG_SUBADDR 0x05u
#define LTC4162_VOUT_LO_ALERT_LIMIT_REG (0u << 12 | (LTC4162_WORD_SIZE - 1) << 8 | LTC4162_VOUT_LO_ALERT_LIMIT_REG_SUBADDR)
//!@}
/*! @defgroup LTC4162_VOUT_LO_ALERT_LIMIT VOUT_LO_ALERT_LIMIT
 *  @ingroup LTC4162-LADM_register_map
 *  @brief VOUT_LO_ALERT_LIMIT Bit Field
 *
 *  Signed number that sets a lower limit that can be used to trigger an interrupt based on vout voltage out of range. The value is based on the A/D value, vout, which has a scaling factor of 1.653mV/LSB. The alert is enabled by setting en_vout_lo_alert and can be read back and cleared at vout_lo_alert.
 *   - Register: @ref LTC4162_VOUT_LO_ALERT_LIMIT_REG "VOUT_LO_ALERT_LIMIT_REG"
 *   - CommandCode: 0x05
 *   - Size: 16
 *   - Offset: 0
 *   - MSB: 15
 *   - MASK: 0xFFFF
 *   - Access: R/W
 *   - Default: 0
 *   - Format: LTC4162_VOUT_FORMAT
 */
//!@{
#define LTC4162_VOUT_LO_ALERT_LIMIT_SUBADDR LTC4162_VOUT_LO_ALERT_LIMIT_REG_SUBADDR //!< @ref LTC4162_VOUT_LO_ALERT_LIMIT "VOUT_LO_ALERT_LIMIT"
#define LTC4162_VOUT_LO_ALERT_LIMIT_SIZE 16u
#define LTC4162_VOUT_LO_ALERT_LIMIT_OFFSET 0u
#define LTC4162_VOUT_LO_ALERT_LIMIT_MASK 0xFFFFu
#define LTC4162_VOUT_LO_ALERT_LIMIT_DEFAULT 0u
#define LTC4162_VOUT_LO_ALERT_LIMIT_DECODE(register_data) (register_data)
#define LTC4162_VOUT_LO_ALERT_LIMIT (LTC4162_VOUT_LO_ALERT_LIMIT_OFFSET << 12 | (LTC4162_VOUT_LO_ALERT_LIMIT_SIZE - 1) << 8 | LTC4162_VOUT_LO_ALERT_LIMIT_SUBADDR)
//!@}

/*! @defgroup LTC4162_VOUT_HI_ALERT_LIMIT_REG VOUT_HI_ALERT_LIMIT_REG
 *  @ingroup LTC4162-LADM_register_map
 *  @brief VOUT_HI_ALERT_LIMIT_REG Register
 *
 * |                15:0 |
 * |:-------------------:|
 * | VOUT_HI_ALERT_LIMIT |
 *
 *   - CommandCode: 0x06
 *   - Contains Bit Fields:
 *     + @ref LTC4162_VOUT_HI_ALERT_LIMIT "VOUT_HI_ALERT_LIMIT" : Signed number that sets an upper limit that can be used to trigger an interrupt based on vout voltage out of range. The value is based on the A/D value, vout, which has a scaling factor of 1.653mV/LSB. The alert is enabled by setting en_vout_hi_alert and can be read back and cleared at vout_hi_alert.
*/

//!@{
#define LTC4162_VOUT_HI_ALERT_LIMIT_REG_SUBADDR 0x06u
#define LTC4162_VOUT_HI_ALERT_LIMIT_REG (0u << 12 | (LTC4162_WORD_SIZE - 1) << 8 | LTC4162_VOUT_HI_ALERT_LIMIT_REG_SUBADDR)
//!@}
/*! @defgroup LTC4162_VOUT_HI_ALERT_LIMIT VOUT_HI_ALERT_LIMIT
 *  @ingroup LTC4162-LADM_register_map
 *  @brief VOUT_HI_ALERT_LIMIT Bit Field
 *
 *  Signed number that sets an upper limit that can be used to trigger an interrupt based on vout voltage out of range. The value is based on the A/D value, vout, which has a scaling factor of 1.653mV/LSB. The alert is enabled by setting en_vout_hi_alert and can be read back and cleared at vout_hi_alert.
 *   - Register: @ref LTC4162_VOUT_HI_ALERT_LIMIT_REG "VOUT_HI_ALERT_LIMIT_REG"
 *   - CommandCode: 0x06
 *   - Size: 16
 *   - Offset: 0
 *   - MSB: 15
 *   - MASK: 0xFFFF
 *   - Access: R/W
 *   - Default: 0
 *   - Format: LTC4162_VOUT_FORMAT
 */
//!@{
#define LTC4162_VOUT_HI_ALERT_LIMIT_SUBADDR LTC4162_VOUT_HI_ALERT_LIMIT_REG_SUBADDR //!< @ref LTC4162_VOUT_HI_ALERT_LIMIT "VOUT_HI_ALERT_LIMIT"
#define LTC4162_VOUT_HI_ALERT_LIMIT_SIZE 16u
#define LTC4162_VOUT_HI_ALERT_LIMIT_OFFSET 0u
#define LTC4162_VOUT_HI_ALERT_LIMIT_MASK 0xFFFFu
#define LTC4162_VOUT_HI_ALERT_LIMIT_DEFAULT 0u
#define LTC4162_VOUT_HI_ALERT_LIMIT_DECODE(register_data) (register_data)
#define LTC4162_VOUT_HI_ALERT_LIMIT (LTC4162_VOUT_HI_ALERT_LIMIT_OFFSET << 12 | (LTC4162_VOUT_HI_ALERT_LIMIT_SIZE - 1) << 8 | LTC4162_VOUT_HI_ALERT_LIMIT_SUBADDR)
//!@}

/*! @defgroup LTC4162_IIN_HI_ALERT_LIMIT_REG IIN_HI_ALERT_LIMIT_REG
 *  @ingroup LTC4162-LADM_register_map
 *  @brief IIN_HI_ALERT_LIMIT_REG Register
 *
 * |               15:0 |
 * |:------------------:|
 * | IIN_HI_ALERT_LIMIT |
 *
 *   - CommandCode: 0x07
 *   - Contains Bit Fields:
 *     + @ref LTC4162_IIN_HI_ALERT_LIMIT "IIN_HI_ALERT_LIMIT" : Signed number that sets an upper limit that can be used to trigger an interrupt based on input current out of range. The value is based on the A/D value, iin, which has a scaling factor of 1.466µV / RSNSI amperes/LSB. The alert is enabled by setting en_iin_hi_alert and can be read back and cleared at iin_hi_alert.
*/

//!@{
#define LTC4162_IIN_HI_ALERT_LIMIT_REG_SUBADDR 0x07u
#define LTC4162_IIN_HI_ALERT_LIMIT_REG (0u << 12 | (LTC4162_WORD_SIZE - 1) << 8 | LTC4162_IIN_HI_ALERT_LIMIT_REG_SUBADDR)
//!@}
/*! @defgroup LTC4162_IIN_HI_ALERT_LIMIT IIN_HI_ALERT_LIMIT
 *  @ingroup LTC4162-LADM_register_map
 *  @brief IIN_HI_ALERT_LIMIT Bit Field
 *
 *  Signed number that sets an upper limit that can be used to trigger an interrupt based on input current out of range. The value is based on the A/D value, iin, which has a scaling factor of 1.466µV / RSNSI amperes/LSB. The alert is enabled by setting en_iin_hi_alert and can be read back and cleared at iin_hi_alert.
 *   - Register: @ref LTC4162_IIN_HI_ALERT_LIMIT_REG "IIN_HI_ALERT_LIMIT_REG"
 *   - CommandCode: 0x07
 *   - Size: 16
 *   - Offset: 0
 *   - MSB: 15
 *   - MASK: 0xFFFF
 *   - Access: R/W
 *   - Default: 0
 *   - Format: LTC4162_IIN_FORMAT
 */
//!@{
#define LTC4162_IIN_HI_ALERT_LIMIT_SUBADDR LTC4162_IIN_HI_ALERT_LIMIT_REG_SUBADDR //!< @ref LTC4162_IIN_HI_ALERT_LIMIT "IIN_HI_ALERT_LIMIT"
#define LTC4162_IIN_HI_ALERT_LIMIT_SIZE 16u
#define LTC4162_IIN_HI_ALERT_LIMIT_OFFSET 0u
#define LTC4162_IIN_HI_ALERT_LIMIT_MASK 0xFFFFu
#define LTC4162_IIN_HI_ALERT_LIMIT_DEFAULT 0u
#define LTC4162_IIN_HI_ALERT_LIMIT_DECODE(register_data) (register_data)
#define LTC4162_IIN_HI_ALERT_LIMIT (LTC4162_IIN_HI_ALERT_LIMIT_OFFSET << 12 | (LTC4162_IIN_HI_ALERT_LIMIT_SIZE - 1) << 8 | LTC4162_IIN_HI_ALERT_LIMIT_SUBADDR)
//!@}

/*! @defgroup LTC4162_IBAT_LO_ALERT_LIMIT_REG IBAT_LO_ALERT_LIMIT_REG
 *  @ingroup LTC4162-LADM_register_map
 *  @brief IBAT_LO_ALERT_LIMIT_REG Register
 *
 * |                15:0 |
 * |:-------------------:|
 * | IBAT_LO_ALERT_LIMIT |
 *
 *   - CommandCode: 0x08
 *   - Contains Bit Fields:
 *     + @ref LTC4162_IBAT_LO_ALERT_LIMIT "IBAT_LO_ALERT_LIMIT" : Signed number that sets a lower limit that can be used to trigger an interrupt based on charge current dropping below a particular value, such as during the constant-voltage phase of charging, or, load current exceeding a particular limit when not charging. When the charger is not running, and telemetry is enabled with force_telemetry_on, this limit indicates that the battery draw has exceeded a particular value. Telemetry will be enabled automatically if the input voltage exceeds the battery voltage, in which case discharge current will be nearly zero. ibat values are positive for charging and negative for discharging so the polarity of this register should be set according to the mode in which the limit alert is of interest. The value is based on the A/D value, ibat, which has a scaling factor of 1.466µV / RSNSB amperes/LSB. The alert is enabled by setting en_ibat_lo_alert and can be read back and cleared at ibat_lo_alert.
*/

//!@{
#define LTC4162_IBAT_LO_ALERT_LIMIT_REG_SUBADDR 0x08u
#define LTC4162_IBAT_LO_ALERT_LIMIT_REG (0u << 12 | (LTC4162_WORD_SIZE - 1) << 8 | LTC4162_IBAT_LO_ALERT_LIMIT_REG_SUBADDR)
//!@}
/*! @defgroup LTC4162_IBAT_LO_ALERT_LIMIT IBAT_LO_ALERT_LIMIT
 *  @ingroup LTC4162-LADM_register_map
 *  @brief IBAT_LO_ALERT_LIMIT Bit Field
 *
 *  Signed number that sets a lower limit that can be used to trigger an interrupt based on charge current dropping below a particular value, such as during the constant-voltage phase of charging, or, load current exceeding a particular limit when not charging. When the charger is not running, and telemetry is enabled with force_telemetry_on, this limit indicates that the battery draw has exceeded a particular value. Telemetry will be enabled automatically if the input voltage exceeds the battery voltage, in which case discharge current will be nearly zero. ibat values are positive for charging and negative for discharging so the polarity of this register should be set according to the mode in which the limit alert is of interest. The value is based on the A/D value, ibat, which has a scaling factor of 1.466µV / RSNSB amperes/LSB. The alert is enabled by setting en_ibat_lo_alert and can be read back and cleared at ibat_lo_alert.
 *   - Register: @ref LTC4162_IBAT_LO_ALERT_LIMIT_REG "IBAT_LO_ALERT_LIMIT_REG"
 *   - CommandCode: 0x08
 *   - Size: 16
 *   - Offset: 0
 *   - MSB: 15
 *   - MASK: 0xFFFF
 *   - Access: R/W
 *   - Default: 0
 *   - Format: LTC4162_IBAT_FORMAT
 */
//!@{
#define LTC4162_IBAT_LO_ALERT_LIMIT_SUBADDR LTC4162_IBAT_LO_ALERT_LIMIT_REG_SUBADDR //!< @ref LTC4162_IBAT_LO_ALERT_LIMIT "IBAT_LO_ALERT_LIMIT"
#define LTC4162_IBAT_LO_ALERT_LIMIT_SIZE 16u
#define LTC4162_IBAT_LO_ALERT_LIMIT_OFFSET 0u
#define LTC4162_IBAT_LO_ALERT_LIMIT_MASK 0xFFFFu
#define LTC4162_IBAT_LO_ALERT_LIMIT_DEFAULT 0u
#define LTC4162_IBAT_LO_ALERT_LIMIT_DECODE(register_data) (register_data)
#define LTC4162_IBAT_LO_ALERT_LIMIT (LTC4162_IBAT_LO_ALERT_LIMIT_OFFSET << 12 | (LTC4162_IBAT_LO_ALERT_LIMIT_SIZE - 1) << 8 | LTC4162_IBAT_LO_ALERT_LIMIT_SUBADDR)
//!@}

/*! @defgroup LTC4162_DIE_TEMP_HI_ALERT_LIMIT_REG DIE_TEMP_HI_ALERT_LIMIT_REG
 *  @ingroup LTC4162-LADM_register_map
 *  @brief DIE_TEMP_HI_ALERT_LIMIT_REG Register
 *
 * |                    15:0 |
 * |:-----------------------:|
 * | DIE_TEMP_HI_ALERT_LIMIT |
 *
 *   - CommandCode: 0x09
 *   - Contains Bit Fields:
 *     + @ref LTC4162_DIE_TEMP_HI_ALERT_LIMIT "DIE_TEMP_HI_ALERT_LIMIT" : Signed number that sets an upper limit that can be used to trigger an interrupt based on high die temperature. The value in °C can be calculated from the A/D reading, die_temp, as TDIE(°C) = die_temp × 0.0215°C/LSB - 264.4°C. The alert is enabled by setting en_die_temp_hi_alert and can be read back and cleared at die_temp_hi_alert.
*/

//!@{
#define LTC4162_DIE_TEMP_HI_ALERT_LIMIT_REG_SUBADDR 0x09u
#define LTC4162_DIE_TEMP_HI_ALERT_LIMIT_REG (0u << 12 | (LTC4162_WORD_SIZE - 1) << 8 | LTC4162_DIE_TEMP_HI_ALERT_LIMIT_REG_SUBADDR)
//!@}
/*! @defgroup LTC4162_DIE_TEMP_HI_ALERT_LIMIT DIE_TEMP_HI_ALERT_LIMIT
 *  @ingroup LTC4162-LADM_register_map
 *  @brief DIE_TEMP_HI_ALERT_LIMIT Bit Field
 *
 *  Signed number that sets an upper limit that can be used to trigger an interrupt based on high die temperature. The value in °C can be calculated from the A/D reading, die_temp, as TDIE(°C) = die_temp × 0.0215°C/LSB - 264.4°C. The alert is enabled by setting en_die_temp_hi_alert and can be read back and cleared at die_temp_hi_alert.
 *   - Register: @ref LTC4162_DIE_TEMP_HI_ALERT_LIMIT_REG "DIE_TEMP_HI_ALERT_LIMIT_REG"
 *   - CommandCode: 0x09
 *   - Size: 16
 *   - Offset: 0
 *   - MSB: 15
 *   - MASK: 0xFFFF
 *   - Access: R/W
 *   - Default: 0
 *   - Format: LTC4162_DIE_TEMP_FORMAT
 */
//!@{
#define LTC4162_DIE_TEMP_HI_ALERT_LIMIT_SUBADDR LTC4162_DIE_TEMP_HI_ALERT_LIMIT_REG_SUBADDR //!< @ref LTC4162_DIE_TEMP_HI_ALERT_LIMIT "DIE_TEMP_HI_ALERT_LIMIT"
#define LTC4162_DIE_TEMP_HI_ALERT_LIMIT_SIZE 16u
#define LTC4162_DIE_TEMP_HI_ALERT_LIMIT_OFFSET 0u
#define LTC4162_DIE_TEMP_HI_ALERT_LIMIT_MASK 0xFFFFu
#define LTC4162_DIE_TEMP_HI_ALERT_LIMIT_DEFAULT 0u
#define LTC4162_DIE_TEMP_HI_ALERT_LIMIT_DECODE(register_data) (register_data)
#define LTC4162_DIE_TEMP_HI_ALERT_LIMIT (LTC4162_DIE_TEMP_HI_ALERT_LIMIT_OFFSET << 12 | (LTC4162_DIE_TEMP_HI_ALERT_LIMIT_SIZE - 1) << 8 | LTC4162_DIE_TEMP_HI_ALERT_LIMIT_SUBADDR)
//!@}

/*! @defgroup LTC4162_BSR_HI_ALERT_LIMIT_REG BSR_HI_ALERT_LIMIT_REG
 *  @ingroup LTC4162-LADM_register_map
 *  @brief BSR_HI_ALERT_LIMIT_REG Register
 *
 * |               15:0 |
 * |:------------------:|
 * | BSR_HI_ALERT_LIMIT |
 *
 *   - CommandCode: 0x0A
 *   - Contains Bit Fields:
 *     + @ref LTC4162_BSR_HI_ALERT_LIMIT "BSR_HI_ALERT_LIMIT" : Sets an upper limit that can be used to trigger an interrupt based on high battery resistance. The per-cell battery resistance is relative to the battery charge current setting resistor, RSNSB, and can be computed in Ω from: BSR = cell_count × bsr × RSNSB / 500. The alert is enabled by setting en_bsr_hi_alert and can be read back and cleared at bsr_hi_alert.
*/

//!@{
#define LTC4162_BSR_HI_ALERT_LIMIT_REG_SUBADDR 0x0Au
#define LTC4162_BSR_HI_ALERT_LIMIT_REG (0u << 12 | (LTC4162_WORD_SIZE - 1) << 8 | LTC4162_BSR_HI_ALERT_LIMIT_REG_SUBADDR)
//!@}
/*! @defgroup LTC4162_BSR_HI_ALERT_LIMIT BSR_HI_ALERT_LIMIT
 *  @ingroup LTC4162-LADM_register_map
 *  @brief BSR_HI_ALERT_LIMIT Bit Field
 *
 *  Sets an upper limit that can be used to trigger an interrupt based on high battery resistance. The per-cell battery resistance is relative to the battery charge current setting resistor, RSNSB, and can be computed in Ω from: BSR = cell_count × bsr × RSNSB / 500. The alert is enabled by setting en_bsr_hi_alert and can be read back and cleared at bsr_hi_alert.
 *   - Register: @ref LTC4162_BSR_HI_ALERT_LIMIT_REG "BSR_HI_ALERT_LIMIT_REG"
 *   - CommandCode: 0x0A
 *   - Size: 16
 *   - Offset: 0
 *   - MSB: 15
 *   - MASK: 0xFFFF
 *   - Access: R/W
 *   - Default: 0
 *   - Format: LTC4162_BSR_FORMAT
 */
//!@{
#define LTC4162_BSR_HI_ALERT_LIMIT_SUBADDR LTC4162_BSR_HI_ALERT_LIMIT_REG_SUBADDR //!< @ref LTC4162_BSR_HI_ALERT_LIMIT "BSR_HI_ALERT_LIMIT"
#define LTC4162_BSR_HI_ALERT_LIMIT_SIZE 16u
#define LTC4162_BSR_HI_ALERT_LIMIT_OFFSET 0u
#define LTC4162_BSR_HI_ALERT_LIMIT_MASK 0xFFFFu
#define LTC4162_BSR_HI_ALERT_LIMIT_DEFAULT 0u
#define LTC4162_BSR_HI_ALERT_LIMIT_DECODE(register_data) (register_data)
#define LTC4162_BSR_HI_ALERT_LIMIT (LTC4162_BSR_HI_ALERT_LIMIT_OFFSET << 12 | (LTC4162_BSR_HI_ALERT_LIMIT_SIZE - 1) << 8 | LTC4162_BSR_HI_ALERT_LIMIT_SUBADDR)
//!@}

/*! @defgroup LTC4162_THERMISTOR_VOLTAGE_HI_ALERT_LIMIT_REG THERMISTOR_VOLTAGE_HI_ALERT_LIMIT_REG
 *  @ingroup LTC4162-LADM_register_map
 *  @brief THERMISTOR_VOLTAGE_HI_ALERT_LIMIT_REG Register
 *
 * |                              15:0 |
 * |:---------------------------------:|
 * | THERMISTOR_VOLTAGE_HI_ALERT_LIMIT |
 *
 *   - CommandCode: 0x0B
 *   - Contains Bit Fields:
 *     + @ref LTC4162_THERMISTOR_VOLTAGE_HI_ALERT_LIMIT "THERMISTOR_VOLTAGE_HI_ALERT_LIMIT" : Signed number that sets an upper limit that can be used to trigger an interrupt based on thermistor value out of range. The value is based on the A/D value for thermistor_voltage. The thermistor value can be determined by the expression RNTC = RNTCBIAS × (21829 - thermistor_voltage) / thermistor_voltage. Recall that the thermistor has a negative temperature coefficient so higher temperatures correspond to lower thermistor_voltage readings and vice-versa. The alert is enabled by setting en_thermistor_voltage_hi_alert can be read back and cleared at thermistor_voltage_hi_alert.
*/

//!@{
#define LTC4162_THERMISTOR_VOLTAGE_HI_ALERT_LIMIT_REG_SUBADDR 0x0Bu
#define LTC4162_THERMISTOR_VOLTAGE_HI_ALERT_LIMIT_REG (0u << 12 | (LTC4162_WORD_SIZE - 1) << 8 | LTC4162_THERMISTOR_VOLTAGE_HI_ALERT_LIMIT_REG_SUBADDR)
//!@}
/*! @defgroup LTC4162_THERMISTOR_VOLTAGE_HI_ALERT_LIMIT THERMISTOR_VOLTAGE_HI_ALERT_LIMIT
 *  @ingroup LTC4162-LADM_register_map
 *  @brief THERMISTOR_VOLTAGE_HI_ALERT_LIMIT Bit Field
 *
 *  Signed number that sets an upper limit that can be used to trigger an interrupt based on thermistor value out of range. The value is based on the A/D value for thermistor_voltage. The thermistor value can be determined by the expression RNTC = RNTCBIAS × (21829 - thermistor_voltage) / thermistor_voltage. Recall that the thermistor has a negative temperature coefficient so higher temperatures correspond to lower thermistor_voltage readings and vice-versa. The alert is enabled by setting en_thermistor_voltage_hi_alert can be read back and cleared at thermistor_voltage_hi_alert.
 *   - Register: @ref LTC4162_THERMISTOR_VOLTAGE_HI_ALERT_LIMIT_REG "THERMISTOR_VOLTAGE_HI_ALERT_LIMIT_REG"
 *   - CommandCode: 0x0B
 *   - Size: 16
 *   - Offset: 0
 *   - MSB: 15
 *   - MASK: 0xFFFF
 *   - Access: R/W
 *   - Default: 0
 *   - Format: LTC4162_NTCS0402E3103FLT
 */
//!@{
#define LTC4162_THERMISTOR_VOLTAGE_HI_ALERT_LIMIT_SUBADDR LTC4162_THERMISTOR_VOLTAGE_HI_ALERT_LIMIT_REG_SUBADDR //!< @ref LTC4162_THERMISTOR_VOLTAGE_HI_ALERT_LIMIT "THERMISTOR_VOLTAGE_HI_ALERT_LIMIT"
#define LTC4162_THERMISTOR_VOLTAGE_HI_ALERT_LIMIT_SIZE 16u
#define LTC4162_THERMISTOR_VOLTAGE_HI_ALERT_LIMIT_OFFSET 0u
#define LTC4162_THERMISTOR_VOLTAGE_HI_ALERT_LIMIT_MASK 0xFFFFu
#define LTC4162_THERMISTOR_VOLTAGE_HI_ALERT_LIMIT_DEFAULT 0u
#define LTC4162_THERMISTOR_VOLTAGE_HI_ALERT_LIMIT_DECODE(register_data) (register_data)
#define LTC4162_THERMISTOR_VOLTAGE_HI_ALERT_LIMIT (LTC4162_THERMISTOR_VOLTAGE_HI_ALERT_LIMIT_OFFSET << 12 | (LTC4162_THERMISTOR_VOLTAGE_HI_ALERT_LIMIT_SIZE - 1) << 8 | LTC4162_THERMISTOR_VOLTAGE_HI_ALERT_LIMIT_SUBADDR)
//!@}

/*! @defgroup LTC4162_THERMISTOR_VOLTAGE_LO_ALERT_LIMIT_REG THERMISTOR_VOLTAGE_LO_ALERT_LIMIT_REG
 *  @ingroup LTC4162-LADM_register_map
 *  @brief THERMISTOR_VOLTAGE_LO_ALERT_LIMIT_REG Register
 *
 * |                              15:0 |
 * |:---------------------------------:|
 * | THERMISTOR_VOLTAGE_LO_ALERT_LIMIT |
 *
 *   - CommandCode: 0x0C
 *   - Contains Bit Fields:
 *     + @ref LTC4162_THERMISTOR_VOLTAGE_LO_ALERT_LIMIT "THERMISTOR_VOLTAGE_LO_ALERT_LIMIT" : Signed number that sets a lower limit that can be used to trigger an interrupt based on thermistor value out of range. The value is based on the A/D value for thermistor_voltage. The thermistor value can be determined by the expression RNTC = RNTCBIAS × (21829 - thermistor_voltage) / thermistor_voltage. Recall that the thermistor has a negative temperature coefficient so higher temperatures correspond to lower thermistor_voltage readings and vice-versa. The alert is enabled by setting en_thermistor_voltage_lo_alert and can be read back and cleared at thermistor_voltage_lo_alert.
*/

//!@{
#define LTC4162_THERMISTOR_VOLTAGE_LO_ALERT_LIMIT_REG_SUBADDR 0x0Cu
#define LTC4162_THERMISTOR_VOLTAGE_LO_ALERT_LIMIT_REG (0u << 12 | (LTC4162_WORD_SIZE - 1) << 8 | LTC4162_THERMISTOR_VOLTAGE_LO_ALERT_LIMIT_REG_SUBADDR)
//!@}
/*! @defgroup LTC4162_THERMISTOR_VOLTAGE_LO_ALERT_LIMIT THERMISTOR_VOLTAGE_LO_ALERT_LIMIT
 *  @ingroup LTC4162-LADM_register_map
 *  @brief THERMISTOR_VOLTAGE_LO_ALERT_LIMIT Bit Field
 *
 *  Signed number that sets a lower limit that can be used to trigger an interrupt based on thermistor value out of range. The value is based on the A/D value for thermistor_voltage. The thermistor value can be determined by the expression RNTC = RNTCBIAS × (21829 - thermistor_voltage) / thermistor_voltage. Recall that the thermistor has a negative temperature coefficient so higher temperatures correspond to lower thermistor_voltage readings and vice-versa. The alert is enabled by setting en_thermistor_voltage_lo_alert and can be read back and cleared at thermistor_voltage_lo_alert.
 *   - Register: @ref LTC4162_THERMISTOR_VOLTAGE_LO_ALERT_LIMIT_REG "THERMISTOR_VOLTAGE_LO_ALERT_LIMIT_REG"
 *   - CommandCode: 0x0C
 *   - Size: 16
 *   - Offset: 0
 *   - MSB: 15
 *   - MASK: 0xFFFF
 *   - Access: R/W
 *   - Default: 0
 *   - Format: LTC4162_NTCS0402E3103FLT
 */
//!@{
#define LTC4162_THERMISTOR_VOLTAGE_LO_ALERT_LIMIT_SUBADDR LTC4162_THERMISTOR_VOLTAGE_LO_ALERT_LIMIT_REG_SUBADDR //!< @ref LTC4162_THERMISTOR_VOLTAGE_LO_ALERT_LIMIT "THERMISTOR_VOLTAGE_LO_ALERT_LIMIT"
#define LTC4162_THERMISTOR_VOLTAGE_LO_ALERT_LIMIT_SIZE 16u
#define LTC4162_THERMISTOR_VOLTAGE_LO_ALERT_LIMIT_OFFSET 0u
#define LTC4162_THERMISTOR_VOLTAGE_LO_ALERT_LIMIT_MASK 0xFFFFu
#define LTC4162_THERMISTOR_VOLTAGE_LO_ALERT_LIMIT_DEFAULT 0u
#define LTC4162_THERMISTOR_VOLTAGE_LO_ALERT_LIMIT_DECODE(register_data) (register_data)
#define LTC4162_THERMISTOR_VOLTAGE_LO_ALERT_LIMIT (LTC4162_THERMISTOR_VOLTAGE_LO_ALERT_LIMIT_OFFSET << 12 | (LTC4162_THERMISTOR_VOLTAGE_LO_ALERT_LIMIT_SIZE - 1) << 8 | LTC4162_THERMISTOR_VOLTAGE_LO_ALERT_LIMIT_SUBADDR)
//!@}

/*! @defgroup LTC4162_EN_LIMIT_ALERTS_REG EN_LIMIT_ALERTS_REG
 *  @ingroup LTC4162-LADM_register_map
 *  @brief EN_LIMIT_ALERTS_REG Register
 *
 * |                       15 |                14 | 13:12 |               11 |               10 |               9 |               8 |                7 |                6 |               5 |                4 |                    3 |               2 |                              1 |                              0 |
 * |:------------------------:|:-----------------:|:-----:|:----------------:|:----------------:|:---------------:|:---------------:|:----------------:|:----------------:|:---------------:|:----------------:|:--------------------:|:---------------:|:------------------------------:|:------------------------------:|
 * | EN_TELEMETRY_VALID_ALERT | EN_BSR_DONE_ALERT |   n/a | EN_VBAT_LO_ALERT | EN_VBAT_HI_ALERT | EN_VIN_LO_ALERT | EN_VIN_HI_ALERT | EN_VOUT_LO_ALERT | EN_VOUT_HI_ALERT | EN_IIN_HI_ALERT | EN_IBAT_LO_ALERT | EN_DIE_TEMP_HI_ALERT | EN_BSR_HI_ALERT | EN_THERMISTOR_VOLTAGE_HI_ALERT | EN_THERMISTOR_VOLTAGE_LO_ALERT |
 *
 * Enable limit monitoring and alert notification via SMBALERT
 *   - CommandCode: 0x0D
 *   - Contains Bit Fields:
 *     + @ref LTC4162_EN_TELEMETRY_VALID_ALERT "EN_TELEMETRY_VALID_ALERT" : To ensure high measurement accuracy, the telemetry system in the LTC4162 has a nominal start-up time of approximately 12ms. Setting this interrupt request causes an SMBALERT telemetry_valid_alert when telemetry_valid indicates that the telemetry system's readings are valid. Note that the switching battery charger will not operate until this telemetry system warmup period has passed, regardless of the state of this setting.
 *     + @ref LTC4162_EN_BSR_DONE_ALERT "EN_BSR_DONE_ALERT" : Interrupt request that causes an SMBALERT upon bsr_done_alert when the bsr (battery-series-resistance) measurement is finished.
 *     + @ref LTC4162_EN_VBAT_LO_ALERT "EN_VBAT_LO_ALERT" : Interrupt request that causes an SMBALERT upon vbat_lo_alert when vbat is below vbat_lo_alert_limit.
 *     + @ref LTC4162_EN_VBAT_HI_ALERT "EN_VBAT_HI_ALERT" : Interrupt request that causes an SMBALERT upon vbat_hi_alert when vbat is above vbat_hi_alert_limit.
 *     + @ref LTC4162_EN_VIN_LO_ALERT "EN_VIN_LO_ALERT" : Interrupt request that causes an SMBALERT upon vin_lo_alert when vin is below vin_lo_alert_limit.
 *     + @ref LTC4162_EN_VIN_HI_ALERT "EN_VIN_HI_ALERT" : Interrupt request that causes an SMBALERT upon vin_hi_alert when vin is above vin_hi_alert_limit.
 *     + @ref LTC4162_EN_VOUT_LO_ALERT "EN_VOUT_LO_ALERT" : Interrupt request that causes an SMBALERT upon vout_lo_alert when vout is below vout_lo_alert_limit.
 *     + @ref LTC4162_EN_VOUT_HI_ALERT "EN_VOUT_HI_ALERT" : Interrupt request that causes an SMBALERT upon vout_hi_alert when vout is above vout_hi_alert_limit.
 *     + @ref LTC4162_EN_IIN_HI_ALERT "EN_IIN_HI_ALERT" : Interrupt request that causes an SMBALERT upon iin_hi_alert when iin is above iin_hi_alert_limit.
 *     + @ref LTC4162_EN_IBAT_LO_ALERT "EN_IBAT_LO_ALERT" : Interrupt request that causes an SMBALERT upon ibat_lo_alert when ibat is below ibat_lo_alert_limit.
 *     + @ref LTC4162_EN_DIE_TEMP_HI_ALERT "EN_DIE_TEMP_HI_ALERT" : Interrupt request that causes an SMBALERT upon die_temp_hi_alert when die_temp is above die_temp_hi_alert_limit.
 *     + @ref LTC4162_EN_BSR_HI_ALERT "EN_BSR_HI_ALERT" : Interrupt request that causes an SMBALERT upon bsr_hi_alert when bsr is above bsr_hi_alert_limit.
 *     + @ref LTC4162_EN_THERMISTOR_VOLTAGE_HI_ALERT "EN_THERMISTOR_VOLTAGE_HI_ALERT" : Interrupt request that causes an SMBALERT upon thermistor_voltage_hi_alert when thermistor_voltage is above thermistor_voltage_hi_alert_limit. Recall that the thermistor has a negative temperature coefficient so higher thermistor_voltage readings correspond to lower temperatures.
 *     + @ref LTC4162_EN_THERMISTOR_VOLTAGE_LO_ALERT "EN_THERMISTOR_VOLTAGE_LO_ALERT" : Interrupt request that causes an SMBALERT upon thermistor_voltage_lo_alert when thermistor_voltage is below thermistor_voltage_lo_alert_limit. Recall that the thermistor has a negative temperature coefficient so lower thermistor_voltage readings correspond to higher temperatures.
*/

//!@{
#define LTC4162_EN_LIMIT_ALERTS_REG_SUBADDR 0x0Du
#define LTC4162_EN_LIMIT_ALERTS_REG (0u << 12 | (LTC4162_WORD_SIZE - 1) << 8 | LTC4162_EN_LIMIT_ALERTS_REG_SUBADDR)
//!@}
/*! @defgroup LTC4162_EN_TELEMETRY_VALID_ALERT EN_TELEMETRY_VALID_ALERT
 *  @ingroup LTC4162-LADM_register_map
 *  @brief EN_TELEMETRY_VALID_ALERT Bit Field
 *
 *  To ensure high measurement accuracy, the telemetry system in the LTC4162 has a nominal start-up time of approximately 12ms. Setting this interrupt request causes an SMBALERT telemetry_valid_alert when telemetry_valid indicates that the telemetry system's readings are valid. Note that the switching battery charger will not operate until this telemetry system warmup period has passed, regardless of the state of this setting.
 *   - Register: @ref LTC4162_EN_LIMIT_ALERTS_REG "EN_LIMIT_ALERTS_REG"
 *   - CommandCode: 0x0D
 *   - Size: 1
 *   - Offset: 15
 *   - MSB: 15
 *   - MASK: 0x8000
 *   - Access: R/W
 *   - Default: 0
 */
//!@{
#define LTC4162_EN_TELEMETRY_VALID_ALERT_SUBADDR LTC4162_EN_LIMIT_ALERTS_REG_SUBADDR //!< @ref LTC4162_EN_TELEMETRY_VALID_ALERT "EN_TELEMETRY_VALID_ALERT"
#define LTC4162_EN_TELEMETRY_VALID_ALERT_SIZE 1u
#define LTC4162_EN_TELEMETRY_VALID_ALERT_OFFSET 15u
#define LTC4162_EN_TELEMETRY_VALID_ALERT_MASK 0x8000u
#define LTC4162_EN_TELEMETRY_VALID_ALERT_DEFAULT 0u
#define LTC4162_EN_TELEMETRY_VALID_ALERT_DECODE(register_data) (((register_data) & LTC4162_EN_TELEMETRY_VALID_ALERT_MASK) >> LTC4162_EN_TELEMETRY_VALID_ALERT_OFFSET)
#define LTC4162_EN_TELEMETRY_VALID_ALERT (LTC4162_EN_TELEMETRY_VALID_ALERT_OFFSET << 12 | (LTC4162_EN_TELEMETRY_VALID_ALERT_SIZE - 1) << 8 | LTC4162_EN_TELEMETRY_VALID_ALERT_SUBADDR)
//!@}
/*! @defgroup LTC4162_EN_BSR_DONE_ALERT EN_BSR_DONE_ALERT
 *  @ingroup LTC4162-LADM_register_map
 *  @brief EN_BSR_DONE_ALERT Bit Field
 *
 *  Interrupt request that causes an SMBALERT upon bsr_done_alert when the bsr (battery-series-resistance) measurement is finished.
 *   - Register: @ref LTC4162_EN_LIMIT_ALERTS_REG "EN_LIMIT_ALERTS_REG"
 *   - CommandCode: 0x0D
 *   - Size: 1
 *   - Offset: 14
 *   - MSB: 14
 *   - MASK: 0x4000
 *   - Access: R/W
 *   - Default: 0
 */
//!@{
#define LTC4162_EN_BSR_DONE_ALERT_SUBADDR LTC4162_EN_LIMIT_ALERTS_REG_SUBADDR //!< @ref LTC4162_EN_BSR_DONE_ALERT "EN_BSR_DONE_ALERT"
#define LTC4162_EN_BSR_DONE_ALERT_SIZE 1u
#define LTC4162_EN_BSR_DONE_ALERT_OFFSET 14u
#define LTC4162_EN_BSR_DONE_ALERT_MASK 0x4000u
#define LTC4162_EN_BSR_DONE_ALERT_DEFAULT 0u
#define LTC4162_EN_BSR_DONE_ALERT_DECODE(register_data) (((register_data) & LTC4162_EN_BSR_DONE_ALERT_MASK) >> LTC4162_EN_BSR_DONE_ALERT_OFFSET)
#define LTC4162_EN_BSR_DONE_ALERT (LTC4162_EN_BSR_DONE_ALERT_OFFSET << 12 | (LTC4162_EN_BSR_DONE_ALERT_SIZE - 1) << 8 | LTC4162_EN_BSR_DONE_ALERT_SUBADDR)
//!@}
/*! @defgroup LTC4162_EN_VBAT_LO_ALERT EN_VBAT_LO_ALERT
 *  @ingroup LTC4162-LADM_register_map
 *  @brief EN_VBAT_LO_ALERT Bit Field
 *
 *  Interrupt request that causes an SMBALERT upon vbat_lo_alert when vbat is below vbat_lo_alert_limit.
 *   - Register: @ref LTC4162_EN_LIMIT_ALERTS_REG "EN_LIMIT_ALERTS_REG"
 *   - CommandCode: 0x0D
 *   - Size: 1
 *   - Offset: 11
 *   - MSB: 11
 *   - MASK: 0x0800
 *   - Access: R/W
 *   - Default: 0
 */
//!@{
#define LTC4162_EN_VBAT_LO_ALERT_SUBADDR LTC4162_EN_LIMIT_ALERTS_REG_SUBADDR //!< @ref LTC4162_EN_VBAT_LO_ALERT "EN_VBAT_LO_ALERT"
#define LTC4162_EN_VBAT_LO_ALERT_SIZE 1u
#define LTC4162_EN_VBAT_LO_ALERT_OFFSET 11u
#define LTC4162_EN_VBAT_LO_ALERT_MASK 0x0800u
#define LTC4162_EN_VBAT_LO_ALERT_DEFAULT 0u
#define LTC4162_EN_VBAT_LO_ALERT_DECODE(register_data) (((register_data) & LTC4162_EN_VBAT_LO_ALERT_MASK) >> LTC4162_EN_VBAT_LO_ALERT_OFFSET)
#define LTC4162_EN_VBAT_LO_ALERT (LTC4162_EN_VBAT_LO_ALERT_OFFSET << 12 | (LTC4162_EN_VBAT_LO_ALERT_SIZE - 1) << 8 | LTC4162_EN_VBAT_LO_ALERT_SUBADDR)
//!@}
/*! @defgroup LTC4162_EN_VBAT_HI_ALERT EN_VBAT_HI_ALERT
 *  @ingroup LTC4162-LADM_register_map
 *  @brief EN_VBAT_HI_ALERT Bit Field
 *
 *  Interrupt request that causes an SMBALERT upon vbat_hi_alert when vbat is above vbat_hi_alert_limit.
 *   - Register: @ref LTC4162_EN_LIMIT_ALERTS_REG "EN_LIMIT_ALERTS_REG"
 *   - CommandCode: 0x0D
 *   - Size: 1
 *   - Offset: 10
 *   - MSB: 10
 *   - MASK: 0x0400
 *   - Access: R/W
 *   - Default: 0
 */
//!@{
#define LTC4162_EN_VBAT_HI_ALERT_SUBADDR LTC4162_EN_LIMIT_ALERTS_REG_SUBADDR //!< @ref LTC4162_EN_VBAT_HI_ALERT "EN_VBAT_HI_ALERT"
#define LTC4162_EN_VBAT_HI_ALERT_SIZE 1u
#define LTC4162_EN_VBAT_HI_ALERT_OFFSET 10u
#define LTC4162_EN_VBAT_HI_ALERT_MASK 0x0400u
#define LTC4162_EN_VBAT_HI_ALERT_DEFAULT 0u
#define LTC4162_EN_VBAT_HI_ALERT_DECODE(register_data) (((register_data) & LTC4162_EN_VBAT_HI_ALERT_MASK) >> LTC4162_EN_VBAT_HI_ALERT_OFFSET)
#define LTC4162_EN_VBAT_HI_ALERT (LTC4162_EN_VBAT_HI_ALERT_OFFSET << 12 | (LTC4162_EN_VBAT_HI_ALERT_SIZE - 1) << 8 | LTC4162_EN_VBAT_HI_ALERT_SUBADDR)
//!@}
/*! @defgroup LTC4162_EN_VIN_LO_ALERT EN_VIN_LO_ALERT
 *  @ingroup LTC4162-LADM_register_map
 *  @brief EN_VIN_LO_ALERT Bit Field
 *
 *  Interrupt request that causes an SMBALERT upon vin_lo_alert when vin is below vin_lo_alert_limit.
 *   - Register: @ref LTC4162_EN_LIMIT_ALERTS_REG "EN_LIMIT_ALERTS_REG"
 *   - CommandCode: 0x0D
 *   - Size: 1
 *   - Offset: 9
 *   - MSB: 9
 *   - MASK: 0x0200
 *   - Access: R/W
 *   - Default: 0
 */
//!@{
#define LTC4162_EN_VIN_LO_ALERT_SUBADDR LTC4162_EN_LIMIT_ALERTS_REG_SUBADDR //!< @ref LTC4162_EN_VIN_LO_ALERT "EN_VIN_LO_ALERT"
#define LTC4162_EN_VIN_LO_ALERT_SIZE 1u
#define LTC4162_EN_VIN_LO_ALERT_OFFSET 9u
#define LTC4162_EN_VIN_LO_ALERT_MASK 0x0200u
#define LTC4162_EN_VIN_LO_ALERT_DEFAULT 0u
#define LTC4162_EN_VIN_LO_ALERT_DECODE(register_data) (((register_data) & LTC4162_EN_VIN_LO_ALERT_MASK) >> LTC4162_EN_VIN_LO_ALERT_OFFSET)
#define LTC4162_EN_VIN_LO_ALERT (LTC4162_EN_VIN_LO_ALERT_OFFSET << 12 | (LTC4162_EN_VIN_LO_ALERT_SIZE - 1) << 8 | LTC4162_EN_VIN_LO_ALERT_SUBADDR)
//!@}
/*! @defgroup LTC4162_EN_VIN_HI_ALERT EN_VIN_HI_ALERT
 *  @ingroup LTC4162-LADM_register_map
 *  @brief EN_VIN_HI_ALERT Bit Field
 *
 *  Interrupt request that causes an SMBALERT upon vin_hi_alert when vin is above vin_hi_alert_limit.
 *   - Register: @ref LTC4162_EN_LIMIT_ALERTS_REG "EN_LIMIT_ALERTS_REG"
 *   - CommandCode: 0x0D
 *   - Size: 1
 *   - Offset: 8
 *   - MSB: 8
 *   - MASK: 0x0100
 *   - Access: R/W
 *   - Default: 0
 */
//!@{
#define LTC4162_EN_VIN_HI_ALERT_SUBADDR LTC4162_EN_LIMIT_ALERTS_REG_SUBADDR //!< @ref LTC4162_EN_VIN_HI_ALERT "EN_VIN_HI_ALERT"
#define LTC4162_EN_VIN_HI_ALERT_SIZE 1u
#define LTC4162_EN_VIN_HI_ALERT_OFFSET 8u
#define LTC4162_EN_VIN_HI_ALERT_MASK 0x0100u
#define LTC4162_EN_VIN_HI_ALERT_DEFAULT 0u
#define LTC4162_EN_VIN_HI_ALERT_DECODE(register_data) (((register_data) & LTC4162_EN_VIN_HI_ALERT_MASK) >> LTC4162_EN_VIN_HI_ALERT_OFFSET)
#define LTC4162_EN_VIN_HI_ALERT (LTC4162_EN_VIN_HI_ALERT_OFFSET << 12 | (LTC4162_EN_VIN_HI_ALERT_SIZE - 1) << 8 | LTC4162_EN_VIN_HI_ALERT_SUBADDR)
//!@}
/*! @defgroup LTC4162_EN_VOUT_LO_ALERT EN_VOUT_LO_ALERT
 *  @ingroup LTC4162-LADM_register_map
 *  @brief EN_VOUT_LO_ALERT Bit Field
 *
 *  Interrupt request that causes an SMBALERT upon vout_lo_alert when vout is below vout_lo_alert_limit.
 *   - Register: @ref LTC4162_EN_LIMIT_ALERTS_REG "EN_LIMIT_ALERTS_REG"
 *   - CommandCode: 0x0D
 *   - Size: 1
 *   - Offset: 7
 *   - MSB: 7
 *   - MASK: 0x0080
 *   - Access: R/W
 *   - Default: 0
 */
//!@{
#define LTC4162_EN_VOUT_LO_ALERT_SUBADDR LTC4162_EN_LIMIT_ALERTS_REG_SUBADDR //!< @ref LTC4162_EN_VOUT_LO_ALERT "EN_VOUT_LO_ALERT"
#define LTC4162_EN_VOUT_LO_ALERT_SIZE 1u
#define LTC4162_EN_VOUT_LO_ALERT_OFFSET 7u
#define LTC4162_EN_VOUT_LO_ALERT_MASK 0x0080u
#define LTC4162_EN_VOUT_LO_ALERT_DEFAULT 0u
#define LTC4162_EN_VOUT_LO_ALERT_DECODE(register_data) (((register_data) & LTC4162_EN_VOUT_LO_ALERT_MASK) >> LTC4162_EN_VOUT_LO_ALERT_OFFSET)
#define LTC4162_EN_VOUT_LO_ALERT (LTC4162_EN_VOUT_LO_ALERT_OFFSET << 12 | (LTC4162_EN_VOUT_LO_ALERT_SIZE - 1) << 8 | LTC4162_EN_VOUT_LO_ALERT_SUBADDR)
//!@}
/*! @defgroup LTC4162_EN_VOUT_HI_ALERT EN_VOUT_HI_ALERT
 *  @ingroup LTC4162-LADM_register_map
 *  @brief EN_VOUT_HI_ALERT Bit Field
 *
 *  Interrupt request that causes an SMBALERT upon vout_hi_alert when vout is above vout_hi_alert_limit.
 *   - Register: @ref LTC4162_EN_LIMIT_ALERTS_REG "EN_LIMIT_ALERTS_REG"
 *   - CommandCode: 0x0D
 *   - Size: 1
 *   - Offset: 6
 *   - MSB: 6
 *   - MASK: 0x0040
 *   - Access: R/W
 *   - Default: 0
 */
//!@{
#define LTC4162_EN_VOUT_HI_ALERT_SUBADDR LTC4162_EN_LIMIT_ALERTS_REG_SUBADDR //!< @ref LTC4162_EN_VOUT_HI_ALERT "EN_VOUT_HI_ALERT"
#define LTC4162_EN_VOUT_HI_ALERT_SIZE 1u
#define LTC4162_EN_VOUT_HI_ALERT_OFFSET 6u
#define LTC4162_EN_VOUT_HI_ALERT_MASK 0x0040u
#define LTC4162_EN_VOUT_HI_ALERT_DEFAULT 0u
#define LTC4162_EN_VOUT_HI_ALERT_DECODE(register_data) (((register_data) & LTC4162_EN_VOUT_HI_ALERT_MASK) >> LTC4162_EN_VOUT_HI_ALERT_OFFSET)
#define LTC4162_EN_VOUT_HI_ALERT (LTC4162_EN_VOUT_HI_ALERT_OFFSET << 12 | (LTC4162_EN_VOUT_HI_ALERT_SIZE - 1) << 8 | LTC4162_EN_VOUT_HI_ALERT_SUBADDR)
//!@}
/*! @defgroup LTC4162_EN_IIN_HI_ALERT EN_IIN_HI_ALERT
 *  @ingroup LTC4162-LADM_register_map
 *  @brief EN_IIN_HI_ALERT Bit Field
 *
 *  Interrupt request that causes an SMBALERT upon iin_hi_alert when iin is above iin_hi_alert_limit.
 *   - Register: @ref LTC4162_EN_LIMIT_ALERTS_REG "EN_LIMIT_ALERTS_REG"
 *   - CommandCode: 0x0D
 *   - Size: 1
 *   - Offset: 5
 *   - MSB: 5
 *   - MASK: 0x0020
 *   - Access: R/W
 *   - Default: 0
 */
//!@{
#define LTC4162_EN_IIN_HI_ALERT_SUBADDR LTC4162_EN_LIMIT_ALERTS_REG_SUBADDR //!< @ref LTC4162_EN_IIN_HI_ALERT "EN_IIN_HI_ALERT"
#define LTC4162_EN_IIN_HI_ALERT_SIZE 1u
#define LTC4162_EN_IIN_HI_ALERT_OFFSET 5u
#define LTC4162_EN_IIN_HI_ALERT_MASK 0x0020u
#define LTC4162_EN_IIN_HI_ALERT_DEFAULT 0u
#define LTC4162_EN_IIN_HI_ALERT_DECODE(register_data) (((register_data) & LTC4162_EN_IIN_HI_ALERT_MASK) >> LTC4162_EN_IIN_HI_ALERT_OFFSET)
#define LTC4162_EN_IIN_HI_ALERT (LTC4162_EN_IIN_HI_ALERT_OFFSET << 12 | (LTC4162_EN_IIN_HI_ALERT_SIZE - 1) << 8 | LTC4162_EN_IIN_HI_ALERT_SUBADDR)
//!@}
/*! @defgroup LTC4162_EN_IBAT_LO_ALERT EN_IBAT_LO_ALERT
 *  @ingroup LTC4162-LADM_register_map
 *  @brief EN_IBAT_LO_ALERT Bit Field
 *
 *  Interrupt request that causes an SMBALERT upon ibat_lo_alert when ibat is below ibat_lo_alert_limit.
 *   - Register: @ref LTC4162_EN_LIMIT_ALERTS_REG "EN_LIMIT_ALERTS_REG"
 *   - CommandCode: 0x0D
 *   - Size: 1
 *   - Offset: 4
 *   - MSB: 4
 *   - MASK: 0x0010
 *   - Access: R/W
 *   - Default: 0
 */
//!@{
#define LTC4162_EN_IBAT_LO_ALERT_SUBADDR LTC4162_EN_LIMIT_ALERTS_REG_SUBADDR //!< @ref LTC4162_EN_IBAT_LO_ALERT "EN_IBAT_LO_ALERT"
#define LTC4162_EN_IBAT_LO_ALERT_SIZE 1u
#define LTC4162_EN_IBAT_LO_ALERT_OFFSET 4u
#define LTC4162_EN_IBAT_LO_ALERT_MASK 0x0010u
#define LTC4162_EN_IBAT_LO_ALERT_DEFAULT 0u
#define LTC4162_EN_IBAT_LO_ALERT_DECODE(register_data) (((register_data) & LTC4162_EN_IBAT_LO_ALERT_MASK) >> LTC4162_EN_IBAT_LO_ALERT_OFFSET)
#define LTC4162_EN_IBAT_LO_ALERT (LTC4162_EN_IBAT_LO_ALERT_OFFSET << 12 | (LTC4162_EN_IBAT_LO_ALERT_SIZE - 1) << 8 | LTC4162_EN_IBAT_LO_ALERT_SUBADDR)
//!@}
/*! @defgroup LTC4162_EN_DIE_TEMP_HI_ALERT EN_DIE_TEMP_HI_ALERT
 *  @ingroup LTC4162-LADM_register_map
 *  @brief EN_DIE_TEMP_HI_ALERT Bit Field
 *
 *  Interrupt request that causes an SMBALERT upon die_temp_hi_alert when die_temp is above die_temp_hi_alert_limit.
 *   - Register: @ref LTC4162_EN_LIMIT_ALERTS_REG "EN_LIMIT_ALERTS_REG"
 *   - CommandCode: 0x0D
 *   - Size: 1
 *   - Offset: 3
 *   - MSB: 3
 *   - MASK: 0x0008
 *   - Access: R/W
 *   - Default: 0
 */
//!@{
#define LTC4162_EN_DIE_TEMP_HI_ALERT_SUBADDR LTC4162_EN_LIMIT_ALERTS_REG_SUBADDR //!< @ref LTC4162_EN_DIE_TEMP_HI_ALERT "EN_DIE_TEMP_HI_ALERT"
#define LTC4162_EN_DIE_TEMP_HI_ALERT_SIZE 1u
#define LTC4162_EN_DIE_TEMP_HI_ALERT_OFFSET 3u
#define LTC4162_EN_DIE_TEMP_HI_ALERT_MASK 0x0008u
#define LTC4162_EN_DIE_TEMP_HI_ALERT_DEFAULT 0u
#define LTC4162_EN_DIE_TEMP_HI_ALERT_DECODE(register_data) (((register_data) & LTC4162_EN_DIE_TEMP_HI_ALERT_MASK) >> LTC4162_EN_DIE_TEMP_HI_ALERT_OFFSET)
#define LTC4162_EN_DIE_TEMP_HI_ALERT (LTC4162_EN_DIE_TEMP_HI_ALERT_OFFSET << 12 | (LTC4162_EN_DIE_TEMP_HI_ALERT_SIZE - 1) << 8 | LTC4162_EN_DIE_TEMP_HI_ALERT_SUBADDR)
//!@}
/*! @defgroup LTC4162_EN_BSR_HI_ALERT EN_BSR_HI_ALERT
 *  @ingroup LTC4162-LADM_register_map
 *  @brief EN_BSR_HI_ALERT Bit Field
 *
 *  Interrupt request that causes an SMBALERT upon bsr_hi_alert when bsr is above bsr_hi_alert_limit.
 *   - Register: @ref LTC4162_EN_LIMIT_ALERTS_REG "EN_LIMIT_ALERTS_REG"
 *   - CommandCode: 0x0D
 *   - Size: 1
 *   - Offset: 2
 *   - MSB: 2
 *   - MASK: 0x0004
 *   - Access: R/W
 *   - Default: 0
 */
//!@{
#define LTC4162_EN_BSR_HI_ALERT_SUBADDR LTC4162_EN_LIMIT_ALERTS_REG_SUBADDR //!< @ref LTC4162_EN_BSR_HI_ALERT "EN_BSR_HI_ALERT"
#define LTC4162_EN_BSR_HI_ALERT_SIZE 1u
#define LTC4162_EN_BSR_HI_ALERT_OFFSET 2u
#define LTC4162_EN_BSR_HI_ALERT_MASK 0x0004u
#define LTC4162_EN_BSR_HI_ALERT_DEFAULT 0u
#define LTC4162_EN_BSR_HI_ALERT_DECODE(register_data) (((register_data) & LTC4162_EN_BSR_HI_ALERT_MASK) >> LTC4162_EN_BSR_HI_ALERT_OFFSET)
#define LTC4162_EN_BSR_HI_ALERT (LTC4162_EN_BSR_HI_ALERT_OFFSET << 12 | (LTC4162_EN_BSR_HI_ALERT_SIZE - 1) << 8 | LTC4162_EN_BSR_HI_ALERT_SUBADDR)
//!@}
/*! @defgroup LTC4162_EN_THERMISTOR_VOLTAGE_HI_ALERT EN_THERMISTOR_VOLTAGE_HI_ALERT
 *  @ingroup LTC4162-LADM_register_map
 *  @brief EN_THERMISTOR_VOLTAGE_HI_ALERT Bit Field
 *
 *  Interrupt request that causes an SMBALERT upon thermistor_voltage_hi_alert when thermistor_voltage is above thermistor_voltage_hi_alert_limit. Recall that the thermistor has a negative temperature coefficient so higher thermistor_voltage readings correspond to lower temperatures.
 *   - Register: @ref LTC4162_EN_LIMIT_ALERTS_REG "EN_LIMIT_ALERTS_REG"
 *   - CommandCode: 0x0D
 *   - Size: 1
 *   - Offset: 1
 *   - MSB: 1
 *   - MASK: 0x0002
 *   - Access: R/W
 *   - Default: 0
 */
//!@{
#define LTC4162_EN_THERMISTOR_VOLTAGE_HI_ALERT_SUBADDR LTC4162_EN_LIMIT_ALERTS_REG_SUBADDR //!< @ref LTC4162_EN_THERMISTOR_VOLTAGE_HI_ALERT "EN_THERMISTOR_VOLTAGE_HI_ALERT"
#define LTC4162_EN_THERMISTOR_VOLTAGE_HI_ALERT_SIZE 1u
#define LTC4162_EN_THERMISTOR_VOLTAGE_HI_ALERT_OFFSET 1u
#define LTC4162_EN_THERMISTOR_VOLTAGE_HI_ALERT_MASK 0x0002u
#define LTC4162_EN_THERMISTOR_VOLTAGE_HI_ALERT_DEFAULT 0u
#define LTC4162_EN_THERMISTOR_VOLTAGE_HI_ALERT_DECODE(register_data) (((register_data) & LTC4162_EN_THERMISTOR_VOLTAGE_HI_ALERT_MASK) >> LTC4162_EN_THERMISTOR_VOLTAGE_HI_ALERT_OFFSET)
#define LTC4162_EN_THERMISTOR_VOLTAGE_HI_ALERT (LTC4162_EN_THERMISTOR_VOLTAGE_HI_ALERT_OFFSET << 12 | (LTC4162_EN_THERMISTOR_VOLTAGE_HI_ALERT_SIZE - 1) << 8 | LTC4162_EN_THERMISTOR_VOLTAGE_HI_ALERT_SUBADDR)
//!@}
/*! @defgroup LTC4162_EN_THERMISTOR_VOLTAGE_LO_ALERT EN_THERMISTOR_VOLTAGE_LO_ALERT
 *  @ingroup LTC4162-LADM_register_map
 *  @brief EN_THERMISTOR_VOLTAGE_LO_ALERT Bit Field
 *
 *  Interrupt request that causes an SMBALERT upon thermistor_voltage_lo_alert when thermistor_voltage is below thermistor_voltage_lo_alert_limit. Recall that the thermistor has a negative temperature coefficient so lower thermistor_voltage readings correspond to higher temperatures.
 *   - Register: @ref LTC4162_EN_LIMIT_ALERTS_REG "EN_LIMIT_ALERTS_REG"
 *   - CommandCode: 0x0D
 *   - Size: 1
 *   - Offset: 0
 *   - MSB: 0
 *   - MASK: 0x0001
 *   - Access: R/W
 *   - Default: 0
 */
//!@{
#define LTC4162_EN_THERMISTOR_VOLTAGE_LO_ALERT_SUBADDR LTC4162_EN_LIMIT_ALERTS_REG_SUBADDR //!< @ref LTC4162_EN_THERMISTOR_VOLTAGE_LO_ALERT "EN_THERMISTOR_VOLTAGE_LO_ALERT"
#define LTC4162_EN_THERMISTOR_VOLTAGE_LO_ALERT_SIZE 1u
#define LTC4162_EN_THERMISTOR_VOLTAGE_LO_ALERT_OFFSET 0u
#define LTC4162_EN_THERMISTOR_VOLTAGE_LO_ALERT_MASK 0x0001u
#define LTC4162_EN_THERMISTOR_VOLTAGE_LO_ALERT_DEFAULT 0u
#define LTC4162_EN_THERMISTOR_VOLTAGE_LO_ALERT_DECODE(register_data) (((register_data) & LTC4162_EN_THERMISTOR_VOLTAGE_LO_ALERT_MASK) >> LTC4162_EN_THERMISTOR_VOLTAGE_LO_ALERT_OFFSET)
#define LTC4162_EN_THERMISTOR_VOLTAGE_LO_ALERT (LTC4162_EN_THERMISTOR_VOLTAGE_LO_ALERT_OFFSET << 12 | (LTC4162_EN_THERMISTOR_VOLTAGE_LO_ALERT_SIZE - 1) << 8 | LTC4162_EN_THERMISTOR_VOLTAGE_LO_ALERT_SUBADDR)
//!@}

/*! @defgroup LTC4162_EN_CHARGER_STATE_ALERTS_REG EN_CHARGER_STATE_ALERTS_REG
 *  @ingroup LTC4162-LADM_register_map
 *  @brief EN_CHARGER_STATE_ALERTS_REG Register
 *
 * | 15:13 |                               12 |                         11 | 10:9 |                          8 |                  7 |                     6 |                  5 |                   4 |                      3 |                        2 |                          1 |                        0 |
 * |:-----:|:--------------------------------:|:--------------------------:|:----:|:--------------------------:|:------------------:|:---------------------:|:------------------:|:-------------------:|:----------------------:|:------------------------:|:--------------------------:|:------------------------:|
 * |   n/a | EN_BAT_DETECT_FAILED_FAULT_ALERT | EN_BATTERY_DETECTION_ALERT |  n/a | EN_CHARGER_SUSPENDED_ALERT | EN_PRECHARGE_ALERT | EN_CC_CV_CHARGE_ALERT | EN_NTC_PAUSE_ALERT | EN_TIMER_TERM_ALERT | EN_C_OVER_X_TERM_ALERT | EN_MAX_CHARGE_TIME_ALERT | EN_BAT_MISSING_FAULT_ALERT | EN_BAT_SHORT_FAULT_ALERT |
 *
 * Enable charger state notification via SMBALERT
 *   - CommandCode: 0x0E
 *   - Contains Bit Fields:
 *     + @ref LTC4162_EN_BAT_DETECT_FAILED_FAULT_ALERT "EN_BAT_DETECT_FAILED_FAULT_ALERT" : Interrupt request that causes an SMBALERT upon bat_detect_failed_fault_alert as indicated by bat_detect_failed_fault due to an inability to source power to the battery during battery detection testing (usually due to either iin_limit_active or vin_uvcl_active).
 *     + @ref LTC4162_EN_BATTERY_DETECTION_ALERT "EN_BATTERY_DETECTION_ALERT" : Interrupt request that causes an SMBALERT upon battery_detection_alert as indicated by battery_detection due to the LTC4162 entering battery detection testing.
 *     + @ref LTC4162_EN_CHARGER_SUSPENDED_ALERT "EN_CHARGER_SUSPENDED_ALERT" : Interrupt request that causes an SMBALERT upon charger_suspended_alert as indicated by charger_suspended whereby battery charging is terminated due to suspend_charger or thermistor_voltage out of jeita_t1 - jeita_t6 range.
 *     + @ref LTC4162_EN_PRECHARGE_ALERT "EN_PRECHARGE_ALERT" : Interrupt request that causes an SMBALERT upon precharge_alert as indicated by precharge denoting the onset of the precharge phase of a battery charging cycle.
 *     + @ref LTC4162_EN_CC_CV_CHARGE_ALERT "EN_CC_CV_CHARGE_ALERT" : Interrupt request that causes an SMBALERT upon cc_cv_charge_alert as indicated by cc_cv_charge denoting the onset of the constant current / constant voltage phase of a battery charging cycle.
 *     + @ref LTC4162_EN_NTC_PAUSE_ALERT "EN_NTC_PAUSE_ALERT" : Interrupt request that causes an SMBALERT upon ntc_pause_alert as indicated by ntc_pause whereby a battery charge cycle is interrupted due to thermistor_voltage out of range as set by the jeita_t1 through jeita_t6 values.
 *     + @ref LTC4162_EN_TIMER_TERM_ALERT "EN_TIMER_TERM_ALERT" : Interrupt request that causes an SMBALERT upon timer_term_alert as indicated by timer_term whereby a battery charge cycle terminates due to tcvtimer reaching max_cv_time, the maximum time allowed in constant_voltage mode.
 *     + @ref LTC4162_EN_C_OVER_X_TERM_ALERT "EN_C_OVER_X_TERM_ALERT" : Interrupt request that causes an SMBALERT upon c_over_x_term_alert as indicated by c_over_x_term whereby a battery charge cycle terminates due to ibat dropping below the c_over_x_threshold.
 *     + @ref LTC4162_EN_MAX_CHARGE_TIME_ALERT "EN_MAX_CHARGE_TIME_ALERT" : Interrupt request that causes an SMBALERT upon max_charge_time_fault_alert as indicated by max_charge_time_fault whereby charging has terminated due to tchargetimer reaching max_charge_time.
 *     + @ref LTC4162_EN_BAT_MISSING_FAULT_ALERT "EN_BAT_MISSING_FAULT_ALERT" : Interrupt request that causes an SMBALERT upon bat_missing_fault_alert as indicated by bat_missing_fault whereby charging is prohibited if no battery is detected during the battery presence detection phase at the beginning of a charge cycle.
 *     + @ref LTC4162_EN_BAT_SHORT_FAULT_ALERT "EN_BAT_SHORT_FAULT_ALERT" : Interrupt request that causes an SMBALERT upon bat_short_fault_alert as indicated by bat_short_fault whereby charging is prohibited if a shorted battery is detected during the battery presence detection phase at the beginning of a charge cycle.
*/

//!@{
#define LTC4162_EN_CHARGER_STATE_ALERTS_REG_SUBADDR 0x0Eu
#define LTC4162_EN_CHARGER_STATE_ALERTS_REG (0u << 12 | (LTC4162_WORD_SIZE - 1) << 8 | LTC4162_EN_CHARGER_STATE_ALERTS_REG_SUBADDR)
//!@}
/*! @defgroup LTC4162_EN_BAT_DETECT_FAILED_FAULT_ALERT EN_BAT_DETECT_FAILED_FAULT_ALERT
 *  @ingroup LTC4162-LADM_register_map
 *  @brief EN_BAT_DETECT_FAILED_FAULT_ALERT Bit Field
 *
 *  Interrupt request that causes an SMBALERT upon bat_detect_failed_fault_alert as indicated by bat_detect_failed_fault due to an inability to source power to the battery during battery detection testing (usually due to either iin_limit_active or vin_uvcl_active).
 *   - Register: @ref LTC4162_EN_CHARGER_STATE_ALERTS_REG "EN_CHARGER_STATE_ALERTS_REG"
 *   - CommandCode: 0x0E
 *   - Size: 1
 *   - Offset: 12
 *   - MSB: 12
 *   - MASK: 0x1000
 *   - Access: R/W
 *   - Default: 0
 */
//!@{
#define LTC4162_EN_BAT_DETECT_FAILED_FAULT_ALERT_SUBADDR LTC4162_EN_CHARGER_STATE_ALERTS_REG_SUBADDR //!< @ref LTC4162_EN_BAT_DETECT_FAILED_FAULT_ALERT "EN_BAT_DETECT_FAILED_FAULT_ALERT"
#define LTC4162_EN_BAT_DETECT_FAILED_FAULT_ALERT_SIZE 1u
#define LTC4162_EN_BAT_DETECT_FAILED_FAULT_ALERT_OFFSET 12u
#define LTC4162_EN_BAT_DETECT_FAILED_FAULT_ALERT_MASK 0x1000u
#define LTC4162_EN_BAT_DETECT_FAILED_FAULT_ALERT_DEFAULT 0u
#define LTC4162_EN_BAT_DETECT_FAILED_FAULT_ALERT_DECODE(register_data) (((register_data) & LTC4162_EN_BAT_DETECT_FAILED_FAULT_ALERT_MASK) >> LTC4162_EN_BAT_DETECT_FAILED_FAULT_ALERT_OFFSET)
#define LTC4162_EN_BAT_DETECT_FAILED_FAULT_ALERT (LTC4162_EN_BAT_DETECT_FAILED_FAULT_ALERT_OFFSET << 12 | (LTC4162_EN_BAT_DETECT_FAILED_FAULT_ALERT_SIZE - 1) << 8 | LTC4162_EN_BAT_DETECT_FAILED_FAULT_ALERT_SUBADDR)
//!@}
/*! @defgroup LTC4162_EN_BATTERY_DETECTION_ALERT EN_BATTERY_DETECTION_ALERT
 *  @ingroup LTC4162-LADM_register_map
 *  @brief EN_BATTERY_DETECTION_ALERT Bit Field
 *
 *  Interrupt request that causes an SMBALERT upon battery_detection_alert as indicated by battery_detection due to the LTC4162 entering battery detection testing.
 *   - Register: @ref LTC4162_EN_CHARGER_STATE_ALERTS_REG "EN_CHARGER_STATE_ALERTS_REG"
 *   - CommandCode: 0x0E
 *   - Size: 1
 *   - Offset: 11
 *   - MSB: 11
 *   - MASK: 0x0800
 *   - Access: R/W
 *   - Default: 0
 */
//!@{
#define LTC4162_EN_BATTERY_DETECTION_ALERT_SUBADDR LTC4162_EN_CHARGER_STATE_ALERTS_REG_SUBADDR //!< @ref LTC4162_EN_BATTERY_DETECTION_ALERT "EN_BATTERY_DETECTION_ALERT"
#define LTC4162_EN_BATTERY_DETECTION_ALERT_SIZE 1u
#define LTC4162_EN_BATTERY_DETECTION_ALERT_OFFSET 11u
#define LTC4162_EN_BATTERY_DETECTION_ALERT_MASK 0x0800u
#define LTC4162_EN_BATTERY_DETECTION_ALERT_DEFAULT 0u
#define LTC4162_EN_BATTERY_DETECTION_ALERT_DECODE(register_data) (((register_data) & LTC4162_EN_BATTERY_DETECTION_ALERT_MASK) >> LTC4162_EN_BATTERY_DETECTION_ALERT_OFFSET)
#define LTC4162_EN_BATTERY_DETECTION_ALERT (LTC4162_EN_BATTERY_DETECTION_ALERT_OFFSET << 12 | (LTC4162_EN_BATTERY_DETECTION_ALERT_SIZE - 1) << 8 | LTC4162_EN_BATTERY_DETECTION_ALERT_SUBADDR)
//!@}
/*! @defgroup LTC4162_EN_CHARGER_SUSPENDED_ALERT EN_CHARGER_SUSPENDED_ALERT
 *  @ingroup LTC4162-LADM_register_map
 *  @brief EN_CHARGER_SUSPENDED_ALERT Bit Field
 *
 *  Interrupt request that causes an SMBALERT upon charger_suspended_alert as indicated by charger_suspended whereby battery charging is terminated due to suspend_charger or thermistor_voltage out of jeita_t1 - jeita_t6 range.
 *   - Register: @ref LTC4162_EN_CHARGER_STATE_ALERTS_REG "EN_CHARGER_STATE_ALERTS_REG"
 *   - CommandCode: 0x0E
 *   - Size: 1
 *   - Offset: 8
 *   - MSB: 8
 *   - MASK: 0x0100
 *   - Access: R/W
 *   - Default: 0
 */
//!@{
#define LTC4162_EN_CHARGER_SUSPENDED_ALERT_SUBADDR LTC4162_EN_CHARGER_STATE_ALERTS_REG_SUBADDR //!< @ref LTC4162_EN_CHARGER_SUSPENDED_ALERT "EN_CHARGER_SUSPENDED_ALERT"
#define LTC4162_EN_CHARGER_SUSPENDED_ALERT_SIZE 1u
#define LTC4162_EN_CHARGER_SUSPENDED_ALERT_OFFSET 8u
#define LTC4162_EN_CHARGER_SUSPENDED_ALERT_MASK 0x0100u
#define LTC4162_EN_CHARGER_SUSPENDED_ALERT_DEFAULT 0u
#define LTC4162_EN_CHARGER_SUSPENDED_ALERT_DECODE(register_data) (((register_data) & LTC4162_EN_CHARGER_SUSPENDED_ALERT_MASK) >> LTC4162_EN_CHARGER_SUSPENDED_ALERT_OFFSET)
#define LTC4162_EN_CHARGER_SUSPENDED_ALERT (LTC4162_EN_CHARGER_SUSPENDED_ALERT_OFFSET << 12 | (LTC4162_EN_CHARGER_SUSPENDED_ALERT_SIZE - 1) << 8 | LTC4162_EN_CHARGER_SUSPENDED_ALERT_SUBADDR)
//!@}
/*! @defgroup LTC4162_EN_PRECHARGE_ALERT EN_PRECHARGE_ALERT
 *  @ingroup LTC4162-LADM_register_map
 *  @brief EN_PRECHARGE_ALERT Bit Field
 *
 *  Interrupt request that causes an SMBALERT upon precharge_alert as indicated by precharge denoting the onset of the precharge phase of a battery charging cycle.
 *   - Register: @ref LTC4162_EN_CHARGER_STATE_ALERTS_REG "EN_CHARGER_STATE_ALERTS_REG"
 *   - CommandCode: 0x0E
 *   - Size: 1
 *   - Offset: 7
 *   - MSB: 7
 *   - MASK: 0x0080
 *   - Access: R/W
 *   - Default: 0
 */
//!@{
#define LTC4162_EN_PRECHARGE_ALERT_SUBADDR LTC4162_EN_CHARGER_STATE_ALERTS_REG_SUBADDR //!< @ref LTC4162_EN_PRECHARGE_ALERT "EN_PRECHARGE_ALERT"
#define LTC4162_EN_PRECHARGE_ALERT_SIZE 1u
#define LTC4162_EN_PRECHARGE_ALERT_OFFSET 7u
#define LTC4162_EN_PRECHARGE_ALERT_MASK 0x0080u
#define LTC4162_EN_PRECHARGE_ALERT_DEFAULT 0u
#define LTC4162_EN_PRECHARGE_ALERT_DECODE(register_data) (((register_data) & LTC4162_EN_PRECHARGE_ALERT_MASK) >> LTC4162_EN_PRECHARGE_ALERT_OFFSET)
#define LTC4162_EN_PRECHARGE_ALERT (LTC4162_EN_PRECHARGE_ALERT_OFFSET << 12 | (LTC4162_EN_PRECHARGE_ALERT_SIZE - 1) << 8 | LTC4162_EN_PRECHARGE_ALERT_SUBADDR)
//!@}
/*! @defgroup LTC4162_EN_CC_CV_CHARGE_ALERT EN_CC_CV_CHARGE_ALERT
 *  @ingroup LTC4162-LADM_register_map
 *  @brief EN_CC_CV_CHARGE_ALERT Bit Field
 *
 *  Interrupt request that causes an SMBALERT upon cc_cv_charge_alert as indicated by cc_cv_charge denoting the onset of the constant current / constant voltage phase of a battery charging cycle.
 *   - Register: @ref LTC4162_EN_CHARGER_STATE_ALERTS_REG "EN_CHARGER_STATE_ALERTS_REG"
 *   - CommandCode: 0x0E
 *   - Size: 1
 *   - Offset: 6
 *   - MSB: 6
 *   - MASK: 0x0040
 *   - Access: R/W
 *   - Default: 0
 */
//!@{
#define LTC4162_EN_CC_CV_CHARGE_ALERT_SUBADDR LTC4162_EN_CHARGER_STATE_ALERTS_REG_SUBADDR //!< @ref LTC4162_EN_CC_CV_CHARGE_ALERT "EN_CC_CV_CHARGE_ALERT"
#define LTC4162_EN_CC_CV_CHARGE_ALERT_SIZE 1u
#define LTC4162_EN_CC_CV_CHARGE_ALERT_OFFSET 6u
#define LTC4162_EN_CC_CV_CHARGE_ALERT_MASK 0x0040u
#define LTC4162_EN_CC_CV_CHARGE_ALERT_DEFAULT 0u
#define LTC4162_EN_CC_CV_CHARGE_ALERT_DECODE(register_data) (((register_data) & LTC4162_EN_CC_CV_CHARGE_ALERT_MASK) >> LTC4162_EN_CC_CV_CHARGE_ALERT_OFFSET)
#define LTC4162_EN_CC_CV_CHARGE_ALERT (LTC4162_EN_CC_CV_CHARGE_ALERT_OFFSET << 12 | (LTC4162_EN_CC_CV_CHARGE_ALERT_SIZE - 1) << 8 | LTC4162_EN_CC_CV_CHARGE_ALERT_SUBADDR)
//!@}
/*! @defgroup LTC4162_EN_NTC_PAUSE_ALERT EN_NTC_PAUSE_ALERT
 *  @ingroup LTC4162-LADM_register_map
 *  @brief EN_NTC_PAUSE_ALERT Bit Field
 *
 *  Interrupt request that causes an SMBALERT upon ntc_pause_alert as indicated by ntc_pause whereby a battery charge cycle is interrupted due to thermistor_voltage out of range as set by the jeita_t1 through jeita_t6 values.
 *   - Register: @ref LTC4162_EN_CHARGER_STATE_ALERTS_REG "EN_CHARGER_STATE_ALERTS_REG"
 *   - CommandCode: 0x0E
 *   - Size: 1
 *   - Offset: 5
 *   - MSB: 5
 *   - MASK: 0x0020
 *   - Access: R/W
 *   - Default: 0
 */
//!@{
#define LTC4162_EN_NTC_PAUSE_ALERT_SUBADDR LTC4162_EN_CHARGER_STATE_ALERTS_REG_SUBADDR //!< @ref LTC4162_EN_NTC_PAUSE_ALERT "EN_NTC_PAUSE_ALERT"
#define LTC4162_EN_NTC_PAUSE_ALERT_SIZE 1u
#define LTC4162_EN_NTC_PAUSE_ALERT_OFFSET 5u
#define LTC4162_EN_NTC_PAUSE_ALERT_MASK 0x0020u
#define LTC4162_EN_NTC_PAUSE_ALERT_DEFAULT 0u
#define LTC4162_EN_NTC_PAUSE_ALERT_DECODE(register_data) (((register_data) & LTC4162_EN_NTC_PAUSE_ALERT_MASK) >> LTC4162_EN_NTC_PAUSE_ALERT_OFFSET)
#define LTC4162_EN_NTC_PAUSE_ALERT (LTC4162_EN_NTC_PAUSE_ALERT_OFFSET << 12 | (LTC4162_EN_NTC_PAUSE_ALERT_SIZE - 1) << 8 | LTC4162_EN_NTC_PAUSE_ALERT_SUBADDR)
//!@}
/*! @defgroup LTC4162_EN_TIMER_TERM_ALERT EN_TIMER_TERM_ALERT
 *  @ingroup LTC4162-LADM_register_map
 *  @brief EN_TIMER_TERM_ALERT Bit Field
 *
 *  Interrupt request that causes an SMBALERT upon timer_term_alert as indicated by timer_term whereby a battery charge cycle terminates due to tcvtimer reaching max_cv_time, the maximum time allowed in constant_voltage mode.
 *   - Register: @ref LTC4162_EN_CHARGER_STATE_ALERTS_REG "EN_CHARGER_STATE_ALERTS_REG"
 *   - CommandCode: 0x0E
 *   - Size: 1
 *   - Offset: 4
 *   - MSB: 4
 *   - MASK: 0x0010
 *   - Access: R/W
 *   - Default: 0
 */
//!@{
#define LTC4162_EN_TIMER_TERM_ALERT_SUBADDR LTC4162_EN_CHARGER_STATE_ALERTS_REG_SUBADDR //!< @ref LTC4162_EN_TIMER_TERM_ALERT "EN_TIMER_TERM_ALERT"
#define LTC4162_EN_TIMER_TERM_ALERT_SIZE 1u
#define LTC4162_EN_TIMER_TERM_ALERT_OFFSET 4u
#define LTC4162_EN_TIMER_TERM_ALERT_MASK 0x0010u
#define LTC4162_EN_TIMER_TERM_ALERT_DEFAULT 0u
#define LTC4162_EN_TIMER_TERM_ALERT_DECODE(register_data) (((register_data) & LTC4162_EN_TIMER_TERM_ALERT_MASK) >> LTC4162_EN_TIMER_TERM_ALERT_OFFSET)
#define LTC4162_EN_TIMER_TERM_ALERT (LTC4162_EN_TIMER_TERM_ALERT_OFFSET << 12 | (LTC4162_EN_TIMER_TERM_ALERT_SIZE - 1) << 8 | LTC4162_EN_TIMER_TERM_ALERT_SUBADDR)
//!@}
/*! @defgroup LTC4162_EN_C_OVER_X_TERM_ALERT EN_C_OVER_X_TERM_ALERT
 *  @ingroup LTC4162-LADM_register_map
 *  @brief EN_C_OVER_X_TERM_ALERT Bit Field
 *
 *  Interrupt request that causes an SMBALERT upon c_over_x_term_alert as indicated by c_over_x_term whereby a battery charge cycle terminates due to ibat dropping below the c_over_x_threshold.
 *   - Register: @ref LTC4162_EN_CHARGER_STATE_ALERTS_REG "EN_CHARGER_STATE_ALERTS_REG"
 *   - CommandCode: 0x0E
 *   - Size: 1
 *   - Offset: 3
 *   - MSB: 3
 *   - MASK: 0x0008
 *   - Access: R/W
 *   - Default: 0
 */
//!@{
#define LTC4162_EN_C_OVER_X_TERM_ALERT_SUBADDR LTC4162_EN_CHARGER_STATE_ALERTS_REG_SUBADDR //!< @ref LTC4162_EN_C_OVER_X_TERM_ALERT "EN_C_OVER_X_TERM_ALERT"
#define LTC4162_EN_C_OVER_X_TERM_ALERT_SIZE 1u
#define LTC4162_EN_C_OVER_X_TERM_ALERT_OFFSET 3u
#define LTC4162_EN_C_OVER_X_TERM_ALERT_MASK 0x0008u
#define LTC4162_EN_C_OVER_X_TERM_ALERT_DEFAULT 0u
#define LTC4162_EN_C_OVER_X_TERM_ALERT_DECODE(register_data) (((register_data) & LTC4162_EN_C_OVER_X_TERM_ALERT_MASK) >> LTC4162_EN_C_OVER_X_TERM_ALERT_OFFSET)
#define LTC4162_EN_C_OVER_X_TERM_ALERT (LTC4162_EN_C_OVER_X_TERM_ALERT_OFFSET << 12 | (LTC4162_EN_C_OVER_X_TERM_ALERT_SIZE - 1) << 8 | LTC4162_EN_C_OVER_X_TERM_ALERT_SUBADDR)
//!@}
/*! @defgroup LTC4162_EN_MAX_CHARGE_TIME_ALERT EN_MAX_CHARGE_TIME_ALERT
 *  @ingroup LTC4162-LADM_register_map
 *  @brief EN_MAX_CHARGE_TIME_ALERT Bit Field
 *
 *  Interrupt request that causes an SMBALERT upon max_charge_time_fault_alert as indicated by max_charge_time_fault whereby charging has terminated due to tchargetimer reaching max_charge_time.
 *   - Register: @ref LTC4162_EN_CHARGER_STATE_ALERTS_REG "EN_CHARGER_STATE_ALERTS_REG"
 *   - CommandCode: 0x0E
 *   - Size: 1
 *   - Offset: 2
 *   - MSB: 2
 *   - MASK: 0x0004
 *   - Access: R/W
 *   - Default: 0
 */
//!@{
#define LTC4162_EN_MAX_CHARGE_TIME_ALERT_SUBADDR LTC4162_EN_CHARGER_STATE_ALERTS_REG_SUBADDR //!< @ref LTC4162_EN_MAX_CHARGE_TIME_ALERT "EN_MAX_CHARGE_TIME_ALERT"
#define LTC4162_EN_MAX_CHARGE_TIME_ALERT_SIZE 1u
#define LTC4162_EN_MAX_CHARGE_TIME_ALERT_OFFSET 2u
#define LTC4162_EN_MAX_CHARGE_TIME_ALERT_MASK 0x0004u
#define LTC4162_EN_MAX_CHARGE_TIME_ALERT_DEFAULT 0u
#define LTC4162_EN_MAX_CHARGE_TIME_ALERT_DECODE(register_data) (((register_data) & LTC4162_EN_MAX_CHARGE_TIME_ALERT_MASK) >> LTC4162_EN_MAX_CHARGE_TIME_ALERT_OFFSET)
#define LTC4162_EN_MAX_CHARGE_TIME_ALERT (LTC4162_EN_MAX_CHARGE_TIME_ALERT_OFFSET << 12 | (LTC4162_EN_MAX_CHARGE_TIME_ALERT_SIZE - 1) << 8 | LTC4162_EN_MAX_CHARGE_TIME_ALERT_SUBADDR)
//!@}
/*! @defgroup LTC4162_EN_BAT_MISSING_FAULT_ALERT EN_BAT_MISSING_FAULT_ALERT
 *  @ingroup LTC4162-LADM_register_map
 *  @brief EN_BAT_MISSING_FAULT_ALERT Bit Field
 *
 *  Interrupt request that causes an SMBALERT upon bat_missing_fault_alert as indicated by bat_missing_fault whereby charging is prohibited if no battery is detected during the battery presence detection phase at the beginning of a charge cycle.
 *   - Register: @ref LTC4162_EN_CHARGER_STATE_ALERTS_REG "EN_CHARGER_STATE_ALERTS_REG"
 *   - CommandCode: 0x0E
 *   - Size: 1
 *   - Offset: 1
 *   - MSB: 1
 *   - MASK: 0x0002
 *   - Access: R/W
 *   - Default: 0
 */
//!@{
#define LTC4162_EN_BAT_MISSING_FAULT_ALERT_SUBADDR LTC4162_EN_CHARGER_STATE_ALERTS_REG_SUBADDR //!< @ref LTC4162_EN_BAT_MISSING_FAULT_ALERT "EN_BAT_MISSING_FAULT_ALERT"
#define LTC4162_EN_BAT_MISSING_FAULT_ALERT_SIZE 1u
#define LTC4162_EN_BAT_MISSING_FAULT_ALERT_OFFSET 1u
#define LTC4162_EN_BAT_MISSING_FAULT_ALERT_MASK 0x0002u
#define LTC4162_EN_BAT_MISSING_FAULT_ALERT_DEFAULT 0u
#define LTC4162_EN_BAT_MISSING_FAULT_ALERT_DECODE(register_data) (((register_data) & LTC4162_EN_BAT_MISSING_FAULT_ALERT_MASK) >> LTC4162_EN_BAT_MISSING_FAULT_ALERT_OFFSET)
#define LTC4162_EN_BAT_MISSING_FAULT_ALERT (LTC4162_EN_BAT_MISSING_FAULT_ALERT_OFFSET << 12 | (LTC4162_EN_BAT_MISSING_FAULT_ALERT_SIZE - 1) << 8 | LTC4162_EN_BAT_MISSING_FAULT_ALERT_SUBADDR)
//!@}
/*! @defgroup LTC4162_EN_BAT_SHORT_FAULT_ALERT EN_BAT_SHORT_FAULT_ALERT
 *  @ingroup LTC4162-LADM_register_map
 *  @brief EN_BAT_SHORT_FAULT_ALERT Bit Field
 *
 *  Interrupt request that causes an SMBALERT upon bat_short_fault_alert as indicated by bat_short_fault whereby charging is prohibited if a shorted battery is detected during the battery presence detection phase at the beginning of a charge cycle.
 *   - Register: @ref LTC4162_EN_CHARGER_STATE_ALERTS_REG "EN_CHARGER_STATE_ALERTS_REG"
 *   - CommandCode: 0x0E
 *   - Size: 1
 *   - Offset: 0
 *   - MSB: 0
 *   - MASK: 0x0001
 *   - Access: R/W
 *   - Default: 0
 */
//!@{
#define LTC4162_EN_BAT_SHORT_FAULT_ALERT_SUBADDR LTC4162_EN_CHARGER_STATE_ALERTS_REG_SUBADDR //!< @ref LTC4162_EN_BAT_SHORT_FAULT_ALERT "EN_BAT_SHORT_FAULT_ALERT"
#define LTC4162_EN_BAT_SHORT_FAULT_ALERT_SIZE 1u
#define LTC4162_EN_BAT_SHORT_FAULT_ALERT_OFFSET 0u
#define LTC4162_EN_BAT_SHORT_FAULT_ALERT_MASK 0x0001u
#define LTC4162_EN_BAT_SHORT_FAULT_ALERT_DEFAULT 0u
#define LTC4162_EN_BAT_SHORT_FAULT_ALERT_DECODE(register_data) (((register_data) & LTC4162_EN_BAT_SHORT_FAULT_ALERT_MASK) >> LTC4162_EN_BAT_SHORT_FAULT_ALERT_OFFSET)
#define LTC4162_EN_BAT_SHORT_FAULT_ALERT (LTC4162_EN_BAT_SHORT_FAULT_ALERT_OFFSET << 12 | (LTC4162_EN_BAT_SHORT_FAULT_ALERT_SIZE - 1) << 8 | LTC4162_EN_BAT_SHORT_FAULT_ALERT_SUBADDR)
//!@}

/*! @defgroup LTC4162_EN_CHARGE_STATUS_ALERTS_REG EN_CHARGE_STATUS_ALERTS_REG
 *  @ingroup LTC4162-LADM_register_map
 *  @brief EN_CHARGE_STATUS_ALERTS_REG Register
 *
 * | 15:6 |                        5 |                           4 |                        3 |                         2 |                         1 |                         0 |
 * |:----:|:------------------------:|:---------------------------:|:------------------------:|:-------------------------:|:-------------------------:|:-------------------------:|
 * |  n/a | EN_ILIM_REG_ACTIVE_ALERT | EN_THERMAL_REG_ACTIVE_ALERT | EN_VIN_UVCL_ACTIVE_ALERT | EN_IIN_LIMIT_ACTIVE_ALERT | EN_CONSTANT_CURRENT_ALERT | EN_CONSTANT_VOLTAGE_ALERT |
 *
 * Enable charge status notification via SMBALERT
 *   - CommandCode: 0x0F
 *   - Contains Bit Fields:
 *     + @ref LTC4162_EN_ILIM_REG_ACTIVE_ALERT "EN_ILIM_REG_ACTIVE_ALERT" : Interrupt request that causes an ilim_reg_active_alert SMBALERT upon ilim_reg_active (VCSP-VCSN greater than 45mV). May indicates that the switching regulator is currently controlling power delivery based on a safety current limit. This should not occur under normal conditions and is likely the result of a circuit board fault. Alternately indicates that the switching regulator is in dropout (near 100% duty cycle) and is not regulating on any feedback control loop.
 *     + @ref LTC4162_EN_THERMAL_REG_ACTIVE_ALERT "EN_THERMAL_REG_ACTIVE_ALERT" : Interrupt request that causes a thermal_reg_active_alert SMBALERT upon thermal_reg_active indicating that the icharge_dac is being dialed back to reduce internal die heating.
 *     + @ref LTC4162_EN_VIN_UVCL_ACTIVE_ALERT "EN_VIN_UVCL_ACTIVE_ALERT" : Interrupt request that causes a vin_uvcl_active_alert SMBALERT upon vin_uvcl_active indicating that the undervoltage regulation loop has taken control of the switching regulator.
 *     + @ref LTC4162_EN_IIN_LIMIT_ACTIVE_ALERT "EN_IIN_LIMIT_ACTIVE_ALERT" : Interrupt request that causes a iin_limit_active_alert SMBALERT upon iin_limit_active indicating that the input current regulation loop has taken control of the switching regulator.
 *     + @ref LTC4162_EN_CONSTANT_CURRENT_ALERT "EN_CONSTANT_CURRENT_ALERT" : Interrupt request that causes a constant_current_alert SMBALERT upon constant_current indicating that the battery charger constant current regulation loop has taken control of the switching regulator.
 *     + @ref LTC4162_EN_CONSTANT_VOLTAGE_ALERT "EN_CONSTANT_VOLTAGE_ALERT" : Interrupt request that causes a constant_voltage_alert SMBALERT upon constant_voltage indicating that the battery charger constant voltage regulation loop has taken control of the switching regulator.
*/

//!@{
#define LTC4162_EN_CHARGE_STATUS_ALERTS_REG_SUBADDR 0x0Fu
#define LTC4162_EN_CHARGE_STATUS_ALERTS_REG (0u << 12 | (LTC4162_WORD_SIZE - 1) << 8 | LTC4162_EN_CHARGE_STATUS_ALERTS_REG_SUBADDR)
//!@}
/*! @defgroup LTC4162_EN_ILIM_REG_ACTIVE_ALERT EN_ILIM_REG_ACTIVE_ALERT
 *  @ingroup LTC4162-LADM_register_map
 *  @brief EN_ILIM_REG_ACTIVE_ALERT Bit Field
 *
 *  Interrupt request that causes an ilim_reg_active_alert SMBALERT upon ilim_reg_active (VCSP-VCSN greater than 45mV). May indicates that the switching regulator is currently controlling power delivery based on a safety current limit. This should not occur under normal conditions and is likely the result of a circuit board fault. Alternately indicates that the switching regulator is in dropout (near 100% duty cycle) and is not regulating on any feedback control loop.
 *   - Register: @ref LTC4162_EN_CHARGE_STATUS_ALERTS_REG "EN_CHARGE_STATUS_ALERTS_REG"
 *   - CommandCode: 0x0F
 *   - Size: 1
 *   - Offset: 5
 *   - MSB: 5
 *   - MASK: 0x0020
 *   - Access: R/W
 *   - Default: 0
 */
//!@{
#define LTC4162_EN_ILIM_REG_ACTIVE_ALERT_SUBADDR LTC4162_EN_CHARGE_STATUS_ALERTS_REG_SUBADDR //!< @ref LTC4162_EN_ILIM_REG_ACTIVE_ALERT "EN_ILIM_REG_ACTIVE_ALERT"
#define LTC4162_EN_ILIM_REG_ACTIVE_ALERT_SIZE 1u
#define LTC4162_EN_ILIM_REG_ACTIVE_ALERT_OFFSET 5u
#define LTC4162_EN_ILIM_REG_ACTIVE_ALERT_MASK 0x0020u
#define LTC4162_EN_ILIM_REG_ACTIVE_ALERT_DEFAULT 0u
#define LTC4162_EN_ILIM_REG_ACTIVE_ALERT_DECODE(register_data) (((register_data) & LTC4162_EN_ILIM_REG_ACTIVE_ALERT_MASK) >> LTC4162_EN_ILIM_REG_ACTIVE_ALERT_OFFSET)
#define LTC4162_EN_ILIM_REG_ACTIVE_ALERT (LTC4162_EN_ILIM_REG_ACTIVE_ALERT_OFFSET << 12 | (LTC4162_EN_ILIM_REG_ACTIVE_ALERT_SIZE - 1) << 8 | LTC4162_EN_ILIM_REG_ACTIVE_ALERT_SUBADDR)
//!@}
/*! @defgroup LTC4162_EN_THERMAL_REG_ACTIVE_ALERT EN_THERMAL_REG_ACTIVE_ALERT
 *  @ingroup LTC4162-LADM_register_map
 *  @brief EN_THERMAL_REG_ACTIVE_ALERT Bit Field
 *
 *  Interrupt request that causes a thermal_reg_active_alert SMBALERT upon thermal_reg_active indicating that the icharge_dac is being dialed back to reduce internal die heating.
 *   - Register: @ref LTC4162_EN_CHARGE_STATUS_ALERTS_REG "EN_CHARGE_STATUS_ALERTS_REG"
 *   - CommandCode: 0x0F
 *   - Size: 1
 *   - Offset: 4
 *   - MSB: 4
 *   - MASK: 0x0010
 *   - Access: R/W
 *   - Default: 0
 */
//!@{
#define LTC4162_EN_THERMAL_REG_ACTIVE_ALERT_SUBADDR LTC4162_EN_CHARGE_STATUS_ALERTS_REG_SUBADDR //!< @ref LTC4162_EN_THERMAL_REG_ACTIVE_ALERT "EN_THERMAL_REG_ACTIVE_ALERT"
#define LTC4162_EN_THERMAL_REG_ACTIVE_ALERT_SIZE 1u
#define LTC4162_EN_THERMAL_REG_ACTIVE_ALERT_OFFSET 4u
#define LTC4162_EN_THERMAL_REG_ACTIVE_ALERT_MASK 0x0010u
#define LTC4162_EN_THERMAL_REG_ACTIVE_ALERT_DEFAULT 0u
#define LTC4162_EN_THERMAL_REG_ACTIVE_ALERT_DECODE(register_data) (((register_data) & LTC4162_EN_THERMAL_REG_ACTIVE_ALERT_MASK) >> LTC4162_EN_THERMAL_REG_ACTIVE_ALERT_OFFSET)
#define LTC4162_EN_THERMAL_REG_ACTIVE_ALERT (LTC4162_EN_THERMAL_REG_ACTIVE_ALERT_OFFSET << 12 | (LTC4162_EN_THERMAL_REG_ACTIVE_ALERT_SIZE - 1) << 8 | LTC4162_EN_THERMAL_REG_ACTIVE_ALERT_SUBADDR)
//!@}
/*! @defgroup LTC4162_EN_VIN_UVCL_ACTIVE_ALERT EN_VIN_UVCL_ACTIVE_ALERT
 *  @ingroup LTC4162-LADM_register_map
 *  @brief EN_VIN_UVCL_ACTIVE_ALERT Bit Field
 *
 *  Interrupt request that causes a vin_uvcl_active_alert SMBALERT upon vin_uvcl_active indicating that the undervoltage regulation loop has taken control of the switching regulator.
 *   - Register: @ref LTC4162_EN_CHARGE_STATUS_ALERTS_REG "EN_CHARGE_STATUS_ALERTS_REG"
 *   - CommandCode: 0x0F
 *   - Size: 1
 *   - Offset: 3
 *   - MSB: 3
 *   - MASK: 0x0008
 *   - Access: R/W
 *   - Default: 0
 */
//!@{
#define LTC4162_EN_VIN_UVCL_ACTIVE_ALERT_SUBADDR LTC4162_EN_CHARGE_STATUS_ALERTS_REG_SUBADDR //!< @ref LTC4162_EN_VIN_UVCL_ACTIVE_ALERT "EN_VIN_UVCL_ACTIVE_ALERT"
#define LTC4162_EN_VIN_UVCL_ACTIVE_ALERT_SIZE 1u
#define LTC4162_EN_VIN_UVCL_ACTIVE_ALERT_OFFSET 3u
#define LTC4162_EN_VIN_UVCL_ACTIVE_ALERT_MASK 0x0008u
#define LTC4162_EN_VIN_UVCL_ACTIVE_ALERT_DEFAULT 0u
#define LTC4162_EN_VIN_UVCL_ACTIVE_ALERT_DECODE(register_data) (((register_data) & LTC4162_EN_VIN_UVCL_ACTIVE_ALERT_MASK) >> LTC4162_EN_VIN_UVCL_ACTIVE_ALERT_OFFSET)
#define LTC4162_EN_VIN_UVCL_ACTIVE_ALERT (LTC4162_EN_VIN_UVCL_ACTIVE_ALERT_OFFSET << 12 | (LTC4162_EN_VIN_UVCL_ACTIVE_ALERT_SIZE - 1) << 8 | LTC4162_EN_VIN_UVCL_ACTIVE_ALERT_SUBADDR)
//!@}
/*! @defgroup LTC4162_EN_IIN_LIMIT_ACTIVE_ALERT EN_IIN_LIMIT_ACTIVE_ALERT
 *  @ingroup LTC4162-LADM_register_map
 *  @brief EN_IIN_LIMIT_ACTIVE_ALERT Bit Field
 *
 *  Interrupt request that causes a iin_limit_active_alert SMBALERT upon iin_limit_active indicating that the input current regulation loop has taken control of the switching regulator.
 *   - Register: @ref LTC4162_EN_CHARGE_STATUS_ALERTS_REG "EN_CHARGE_STATUS_ALERTS_REG"
 *   - CommandCode: 0x0F
 *   - Size: 1
 *   - Offset: 2
 *   - MSB: 2
 *   - MASK: 0x0004
 *   - Access: R/W
 *   - Default: 0
 */
//!@{
#define LTC4162_EN_IIN_LIMIT_ACTIVE_ALERT_SUBADDR LTC4162_EN_CHARGE_STATUS_ALERTS_REG_SUBADDR //!< @ref LTC4162_EN_IIN_LIMIT_ACTIVE_ALERT "EN_IIN_LIMIT_ACTIVE_ALERT"
#define LTC4162_EN_IIN_LIMIT_ACTIVE_ALERT_SIZE 1u
#define LTC4162_EN_IIN_LIMIT_ACTIVE_ALERT_OFFSET 2u
#define LTC4162_EN_IIN_LIMIT_ACTIVE_ALERT_MASK 0x0004u
#define LTC4162_EN_IIN_LIMIT_ACTIVE_ALERT_DEFAULT 0u
#define LTC4162_EN_IIN_LIMIT_ACTIVE_ALERT_DECODE(register_data) (((register_data) & LTC4162_EN_IIN_LIMIT_ACTIVE_ALERT_MASK) >> LTC4162_EN_IIN_LIMIT_ACTIVE_ALERT_OFFSET)
#define LTC4162_EN_IIN_LIMIT_ACTIVE_ALERT (LTC4162_EN_IIN_LIMIT_ACTIVE_ALERT_OFFSET << 12 | (LTC4162_EN_IIN_LIMIT_ACTIVE_ALERT_SIZE - 1) << 8 | LTC4162_EN_IIN_LIMIT_ACTIVE_ALERT_SUBADDR)
//!@}
/*! @defgroup LTC4162_EN_CONSTANT_CURRENT_ALERT EN_CONSTANT_CURRENT_ALERT
 *  @ingroup LTC4162-LADM_register_map
 *  @brief EN_CONSTANT_CURRENT_ALERT Bit Field
 *
 *  Interrupt request that causes a constant_current_alert SMBALERT upon constant_current indicating that the battery charger constant current regulation loop has taken control of the switching regulator.
 *   - Register: @ref LTC4162_EN_CHARGE_STATUS_ALERTS_REG "EN_CHARGE_STATUS_ALERTS_REG"
 *   - CommandCode: 0x0F
 *   - Size: 1
 *   - Offset: 1
 *   - MSB: 1
 *   - MASK: 0x0002
 *   - Access: R/W
 *   - Default: 0
 */
//!@{
#define LTC4162_EN_CONSTANT_CURRENT_ALERT_SUBADDR LTC4162_EN_CHARGE_STATUS_ALERTS_REG_SUBADDR //!< @ref LTC4162_EN_CONSTANT_CURRENT_ALERT "EN_CONSTANT_CURRENT_ALERT"
#define LTC4162_EN_CONSTANT_CURRENT_ALERT_SIZE 1u
#define LTC4162_EN_CONSTANT_CURRENT_ALERT_OFFSET 1u
#define LTC4162_EN_CONSTANT_CURRENT_ALERT_MASK 0x0002u
#define LTC4162_EN_CONSTANT_CURRENT_ALERT_DEFAULT 0u
#define LTC4162_EN_CONSTANT_CURRENT_ALERT_DECODE(register_data) (((register_data) & LTC4162_EN_CONSTANT_CURRENT_ALERT_MASK) >> LTC4162_EN_CONSTANT_CURRENT_ALERT_OFFSET)
#define LTC4162_EN_CONSTANT_CURRENT_ALERT (LTC4162_EN_CONSTANT_CURRENT_ALERT_OFFSET << 12 | (LTC4162_EN_CONSTANT_CURRENT_ALERT_SIZE - 1) << 8 | LTC4162_EN_CONSTANT_CURRENT_ALERT_SUBADDR)
//!@}
/*! @defgroup LTC4162_EN_CONSTANT_VOLTAGE_ALERT EN_CONSTANT_VOLTAGE_ALERT
 *  @ingroup LTC4162-LADM_register_map
 *  @brief EN_CONSTANT_VOLTAGE_ALERT Bit Field
 *
 *  Interrupt request that causes a constant_voltage_alert SMBALERT upon constant_voltage indicating that the battery charger constant voltage regulation loop has taken control of the switching regulator.
 *   - Register: @ref LTC4162_EN_CHARGE_STATUS_ALERTS_REG "EN_CHARGE_STATUS_ALERTS_REG"
 *   - CommandCode: 0x0F
 *   - Size: 1
 *   - Offset: 0
 *   - MSB: 0
 *   - MASK: 0x0001
 *   - Access: R/W
 *   - Default: 0
 */
//!@{
#define LTC4162_EN_CONSTANT_VOLTAGE_ALERT_SUBADDR LTC4162_EN_CHARGE_STATUS_ALERTS_REG_SUBADDR //!< @ref LTC4162_EN_CONSTANT_VOLTAGE_ALERT "EN_CONSTANT_VOLTAGE_ALERT"
#define LTC4162_EN_CONSTANT_VOLTAGE_ALERT_SIZE 1u
#define LTC4162_EN_CONSTANT_VOLTAGE_ALERT_OFFSET 0u
#define LTC4162_EN_CONSTANT_VOLTAGE_ALERT_MASK 0x0001u
#define LTC4162_EN_CONSTANT_VOLTAGE_ALERT_DEFAULT 0u
#define LTC4162_EN_CONSTANT_VOLTAGE_ALERT_DECODE(register_data) (((register_data) & LTC4162_EN_CONSTANT_VOLTAGE_ALERT_MASK) >> LTC4162_EN_CONSTANT_VOLTAGE_ALERT_OFFSET)
#define LTC4162_EN_CONSTANT_VOLTAGE_ALERT (LTC4162_EN_CONSTANT_VOLTAGE_ALERT_OFFSET << 12 | (LTC4162_EN_CONSTANT_VOLTAGE_ALERT_SIZE - 1) << 8 | LTC4162_EN_CONSTANT_VOLTAGE_ALERT_SUBADDR)
//!@}

/*! @defgroup LTC4162_THERMAL_REG_START_TEMP_REG THERMAL_REG_START_TEMP_REG
 *  @ingroup LTC4162-LADM_register_map
 *  @brief THERMAL_REG_START_TEMP_REG Register
 *
 * |                   15:0 |
 * |:----------------------:|
 * | THERMAL_REG_START_TEMP |
 *
 *   - CommandCode: 0x10
 *   - Contains Bit Fields:
 *     + @ref LTC4162_THERMAL_REG_START_TEMP "THERMAL_REG_START_TEMP" : Signed number that sets the start of the temperature region for thermal regulation. To prevent overheating, a thermal regulation feedback loop utilizing die_temp sets an upper limit on icharge_dac following a linear gradient from full scale (31) to minimum scale (0) between thermal_reg_start_temp and thermal_reg_end_temp. The default value of 17897 corresponds to 120°C.
*/

//!@{
#define LTC4162_THERMAL_REG_START_TEMP_REG_SUBADDR 0x10u
#define LTC4162_THERMAL_REG_START_TEMP_REG (0u << 12 | (LTC4162_WORD_SIZE - 1) << 8 | LTC4162_THERMAL_REG_START_TEMP_REG_SUBADDR)
//!@}
/*! @defgroup LTC4162_THERMAL_REG_START_TEMP THERMAL_REG_START_TEMP
 *  @ingroup LTC4162-LADM_register_map
 *  @brief THERMAL_REG_START_TEMP Bit Field
 *
 *  Signed number that sets the start of the temperature region for thermal regulation. To prevent overheating, a thermal regulation feedback loop utilizing die_temp sets an upper limit on icharge_dac following a linear gradient from full scale (31) to minimum scale (0) between thermal_reg_start_temp and thermal_reg_end_temp. The default value of 17897 corresponds to 120°C.
 *   - Register: @ref LTC4162_THERMAL_REG_START_TEMP_REG "THERMAL_REG_START_TEMP_REG"
 *   - CommandCode: 0x10
 *   - Size: 16
 *   - Offset: 0
 *   - MSB: 15
 *   - MASK: 0xFFFF
 *   - Access: R/W
 *   - Default: 17897
 *   - Format: LTC4162_DIE_TEMP_FORMAT
 */
//!@{
#define LTC4162_THERMAL_REG_START_TEMP_SUBADDR LTC4162_THERMAL_REG_START_TEMP_REG_SUBADDR //!< @ref LTC4162_THERMAL_REG_START_TEMP "THERMAL_REG_START_TEMP"
#define LTC4162_THERMAL_REG_START_TEMP_SIZE 16u
#define LTC4162_THERMAL_REG_START_TEMP_OFFSET 0u
#define LTC4162_THERMAL_REG_START_TEMP_MASK 0xFFFFu
#define LTC4162_THERMAL_REG_START_TEMP_DEFAULT 17897u
#define LTC4162_THERMAL_REG_START_TEMP_DECODE(register_data) (register_data)
#define LTC4162_THERMAL_REG_START_TEMP (LTC4162_THERMAL_REG_START_TEMP_OFFSET << 12 | (LTC4162_THERMAL_REG_START_TEMP_SIZE - 1) << 8 | LTC4162_THERMAL_REG_START_TEMP_SUBADDR)
//!@}

/*! @defgroup LTC4162_THERMAL_REG_END_TEMP_REG THERMAL_REG_END_TEMP_REG
 *  @ingroup LTC4162-LADM_register_map
 *  @brief THERMAL_REG_END_TEMP_REG Register
 *
 * |                 15:0 |
 * |:--------------------:|
 * | THERMAL_REG_END_TEMP |
 *
 *   - CommandCode: 0x11
 *   - Contains Bit Fields:
 *     + @ref LTC4162_THERMAL_REG_END_TEMP "THERMAL_REG_END_TEMP" : Signed number that sets the end of the temperature region for thermal regulation. To prevent overheating, a thermal regulation feedback loop utilizing die_temp sets an upper limit on icharge_dac following a linear gradient from full scale (31) to minimum scale (0) between thermal_reg_start_temp and thermal_reg_end_temp. The default value of 18130 corresponds to 125°C.
*/

//!@{
#define LTC4162_THERMAL_REG_END_TEMP_REG_SUBADDR 0x11u
#define LTC4162_THERMAL_REG_END_TEMP_REG (0u << 12 | (LTC4162_WORD_SIZE - 1) << 8 | LTC4162_THERMAL_REG_END_TEMP_REG_SUBADDR)
//!@}
/*! @defgroup LTC4162_THERMAL_REG_END_TEMP THERMAL_REG_END_TEMP
 *  @ingroup LTC4162-LADM_register_map
 *  @brief THERMAL_REG_END_TEMP Bit Field
 *
 *  Signed number that sets the end of the temperature region for thermal regulation. To prevent overheating, a thermal regulation feedback loop utilizing die_temp sets an upper limit on icharge_dac following a linear gradient from full scale (31) to minimum scale (0) between thermal_reg_start_temp and thermal_reg_end_temp. The default value of 18130 corresponds to 125°C.
 *   - Register: @ref LTC4162_THERMAL_REG_END_TEMP_REG "THERMAL_REG_END_TEMP_REG"
 *   - CommandCode: 0x11
 *   - Size: 16
 *   - Offset: 0
 *   - MSB: 15
 *   - MASK: 0xFFFF
 *   - Access: R/W
 *   - Default: 18130
 *   - Format: LTC4162_DIE_TEMP_FORMAT
 */
//!@{
#define LTC4162_THERMAL_REG_END_TEMP_SUBADDR LTC4162_THERMAL_REG_END_TEMP_REG_SUBADDR //!< @ref LTC4162_THERMAL_REG_END_TEMP "THERMAL_REG_END_TEMP"
#define LTC4162_THERMAL_REG_END_TEMP_SIZE 16u
#define LTC4162_THERMAL_REG_END_TEMP_OFFSET 0u
#define LTC4162_THERMAL_REG_END_TEMP_MASK 0xFFFFu
#define LTC4162_THERMAL_REG_END_TEMP_DEFAULT 18130u
#define LTC4162_THERMAL_REG_END_TEMP_DECODE(register_data) (register_data)
#define LTC4162_THERMAL_REG_END_TEMP (LTC4162_THERMAL_REG_END_TEMP_OFFSET << 12 | (LTC4162_THERMAL_REG_END_TEMP_SIZE - 1) << 8 | LTC4162_THERMAL_REG_END_TEMP_SUBADDR)
//!@}

/*! @defgroup LTC4162_CONFIG_BITS_REG CONFIG_BITS_REG
 *  @ingroup LTC4162-LADM_register_map
 *  @brief CONFIG_BITS_REG Register
 *
 * | 15:6 |               5 |       4 |               3 |                  2 |       1 |
 * |:----:|:---------------:|:-------:|:---------------:|:------------------:|:-------:|
 * |  n/a | SUSPEND_CHARGER | RUN_BSR | TELEMETRY_SPEED | FORCE_TELEMETRY_ON | MPPT_EN |
 *
 * System configuration settings
 *   - CommandCode: 0x14
 *   - Contains Bit Fields:
 *     + @ref LTC4162_SUSPEND_CHARGER "SUSPEND_CHARGER" : Causes battery charging to be suspended. This setting should be used cautiously. For embedded battery systems where two wire interface communication relies on a minimum battery voltage, setting this bit could result in a deadlock that may require factory service to correct.
 *     + @ref LTC4162_RUN_BSR "RUN_BSR" : Causes the battery equivalent-series-resistance (bsr) measurement to be made as soon as a charge cycle starts or immediately if a charge cycle is already running.
 *     + @ref LTC4162_TELEMETRY_SPEED "TELEMETRY_SPEED" : Forces the telemetry system to take measurements at the higher rate of approximately once every 11ms whenever the telemetry system is on. When this bit is disabled, the telemetry system will slow down to about once every 5s to reduce power when not charging. Setting telemetry_speed to tel_high_speed in conjunction with force_telemetry_on with no input power available will increase battery drain.
 *     + @ref LTC4162_FORCE_TELEMETRY_ON "FORCE_TELEMETRY_ON" : Causes the telemetry system to operate at all times, including times when only battery power is available.
 *     + @ref LTC4162_MPPT_EN "MPPT_EN" : Causes the Maximum Power-Point Tracking algorithm to run. The maximum power point algorithm takes control of the input undervoltage regulation control loop via the input_undervoltage_dac to seek the optimum power-point for resistive sources such as a long cable or solar panel.
*/

//!@{
#define LTC4162_CONFIG_BITS_REG_SUBADDR 0x14u
#define LTC4162_CONFIG_BITS_REG (0u << 12 | (LTC4162_WORD_SIZE - 1) << 8 | LTC4162_CONFIG_BITS_REG_SUBADDR)
//!@}
/*! @defgroup LTC4162_SUSPEND_CHARGER SUSPEND_CHARGER
 *  @ingroup LTC4162-LADM_register_map
 *  @brief SUSPEND_CHARGER Bit Field
 *
 *  Causes battery charging to be suspended. This setting should be used cautiously. For embedded battery systems where two wire interface communication relies on a minimum battery voltage, setting this bit could result in a deadlock that may require factory service to correct.
 *   - Register: @ref LTC4162_CONFIG_BITS_REG "CONFIG_BITS_REG"
 *   - CommandCode: 0x14
 *   - Size: 1
 *   - Offset: 5
 *   - MSB: 5
 *   - MASK: 0x0020
 *   - Access: R/W
 *   - Default: 0
 */
//!@{
#define LTC4162_SUSPEND_CHARGER_SUBADDR LTC4162_CONFIG_BITS_REG_SUBADDR //!< @ref LTC4162_SUSPEND_CHARGER "SUSPEND_CHARGER"
#define LTC4162_SUSPEND_CHARGER_SIZE 1u
#define LTC4162_SUSPEND_CHARGER_OFFSET 5u
#define LTC4162_SUSPEND_CHARGER_MASK 0x0020u
#define LTC4162_SUSPEND_CHARGER_DEFAULT 0u
#define LTC4162_SUSPEND_CHARGER_DECODE(register_data) (((register_data) & LTC4162_SUSPEND_CHARGER_MASK) >> LTC4162_SUSPEND_CHARGER_OFFSET)
#define LTC4162_SUSPEND_CHARGER (LTC4162_SUSPEND_CHARGER_OFFSET << 12 | (LTC4162_SUSPEND_CHARGER_SIZE - 1) << 8 | LTC4162_SUSPEND_CHARGER_SUBADDR)
//!@}
/*! @defgroup LTC4162_RUN_BSR RUN_BSR
 *  @ingroup LTC4162-LADM_register_map
 *  @brief RUN_BSR Bit Field
 *
 *  Causes the battery equivalent-series-resistance (bsr) measurement to be made as soon as a charge cycle starts or immediately if a charge cycle is already running.
 *   - Register: @ref LTC4162_CONFIG_BITS_REG "CONFIG_BITS_REG"
 *   - CommandCode: 0x14
 *   - Size: 1
 *   - Offset: 4
 *   - MSB: 4
 *   - MASK: 0x0010
 *   - Access: R/W
 *   - Default: 0
 */
//!@{
#define LTC4162_RUN_BSR_SUBADDR LTC4162_CONFIG_BITS_REG_SUBADDR //!< @ref LTC4162_RUN_BSR "RUN_BSR"
#define LTC4162_RUN_BSR_SIZE 1u
#define LTC4162_RUN_BSR_OFFSET 4u
#define LTC4162_RUN_BSR_MASK 0x0010u
#define LTC4162_RUN_BSR_DEFAULT 0u
#define LTC4162_RUN_BSR_DECODE(register_data) (((register_data) & LTC4162_RUN_BSR_MASK) >> LTC4162_RUN_BSR_OFFSET)
#define LTC4162_RUN_BSR (LTC4162_RUN_BSR_OFFSET << 12 | (LTC4162_RUN_BSR_SIZE - 1) << 8 | LTC4162_RUN_BSR_SUBADDR)
//!@}
/*! @defgroup LTC4162_TELEMETRY_SPEED TELEMETRY_SPEED
 *  @ingroup LTC4162-LADM_register_map
 *  @brief TELEMETRY_SPEED Bit Field
 *
 *  Forces the telemetry system to take measurements at the higher rate of approximately once every 11ms whenever the telemetry system is on. When this bit is disabled, the telemetry system will slow down to about once every 5s to reduce power when not charging. Setting telemetry_speed to tel_high_speed in conjunction with force_telemetry_on with no input power available will increase battery drain.
 *   - Register: @ref LTC4162_CONFIG_BITS_REG "CONFIG_BITS_REG"
 *   - CommandCode: 0x14
 *   - Size: 1
 *   - Offset: 3
 *   - MSB: 3
 *   - MASK: 0x0008
 *   - Access: R/W
 *   - Default: 0
 */
//!@{
#define LTC4162_TELEMETRY_SPEED_SUBADDR LTC4162_CONFIG_BITS_REG_SUBADDR //!< @ref LTC4162_TELEMETRY_SPEED "TELEMETRY_SPEED"
#define LTC4162_TELEMETRY_SPEED_SIZE 1u
#define LTC4162_TELEMETRY_SPEED_OFFSET 3u
#define LTC4162_TELEMETRY_SPEED_MASK 0x0008u
#define LTC4162_TELEMETRY_SPEED_DEFAULT 0u
#define LTC4162_TELEMETRY_SPEED_DECODE(register_data) (((register_data) & LTC4162_TELEMETRY_SPEED_MASK) >> LTC4162_TELEMETRY_SPEED_OFFSET)
#define LTC4162_TELEMETRY_SPEED (LTC4162_TELEMETRY_SPEED_OFFSET << 12 | (LTC4162_TELEMETRY_SPEED_SIZE - 1) << 8 | LTC4162_TELEMETRY_SPEED_SUBADDR)
#define LTC4162_TELEMETRY_SPEED_ENUM_TEL_HIGH_SPEED 1u
#define LTC4162_TELEMETRY_SPEED_ENUM_TEL_LOW_SPEED 0u
//!@}
/*! @defgroup LTC4162_FORCE_TELEMETRY_ON FORCE_TELEMETRY_ON
 *  @ingroup LTC4162-LADM_register_map
 *  @brief FORCE_TELEMETRY_ON Bit Field
 *
 *  Causes the telemetry system to operate at all times, including times when only battery power is available.
 *   - Register: @ref LTC4162_CONFIG_BITS_REG "CONFIG_BITS_REG"
 *   - CommandCode: 0x14
 *   - Size: 1
 *   - Offset: 2
 *   - MSB: 2
 *   - MASK: 0x0004
 *   - Access: R/W
 *   - Default: 0
 */
//!@{
#define LTC4162_FORCE_TELEMETRY_ON_SUBADDR LTC4162_CONFIG_BITS_REG_SUBADDR //!< @ref LTC4162_FORCE_TELEMETRY_ON "FORCE_TELEMETRY_ON"
#define LTC4162_FORCE_TELEMETRY_ON_SIZE 1u
#define LTC4162_FORCE_TELEMETRY_ON_OFFSET 2u
#define LTC4162_FORCE_TELEMETRY_ON_MASK 0x0004u
#define LTC4162_FORCE_TELEMETRY_ON_DEFAULT 0u
#define LTC4162_FORCE_TELEMETRY_ON_DECODE(register_data) (((register_data) & LTC4162_FORCE_TELEMETRY_ON_MASK) >> LTC4162_FORCE_TELEMETRY_ON_OFFSET)
#define LTC4162_FORCE_TELEMETRY_ON (LTC4162_FORCE_TELEMETRY_ON_OFFSET << 12 | (LTC4162_FORCE_TELEMETRY_ON_SIZE - 1) << 8 | LTC4162_FORCE_TELEMETRY_ON_SUBADDR)
//!@}
/*! @defgroup LTC4162_MPPT_EN MPPT_EN
 *  @ingroup LTC4162-LADM_register_map
 *  @brief MPPT_EN Bit Field
 *
 *  Causes the Maximum Power-Point Tracking algorithm to run. The maximum power point algorithm takes control of the input undervoltage regulation control loop via the input_undervoltage_dac to seek the optimum power-point for resistive sources such as a long cable or solar panel.
 *   - Register: @ref LTC4162_CONFIG_BITS_REG "CONFIG_BITS_REG"
 *   - CommandCode: 0x14
 *   - Size: 1
 *   - Offset: 1
 *   - MSB: 1
 *   - MASK: 0x0002
 *   - Access: R/W
 *   - Default: 1
 */
//!@{
#define LTC4162_MPPT_EN_SUBADDR LTC4162_CONFIG_BITS_REG_SUBADDR //!< @ref LTC4162_MPPT_EN "MPPT_EN"
#define LTC4162_MPPT_EN_SIZE 1u
#define LTC4162_MPPT_EN_OFFSET 1u
#define LTC4162_MPPT_EN_MASK 0x0002u
#define LTC4162_MPPT_EN_DEFAULT 1u
#define LTC4162_MPPT_EN_DECODE(register_data) (((register_data) & LTC4162_MPPT_EN_MASK) >> LTC4162_MPPT_EN_OFFSET)
#define LTC4162_MPPT_EN (LTC4162_MPPT_EN_OFFSET << 12 | (LTC4162_MPPT_EN_SIZE - 1) << 8 | LTC4162_MPPT_EN_SUBADDR)
//!@}

/*! @defgroup LTC4162_IIN_LIMIT_TARGET_REG IIN_LIMIT_TARGET_REG
 *  @ingroup LTC4162-LADM_register_map
 *  @brief IIN_LIMIT_TARGET_REG Register
 *
 * | 15:6 |              5:0 |
 * |:----:|:----------------:|
 * |  n/a | IIN_LIMIT_TARGET |
 *
 *   - CommandCode: 0x15
 *   - Contains Bit Fields:
 *     + @ref LTC4162_IIN_LIMIT_TARGET "IIN_LIMIT_TARGET" : Controls the target input current limit setting. The input current is limited by regulating charge current in response to the voltage across an external current sense resistor, RSNSI, between the CLP and CLN pins and is given by (iin_limit_target + 1) × 500µV / RSNSI. Note that the LTC4162 can only limit charge current based on this setting. It does not have the authority to block current from passing directly through to the system load. Connecting the system load to the battery, however, can allow total input current control.
*/

//!@{
#define LTC4162_IIN_LIMIT_TARGET_REG_SUBADDR 0x15u
#define LTC4162_IIN_LIMIT_TARGET_REG (0u << 12 | (LTC4162_WORD_SIZE - 1) << 8 | LTC4162_IIN_LIMIT_TARGET_REG_SUBADDR)
//!@}
/*! @defgroup LTC4162_IIN_LIMIT_TARGET IIN_LIMIT_TARGET
 *  @ingroup LTC4162-LADM_register_map
 *  @brief IIN_LIMIT_TARGET Bit Field
 *
 *  Controls the target input current limit setting. The input current is limited by regulating charge current in response to the voltage across an external current sense resistor, RSNSI, between the CLP and CLN pins and is given by (iin_limit_target + 1) × 500µV / RSNSI. Note that the LTC4162 can only limit charge current based on this setting. It does not have the authority to block current from passing directly through to the system load. Connecting the system load to the battery, however, can allow total input current control.
 *   - Register: @ref LTC4162_IIN_LIMIT_TARGET_REG "IIN_LIMIT_TARGET_REG"
 *   - CommandCode: 0x15
 *   - Size: 6
 *   - Offset: 0
 *   - MSB: 5
 *   - MASK: 0x003F
 *   - Access: R/W
 *   - Default: 63
 *   - Format: LTC4162_IINLIM
 */
//!@{
#define LTC4162_IIN_LIMIT_TARGET_SUBADDR LTC4162_IIN_LIMIT_TARGET_REG_SUBADDR //!< @ref LTC4162_IIN_LIMIT_TARGET "IIN_LIMIT_TARGET"
#define LTC4162_IIN_LIMIT_TARGET_SIZE 6u
#define LTC4162_IIN_LIMIT_TARGET_OFFSET 0u
#define LTC4162_IIN_LIMIT_TARGET_MASK 0x003Fu
#define LTC4162_IIN_LIMIT_TARGET_DEFAULT 63u
#define LTC4162_IIN_LIMIT_TARGET_DECODE(register_data) (((register_data) & LTC4162_IIN_LIMIT_TARGET_MASK) >> LTC4162_IIN_LIMIT_TARGET_OFFSET)
#define LTC4162_IIN_LIMIT_TARGET (LTC4162_IIN_LIMIT_TARGET_OFFSET << 12 | (LTC4162_IIN_LIMIT_TARGET_SIZE - 1) << 8 | LTC4162_IIN_LIMIT_TARGET_SUBADDR)
//!@}

/*! @defgroup LTC4162_INPUT_UNDERVOLTAGE_SETTING_REG INPUT_UNDERVOLTAGE_SETTING_REG
 *  @ingroup LTC4162-LADM_register_map
 *  @brief INPUT_UNDERVOLTAGE_SETTING_REG Register
 *
 * | 15:8 |                        7:0 |
 * |:----:|:--------------------------:|
 * |  n/a | INPUT_UNDERVOLTAGE_SETTING |
 *
 *   - CommandCode: 0x16
 *   - Contains Bit Fields:
 *     + @ref LTC4162_INPUT_UNDERVOLTAGE_SETTING "INPUT_UNDERVOLTAGE_SETTING" : Controls the input undervoltage regulation setting. The regulation voltage, given by (input_undervoltage_setting + 1) × 140.625mV, is the voltage at which the charge current will be reduced to prevent further droop in supply voltage due to a resistive source. If mppt_en is set, the MPPT algorithm will override this setting. The actual input undervoltage value can be read back from the input_undervoltage_dac.
*/

//!@{
#define LTC4162_INPUT_UNDERVOLTAGE_SETTING_REG_SUBADDR 0x16u
#define LTC4162_INPUT_UNDERVOLTAGE_SETTING_REG (0u << 12 | (LTC4162_WORD_SIZE - 1) << 8 | LTC4162_INPUT_UNDERVOLTAGE_SETTING_REG_SUBADDR)
//!@}
/*! @defgroup LTC4162_INPUT_UNDERVOLTAGE_SETTING INPUT_UNDERVOLTAGE_SETTING
 *  @ingroup LTC4162-LADM_register_map
 *  @brief INPUT_UNDERVOLTAGE_SETTING Bit Field
 *
 *  Controls the input undervoltage regulation setting. The regulation voltage, given by (input_undervoltage_setting + 1) × 140.625mV, is the voltage at which the charge current will be reduced to prevent further droop in supply voltage due to a resistive source. If mppt_en is set, the MPPT algorithm will override this setting. The actual input undervoltage value can be read back from the input_undervoltage_dac.
 *   - Register: @ref LTC4162_INPUT_UNDERVOLTAGE_SETTING_REG "INPUT_UNDERVOLTAGE_SETTING_REG"
 *   - CommandCode: 0x16
 *   - Size: 8
 *   - Offset: 0
 *   - MSB: 7
 *   - MASK: 0x00FF
 *   - Access: R/W
 *   - Default: 31
 *   - Format: LTC4162_VIN_UVCL
 */
//!@{
#define LTC4162_INPUT_UNDERVOLTAGE_SETTING_SUBADDR LTC4162_INPUT_UNDERVOLTAGE_SETTING_REG_SUBADDR //!< @ref LTC4162_INPUT_UNDERVOLTAGE_SETTING "INPUT_UNDERVOLTAGE_SETTING"
#define LTC4162_INPUT_UNDERVOLTAGE_SETTING_SIZE 8u
#define LTC4162_INPUT_UNDERVOLTAGE_SETTING_OFFSET 0u
#define LTC4162_INPUT_UNDERVOLTAGE_SETTING_MASK 0x00FFu
#define LTC4162_INPUT_UNDERVOLTAGE_SETTING_DEFAULT 31u
#define LTC4162_INPUT_UNDERVOLTAGE_SETTING_DECODE(register_data) (((register_data) & LTC4162_INPUT_UNDERVOLTAGE_SETTING_MASK) >> LTC4162_INPUT_UNDERVOLTAGE_SETTING_OFFSET)
#define LTC4162_INPUT_UNDERVOLTAGE_SETTING (LTC4162_INPUT_UNDERVOLTAGE_SETTING_OFFSET << 12 | (LTC4162_INPUT_UNDERVOLTAGE_SETTING_SIZE - 1) << 8 | LTC4162_INPUT_UNDERVOLTAGE_SETTING_SUBADDR)
//!@}

/*! @defgroup LTC4162_ARM_SHIP_MODE_REG ARM_SHIP_MODE_REG
 *  @ingroup LTC4162-LADM_register_map
 *  @brief ARM_SHIP_MODE_REG Register
 *
 * |          15:0 |
 * |:-------------:|
 * | ARM_SHIP_MODE |
 *
 *   - CommandCode: 0x19
 *   - Contains Bit Fields:
 *     + @ref LTC4162_ARM_SHIP_MODE "ARM_SHIP_MODE" : Setting this register to arm arms the ultra low-power ship and store mode. Ship mode does not take effect until the VIN pin drops below approximately 1V or immediately if VIN is already below 1V.
*/

//!@{
#define LTC4162_ARM_SHIP_MODE_REG_SUBADDR 0x19u
#define LTC4162_ARM_SHIP_MODE_REG (0u << 12 | (LTC4162_WORD_SIZE - 1) << 8 | LTC4162_ARM_SHIP_MODE_REG_SUBADDR)
//!@}
/*! @defgroup LTC4162_ARM_SHIP_MODE ARM_SHIP_MODE
 *  @ingroup LTC4162-LADM_register_map
 *  @brief ARM_SHIP_MODE Bit Field
 *
 *  Setting this register to arm arms the ultra low-power ship and store mode. Ship mode does not take effect until the VIN pin drops below approximately 1V or immediately if VIN is already below 1V.
 *   - Register: @ref LTC4162_ARM_SHIP_MODE_REG "ARM_SHIP_MODE_REG"
 *   - CommandCode: 0x19
 *   - Size: 16
 *   - Offset: 0
 *   - MSB: 15
 *   - MASK: 0xFFFF
 *   - Access: R/W
 *   - Default: 0
 */
//!@{
#define LTC4162_ARM_SHIP_MODE_SUBADDR LTC4162_ARM_SHIP_MODE_REG_SUBADDR //!< @ref LTC4162_ARM_SHIP_MODE "ARM_SHIP_MODE"
#define LTC4162_ARM_SHIP_MODE_SIZE 16u
#define LTC4162_ARM_SHIP_MODE_OFFSET 0u
#define LTC4162_ARM_SHIP_MODE_MASK 0xFFFFu
#define LTC4162_ARM_SHIP_MODE_DEFAULT 0u
#define LTC4162_ARM_SHIP_MODE_DECODE(register_data) (register_data)
#define LTC4162_ARM_SHIP_MODE (LTC4162_ARM_SHIP_MODE_OFFSET << 12 | (LTC4162_ARM_SHIP_MODE_SIZE - 1) << 8 | LTC4162_ARM_SHIP_MODE_SUBADDR)
#define LTC4162_ARM_SHIP_MODE_ENUM_ARM 21325u
//!@}

/*! @defgroup LTC4162_CHARGE_CURRENT_SETTING_REG CHARGE_CURRENT_SETTING_REG
 *  @ingroup LTC4162-LADM_register_map
 *  @brief CHARGE_CURRENT_SETTING_REG Register
 *
 * | 15:5 |                    4:0 |
 * |:----:|:----------------------:|
 * |  n/a | CHARGE_CURRENT_SETTING |
 *
 *   - CommandCode: 0x1A
 *   - Contains Bit Fields:
 *     + @ref LTC4162_CHARGE_CURRENT_SETTING "CHARGE_CURRENT_SETTING" : Controls the target charge current regulation servo level. The charge current is regulated by servoing the voltage across an external current sense resistor, RSNSB, between the CSP and CSN pins. The servo voltage is given by (charge_current_setting + 1) × 1mV. The effective charge current, determined by the external resistor, RSNSB, is given by (charge_current_setting + 1) × 1mV / RSNSB. icharge_dac will follow charge_current_setting unless thermal_reg_active is true or the JEITA algorithm, with en_jeita, has altered it.
*/

//!@{
#define LTC4162_CHARGE_CURRENT_SETTING_REG_SUBADDR 0x1Au
#define LTC4162_CHARGE_CURRENT_SETTING_REG (0u << 12 | (LTC4162_WORD_SIZE - 1) << 8 | LTC4162_CHARGE_CURRENT_SETTING_REG_SUBADDR)
//!@}
/*! @defgroup LTC4162_CHARGE_CURRENT_SETTING CHARGE_CURRENT_SETTING
 *  @ingroup LTC4162-LADM_register_map
 *  @brief CHARGE_CURRENT_SETTING Bit Field
 *
 *  Controls the target charge current regulation servo level. The charge current is regulated by servoing the voltage across an external current sense resistor, RSNSB, between the CSP and CSN pins. The servo voltage is given by (charge_current_setting + 1) × 1mV. The effective charge current, determined by the external resistor, RSNSB, is given by (charge_current_setting + 1) × 1mV / RSNSB. icharge_dac will follow charge_current_setting unless thermal_reg_active is true or the JEITA algorithm, with en_jeita, has altered it.
 *   - Register: @ref LTC4162_CHARGE_CURRENT_SETTING_REG "CHARGE_CURRENT_SETTING_REG"
 *   - CommandCode: 0x1A
 *   - Size: 5
 *   - Offset: 0
 *   - MSB: 4
 *   - MASK: 0x001F
 *   - Access: R/W
 *   - Default: 31
 *   - Format: LTC4162_ICHARGE
 */
//!@{
#define LTC4162_CHARGE_CURRENT_SETTING_SUBADDR LTC4162_CHARGE_CURRENT_SETTING_REG_SUBADDR //!< @ref LTC4162_CHARGE_CURRENT_SETTING "CHARGE_CURRENT_SETTING"
#define LTC4162_CHARGE_CURRENT_SETTING_SIZE 5u
#define LTC4162_CHARGE_CURRENT_SETTING_OFFSET 0u
#define LTC4162_CHARGE_CURRENT_SETTING_MASK 0x001Fu
#define LTC4162_CHARGE_CURRENT_SETTING_DEFAULT 31u
#define LTC4162_CHARGE_CURRENT_SETTING_DECODE(register_data) (((register_data) & LTC4162_CHARGE_CURRENT_SETTING_MASK) >> LTC4162_CHARGE_CURRENT_SETTING_OFFSET)
#define LTC4162_CHARGE_CURRENT_SETTING (LTC4162_CHARGE_CURRENT_SETTING_OFFSET << 12 | (LTC4162_CHARGE_CURRENT_SETTING_SIZE - 1) << 8 | LTC4162_CHARGE_CURRENT_SETTING_SUBADDR)
//!@}

/*! @defgroup LTC4162_VCHARGE_SETTING_REG VCHARGE_SETTING_REG
 *  @ingroup LTC4162-LADM_register_map
 *  @brief VCHARGE_SETTING_REG Register
 *
 * | 15:5 |             4:0 |
 * |:----:|:---------------:|
 * |  n/a | VCHARGE_SETTING |
 *
 *   - CommandCode: 0x1B
 *   - Contains Bit Fields:
 *     + @ref LTC4162_VCHARGE_SETTING "VCHARGE_SETTING" : Controls the final charge voltage regulation servo level. To maintain inherent over-charge protection, only Lithium Ion appropriate charge voltage values can be selected. The charge voltage setting can be computed from cell_count × (vcharge_setting × 12.5mV + 3.8125V) where vcharge_setting ranges from 0 to 31 (4.2V max). vcharge_dac will follow vcharge_setting unless the advanced JEITA temperature control system (en_jeita) has altered it.
*/

//!@{
#define LTC4162_VCHARGE_SETTING_REG_SUBADDR 0x1Bu
#define LTC4162_VCHARGE_SETTING_REG (0u << 12 | (LTC4162_WORD_SIZE - 1) << 8 | LTC4162_VCHARGE_SETTING_REG_SUBADDR)
//!@}
/*! @defgroup LTC4162_VCHARGE_SETTING VCHARGE_SETTING
 *  @ingroup LTC4162-LADM_register_map
 *  @brief VCHARGE_SETTING Bit Field
 *
 *  Controls the final charge voltage regulation servo level. To maintain inherent over-charge protection, only Lithium Ion appropriate charge voltage values can be selected. The charge voltage setting can be computed from cell_count × (vcharge_setting × 12.5mV + 3.8125V) where vcharge_setting ranges from 0 to 31 (4.2V max). vcharge_dac will follow vcharge_setting unless the advanced JEITA temperature control system (en_jeita) has altered it.
 *   - Register: @ref LTC4162_VCHARGE_SETTING_REG "VCHARGE_SETTING_REG"
 *   - CommandCode: 0x1B
 *   - Size: 5
 *   - Offset: 0
 *   - MSB: 4
 *   - MASK: 0x001F
 *   - Access: R/W
 *   - Default: 31
 *   - Format: LTC4162_VCHARGE_LIION
 */
//!@{
#define LTC4162_VCHARGE_SETTING_SUBADDR LTC4162_VCHARGE_SETTING_REG_SUBADDR //!< @ref LTC4162_VCHARGE_SETTING "VCHARGE_SETTING"
#define LTC4162_VCHARGE_SETTING_SIZE 5u
#define LTC4162_VCHARGE_SETTING_OFFSET 0u
#define LTC4162_VCHARGE_SETTING_MASK 0x001Fu
#define LTC4162_VCHARGE_SETTING_DEFAULT 31u
#define LTC4162_VCHARGE_SETTING_DECODE(register_data) (((register_data) & LTC4162_VCHARGE_SETTING_MASK) >> LTC4162_VCHARGE_SETTING_OFFSET)
#define LTC4162_VCHARGE_SETTING (LTC4162_VCHARGE_SETTING_OFFSET << 12 | (LTC4162_VCHARGE_SETTING_SIZE - 1) << 8 | LTC4162_VCHARGE_SETTING_SUBADDR)
#define LTC4162_VCHARGE_SETTING_ENUM_VCHARGE_LION_DEFAULT 31u
//!@}

/*! @defgroup LTC4162_C_OVER_X_THRESHOLD_REG C_OVER_X_THRESHOLD_REG
 *  @ingroup LTC4162-LADM_register_map
 *  @brief C_OVER_X_THRESHOLD_REG Register
 *
 * |               15:0 |
 * |:------------------:|
 * | C_OVER_X_THRESHOLD |
 *
 *   - CommandCode: 0x1C
 *   - Contains Bit Fields:
 *     + @ref LTC4162_C_OVER_X_THRESHOLD "C_OVER_X_THRESHOLD" : Signed number that sets the ibat A/D value used to qualify C/x detection and termination. The C/x level is based on the value for ibat which has a scaling factor of 1.466µV / RSNSB amperes/LSB. For example, to make the C/x level C/10 (a very common choice) then c_over_x_threshold should be set to c_over_10 which is 10% of the maximum possible ibat reading (32mV × 37.5 × 18,191 / 10). 32mV is the full scale charge current signal from CSP to CSN, 37.5 is the internal charge amplifier's gain and 18,191 is the A/D's span term in counts per Volt.
*/

//!@{
#define LTC4162_C_OVER_X_THRESHOLD_REG_SUBADDR 0x1Cu
#define LTC4162_C_OVER_X_THRESHOLD_REG (0u << 12 | (LTC4162_WORD_SIZE - 1) << 8 | LTC4162_C_OVER_X_THRESHOLD_REG_SUBADDR)
//!@}
/*! @defgroup LTC4162_C_OVER_X_THRESHOLD C_OVER_X_THRESHOLD
 *  @ingroup LTC4162-LADM_register_map
 *  @brief C_OVER_X_THRESHOLD Bit Field
 *
 *  Signed number that sets the ibat A/D value used to qualify C/x detection and termination. The C/x level is based on the value for ibat which has a scaling factor of 1.466µV / RSNSB amperes/LSB. For example, to make the C/x level C/10 (a very common choice) then c_over_x_threshold should be set to c_over_10 which is 10% of the maximum possible ibat reading (32mV × 37.5 × 18,191 / 10). 32mV is the full scale charge current signal from CSP to CSN, 37.5 is the internal charge amplifier's gain and 18,191 is the A/D's span term in counts per Volt.
 *   - Register: @ref LTC4162_C_OVER_X_THRESHOLD_REG "C_OVER_X_THRESHOLD_REG"
 *   - CommandCode: 0x1C
 *   - Size: 16
 *   - Offset: 0
 *   - MSB: 15
 *   - MASK: 0xFFFF
 *   - Access: R/W
 *   - Default: 2184
 *   - Format: LTC4162_IBAT_FORMAT
 */
//!@{
#define LTC4162_C_OVER_X_THRESHOLD_SUBADDR LTC4162_C_OVER_X_THRESHOLD_REG_SUBADDR //!< @ref LTC4162_C_OVER_X_THRESHOLD "C_OVER_X_THRESHOLD"
#define LTC4162_C_OVER_X_THRESHOLD_SIZE 16u
#define LTC4162_C_OVER_X_THRESHOLD_OFFSET 0u
#define LTC4162_C_OVER_X_THRESHOLD_MASK 0xFFFFu
#define LTC4162_C_OVER_X_THRESHOLD_DEFAULT 2184u
#define LTC4162_C_OVER_X_THRESHOLD_DECODE(register_data) (register_data)
#define LTC4162_C_OVER_X_THRESHOLD (LTC4162_C_OVER_X_THRESHOLD_OFFSET << 12 | (LTC4162_C_OVER_X_THRESHOLD_SIZE - 1) << 8 | LTC4162_C_OVER_X_THRESHOLD_SUBADDR)
#define LTC4162_C_OVER_X_THRESHOLD_ENUM_C_OVER_10 2184u
//!@}

/*! @defgroup LTC4162_MAX_CV_TIME_REG MAX_CV_TIME_REG
 *  @ingroup LTC4162-LADM_register_map
 *  @brief MAX_CV_TIME_REG Register
 *
 * |        15:0 |
 * |:-----------:|
 * | MAX_CV_TIME |
 *
 *   - CommandCode: 0x1D
 *   - Contains Bit Fields:
 *     + @ref LTC4162_MAX_CV_TIME "MAX_CV_TIME" : Sets the constant-voltage termination setting against which the tcvtimer is compared. The timer begins at the onset of the constant_voltage phase of charging and increments at one count per second. The default setting is 14,400 (4 hours).
*/

//!@{
#define LTC4162_MAX_CV_TIME_REG_SUBADDR 0x1Du
#define LTC4162_MAX_CV_TIME_REG (0u << 12 | (LTC4162_WORD_SIZE - 1) << 8 | LTC4162_MAX_CV_TIME_REG_SUBADDR)
//!@}
/*! @defgroup LTC4162_MAX_CV_TIME MAX_CV_TIME
 *  @ingroup LTC4162-LADM_register_map
 *  @brief MAX_CV_TIME Bit Field
 *
 *  Sets the constant-voltage termination setting against which the tcvtimer is compared. The timer begins at the onset of the constant_voltage phase of charging and increments at one count per second. The default setting is 14,400 (4 hours).
 *   - Register: @ref LTC4162_MAX_CV_TIME_REG "MAX_CV_TIME_REG"
 *   - CommandCode: 0x1D
 *   - Size: 16
 *   - Offset: 0
 *   - MSB: 15
 *   - MASK: 0xFFFF
 *   - Access: R/W
 *   - Default: 14400
 */
//!@{
#define LTC4162_MAX_CV_TIME_SUBADDR LTC4162_MAX_CV_TIME_REG_SUBADDR //!< @ref LTC4162_MAX_CV_TIME "MAX_CV_TIME"
#define LTC4162_MAX_CV_TIME_SIZE 16u
#define LTC4162_MAX_CV_TIME_OFFSET 0u
#define LTC4162_MAX_CV_TIME_MASK 0xFFFFu
#define LTC4162_MAX_CV_TIME_DEFAULT 14400u
#define LTC4162_MAX_CV_TIME_DECODE(register_data) (register_data)
#define LTC4162_MAX_CV_TIME (LTC4162_MAX_CV_TIME_OFFSET << 12 | (LTC4162_MAX_CV_TIME_SIZE - 1) << 8 | LTC4162_MAX_CV_TIME_SUBADDR)
#define LTC4162_MAX_CV_TIME_ENUM_30MINS 1800u
#define LTC4162_MAX_CV_TIME_ENUM_1HOUR 3600u
#define LTC4162_MAX_CV_TIME_ENUM_2HOURS 7200u
#define LTC4162_MAX_CV_TIME_ENUM_4HOURS_DEFAULT 14400u
//!@}

/*! @defgroup LTC4162_MAX_CHARGE_TIME_REG MAX_CHARGE_TIME_REG
 *  @ingroup LTC4162-LADM_register_map
 *  @brief MAX_CHARGE_TIME_REG Register
 *
 * |            15:0 |
 * |:---------------:|
 * | MAX_CHARGE_TIME |
 *
 *   - CommandCode: 0x1E
 *   - Contains Bit Fields:
 *     + @ref LTC4162_MAX_CHARGE_TIME "MAX_CHARGE_TIME" : Sets the total charge time termination setting against which the tchargetimer is compared. The default value of 0 disables the total charge time feature and prevents the tchargetimer from running. If enabled with a non zero value, the tchargetimer begins counting at the onset of a charge cycle and increments at one count per minute.
*/

//!@{
#define LTC4162_MAX_CHARGE_TIME_REG_SUBADDR 0x1Eu
#define LTC4162_MAX_CHARGE_TIME_REG (0u << 12 | (LTC4162_WORD_SIZE - 1) << 8 | LTC4162_MAX_CHARGE_TIME_REG_SUBADDR)
//!@}
/*! @defgroup LTC4162_MAX_CHARGE_TIME MAX_CHARGE_TIME
 *  @ingroup LTC4162-LADM_register_map
 *  @brief MAX_CHARGE_TIME Bit Field
 *
 *  Sets the total charge time termination setting against which the tchargetimer is compared. The default value of 0 disables the total charge time feature and prevents the tchargetimer from running. If enabled with a non zero value, the tchargetimer begins counting at the onset of a charge cycle and increments at one count per minute.
 *   - Register: @ref LTC4162_MAX_CHARGE_TIME_REG "MAX_CHARGE_TIME_REG"
 *   - CommandCode: 0x1E
 *   - Size: 16
 *   - Offset: 0
 *   - MSB: 15
 *   - MASK: 0xFFFF
 *   - Access: R/W
 *   - Default: 0
 */
//!@{
#define LTC4162_MAX_CHARGE_TIME_SUBADDR LTC4162_MAX_CHARGE_TIME_REG_SUBADDR //!< @ref LTC4162_MAX_CHARGE_TIME "MAX_CHARGE_TIME"
#define LTC4162_MAX_CHARGE_TIME_SIZE 16u
#define LTC4162_MAX_CHARGE_TIME_OFFSET 0u
#define LTC4162_MAX_CHARGE_TIME_MASK 0xFFFFu
#define LTC4162_MAX_CHARGE_TIME_DEFAULT 0u
#define LTC4162_MAX_CHARGE_TIME_DECODE(register_data) (register_data)
#define LTC4162_MAX_CHARGE_TIME (LTC4162_MAX_CHARGE_TIME_OFFSET << 12 | (LTC4162_MAX_CHARGE_TIME_SIZE - 1) << 8 | LTC4162_MAX_CHARGE_TIME_SUBADDR)
#define LTC4162_MAX_CHARGE_TIME_ENUM_MAXCHARGETIME_DISABLE 0u
//!@}

/*! @defgroup LTC4162_JEITA_T1_REG JEITA_T1_REG
 *  @ingroup LTC4162-LADM_register_map
 *  @brief JEITA_T1_REG Register
 *
 * |     15:0 |
 * |:--------:|
 * | JEITA_T1 |
 *
 *   - CommandCode: 0x1F
 *   - Contains Bit Fields:
 *     + @ref LTC4162_JEITA_T1 "JEITA_T1" : Signed number that sets the JEITA temperature region transition temperature T1 between JEITA regions R1 and R2. The temperature is based on the thermistor reading from the telemetry system; RNTC = RNTCBIAS × (21829 - thermistor_voltage) / thermistor_voltage. Recall that the thermistor has a negative temperature coefficient so jeita_t1, representing colder temperatures, will have the highest value and jeita_t6, representing warmer temperatures, will have the lowest value. The default value of 16117 maps to about 0°C for the expected thermistor β value of 3490K.
*/

//!@{
#define LTC4162_JEITA_T1_REG_SUBADDR 0x1Fu
#define LTC4162_JEITA_T1_REG (0u << 12 | (LTC4162_WORD_SIZE - 1) << 8 | LTC4162_JEITA_T1_REG_SUBADDR)
//!@}
/*! @defgroup LTC4162_JEITA_T1 JEITA_T1
 *  @ingroup LTC4162-LADM_register_map
 *  @brief JEITA_T1 Bit Field
 *
 *  Signed number that sets the JEITA temperature region transition temperature T1 between JEITA regions R1 and R2. The temperature is based on the thermistor reading from the telemetry system; RNTC = RNTCBIAS × (21829 - thermistor_voltage) / thermistor_voltage. Recall that the thermistor has a negative temperature coefficient so jeita_t1, representing colder temperatures, will have the highest value and jeita_t6, representing warmer temperatures, will have the lowest value. The default value of 16117 maps to about 0°C for the expected thermistor β value of 3490K.
 *   - Register: @ref LTC4162_JEITA_T1_REG "JEITA_T1_REG"
 *   - CommandCode: 0x1F
 *   - Size: 16
 *   - Offset: 0
 *   - MSB: 15
 *   - MASK: 0xFFFF
 *   - Access: R/W
 *   - Default: 16117
 *   - Format: LTC4162_NTCS0402E3103FLT
 */
//!@{
#define LTC4162_JEITA_T1_SUBADDR LTC4162_JEITA_T1_REG_SUBADDR //!< @ref LTC4162_JEITA_T1 "JEITA_T1"
#define LTC4162_JEITA_T1_SIZE 16u
#define LTC4162_JEITA_T1_OFFSET 0u
#define LTC4162_JEITA_T1_MASK 0xFFFFu
#define LTC4162_JEITA_T1_DEFAULT 16117u
#define LTC4162_JEITA_T1_DECODE(register_data) (register_data)
#define LTC4162_JEITA_T1 (LTC4162_JEITA_T1_OFFSET << 12 | (LTC4162_JEITA_T1_SIZE - 1) << 8 | LTC4162_JEITA_T1_SUBADDR)
//!@}

/*! @defgroup LTC4162_JEITA_T2_REG JEITA_T2_REG
 *  @ingroup LTC4162-LADM_register_map
 *  @brief JEITA_T2_REG Register
 *
 * |     15:0 |
 * |:--------:|
 * | JEITA_T2 |
 *
 *   - CommandCode: 0x20
 *   - Contains Bit Fields:
 *     + @ref LTC4162_JEITA_T2 "JEITA_T2" : Signed number that sets the JEITA temperature region transition temperature T2 between JEITA regions R2 and R3. The temperature is based on the thermistor reading from the telemetry system; RNTC = RNTCBIAS × (21829 - thermistor_voltage) / thermistor_voltage. Recall that the thermistor has a negative temperature coefficient so jeita_t1, representing colder temperatures, will have the highest value and jeita_t6, representing warmer temperatures, will have the lowest value. The default value of 14113 maps to about 10°C for the expected thermistor β value of 3490K.
*/
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
