gibbs212521/HEC_2_senior_design/docs/Firmware/LTC4162-LADM/c_code/common/LTC4162-LADM_formats.h

/*!*****************************************************************************
*
* LTC4162: Advanced Synchronous Switching Battery Charger and PowerPath Manager
*
* @verbatim
* The LTC®4162-L is an advanced synchronous switching battery charger and
* PowerPath manager that seamlessly manages power distribution from input
* sources such as wall adapters, backplanes, solar panels, etc. and a
* rechargeable battery. A high resolution telemetry system provides extensive
* information on circuit voltages, currents, battery resistance and temperatures
* which can all be read back over the serial interface. The serial interface can
* also be used to configure many of the charging parameters including
* termination algorithms as well as numerous system status alerts. The LTC4162-L
* can charge Lithium-Ion cell stacks as high as eight cells with up to 3.2A of
* charge current. The power path topology decouples the output voltage from the
* battery allowing a portable product to start up under very low battery voltage
* conditions. The LTC4162-L is available in an I²C adjustable version as well as
* 4.0V, 4.1V and 4.2V fixed voltage versions all with and without MPPT enabled
* by default. The LTC4162-L is available in the 28-pin 4mm × 5mm × 0.75mm QFN
* surface mount package.
* @endverbatim
*
* http://www.linear.com/product/LTC4162
*
* http://www.linear.com/product/LTC4162#demoboards
*
* REVISION HISTORY
* $Revision$
* $Date: 2019-03-06 17:20:19 -0500 (Wed, 06 Mar 2019) $
*
* Copyright (c) 2019 Analog Devices, Inc.
*
* All rights reserved.
*
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
* The Linear Technology Linduino is not affiliated with the official Arduino
* team. However, the Linduino is only possible because of the Arduino team's
* commitment to the open-source community. Please, visit http://www.arduino.cc
* and http://store.arduino.cc, and consider a purchase that will help fund
* their ongoing work.
*
* Generated on: 2019-03-06
*
******************************************************************************/


/*! @file
 *  @ingroup LTC4162-LADM
 *  @brief LTC4162-LADM library file defining data conversion macros and constants for the LTC4162-LADM.
 *
 *
 *  This file contains constants and real to integer/unsigned macros which can be used
 *  to represent real values in the source code, with automatic compile-time
 *  conversion to LTC4162 integer register scaling.
 *  Passing runtime variables to these macros should be avoided in embedded systems, as it
 *  results in runtime floating point calculations.
 *
 *  This file also contains integer/unsigned to real macros which can be used to convert from
 *  internal integer format to real values for display/debug. Invoking these macros results in
 *  runtime floating point calculations with associated high memory and execution penalty in
 *  small embedded systems.
 * @{
 */

#ifndef LTC4162_FORMATS_H_
#define LTC4162_FORMATS_H_

/*! @name Format Definitions
 *  Constants used by the macros below to convert between real and LTC4162 integer scaling.
 */
/*! @name Constants used in real/integer conversion macros below */
#define LTC4162_RSNSI 0.010
#define LTC4162_RSNSB 0.010
#define LTC4162_RNTCBIAS 10000.0
#define LTC4162_RNTCSER 0.0
#define LTC4162_VINDIV 30.0
#define LTC4162_VOUTDIV (30.0 * 1.00232)
#define LTC4162_BATDIV 3.5
#define LTC4162_AVPROG 37.5
#define LTC4162_AVCLPROG 37.5
#define LTC4162_ADCGAIN 18191.0
#define LTC4162_VREF 1.2
#define LTC4162_Rm40 214063.67
#define LTC4162_Rm34 152840.30
#define LTC4162_Rm28 110480.73
#define LTC4162_Rm21 76798.02
#define LTC4162_Rm14 54214.99
#define LTC4162_Rm6 37075.65
#define LTC4162_R4 23649.71
#define LTC4162_R33 7400.97
#define LTC4162_R44 5001.22
#define LTC4162_R53 3693.55
#define LTC4162_R62 2768.21
#define LTC4162_R70 2167.17
#define LTC4162_R78 1714.08
#define LTC4162_R86 1368.87
#define LTC4162_R94 1103.18
#define LTC4162_R102 896.73
#define LTC4162_R110 734.86
#define LTC4162_R118 606.86
#define LTC4162_R126 504.80
#define LTC4162_R134 422.81
#define LTC4162_R142 356.45
#define LTC4162_R150 302.36

/*! @name Use the macros below to convert between real and LTC4162 integer scaling. */
/*! Convert from amperes to the iinlim setting.
 *   - Used with Bit Fields: iin_limit_target, iin_limit_dac, target_ilim.
 */
#define LTC4162_IINLIM_R2U(x) (uint16_t)__LTC4162_ILINE__((LTC4162_VREF / 64 / LTC4162_AVCLPROG / LTC4162_RSNSI), (LTC4162_VREF / 64 / LTC4162_AVCLPROG / LTC4162_RSNSI * 2), (0), (1), x)
#define LTC4162_IINLIM_U2R(y) __LTC4162_RLINE__((0), (1), (LTC4162_VREF / 64 / LTC4162_AVCLPROG / LTC4162_RSNSI), (LTC4162_VREF / 64 / LTC4162_AVCLPROG / LTC4162_RSNSI * 2), (uint16_t)(y))

/*! Convert from volts to the vcharge_liion setting.
 *   - Used with Bit Fields: vcharge_setting, vcharge_jeita_6, vcharge_jeita_5, vcharge_jeita_4, vcharge_jeita_3, vcharge_jeita_2, vcharge_dac.
 */
#define LTC4162_VCHARGE_LIION_R2U(x) (uint16_t)__LTC4162_ILINE__((3.8125), (3.8125 + 0.0125), (0), (1), x)
#define LTC4162_VCHARGE_LIION_U2R(y) __LTC4162_RLINE__((0), (1), (3.8125), (3.8125 + 0.0125), (uint16_t)(y))

/*! Convert from volts to the vin_uvcl setting.
 *   - Used with Bit Fields: input_undervoltage_setting, input_undervoltage_dac, input_undervoltage_mppt, mppt_vuvcl_dac_pmax.
 */
#define LTC4162_VIN_UVCL_R2U(x) (uint16_t)__LTC4162_ILINE__((LTC4162_VREF / 256 * LTC4162_VINDIV), (LTC4162_VREF / 256 * LTC4162_VINDIV * 2), (0), (1), x)
#define LTC4162_VIN_UVCL_U2R(y) __LTC4162_RLINE__((0), (1), (LTC4162_VREF / 256 * LTC4162_VINDIV), (LTC4162_VREF / 256 * LTC4162_VINDIV * 2), (uint16_t)(y))

/*! Convert from amperes to the charge_current_setting.
 *   - Used with Bit Fields: charge_current_setting, icharge_jeita_6, icharge_jeita_5, icharge_jeita_4, icharge_jeita_3, icharge_jeita_2, icharge_dac, target_icharge.
 */
#define LTC4162_ICHARGE_R2U(x) (uint16_t)__LTC4162_ILINE__((LTC4162_VREF / 32 / LTC4162_AVPROG / LTC4162_RSNSB), (LTC4162_VREF / 32 / LTC4162_AVPROG / LTC4162_RSNSB * 2), (0), (1), x)
#define LTC4162_ICHARGE_U2R(y) __LTC4162_RLINE__((0), (1), (LTC4162_VREF / 32 / LTC4162_AVPROG / LTC4162_RSNSB), (LTC4162_VREF / 32 / LTC4162_AVPROG / LTC4162_RSNSB * 2), (uint16_t)(y))

/*! Convert from volts to the per-cell vbat ADC reading.
 *   - Used with Bit Fields: vbat_lo_alert_limit, vbat_hi_alert_limit, vbat, vbat_filt.
 */
#define LTC4162_VBAT_FORMAT_R2I(x) (int16_t)__LTC4162_ILINE__((0), (LTC4162_BATDIV / LTC4162_ADCGAIN), (0), (1), x)
#define LTC4162_VBAT_FORMAT_I2R(y) __LTC4162_RLINE__((0), (1), (0), (LTC4162_BATDIV / LTC4162_ADCGAIN), (int16_t)(y))

/*! Convert from amperes to the ibat ADC reading.
 *   - Used with Bit Fields: ibat_lo_alert_limit, c_over_x_threshold, ibat, bsr_charge_current, mppt_ichrg, mppt_ichrg_max, mppt_ichrg_last.
 */
#define LTC4162_IBAT_FORMAT_R2I(x) (int16_t)__LTC4162_ILINE__((0), (1 / LTC4162_RSNSB / LTC4162_AVPROG / LTC4162_ADCGAIN), (0), (1), x)
#define LTC4162_IBAT_FORMAT_I2R(y) __LTC4162_RLINE__((0), (1), (0), (1 / LTC4162_RSNSB / LTC4162_AVPROG / LTC4162_ADCGAIN), (int16_t)(y))

/*! Convert from volts to the vout ADC reading.
 *   - Used with Bit Fields: vout_lo_alert_limit, vout_hi_alert_limit, vout.
 */
#define LTC4162_VOUT_FORMAT_R2I(x) (int16_t)__LTC4162_ILINE__((0), (LTC4162_VOUTDIV / LTC4162_ADCGAIN), (0), (1), x)
#define LTC4162_VOUT_FORMAT_I2R(y) __LTC4162_RLINE__((0), (1), (0), (LTC4162_VOUTDIV / LTC4162_ADCGAIN), (int16_t)(y))

/*! Convert from volts to the vin ADC reading.
 *   - Used with Bit Fields: vin_lo_alert_limit, vin_hi_alert_limit, vin, mppt_vin_init.
 */
#define LTC4162_VIN_FORMAT_R2I(x) (int16_t)__LTC4162_ILINE__((0), (LTC4162_VINDIV / LTC4162_ADCGAIN), (0), (1), x)
#define LTC4162_VIN_FORMAT_I2R(y) __LTC4162_RLINE__((0), (1), (0), (LTC4162_VINDIV / LTC4162_ADCGAIN), (int16_t)(y))

/*! Convert from amperes to the iin ADC reading.
 *   - Used with Bit Fields: iin_hi_alert_limit, iin.
 */
#define LTC4162_IIN_FORMAT_R2I(x) (int16_t)__LTC4162_ILINE__((0), (1 / LTC4162_RSNSI / LTC4162_AVCLPROG / LTC4162_ADCGAIN), (0), (1), x)
#define LTC4162_IIN_FORMAT_I2R(y) __LTC4162_RLINE__((0), (1), (0), (1 / LTC4162_RSNSI / LTC4162_AVCLPROG / LTC4162_ADCGAIN), (int16_t)(y))

/*! Convert from Ω to the per-cell bsr ADC reading.
 *   - Used with Bit Fields: bsr_hi_alert_limit, bsr.
 */
#define LTC4162_BSR_FORMAT_R2U(x) (uint16_t)__LTC4162_ILINE__((0), (LTC4162_RSNSB * LTC4162_AVPROG * LTC4162_BATDIV / 65536), (0), (1), x)
#define LTC4162_BSR_FORMAT_U2R(y) __LTC4162_RLINE__((0), (1), (0), (LTC4162_RSNSB * LTC4162_AVPROG * LTC4162_BATDIV / 65536), (uint16_t)(y))

/*! Convert from °C to the die_temp ADC reading.
 *   - Used with Bit Fields: die_temp_hi_alert_limit, thermal_reg_start_temp, thermal_reg_end_temp, die_temp.
 */
#define LTC4162_DIE_TEMP_FORMAT_R2I(x) (int16_t)__LTC4162_ILINE__((-264.4), (-264.4 + 1 / 46.557), (0), (1), x)
#define LTC4162_DIE_TEMP_FORMAT_I2R(y) __LTC4162_RLINE__((0), (1), (-264.4), (-264.4 + 1 / 46.557), (int16_t)(y))
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
